elliotmartin92/kia-socket/testing/brass_part_photo.jpeg

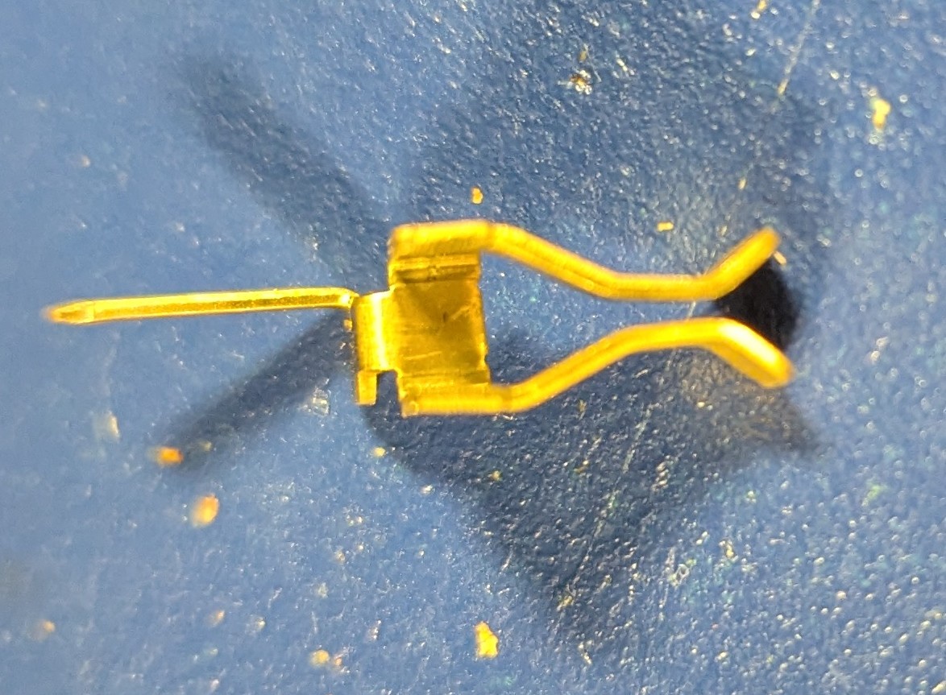
testing/brass_part_photo.jpeg
