elliotmartin92/kia-socket/testing/cropped_bracket_photo.jpg

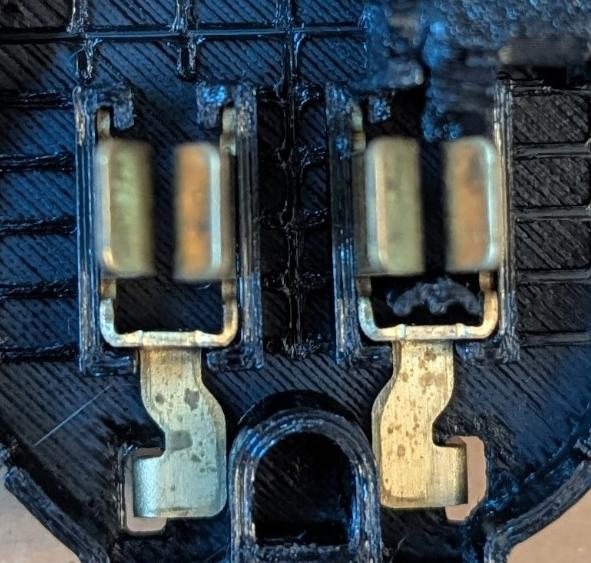
testing/cropped_bracket_photo.jpg
