elliotmartin92/kia-socket/testing/brass_insert_kinematic_simulation.png

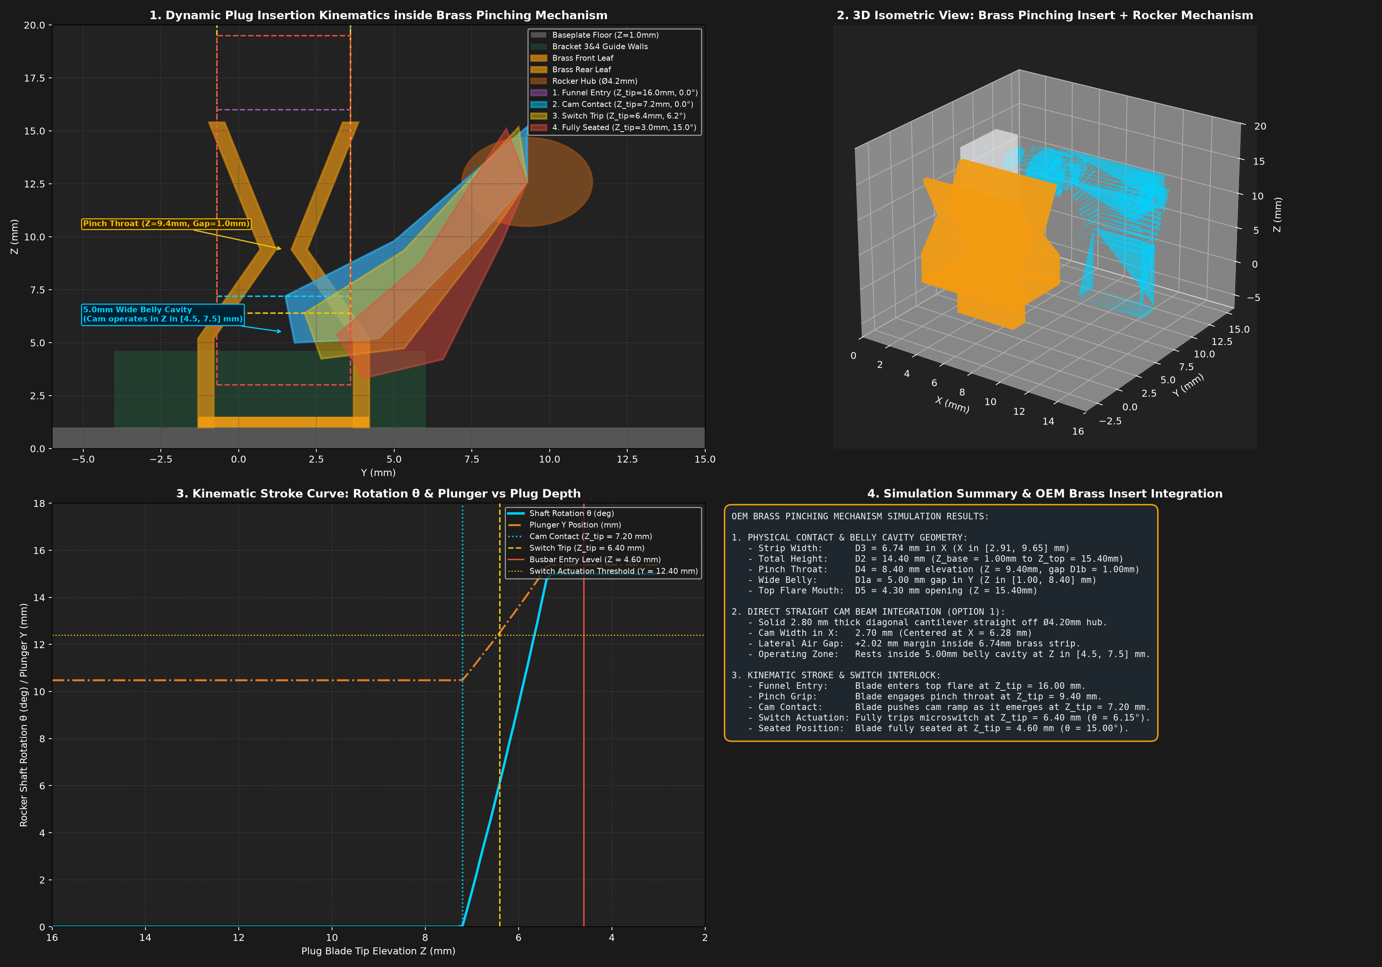
testing/brass_insert_kinematic_simulation.png
