elliotmartin92/kia-socket/testing/clip_support_design_comparison.png

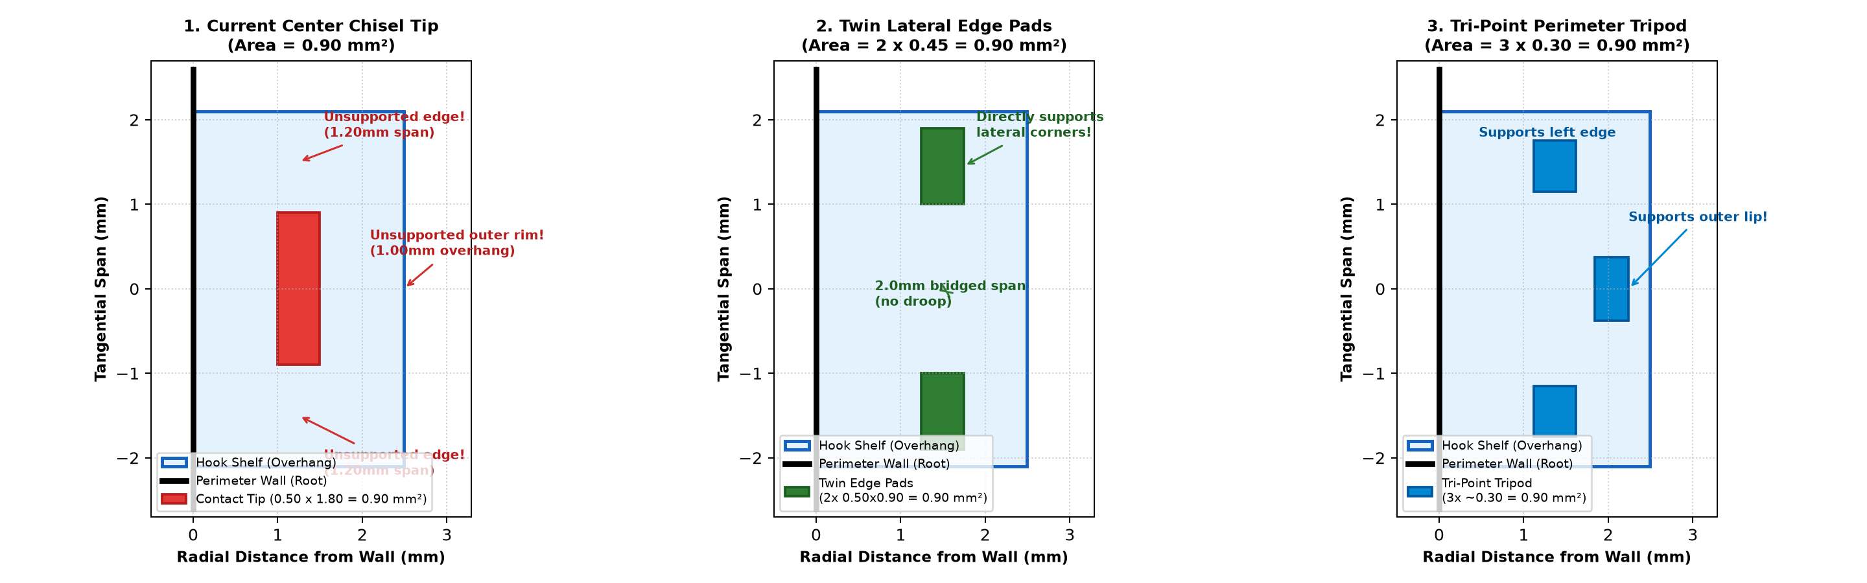
testing/clip_support_design_comparison.png
