elliotmartin92/kia-socket/testing/corrected_brass_kinematic_simulation.png

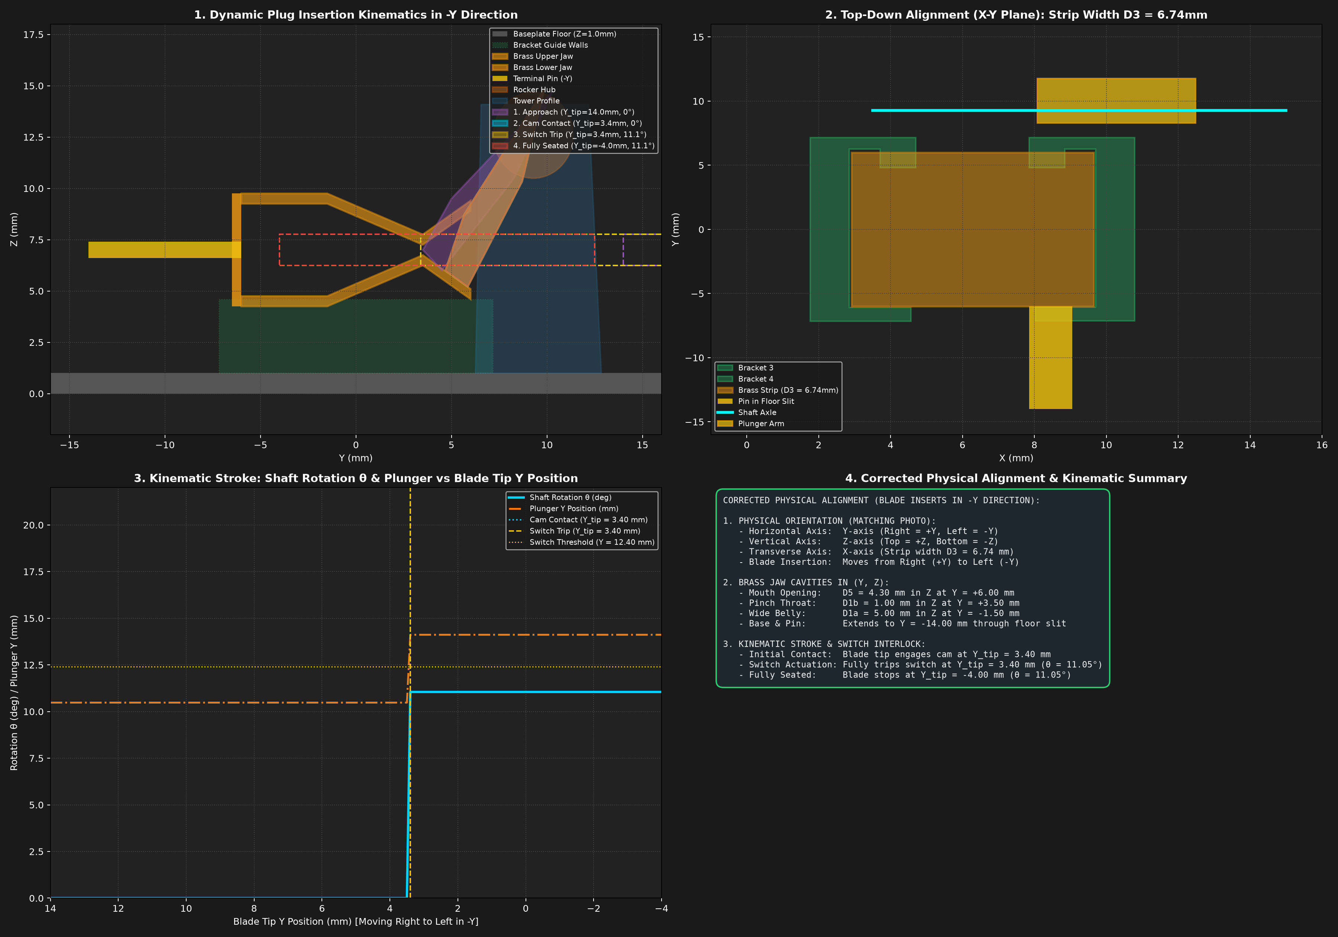
testing/corrected_brass_kinematic_simulation.png
