elliotmartin92/kia-socket/testing/arched_cam_step_by_step_study.png

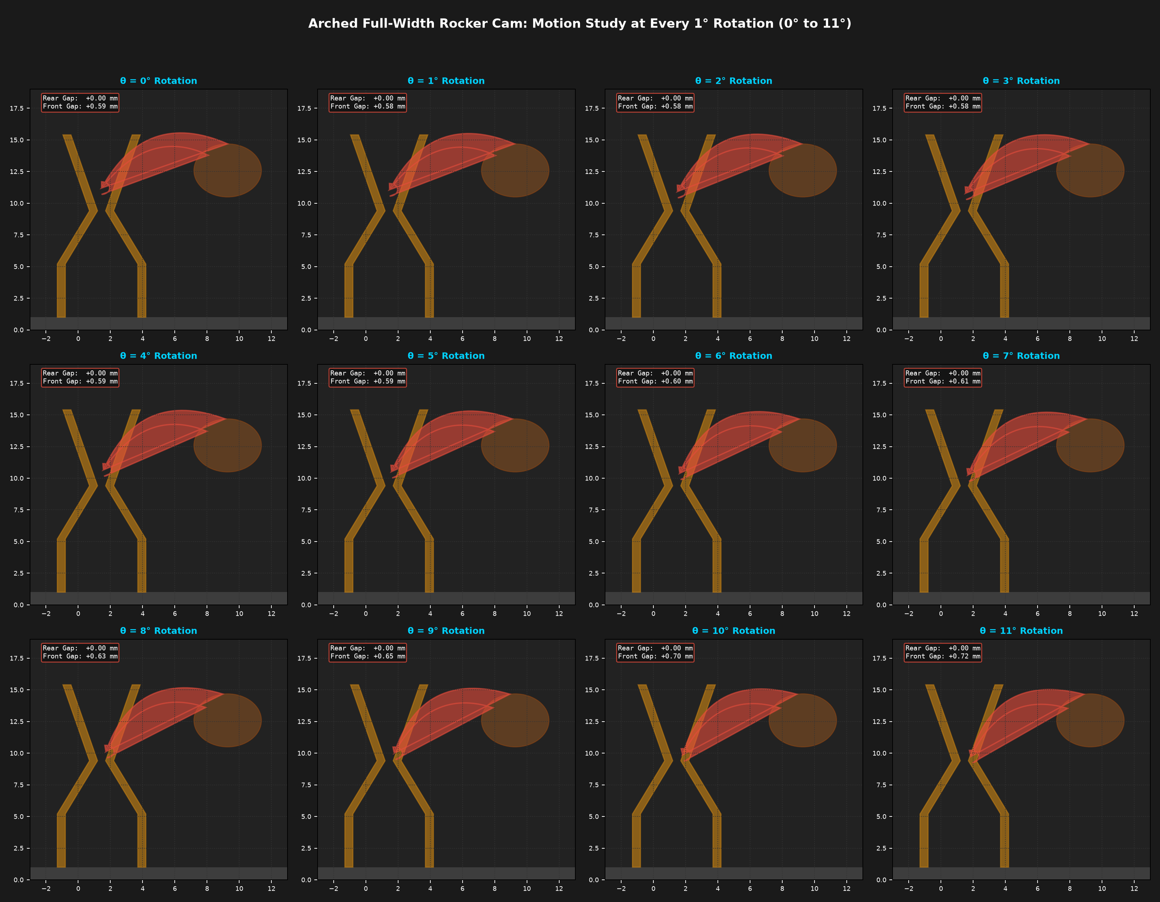
testing/arched_cam_step_by_step_study.png
