elliotmartin92/kia-socket/testing/exact_assembly_alignment.png

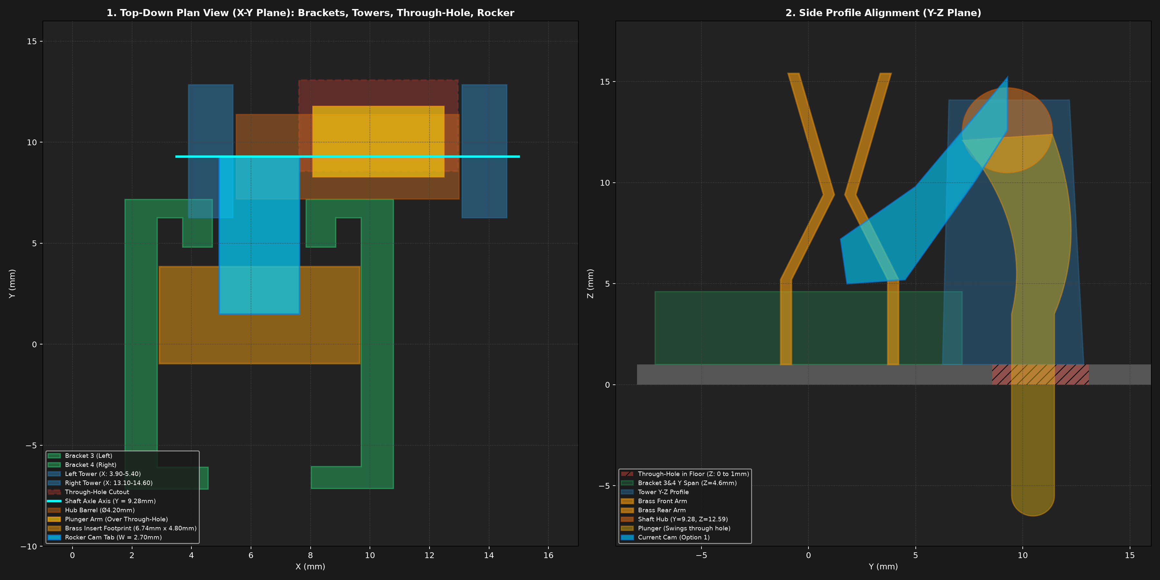
testing/exact_assembly_alignment.png
