elliotmartin92/kia-socket/testing/installed_brass_part_photo.jpg

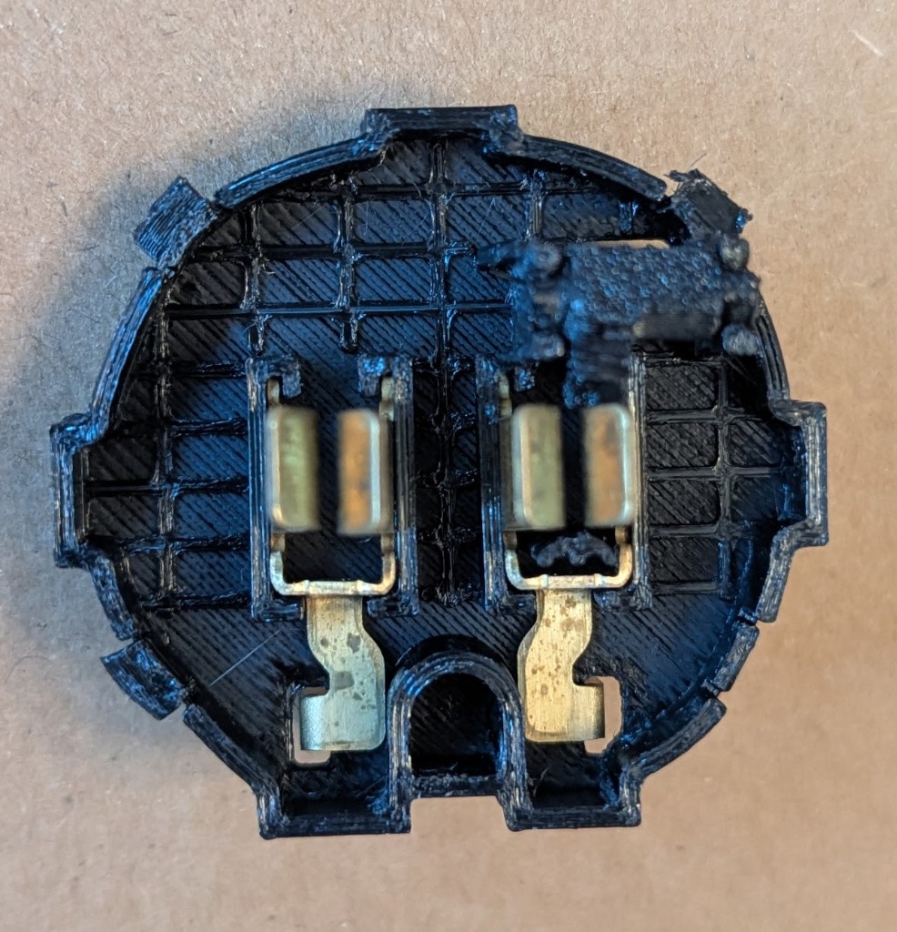
testing/installed_brass_part_photo.jpg
