elliotmartin92/kia-socket/testing/measurement_guide_diagram.png

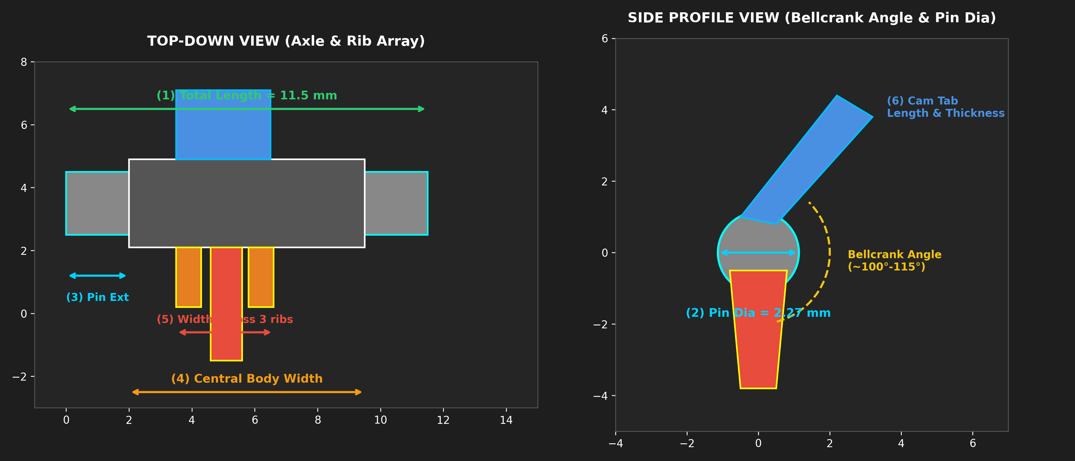
testing/measurement_guide_diagram.png
