elliotmartin92/kia-socket/testing/shaft_print_orientations_visualized.png

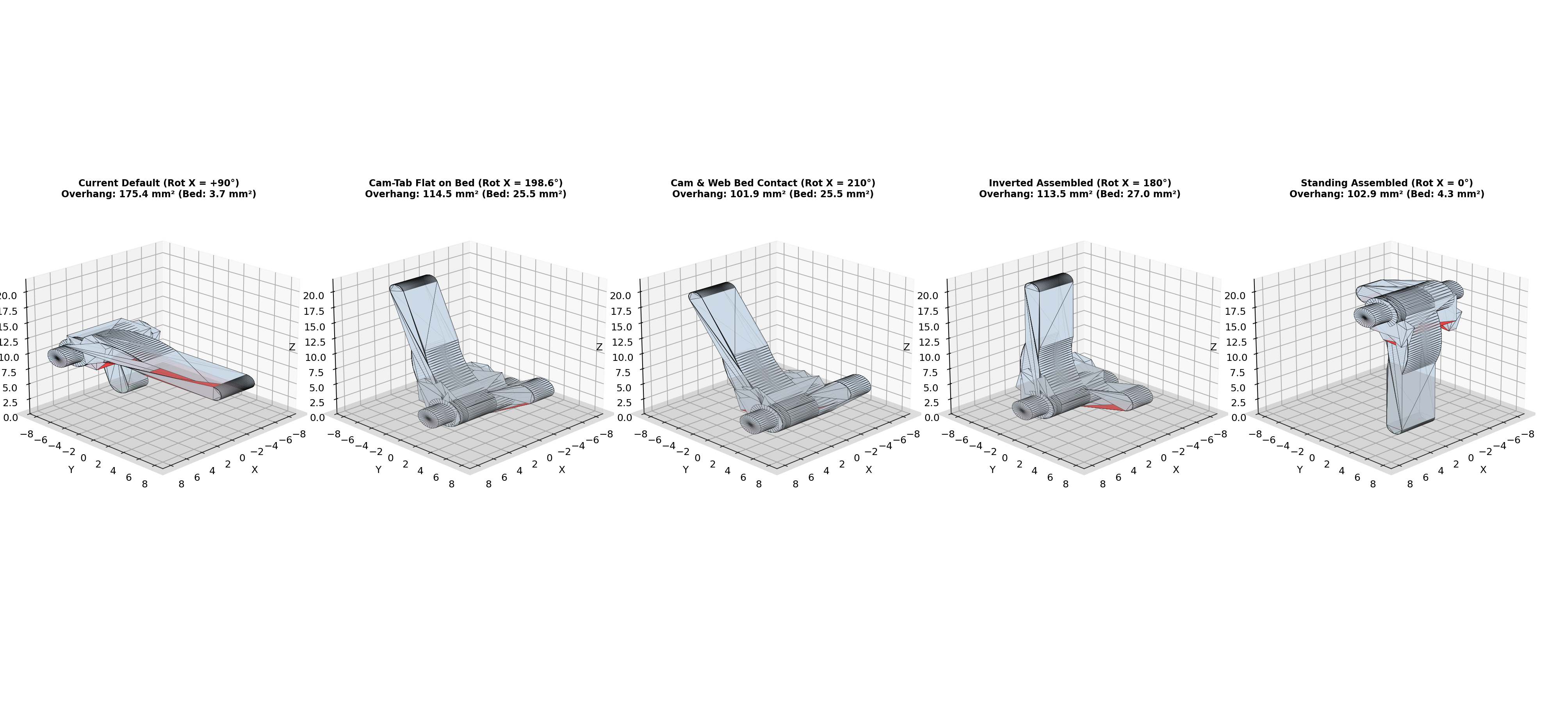
testing/shaft_print_orientations_visualized.png
