elliotmartin92/kia-socket/testing/tower_clamp_assembly_preview.png

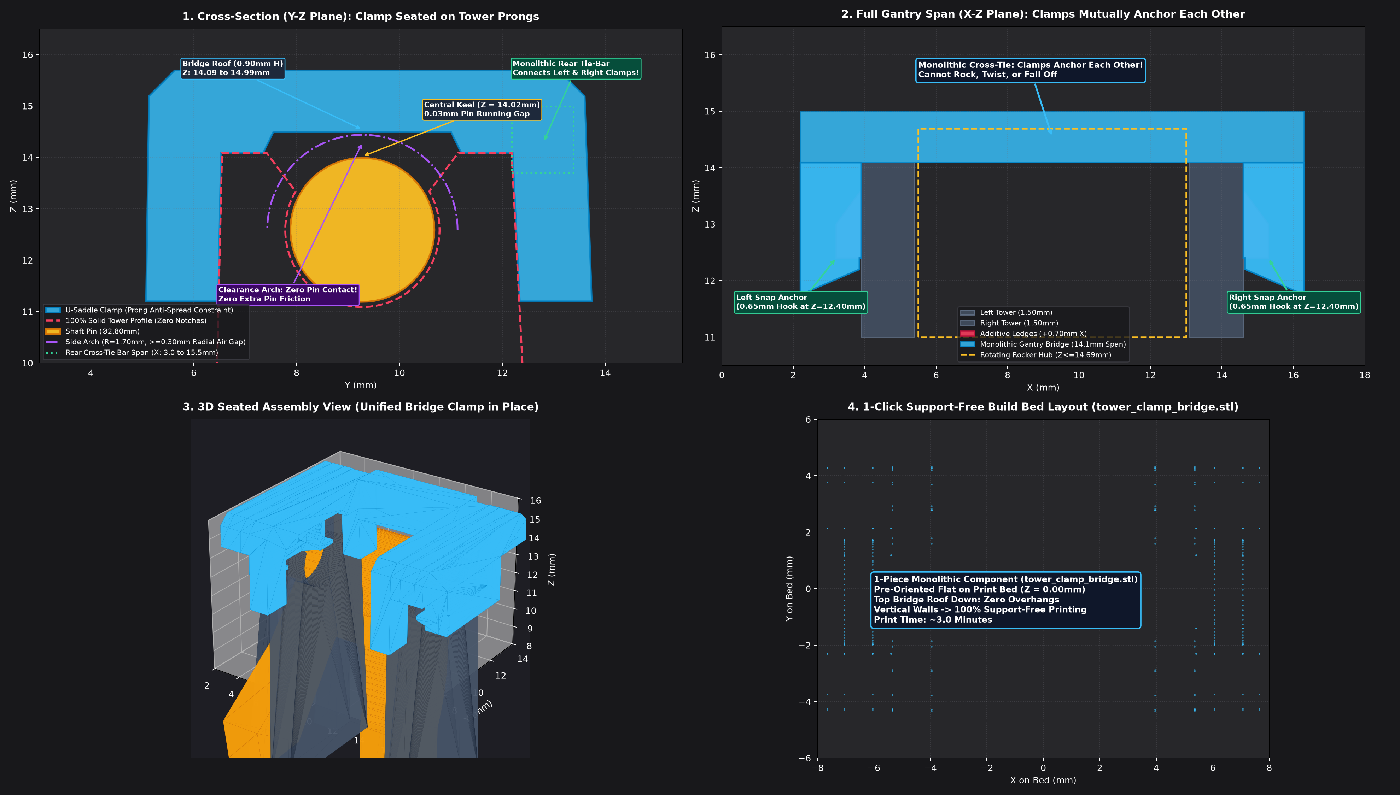
testing/tower_clamp_assembly_preview.png
