elliotmartin92/kia-socket/testing/tower_measurement_guide.png

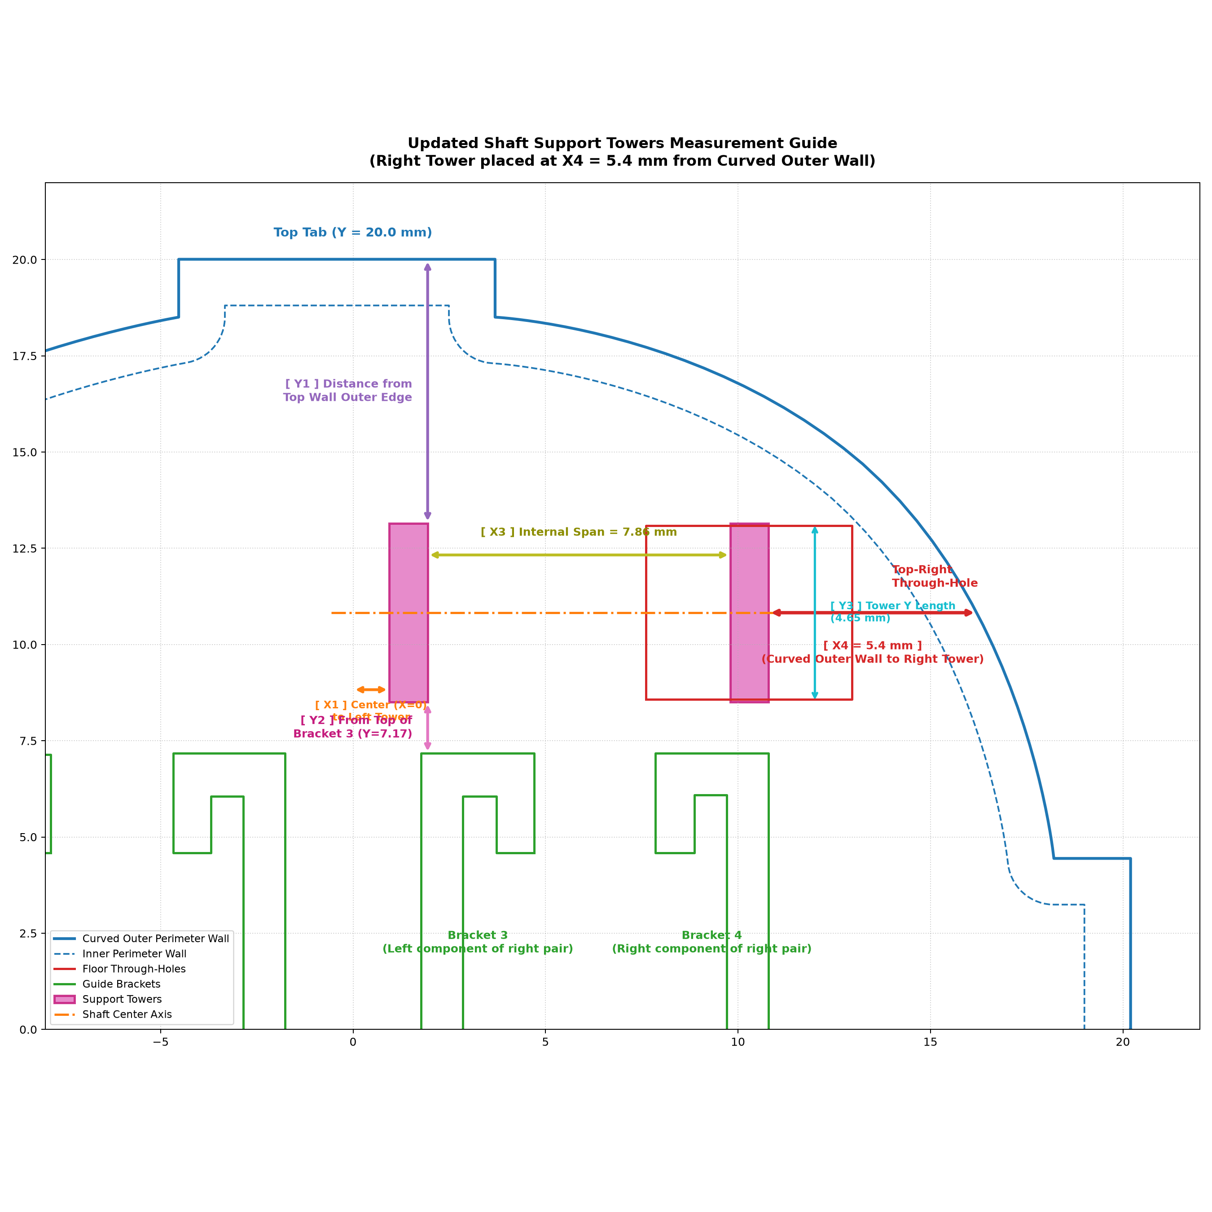
testing/tower_measurement_guide.png
