elliotmartin92/kia-socket/testing/3d_plug_insertion_view.png

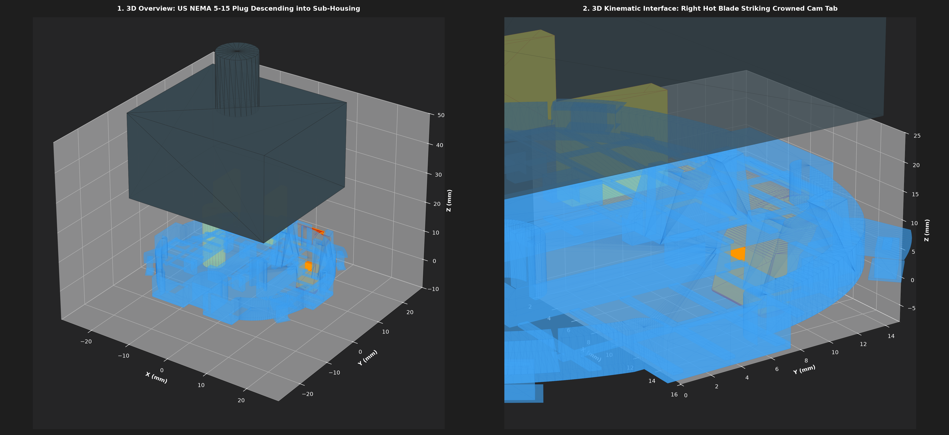
testing/3d_plug_insertion_view.png
