elliotmartin92/kia-socket/testing/aligned_bottom_arch_and_wall.png

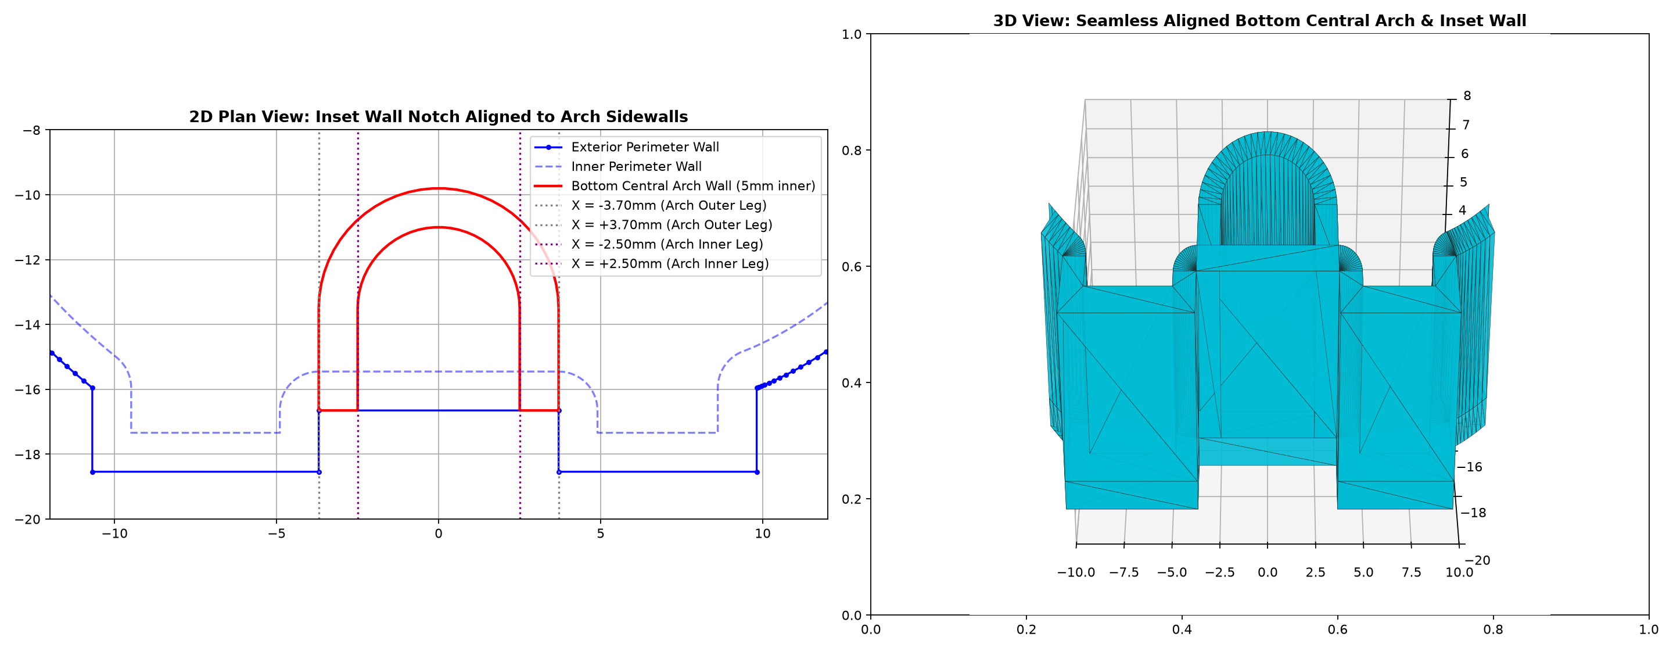
testing/aligned_bottom_arch_and_wall.png
