elliotmartin92/kia-socket/testing/aligned_bottom_notch_options.png

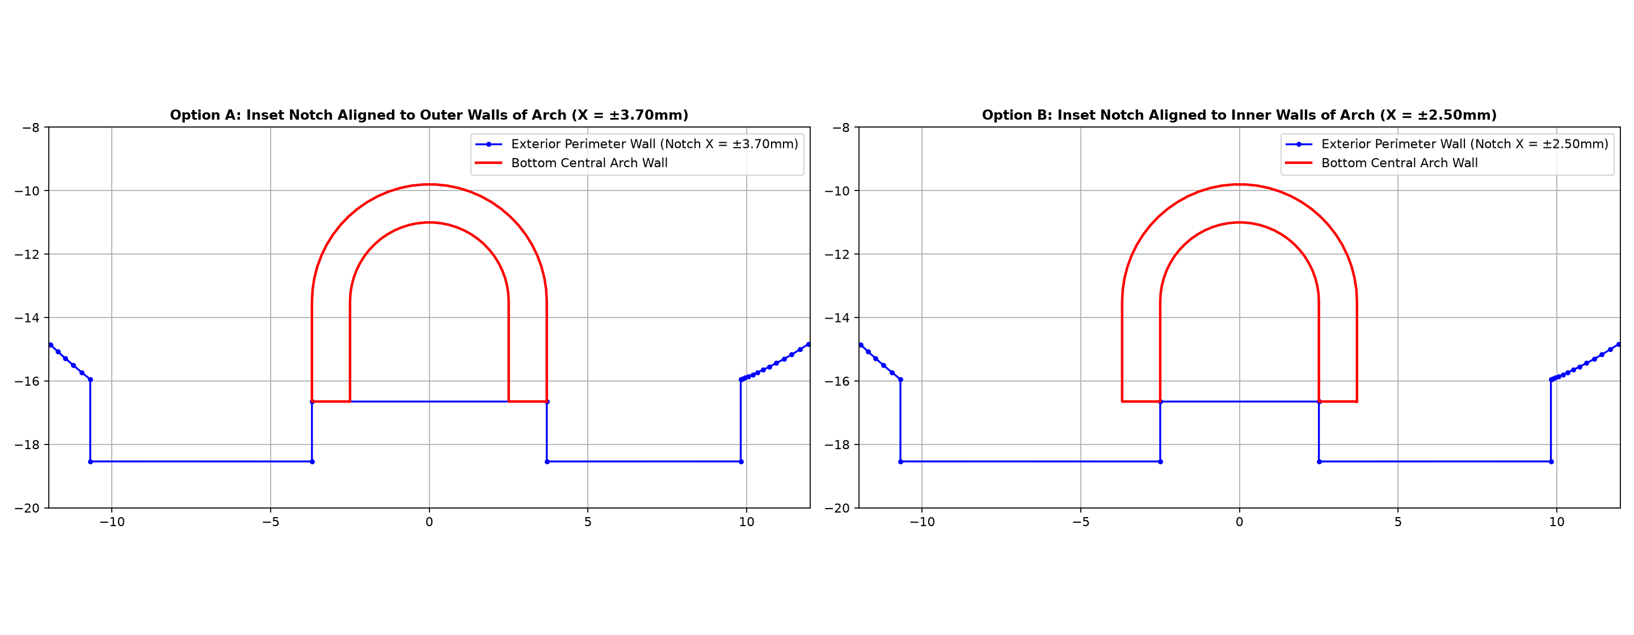
testing/aligned_bottom_notch_options.png
