elliotmartin92/kia-socket/testing/aligned_brass_insert_study.png

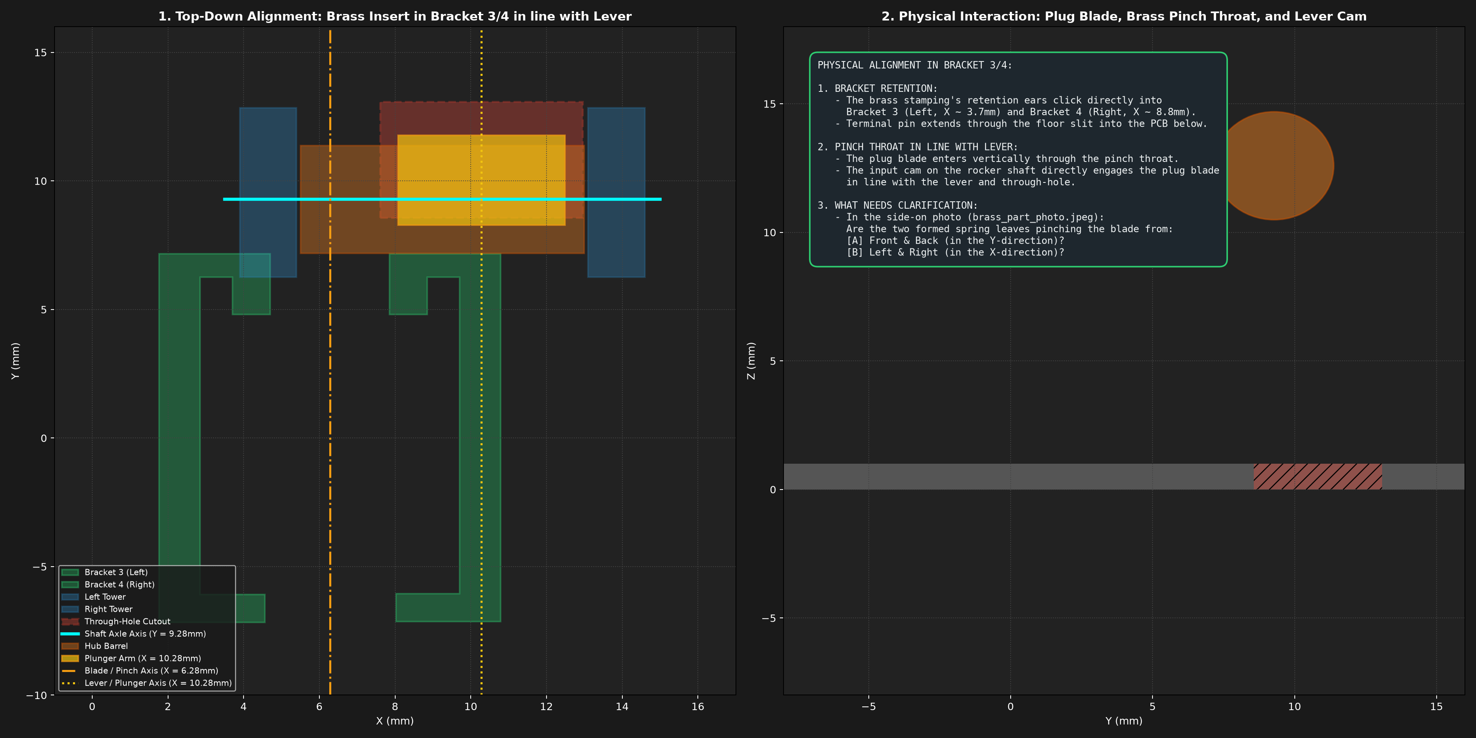
testing/aligned_brass_insert_study.png
