elliotmartin92/kia-socket/testing/aligned_towers_preview.png

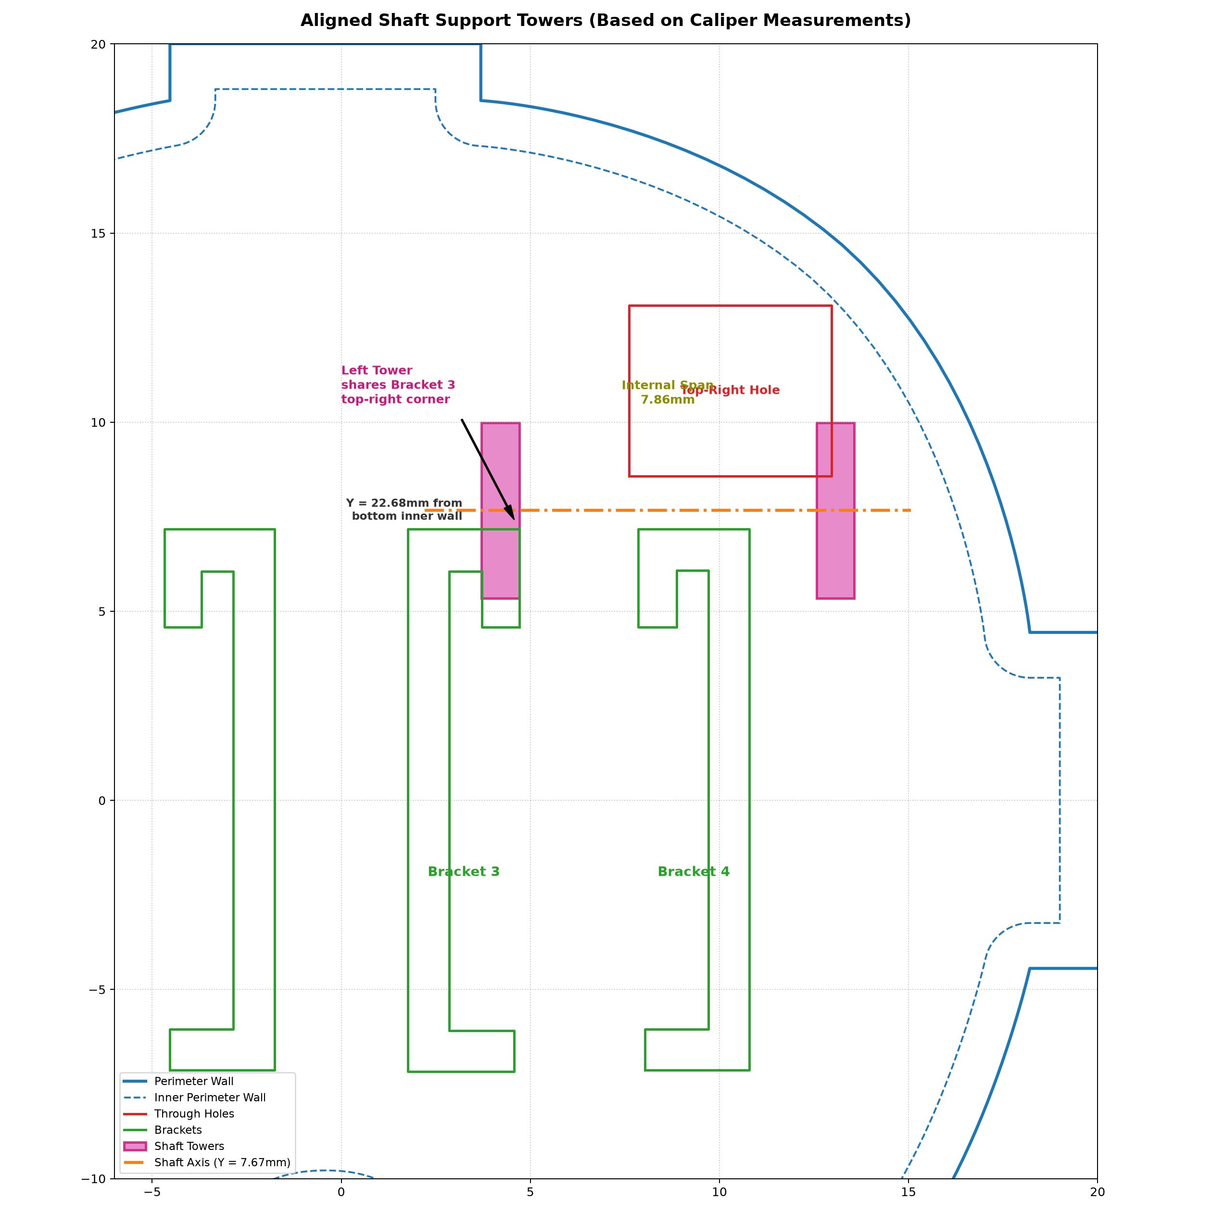
testing/aligned_towers_preview.png
