elliotmartin92/kia-socket/testing/approach_b_accurate_render.png

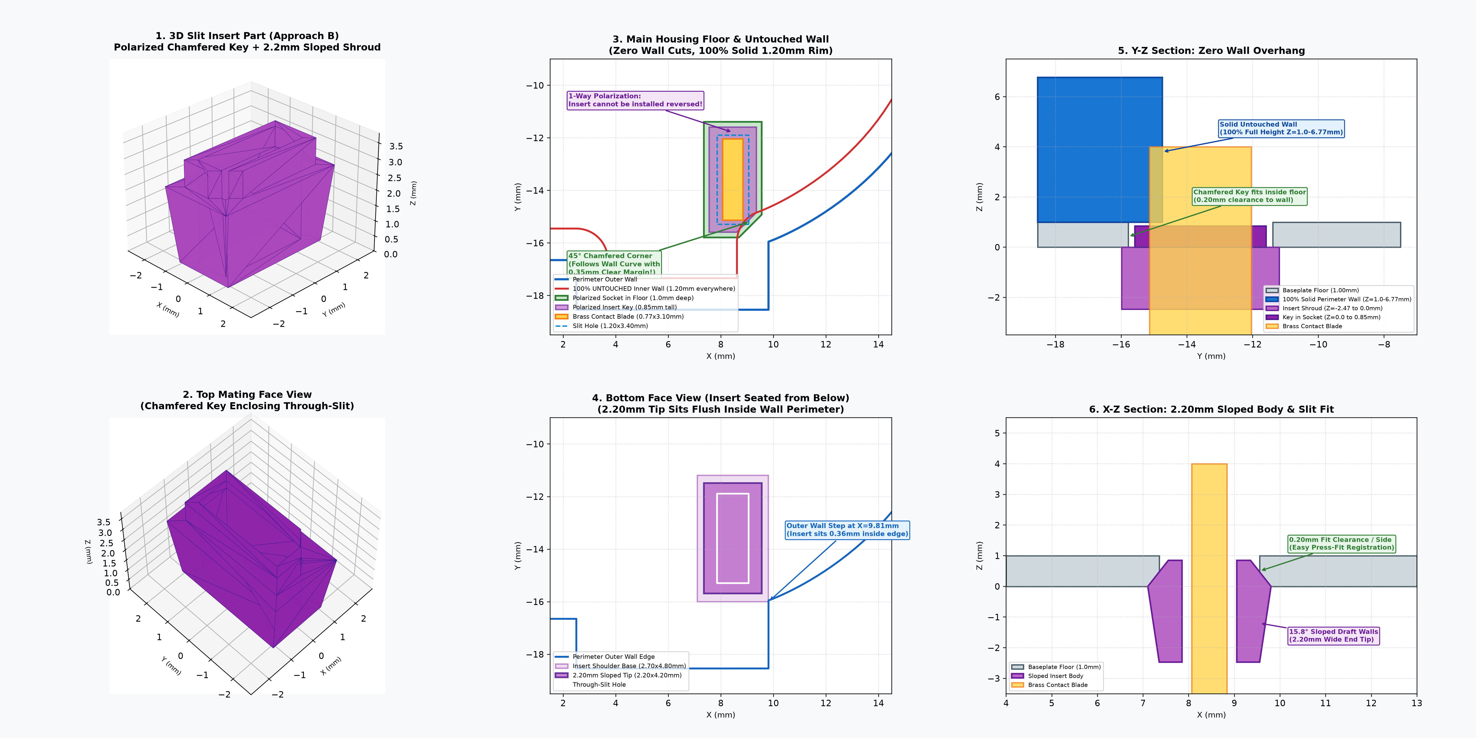
testing/approach_b_accurate_render.png
