elliotmartin92/kia-socket/testing/arch_5mm_test.png

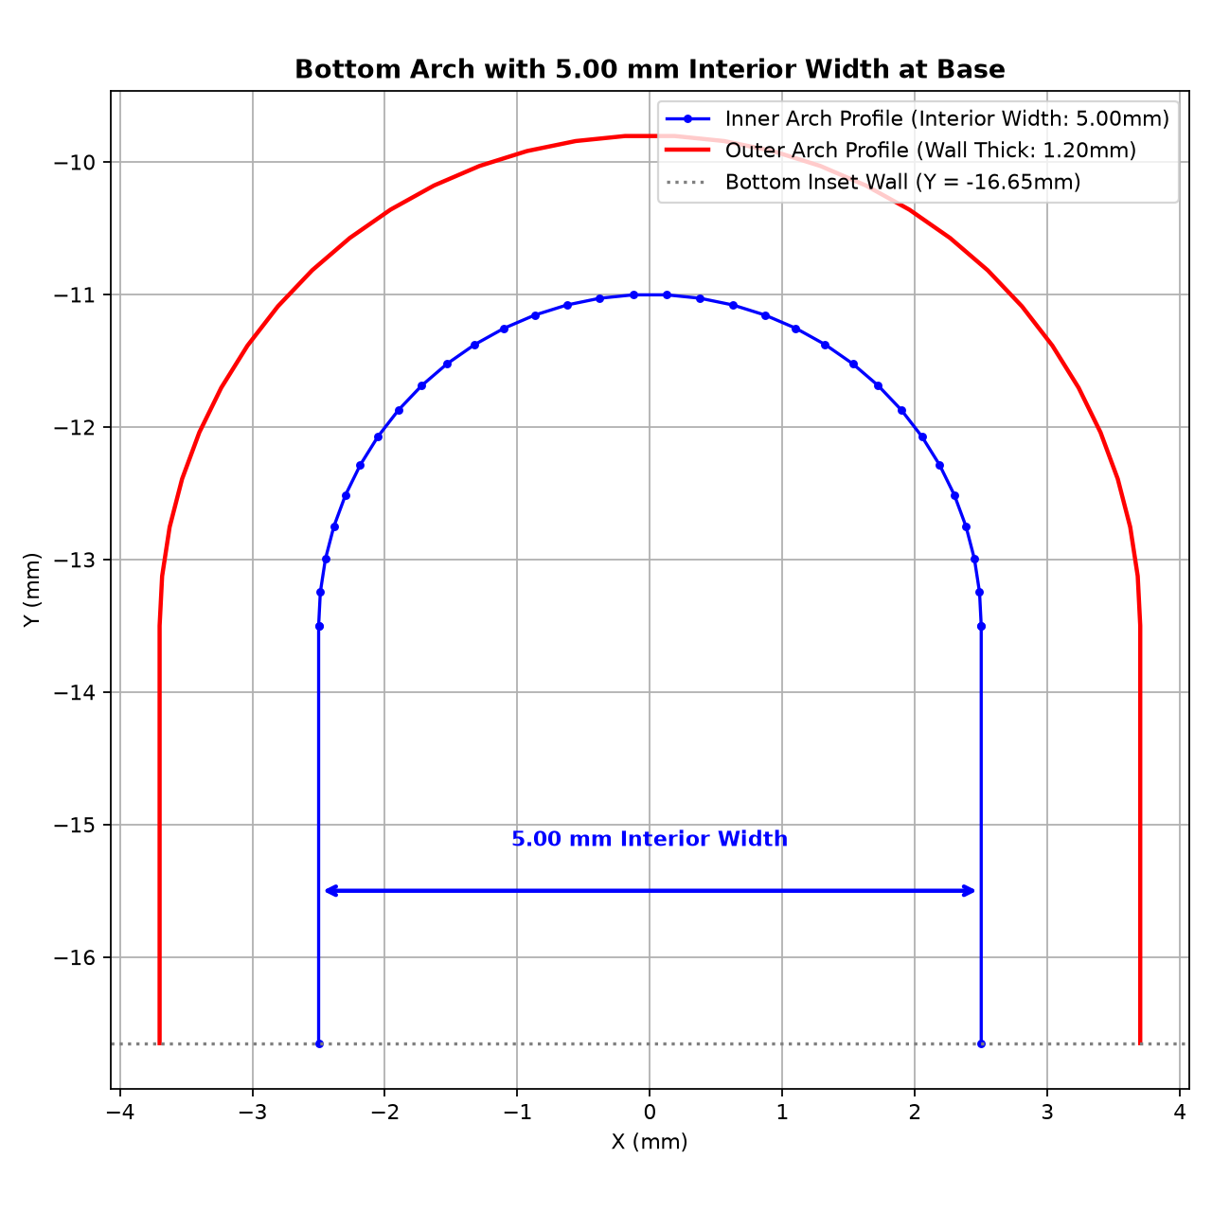
testing/arch_5mm_test.png
