elliotmartin92/kia-socket/testing/arch_795_preview.png

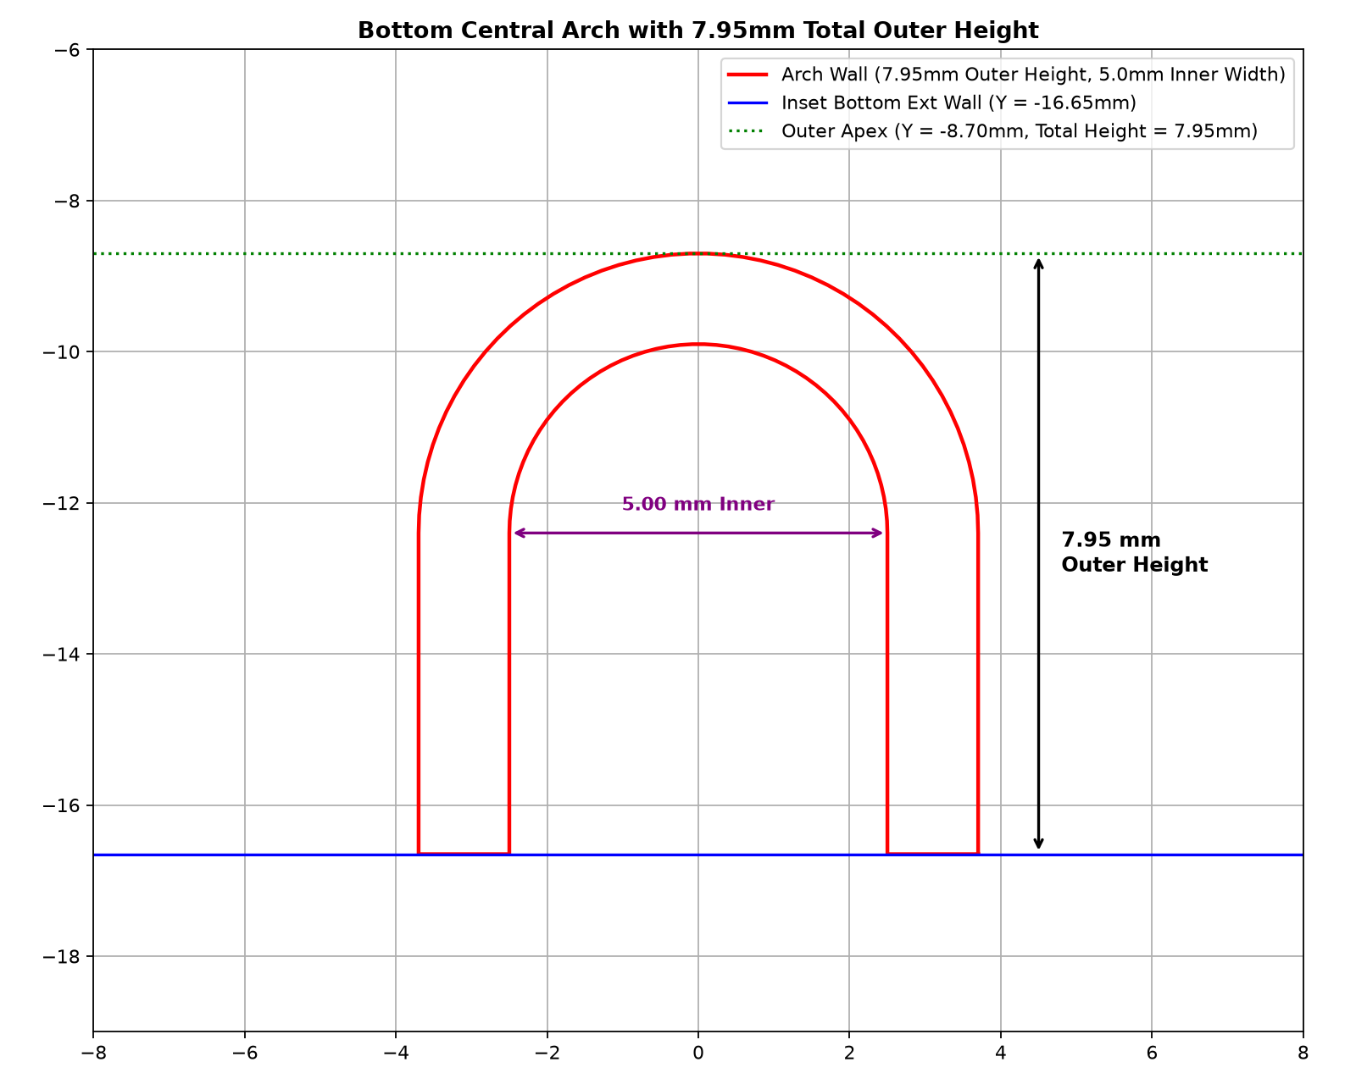
testing/arch_795_preview.png
