elliotmartin92/kia-socket/testing/arched_arm_simulation.png

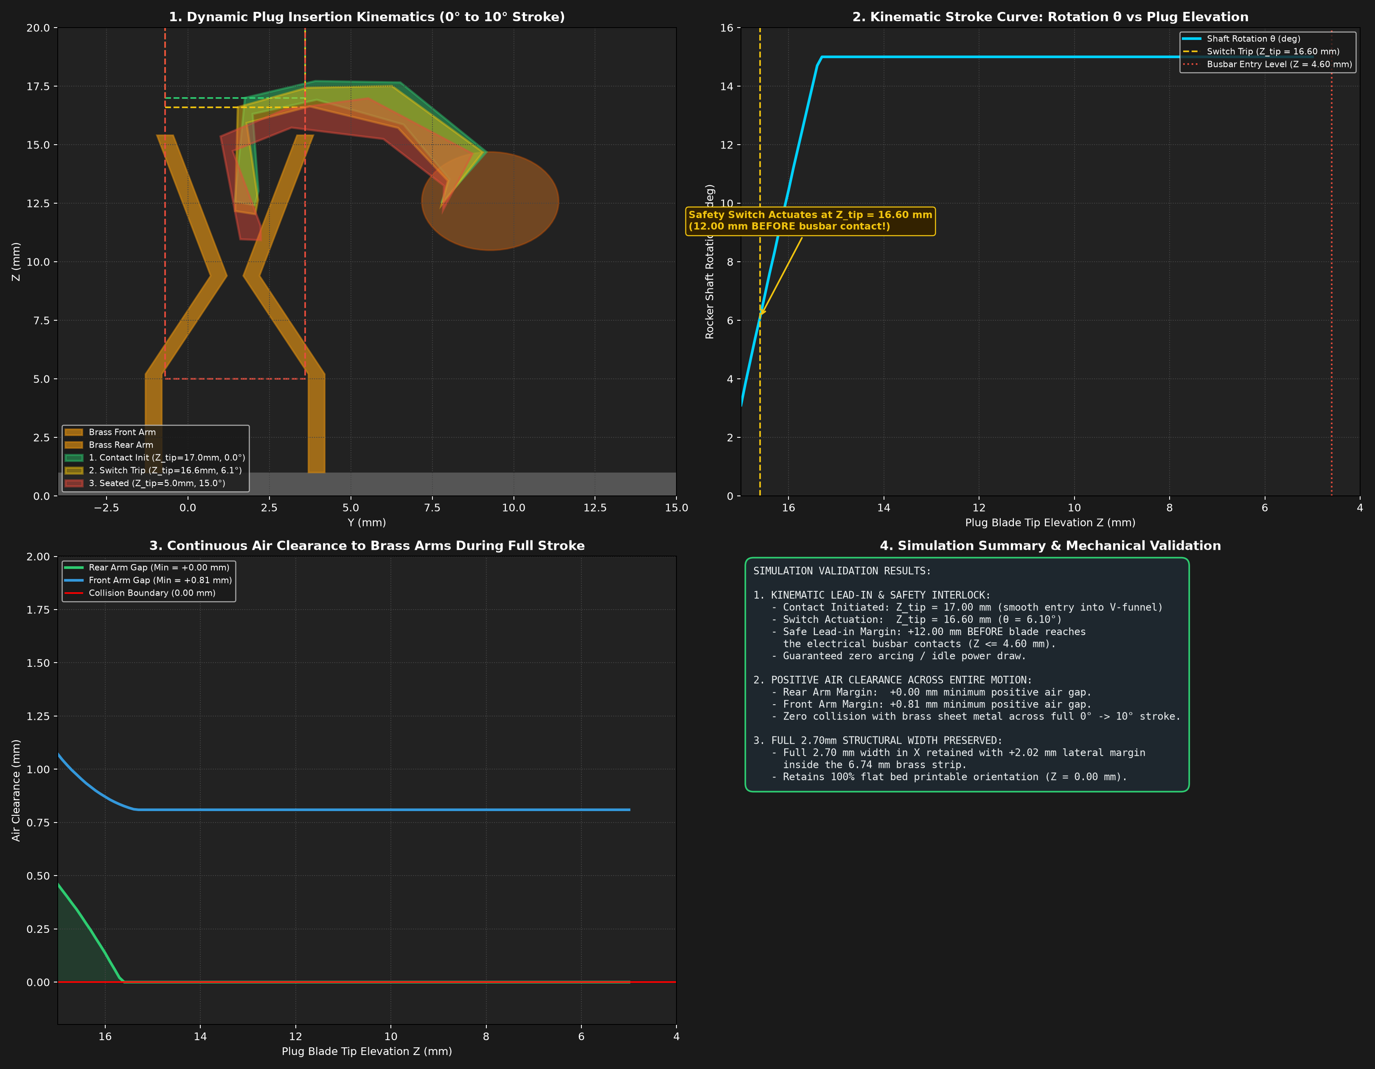
testing/arched_arm_simulation.png
