elliotmartin92/kia-socket/testing/bellcrank_angle_comparison.png

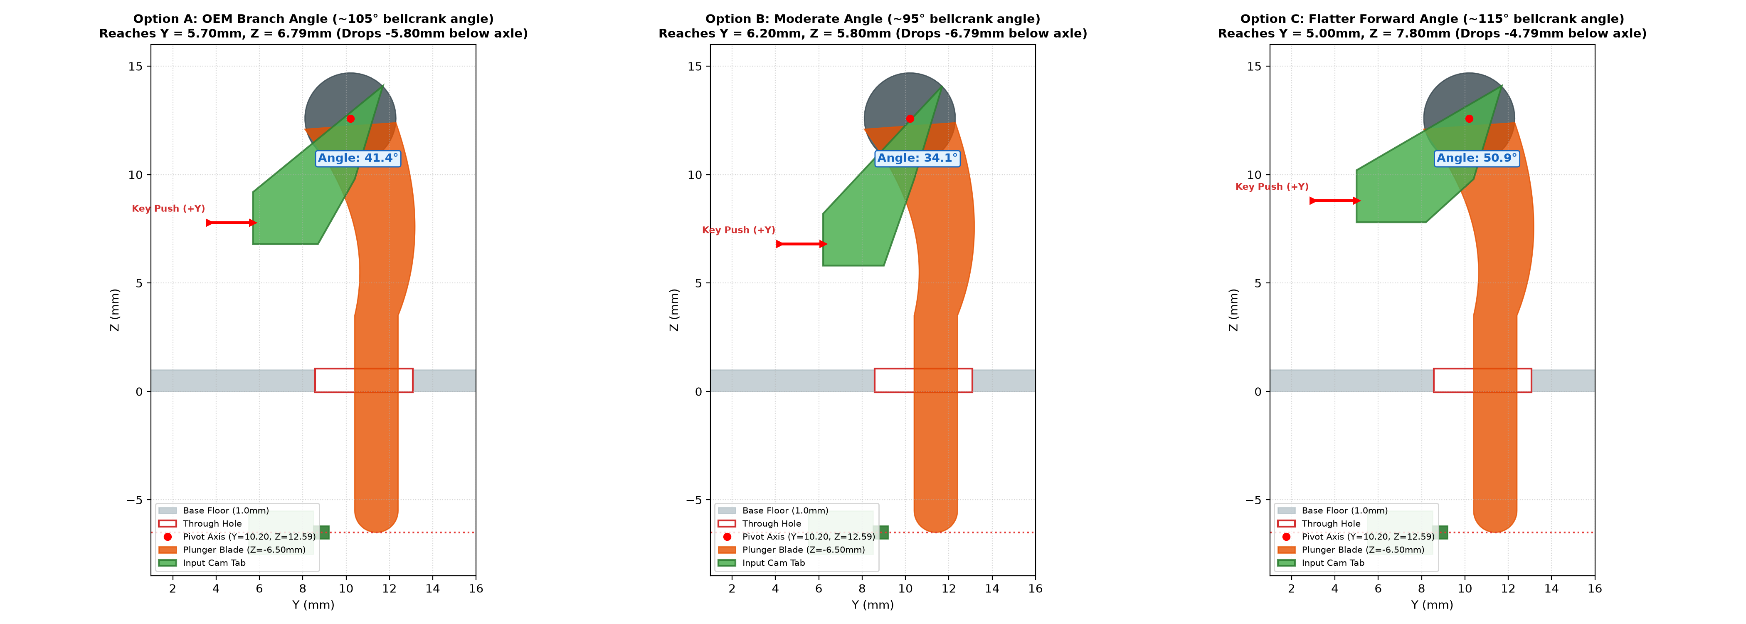
testing/bellcrank_angle_comparison.png
