elliotmartin92/kia-socket/testing/blade_cam_contact_analysis.png

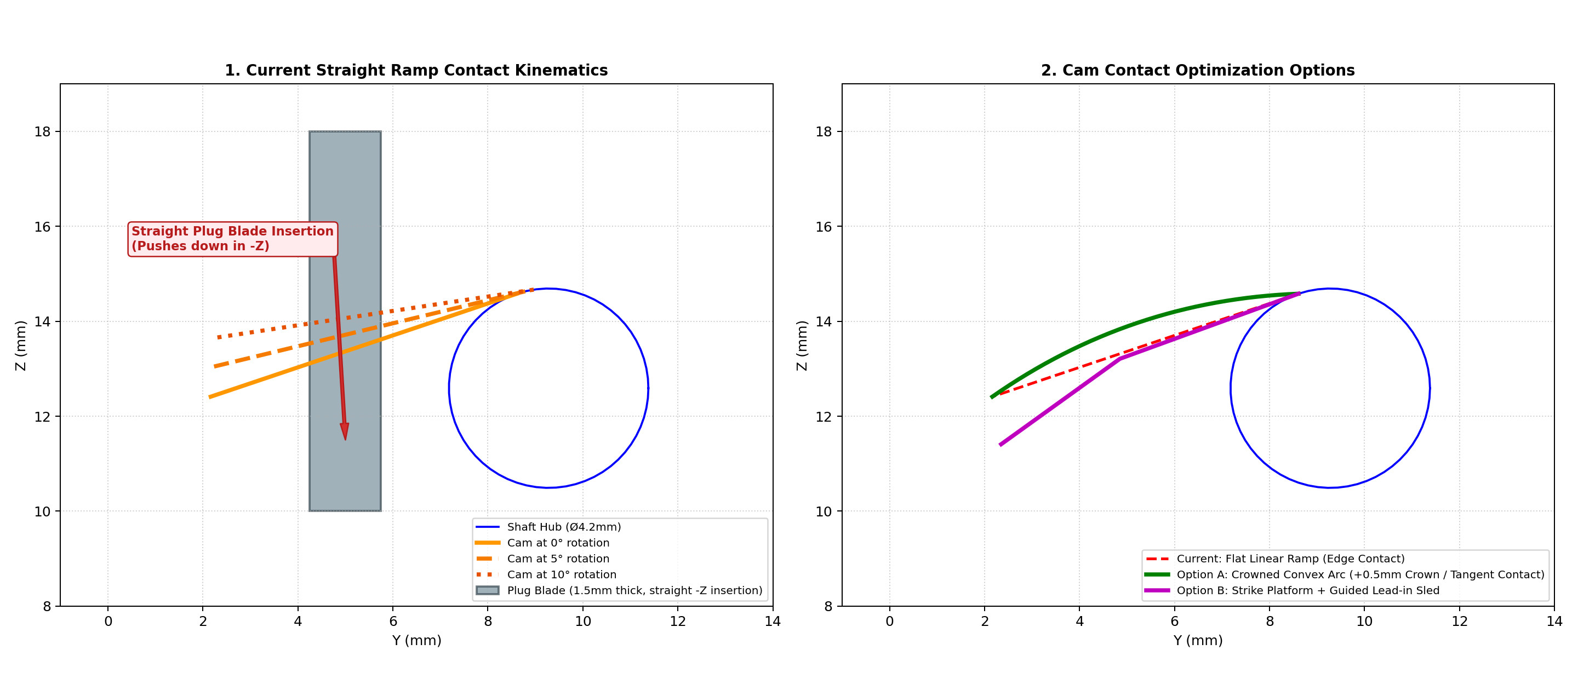
testing/blade_cam_contact_analysis.png
