elliotmartin92/kia-socket/testing/blade_contact_options_comparison.png

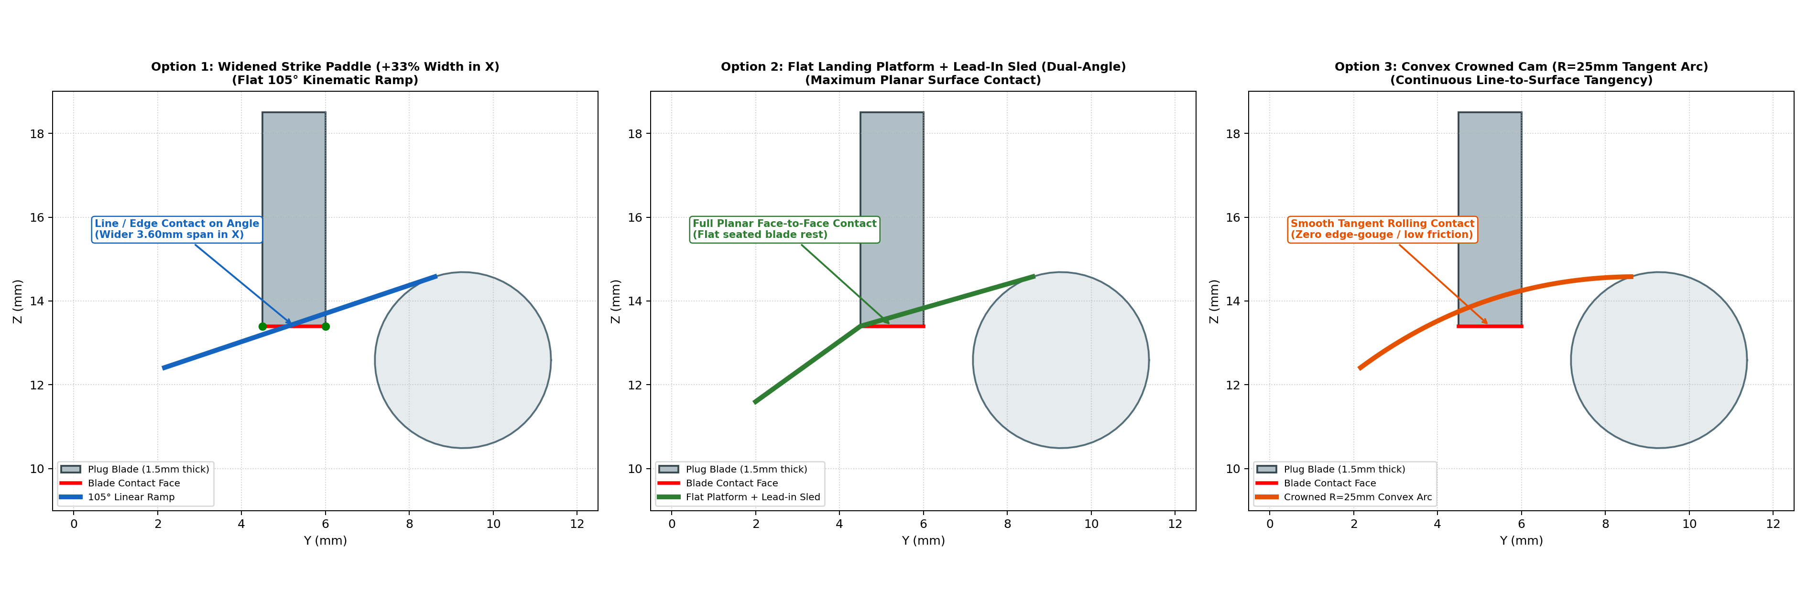
testing/blade_contact_options_comparison.png
