elliotmartin92/kia-socket/testing/blade_seating_measurements_diagram.png

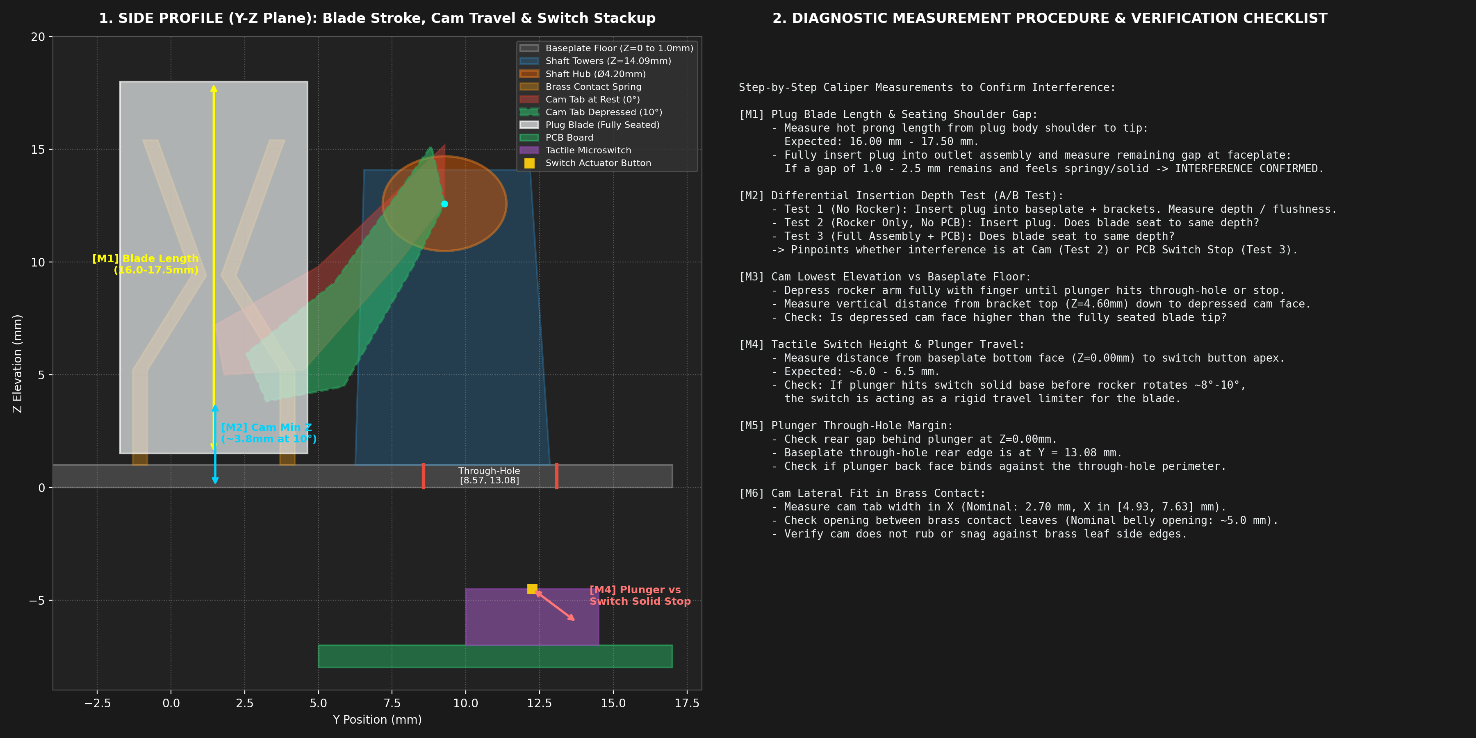
testing/blade_seating_measurements_diagram.png
