elliotmartin92/kia-socket/testing/bottom_arch_options.png

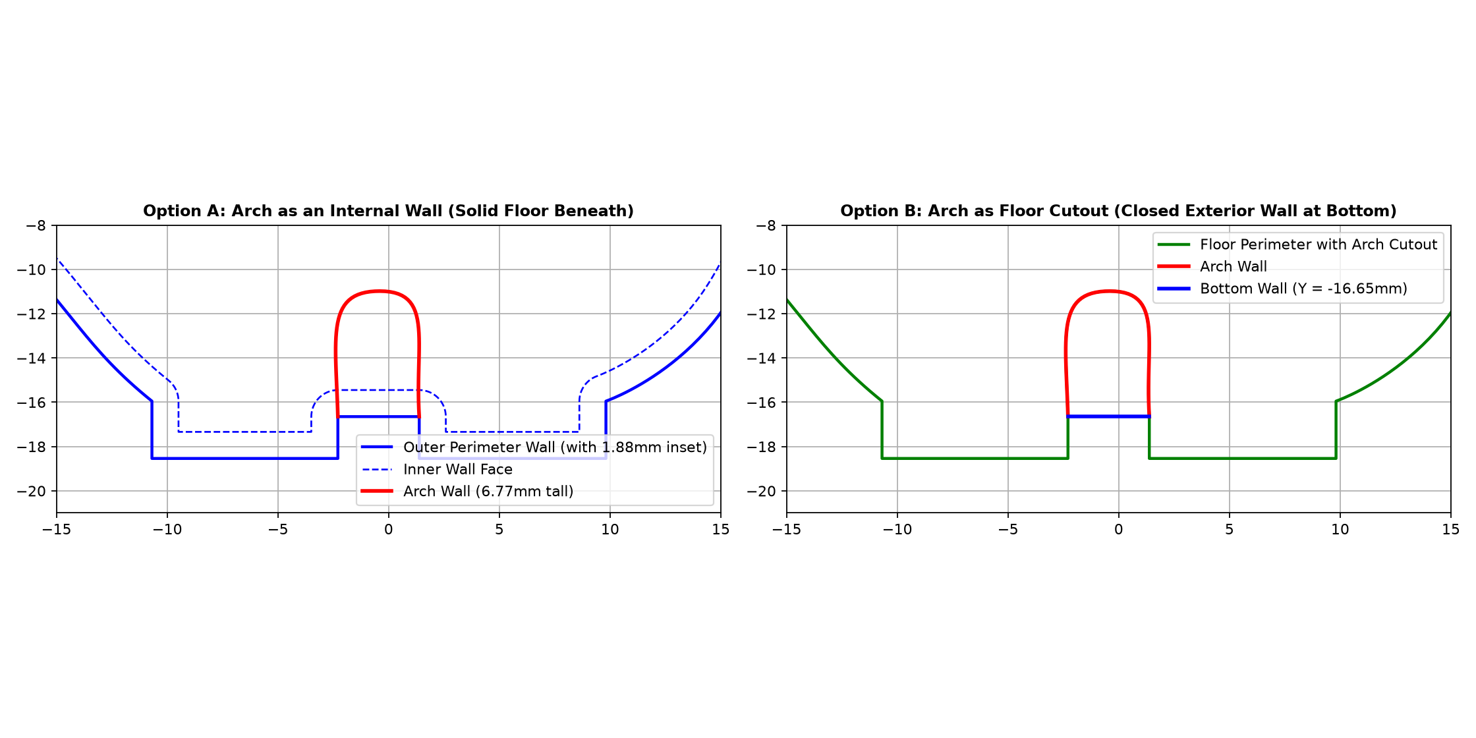
testing/bottom_arch_options.png
