elliotmartin92/kia-socket/testing/bottom_clip_options_plot.png

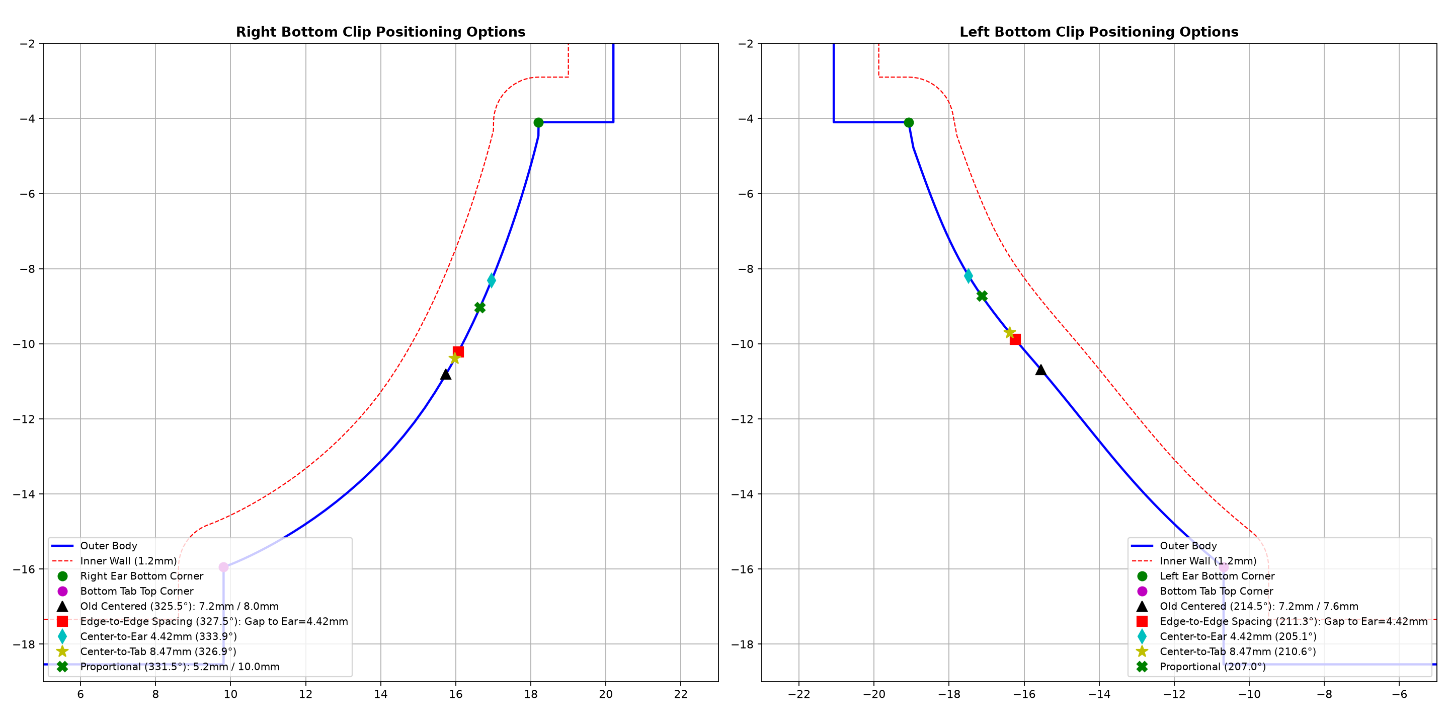
testing/bottom_clip_options_plot.png
