elliotmartin92/kia-socket/testing/bottom_feature_3d_test.png

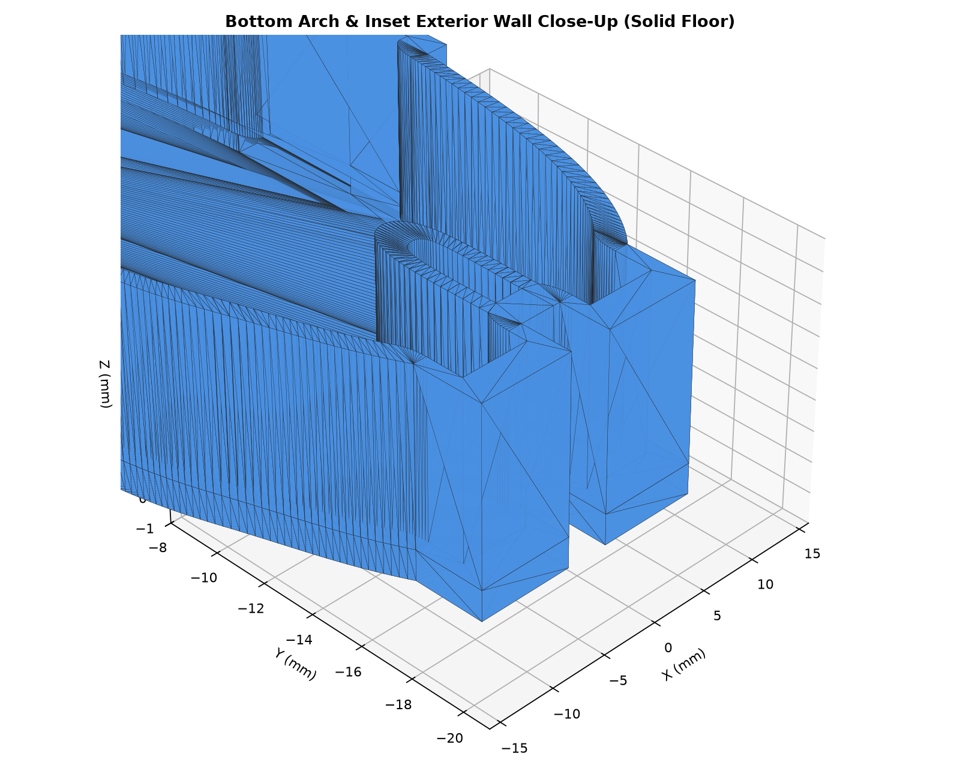
testing/bottom_feature_3d_test.png
