elliotmartin92/kia-socket/testing/bottom_notch_and_arch_configs.png

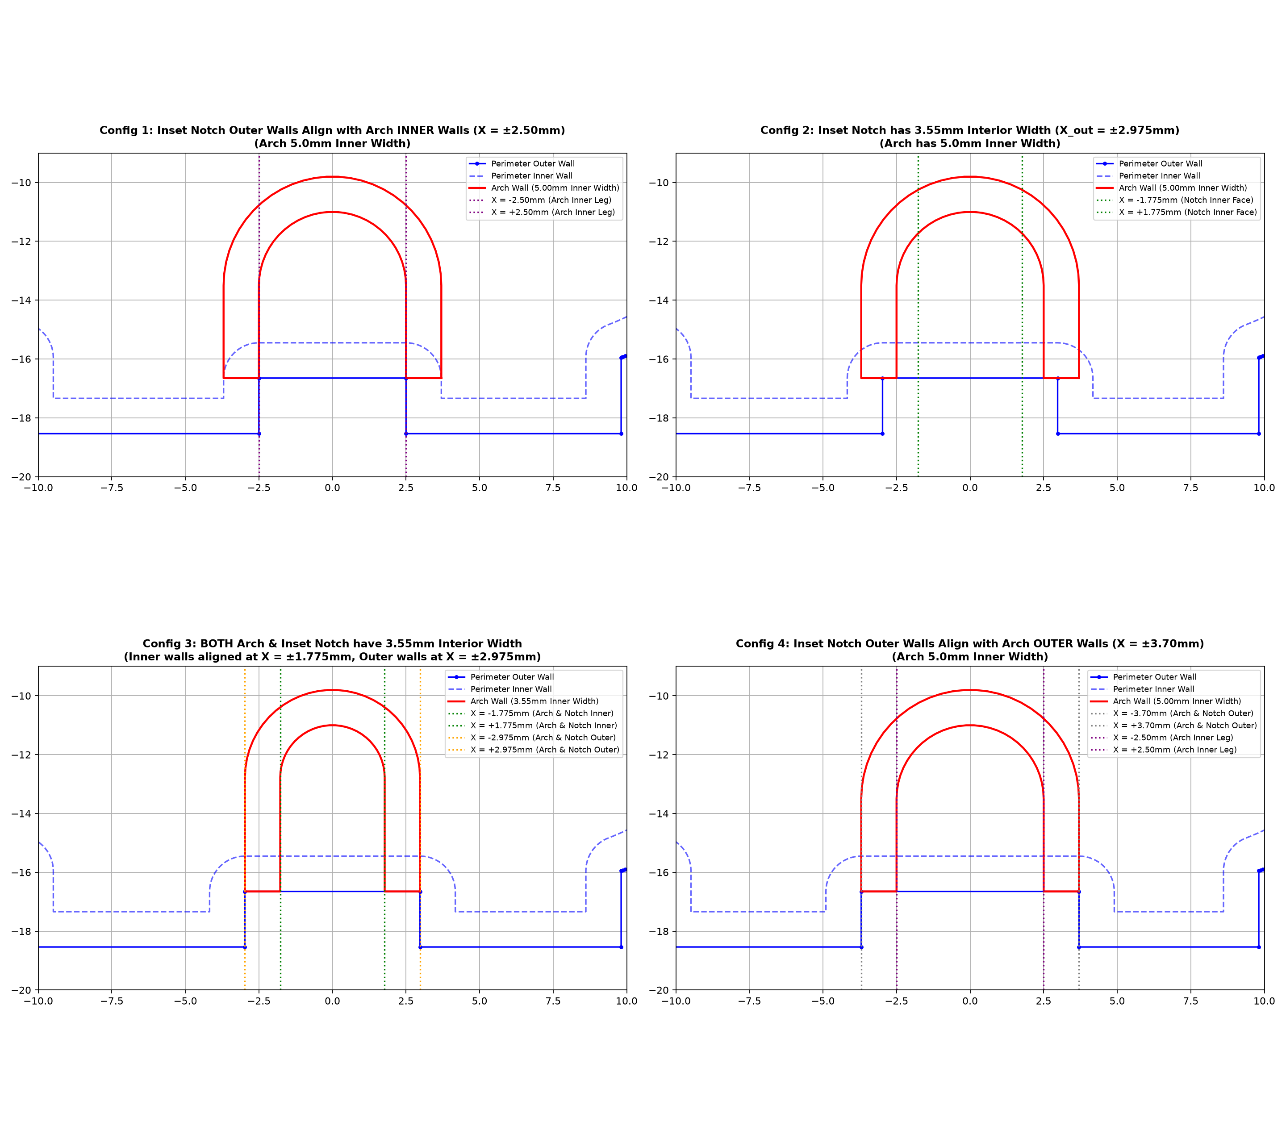
testing/bottom_notch_and_arch_configs.png
