elliotmartin92/kia-socket/testing/bottom_wall_alignment_inspect.png

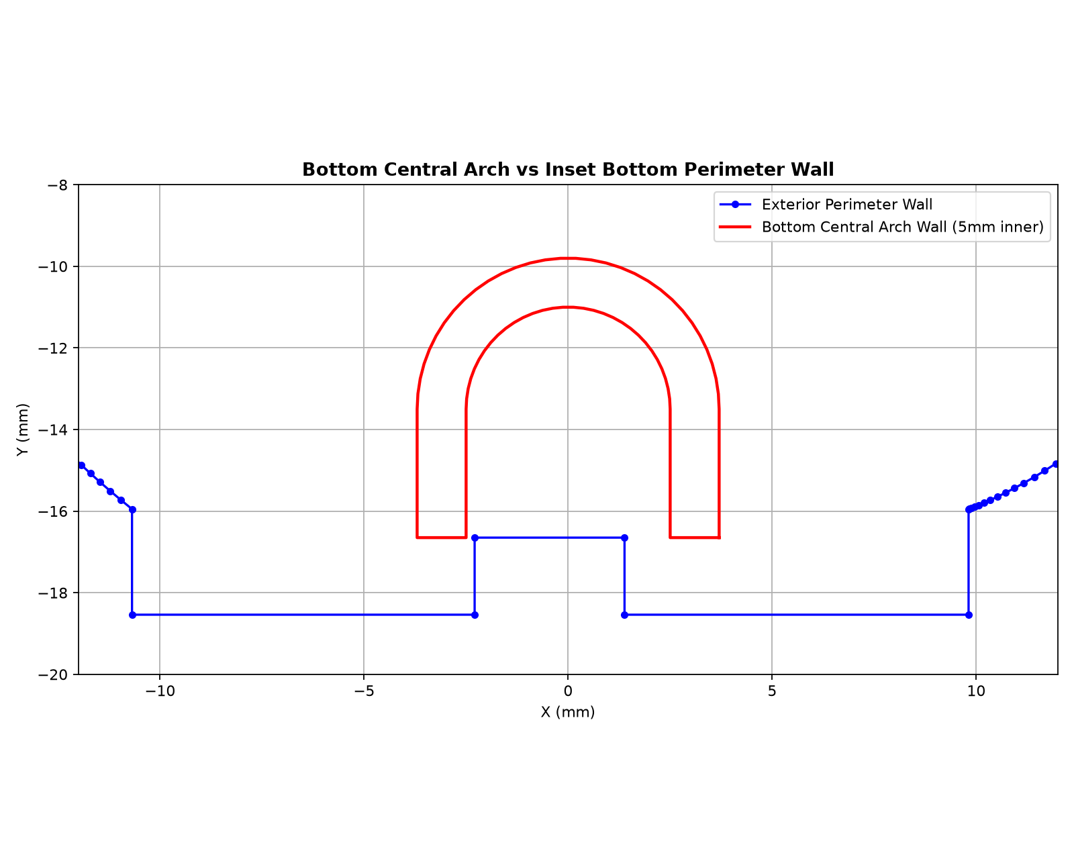
testing/bottom_wall_alignment_inspect.png
