elliotmartin92/kia-socket/testing/bracket3_clearance_verified.png

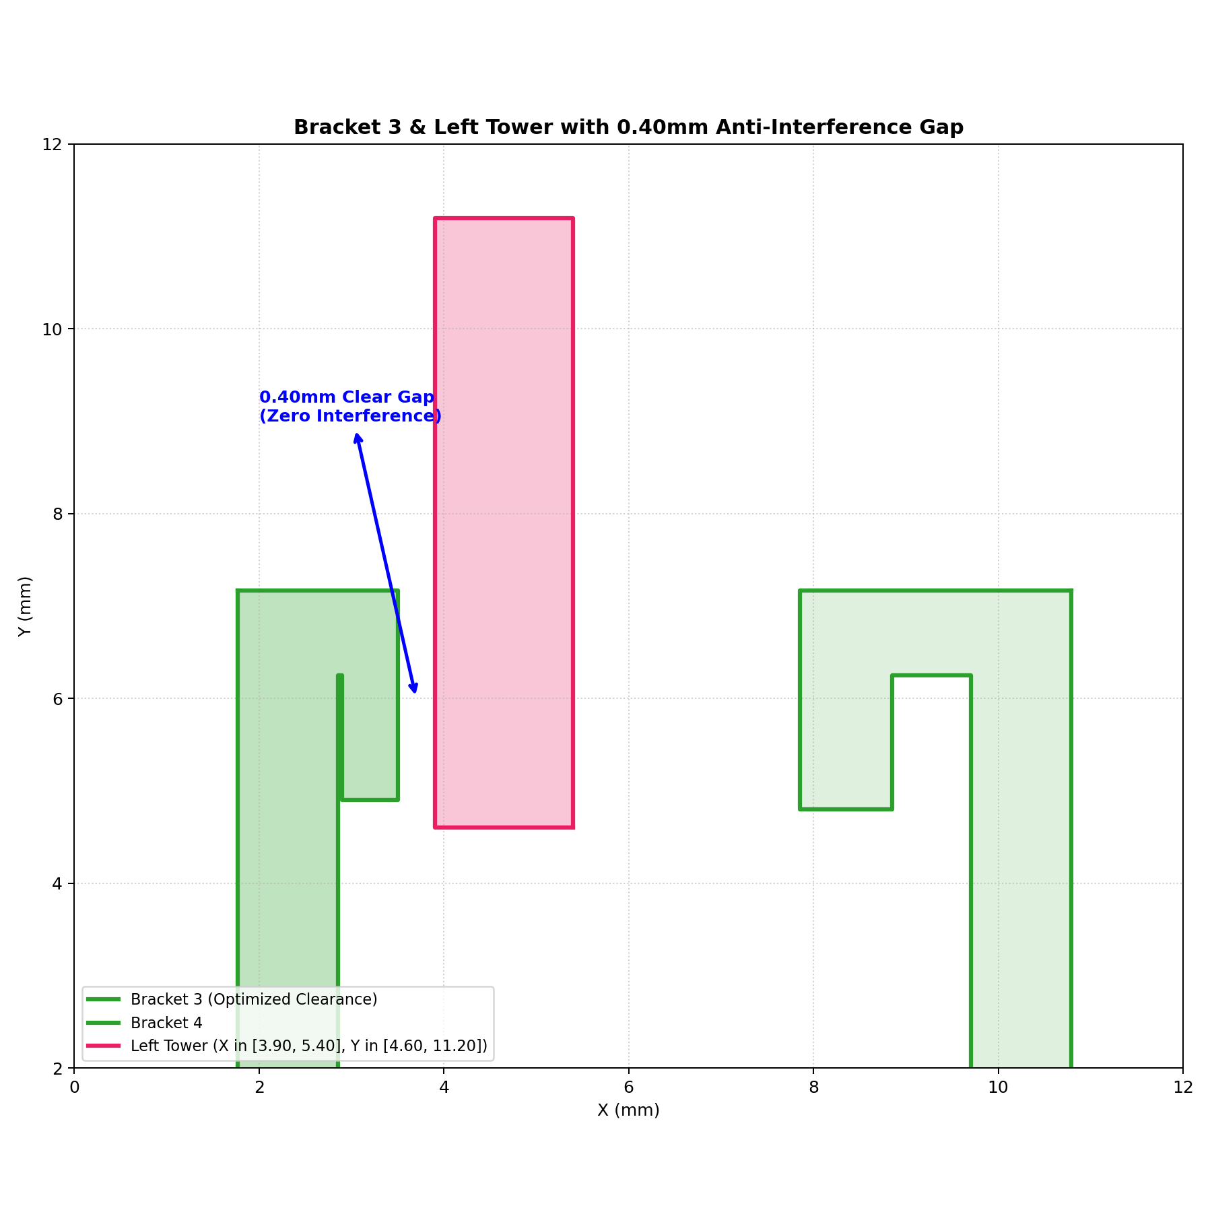
testing/bracket3_clearance_verified.png
