elliotmartin92/kia-socket/testing/bracket3_full_slot_trimmed_strut.png

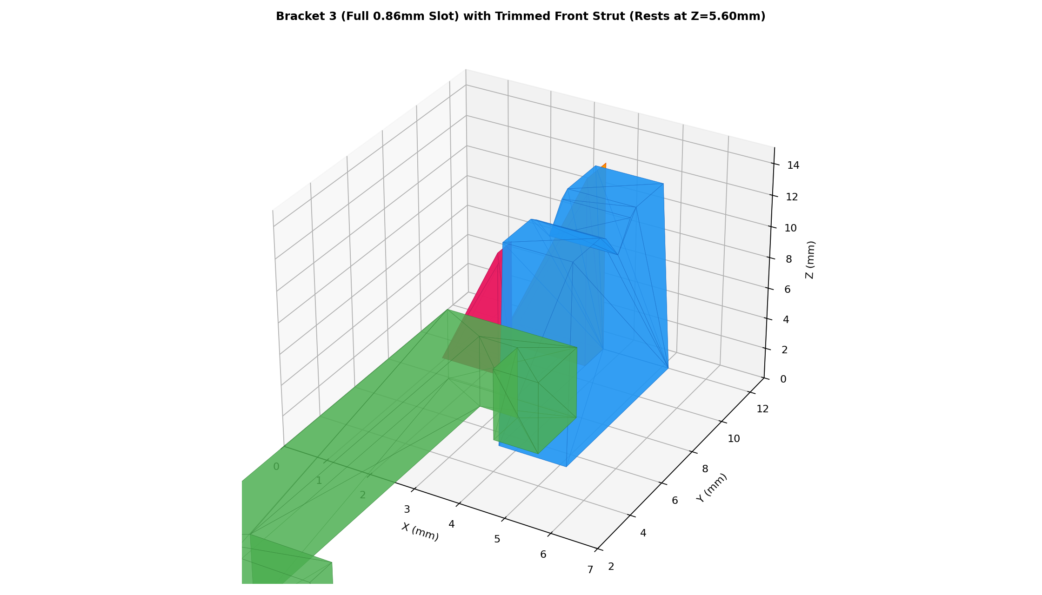
testing/bracket3_full_slot_trimmed_strut.png
