elliotmartin92/kia-socket/testing/bracket3_tower_interference.png

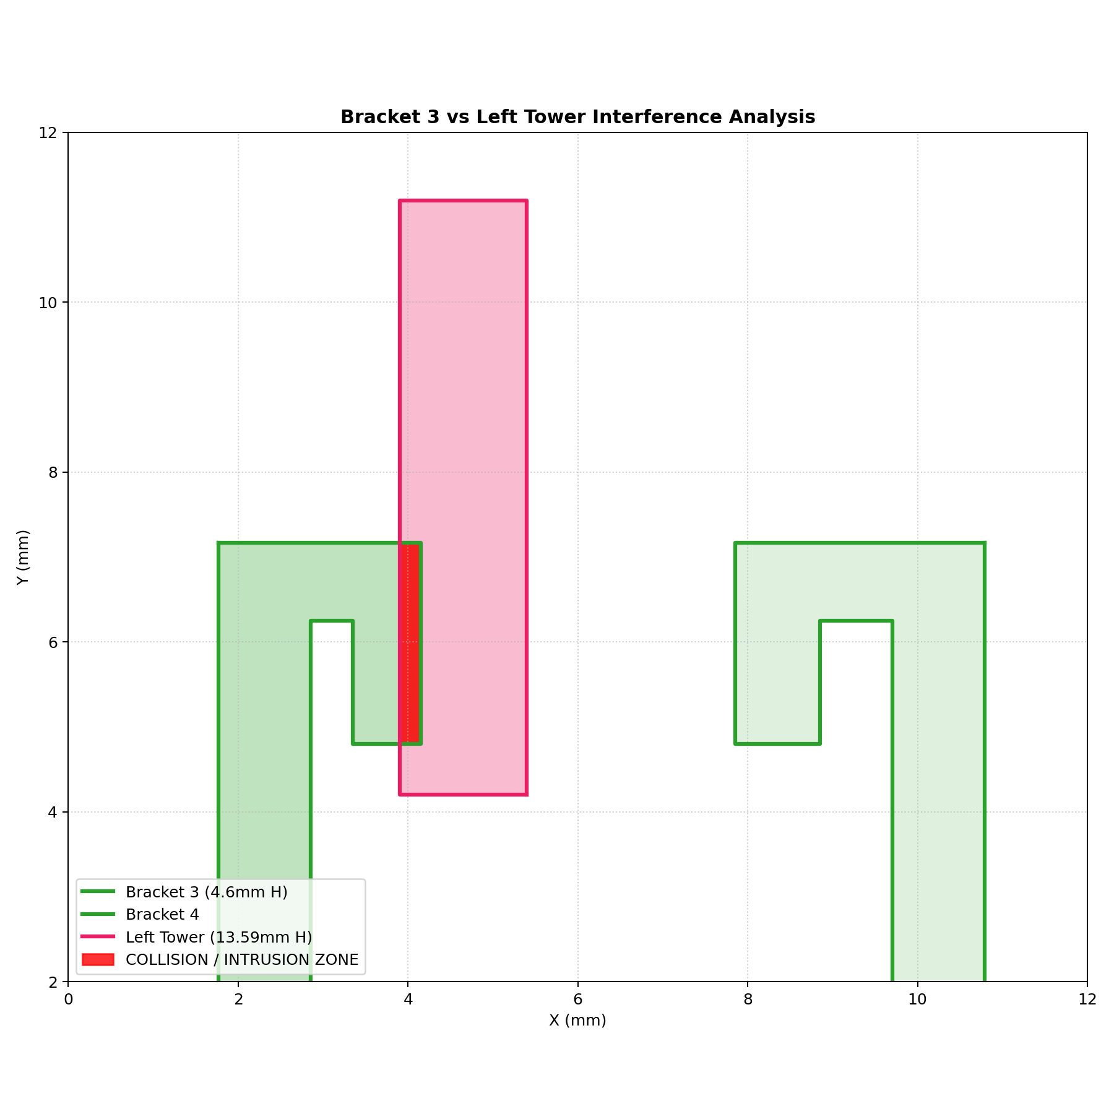
testing/bracket3_tower_interference.png
