elliotmartin92/kia-socket/testing/bracket_change_diagram.png

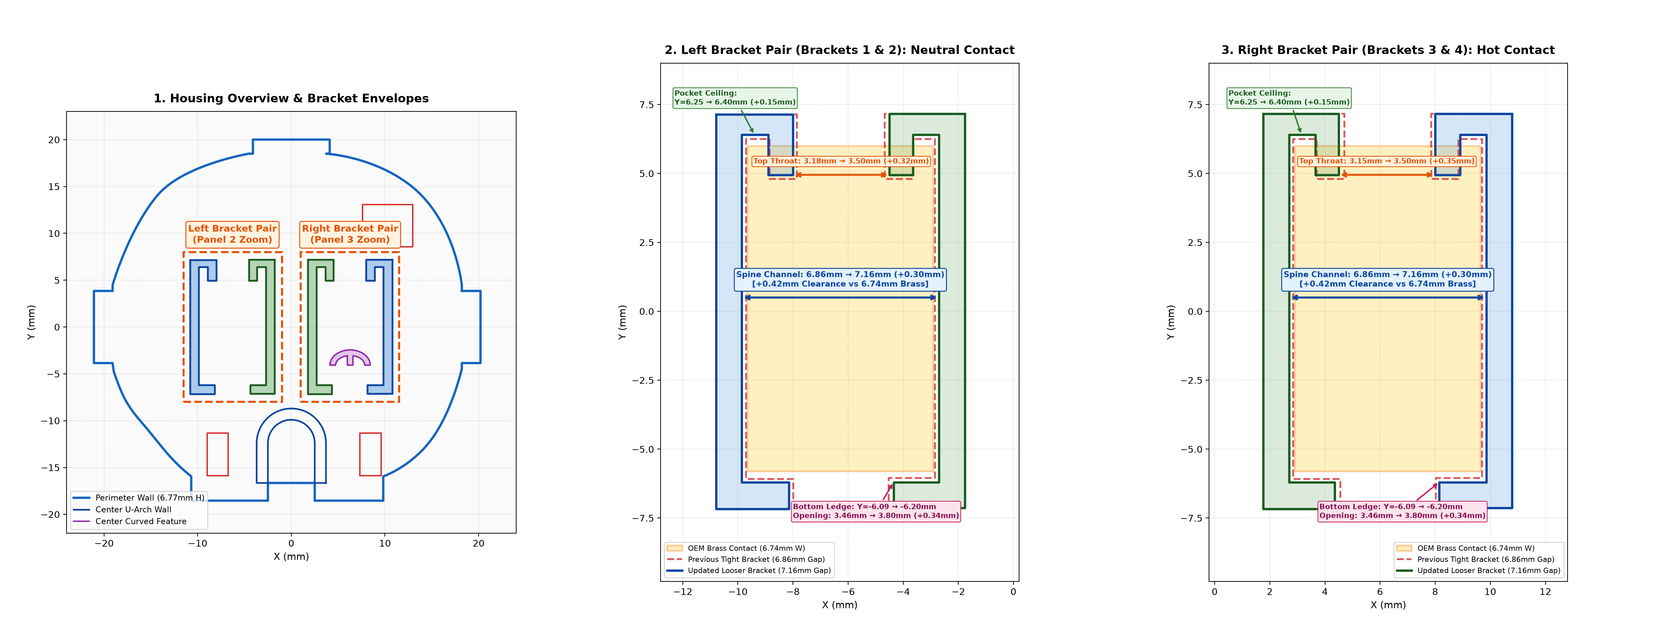
testing/bracket_change_diagram.png
