elliotmartin92/kia-socket/testing/bracket_channels_gap_preview.png

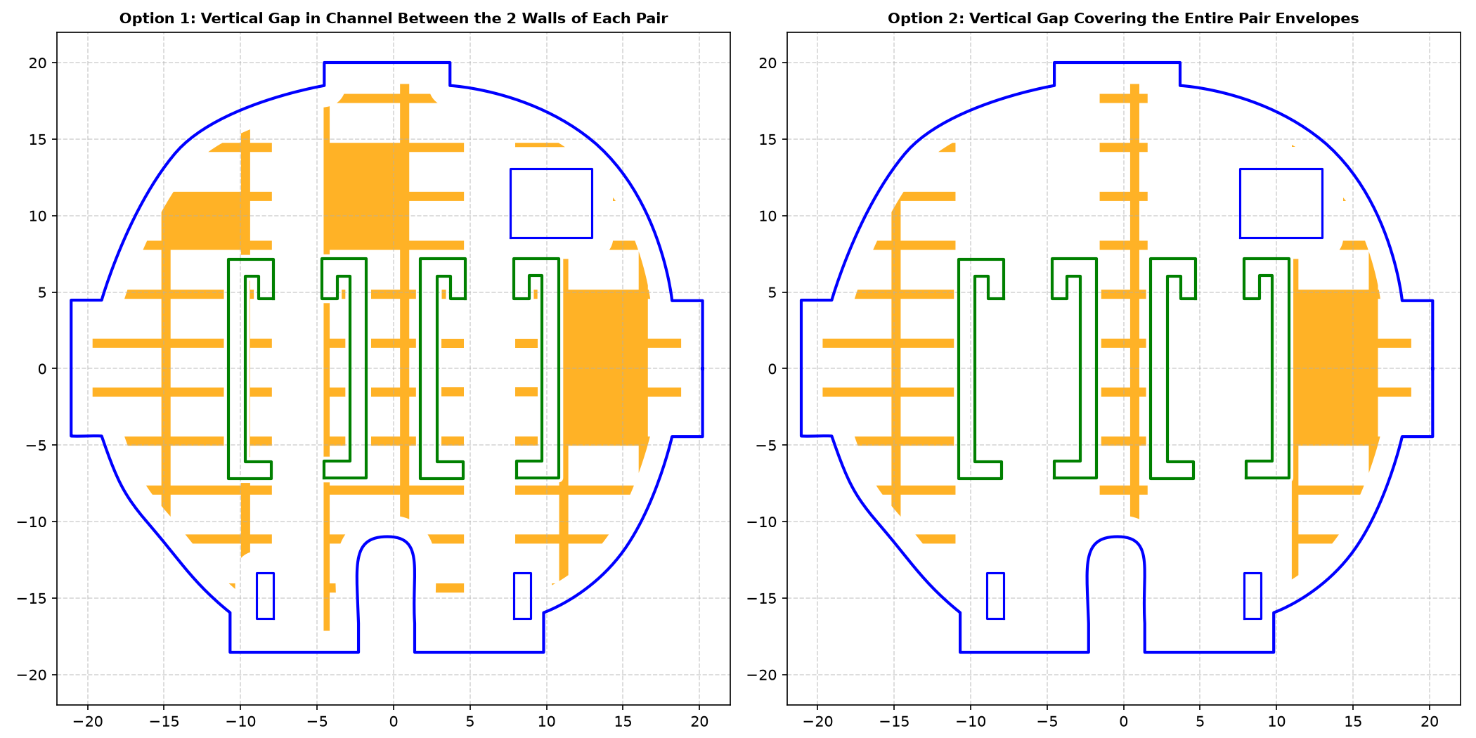
testing/bracket_channels_gap_preview.png
