elliotmartin92/kia-socket/testing/bracket_current_dimensions.png

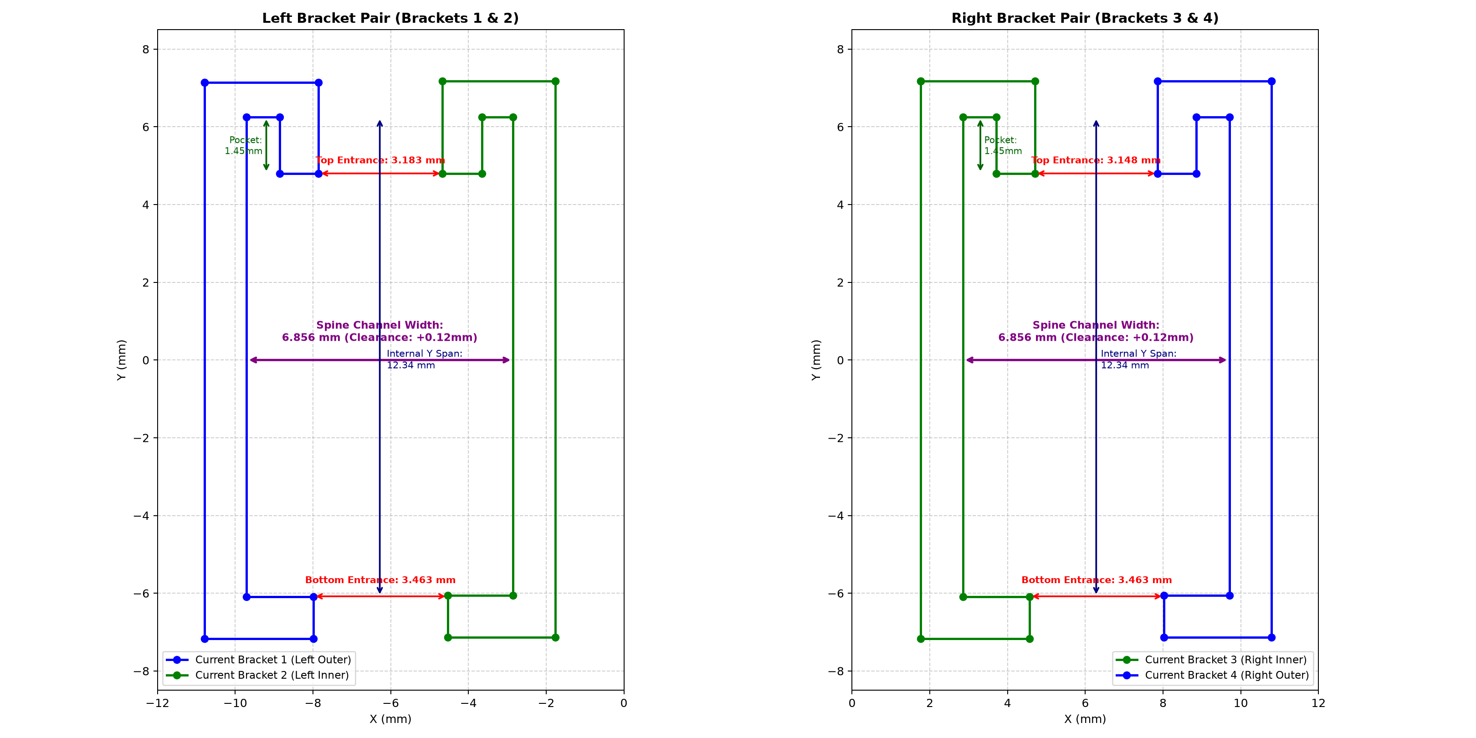
testing/bracket_current_dimensions.png
