elliotmartin92/kia-socket/testing/bracket_gap_adjusted_comparison.png

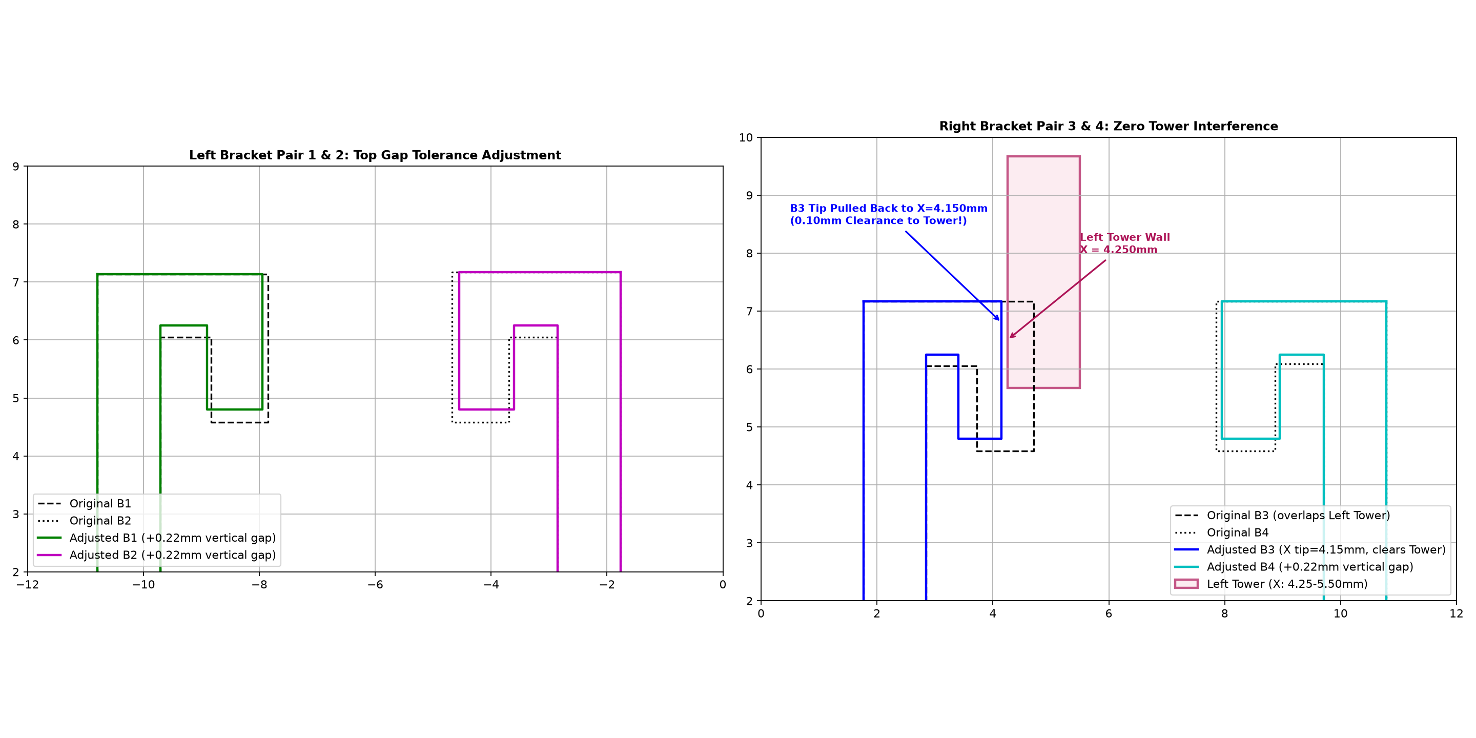
testing/bracket_gap_adjusted_comparison.png
