elliotmartin92/kia-socket/testing/bracket_landmarks.png

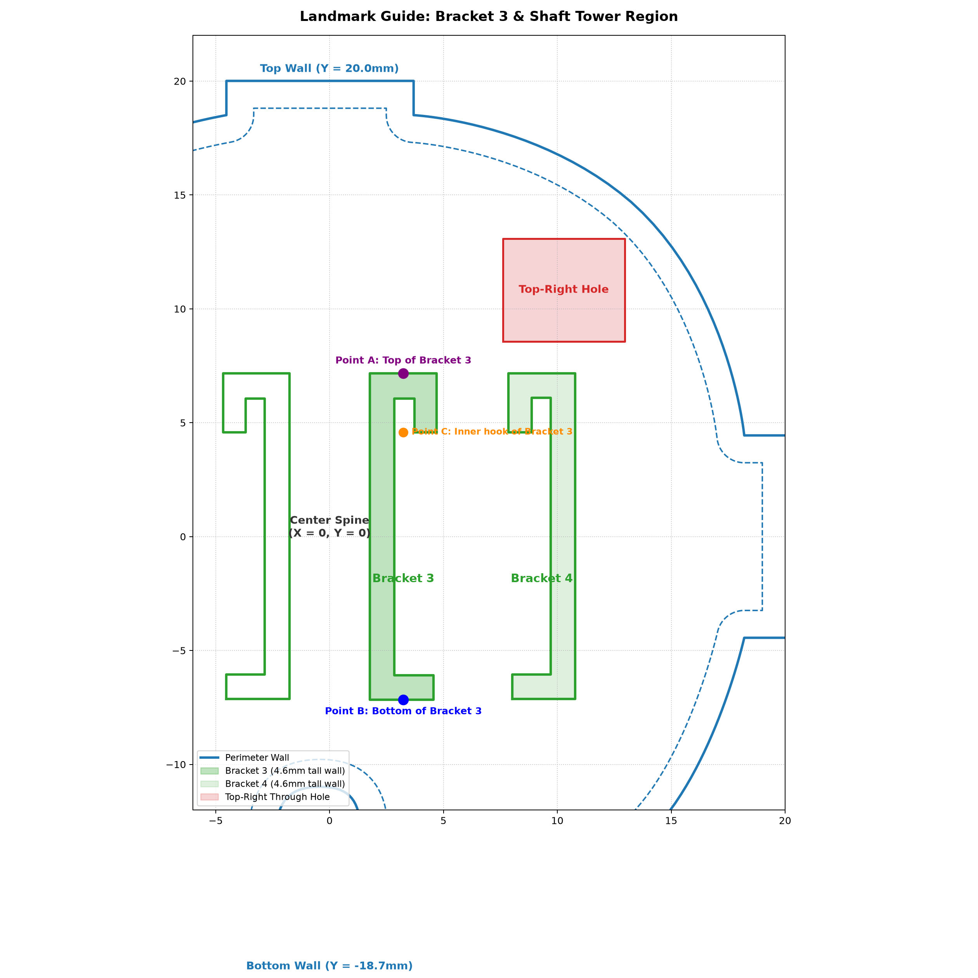
testing/bracket_landmarks.png
