elliotmartin92/kia-socket/testing/bracket_looser_tolerance_comparison.png

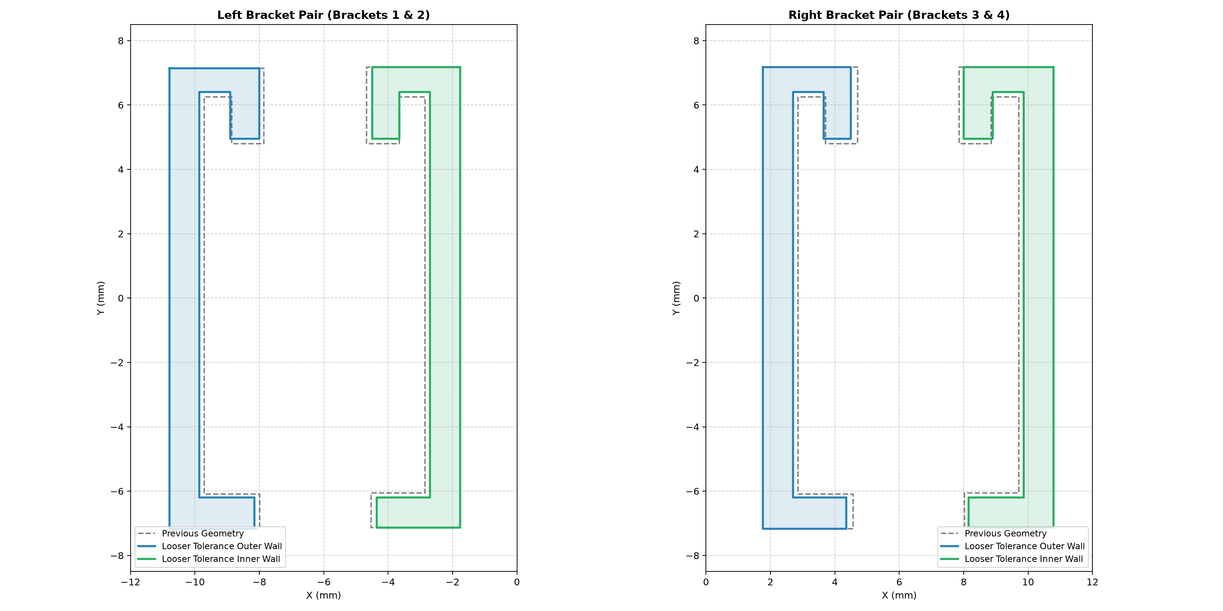
testing/bracket_looser_tolerance_comparison.png
