elliotmartin92/kia-socket/testing/bracket_seating_ribs_preview.png

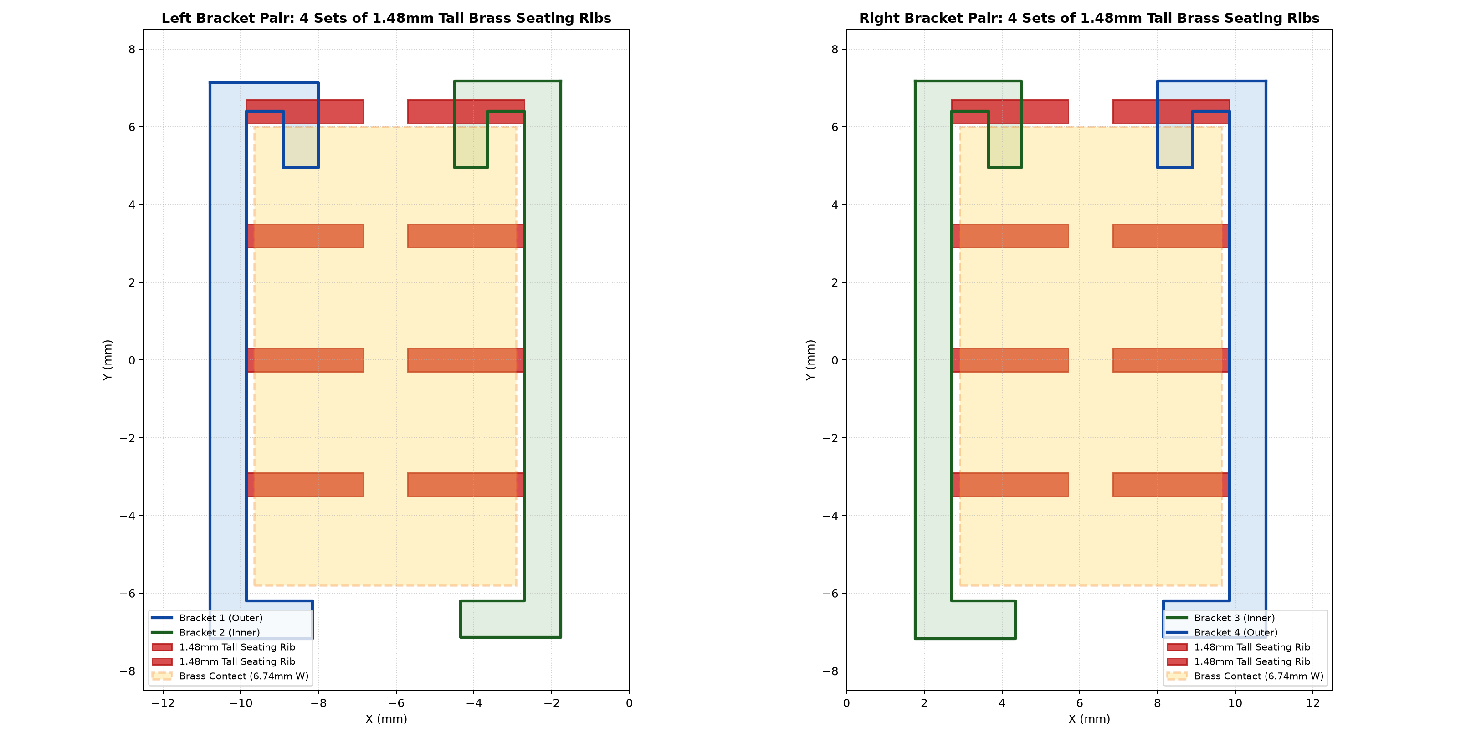
testing/bracket_seating_ribs_preview.png
