elliotmartin92/kia-socket/testing/bracket_top_gap_inspection.png

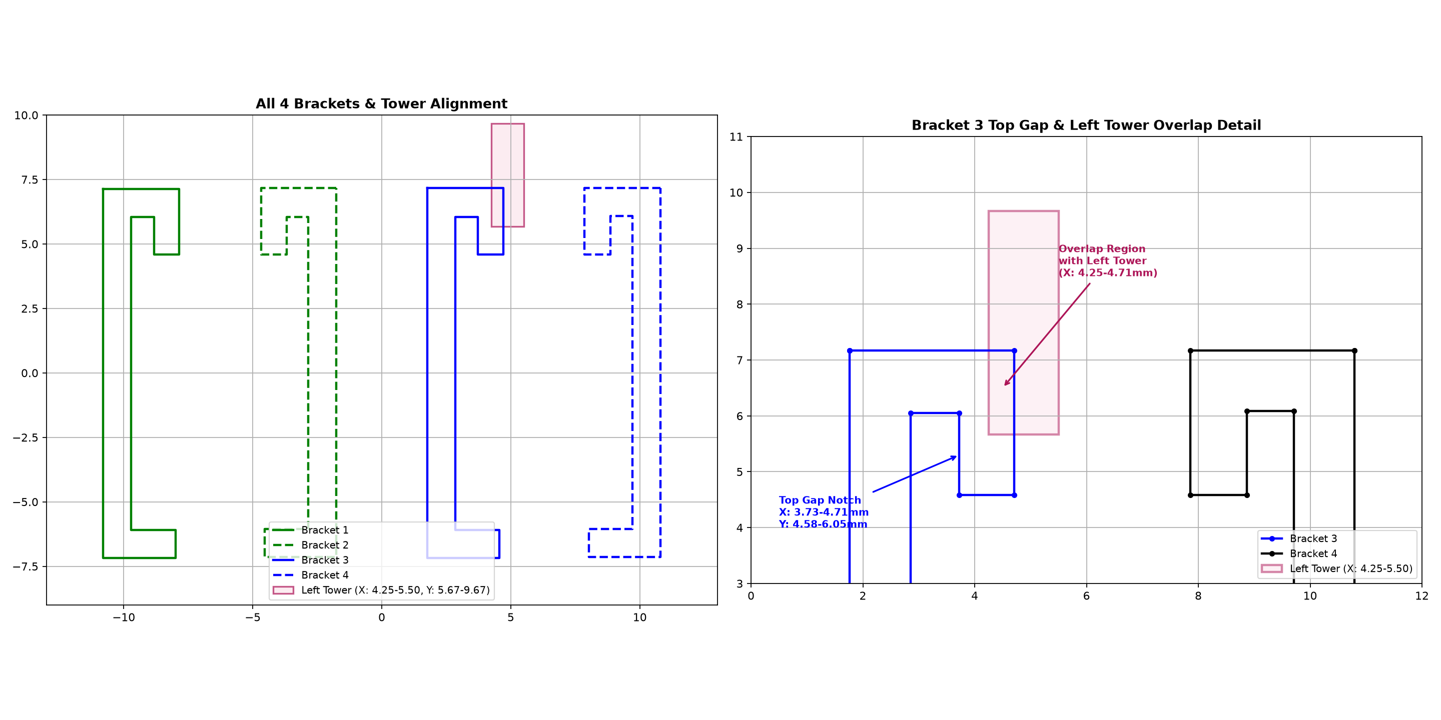
testing/bracket_top_gap_inspection.png
