elliotmartin92/kia-socket/testing/brackets_vs_slits_comparison.png

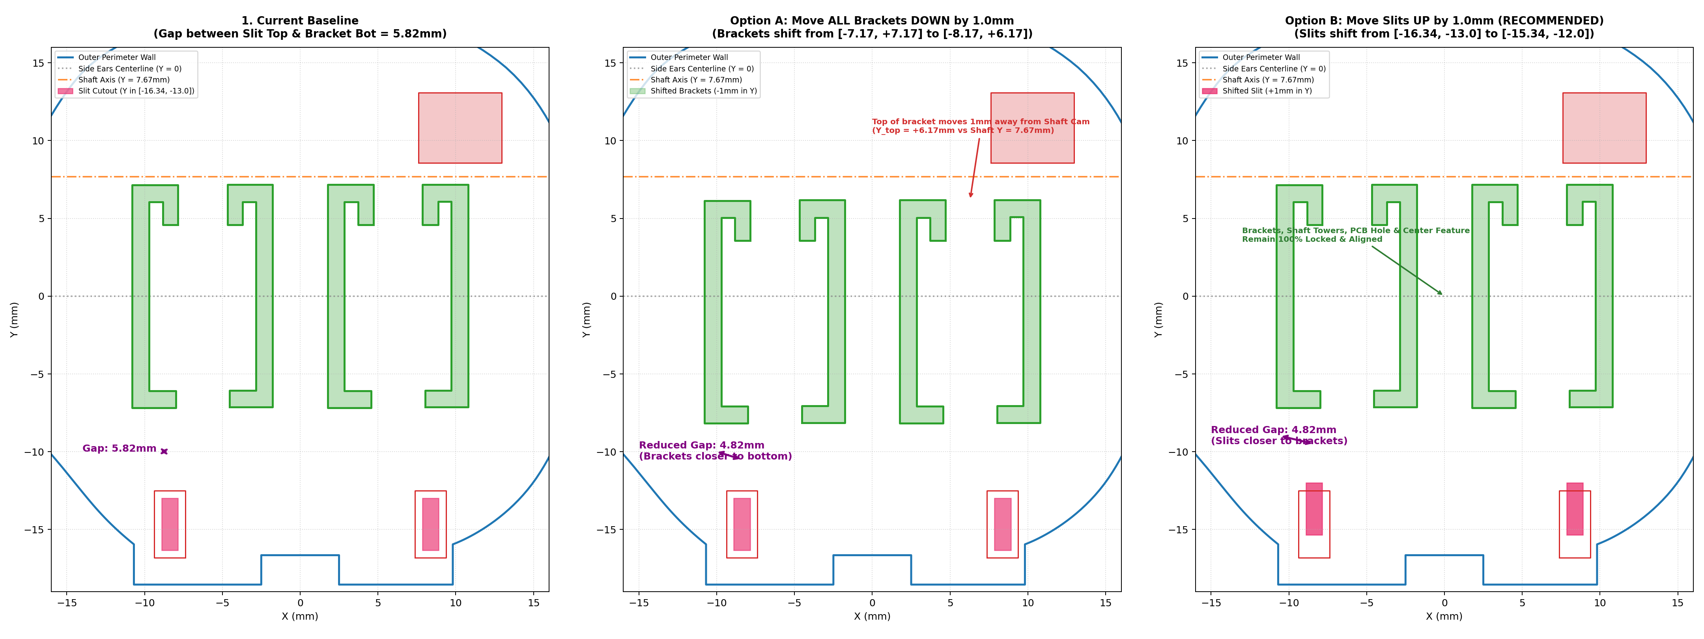
testing/brackets_vs_slits_comparison.png
