elliotmartin92/kia-socket/testing/brass_and_lever_clearance_analysis.png

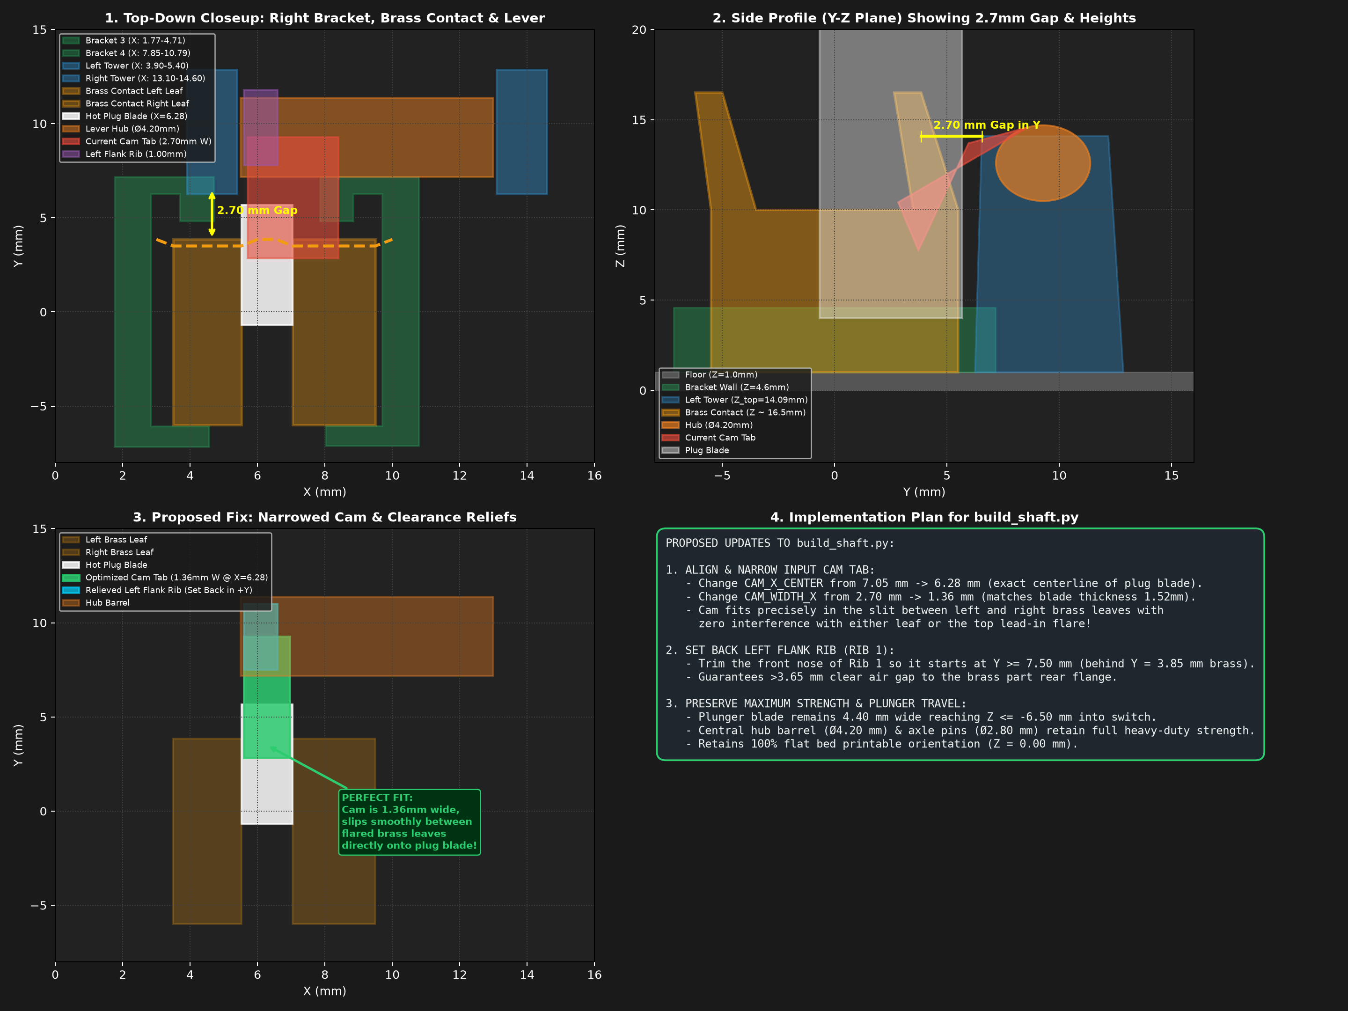
testing/brass_and_lever_clearance_analysis.png
