elliotmartin92/kia-socket/testing/brass_mechanism_interference_analysis.png

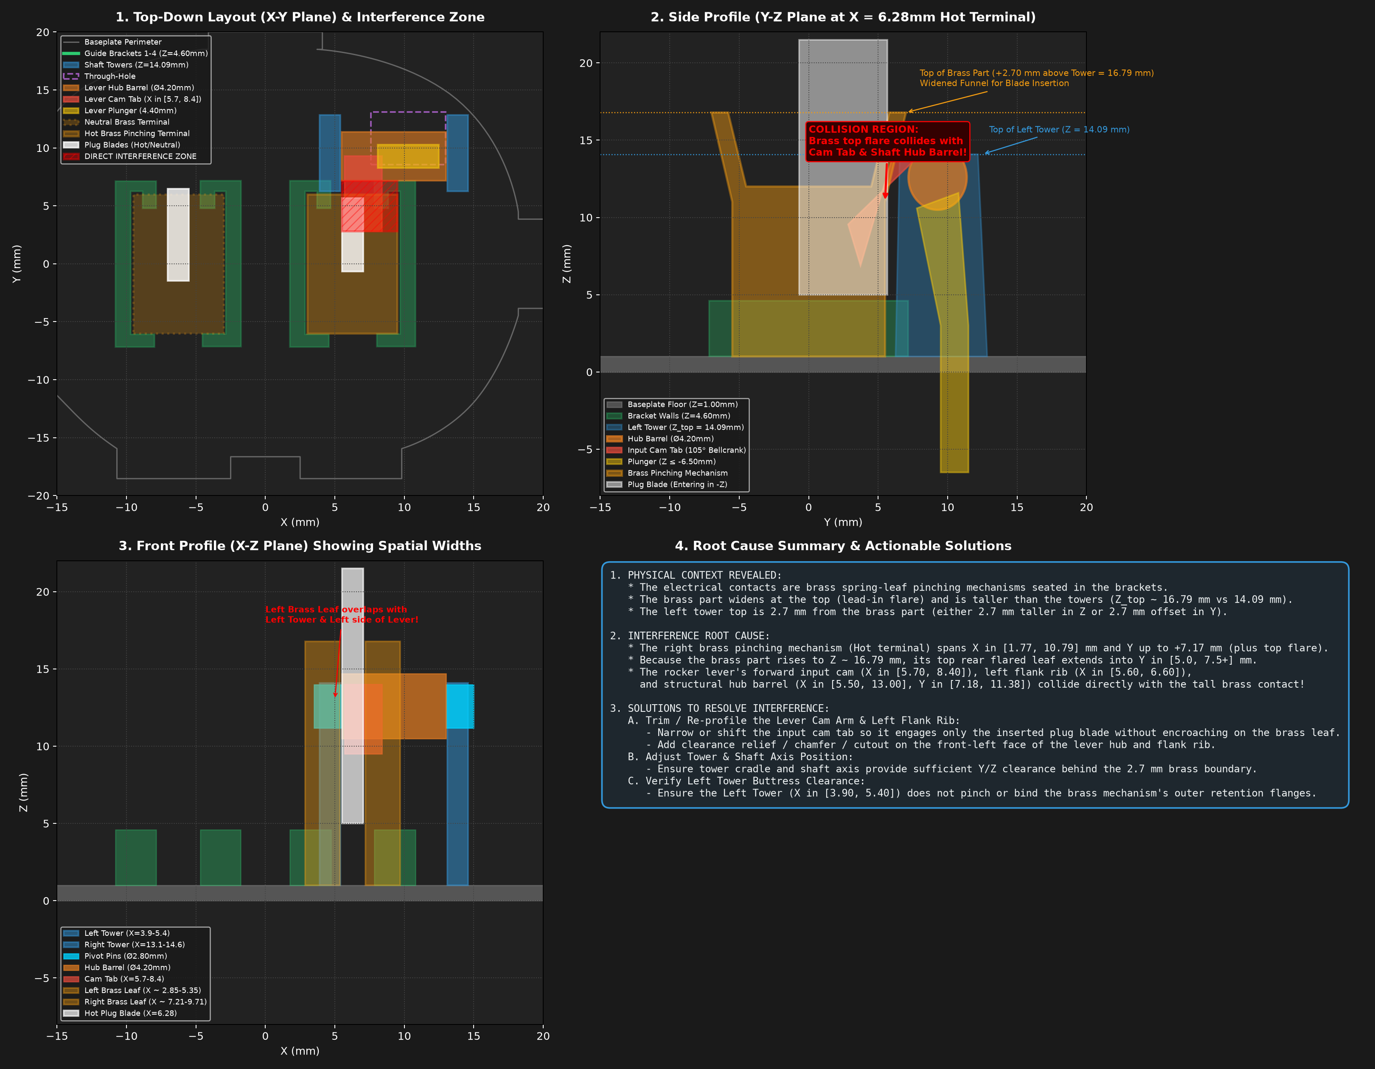
testing/brass_mechanism_interference_analysis.png
