elliotmartin92/kia-socket/testing/bridge_rib_detail.png

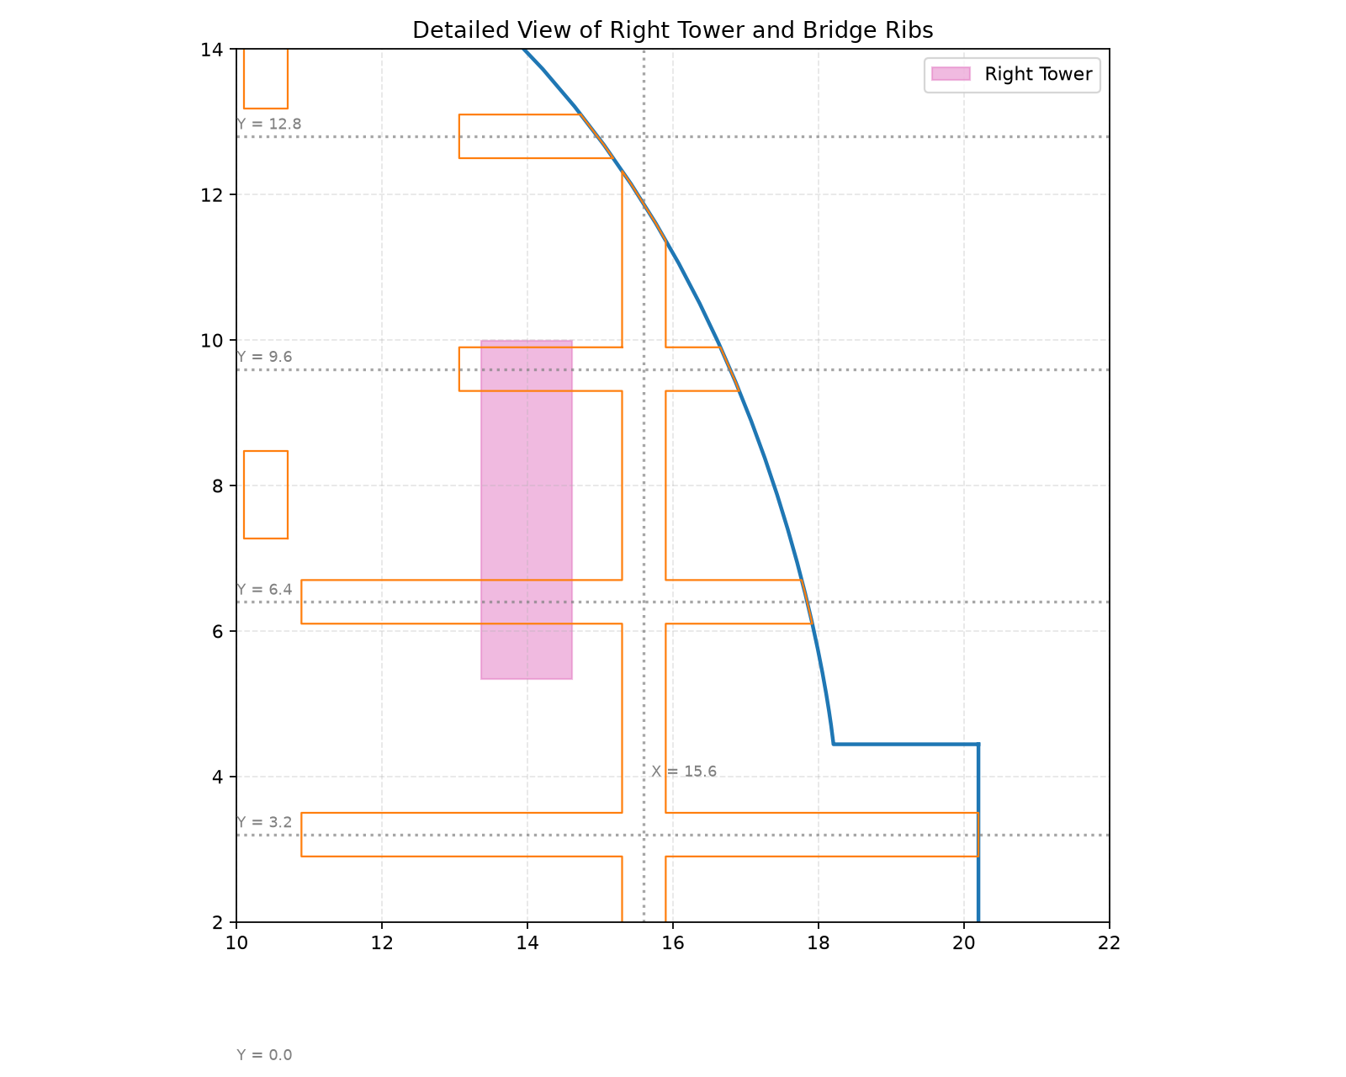
testing/bridge_rib_detail.png
