elliotmartin92/kia-socket/testing/bridge_rib_inspect.png

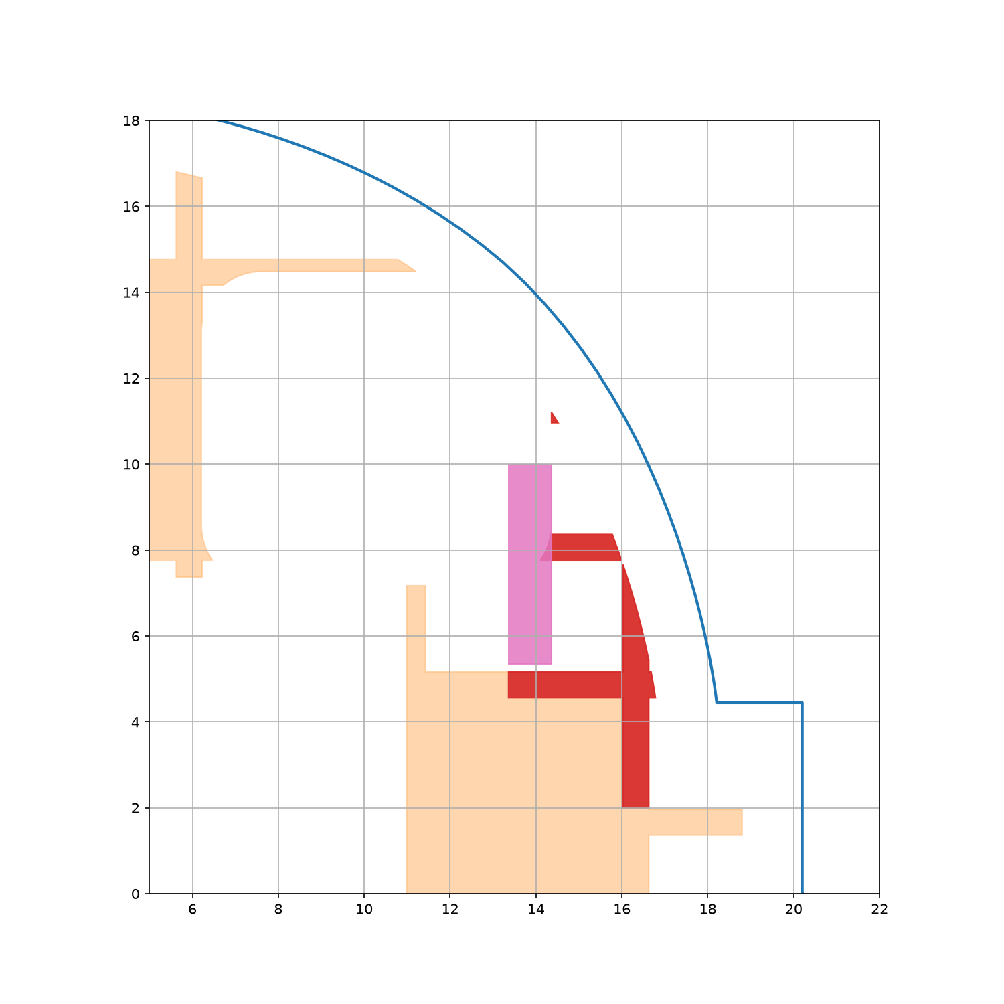
testing/bridge_rib_inspect.png
