elliotmartin92/kia-socket/testing/buttress_exact_alignment_preview.png

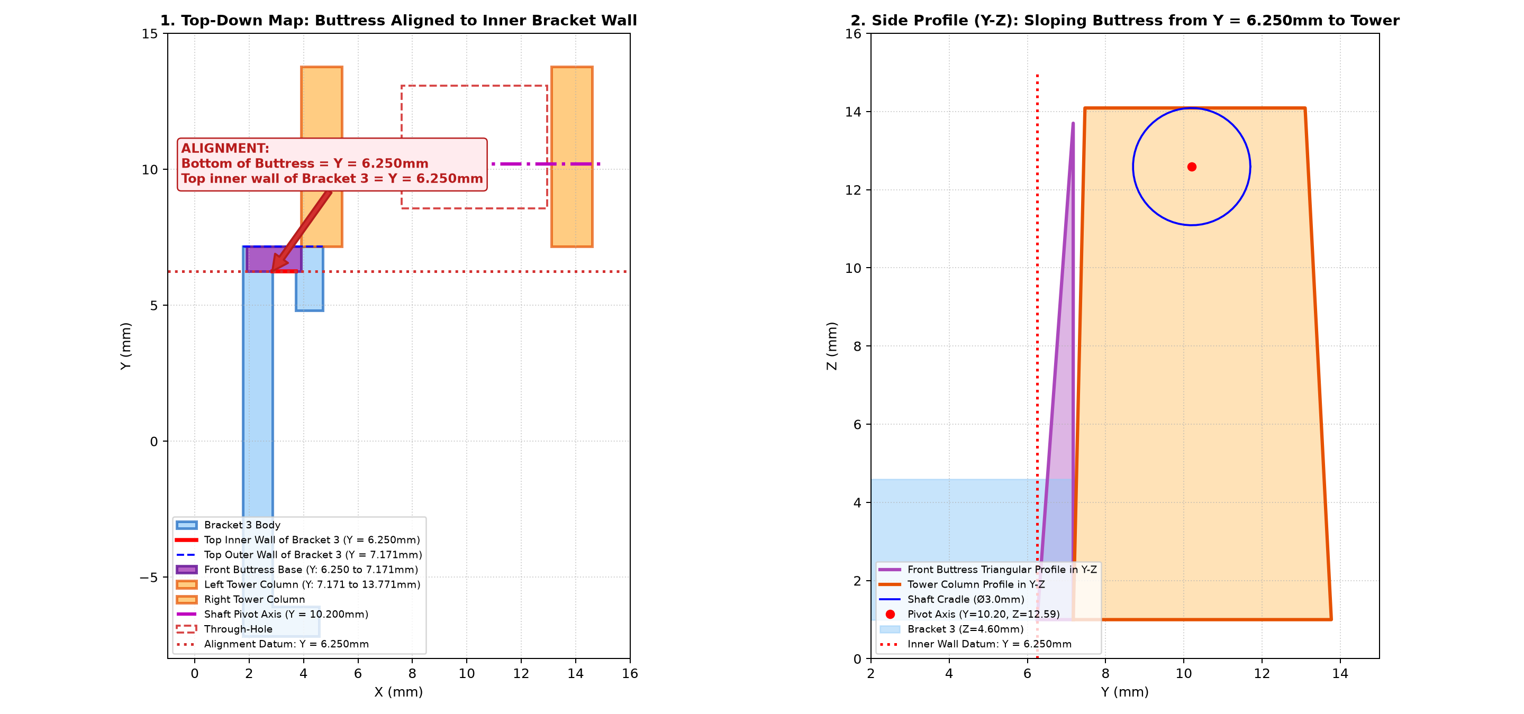
testing/buttress_exact_alignment_preview.png
