elliotmartin92/kia-socket/testing/cam_junction_inspect.png

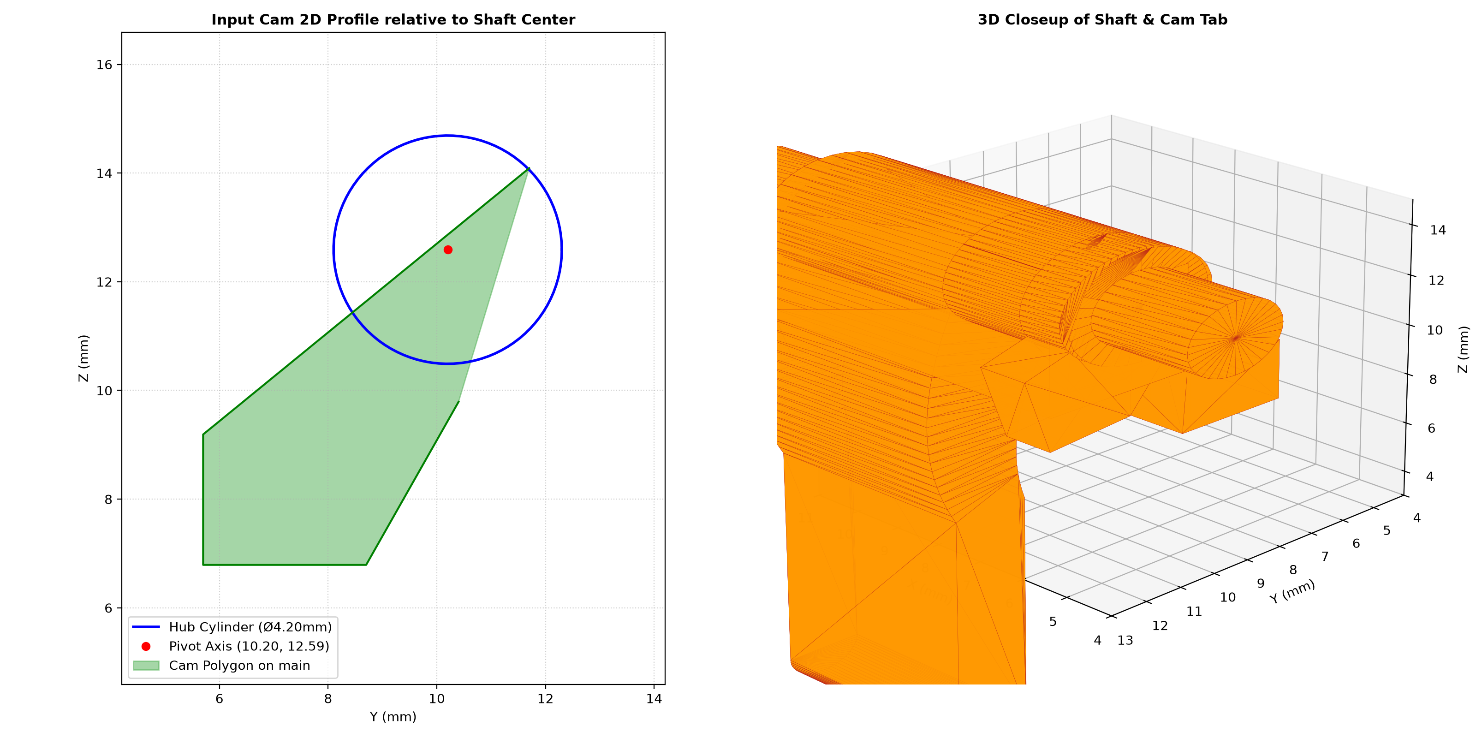
testing/cam_junction_inspect.png
