elliotmartin92/kia-socket/testing/central_gap_preview.png

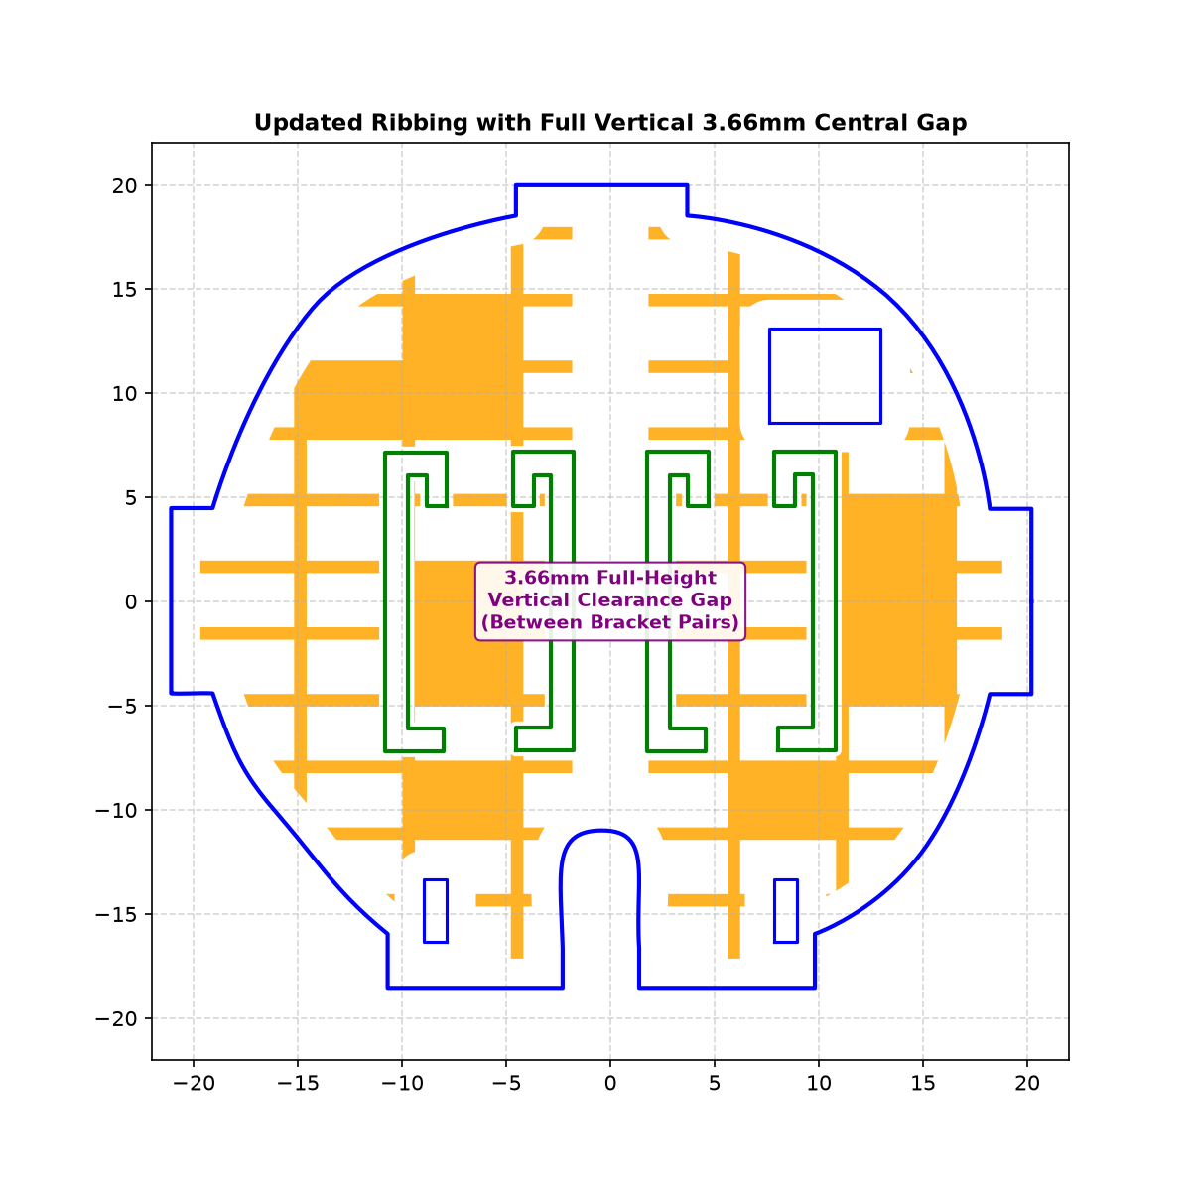
testing/central_gap_preview.png
