elliotmartin92/kia-socket/testing/clean_arch_test.png

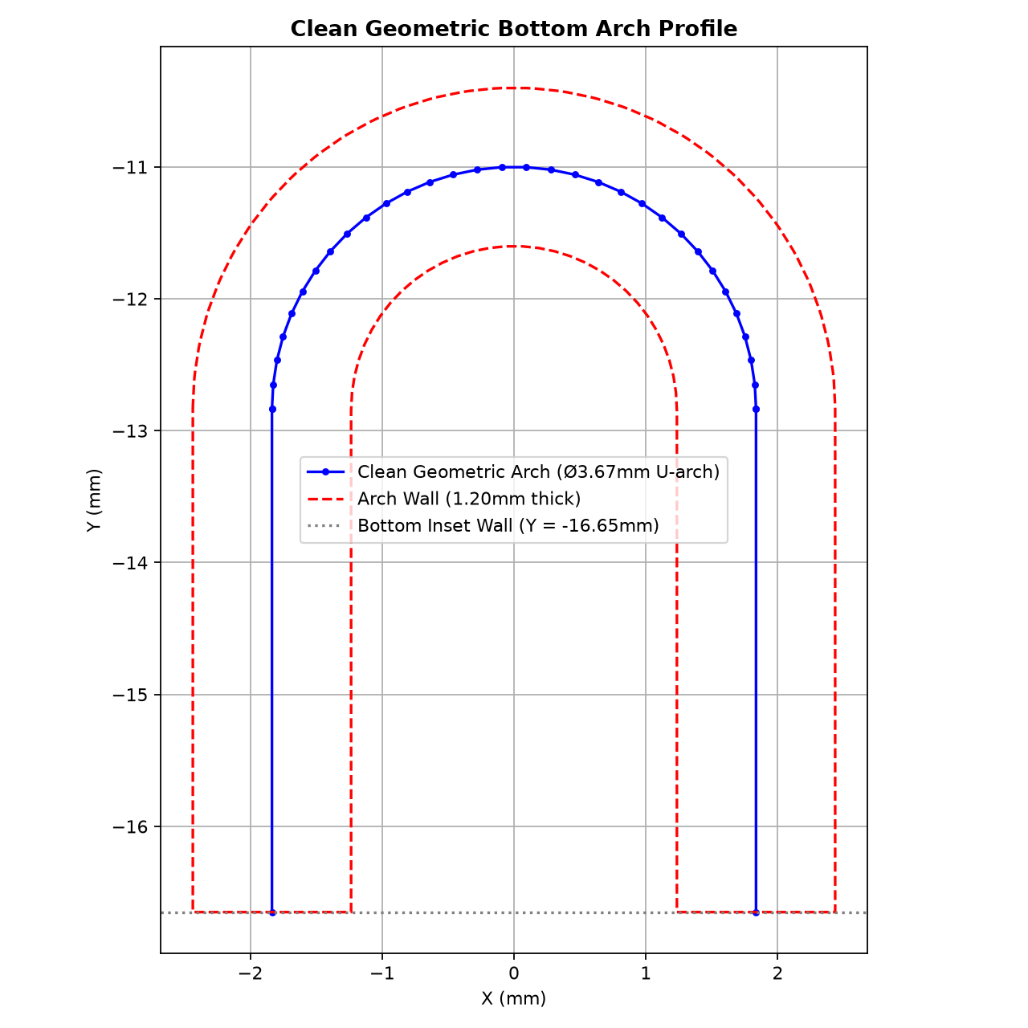
testing/clean_arch_test.png
