elliotmartin92/kia-socket/testing/clean_clip_test.png

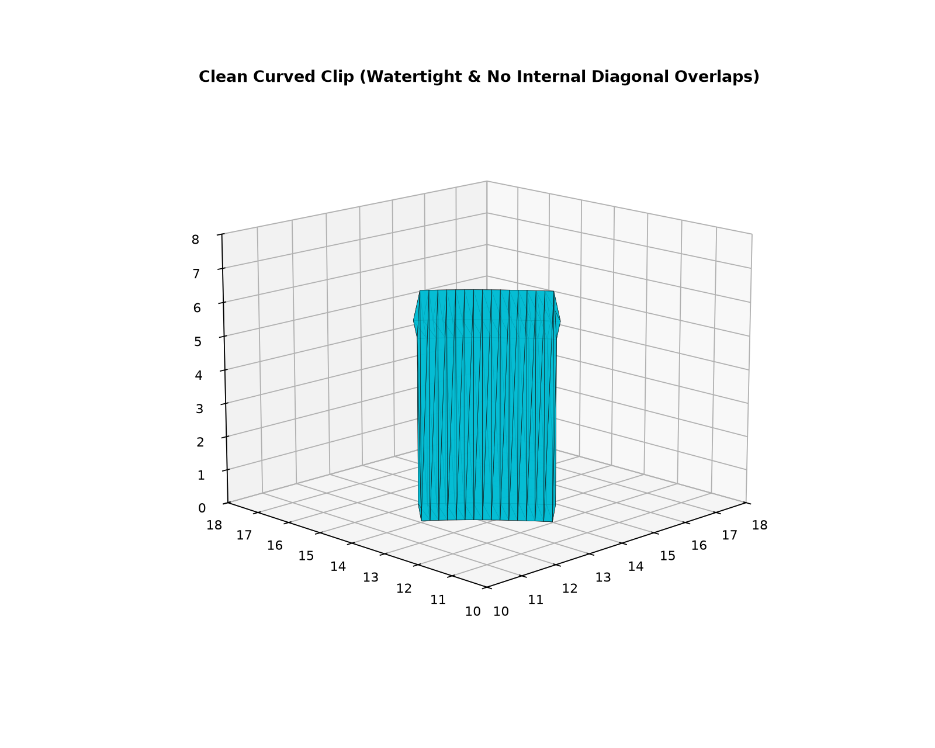
testing/clean_clip_test.png
