elliotmartin92/kia-socket/testing/clean_u_cradle.png

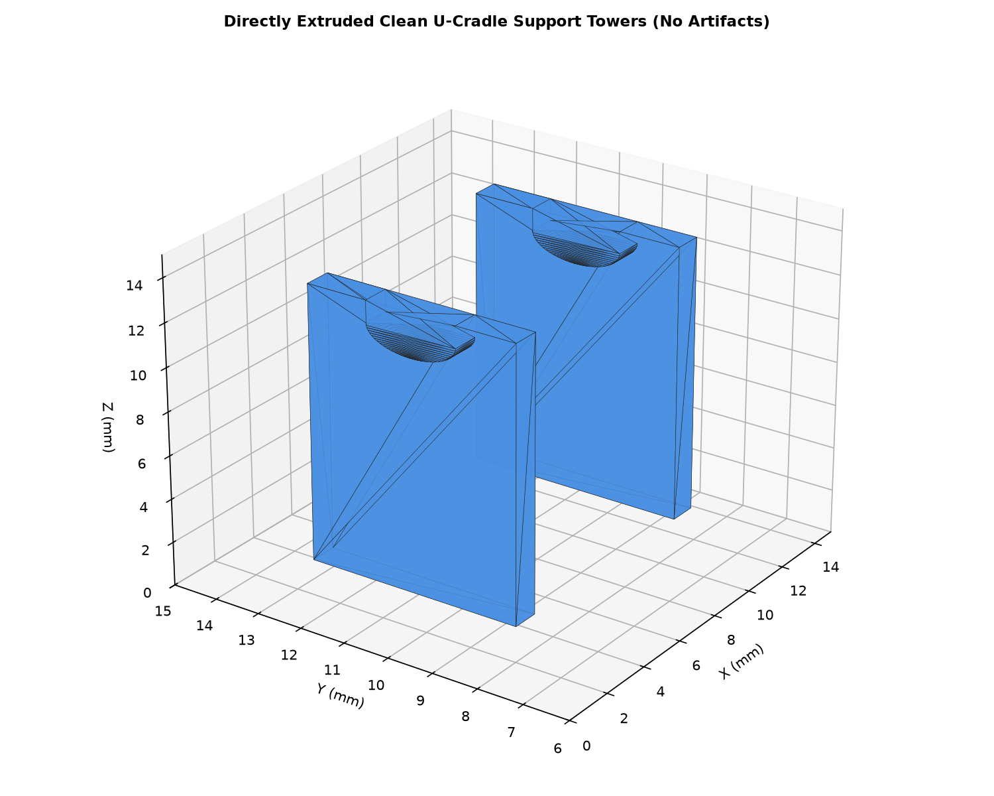
testing/clean_u_cradle.png
