elliotmartin92/kia-socket/testing/clip_45.0_detailed_stl.png

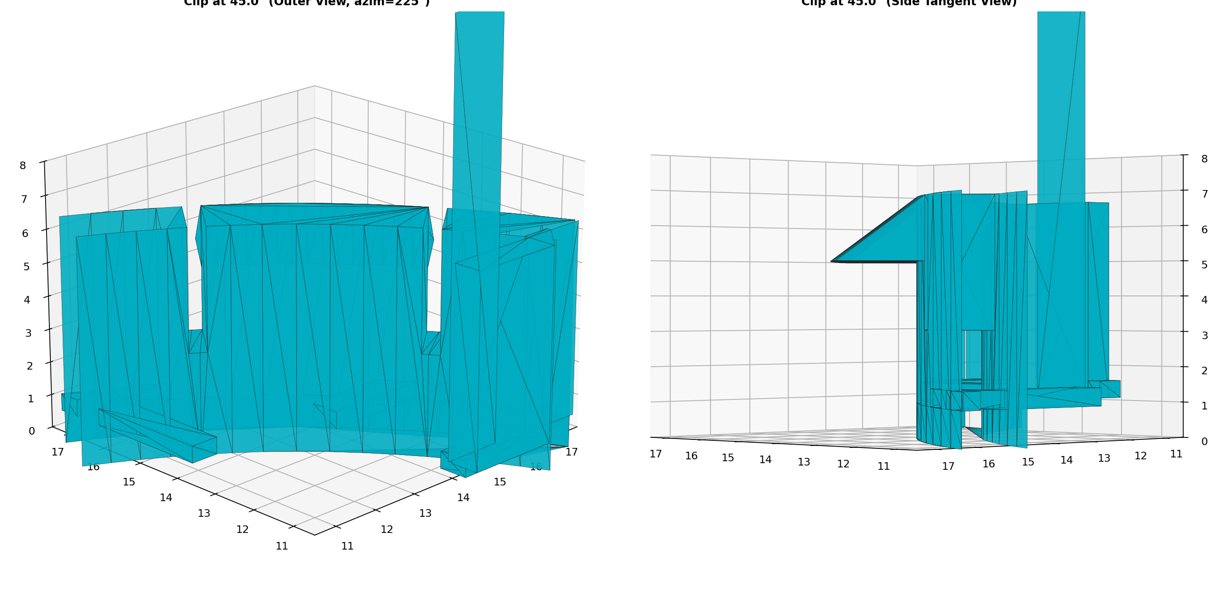
testing/clip_45.0_detailed_stl.png
