elliotmartin92/kia-socket/testing/clip_45_current_support.png

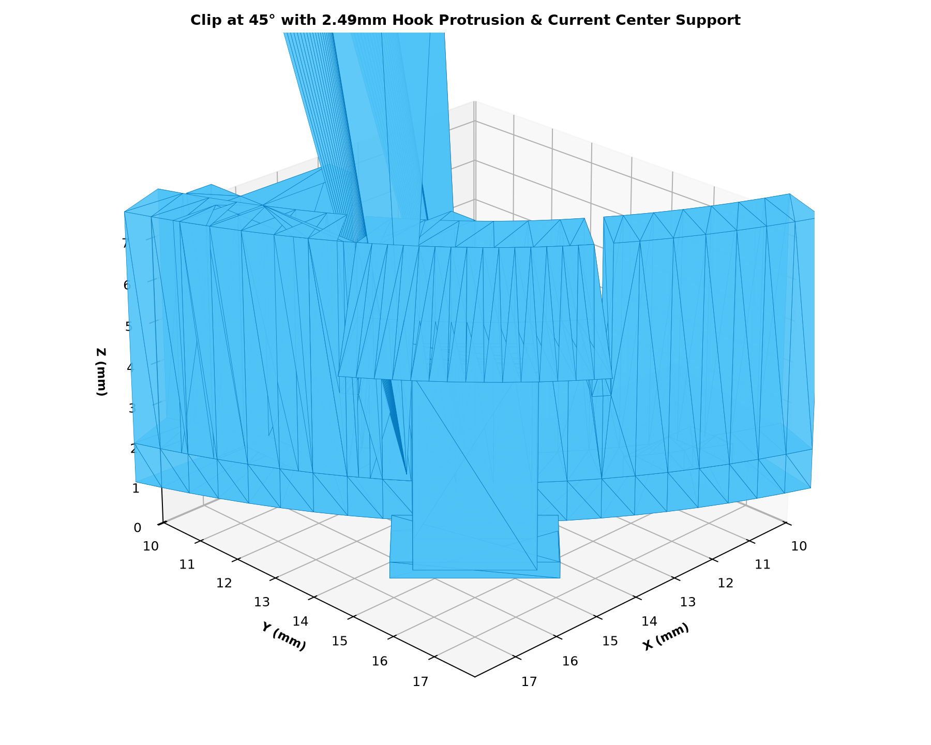
testing/clip_45_current_support.png
