elliotmartin92/kia-socket/testing/clip_135.0_detailed_stl.png

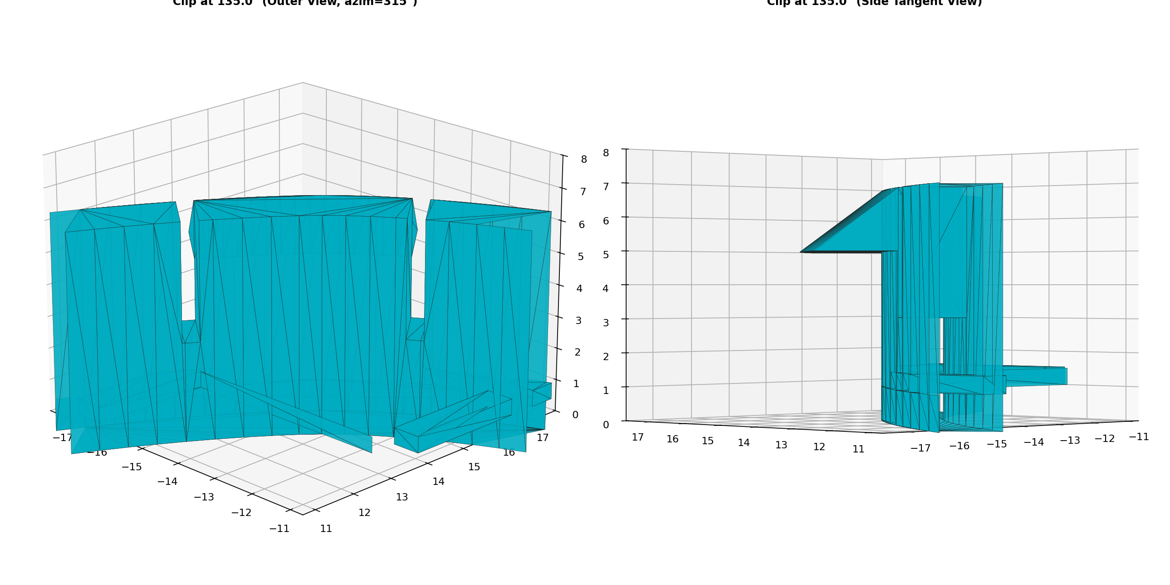
testing/clip_135.0_detailed_stl.png
