elliotmartin92/kia-socket/testing/clip_214.5_detailed_stl.png

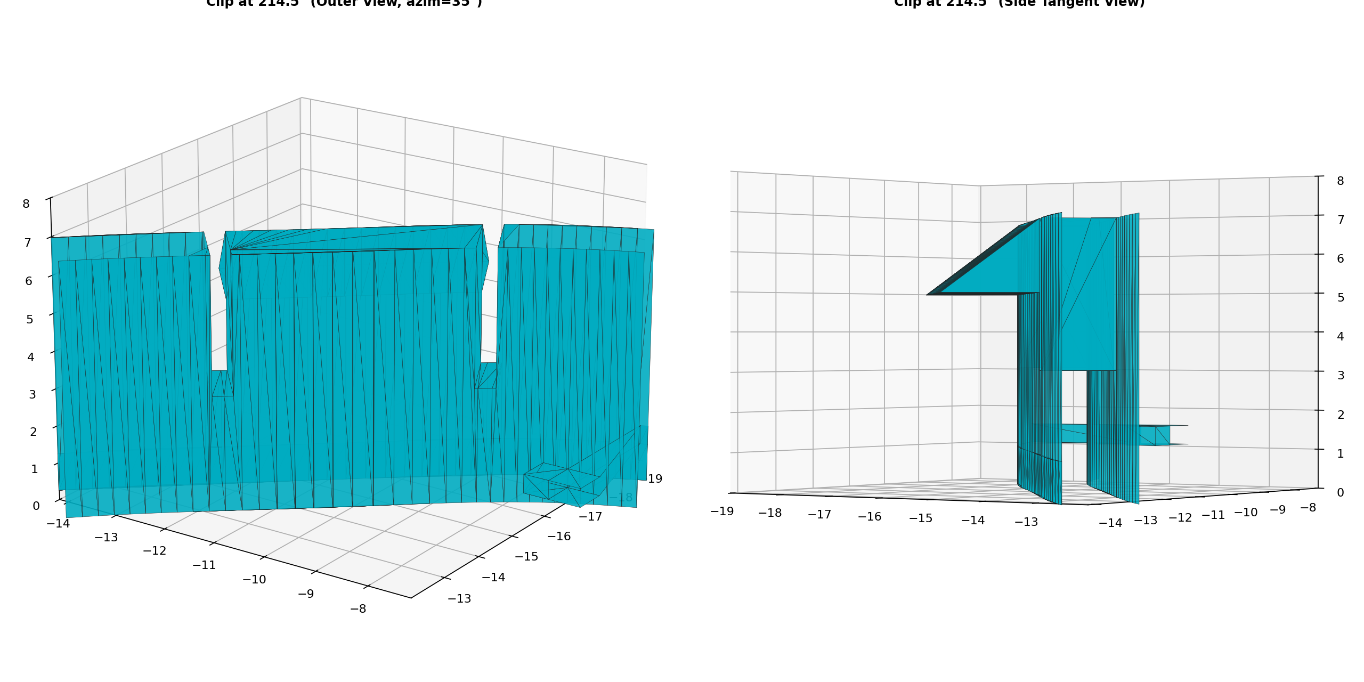
testing/clip_214.5_detailed_stl.png
