elliotmartin92/kia-socket/testing/clip_225_detailed_stl.png

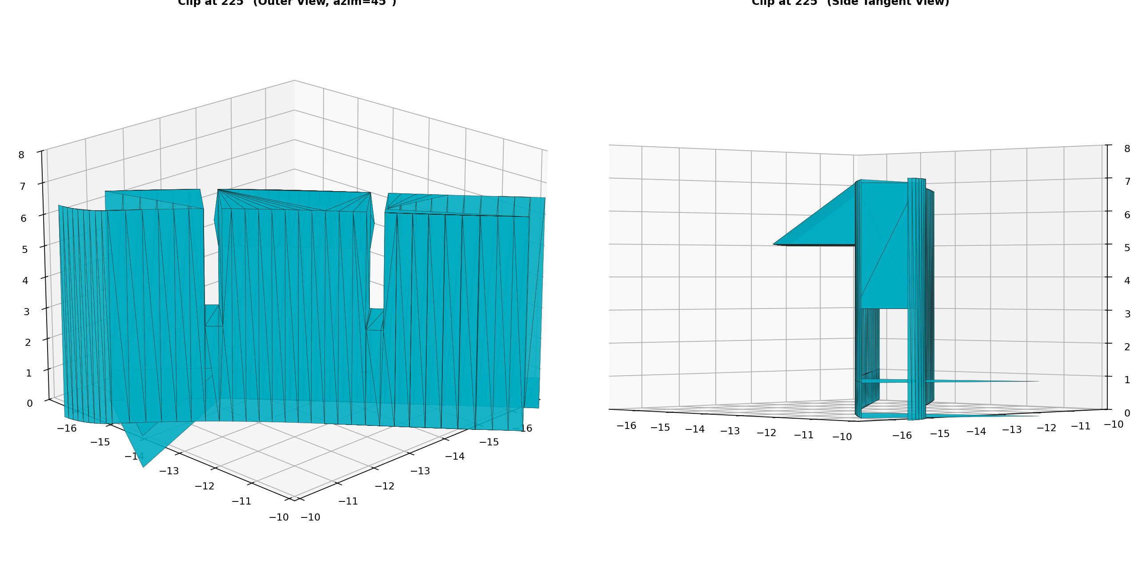
testing/clip_225_detailed_stl.png
