elliotmartin92/kia-socket/testing/clip_315_detailed_stl.png

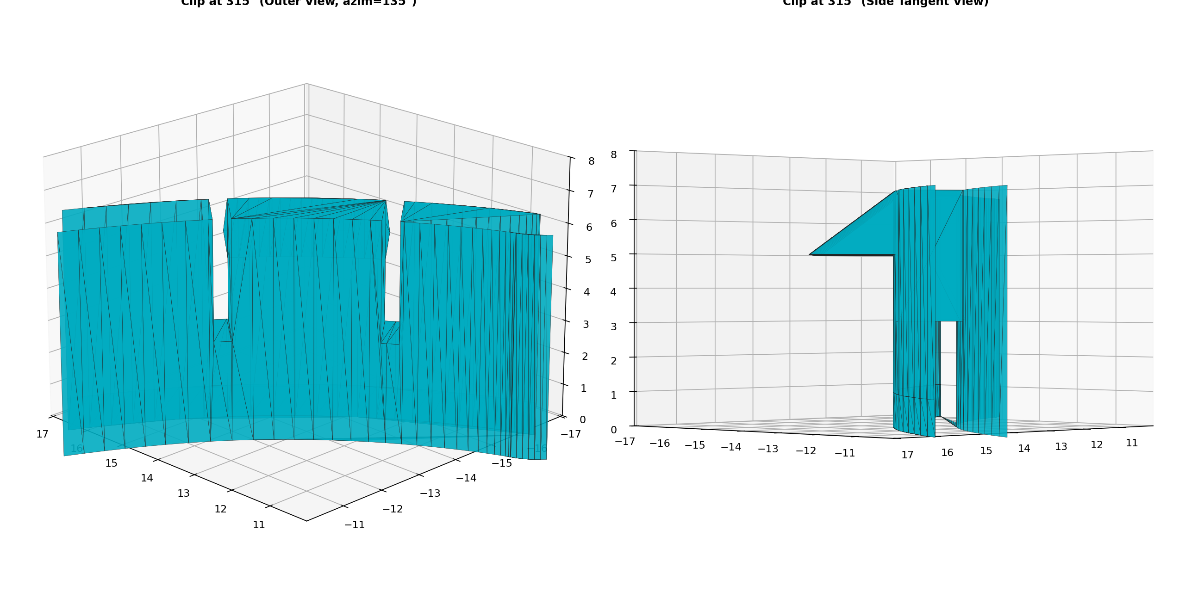
testing/clip_315_detailed_stl.png
