elliotmartin92/kia-socket/testing/clip_and_rib_details.png

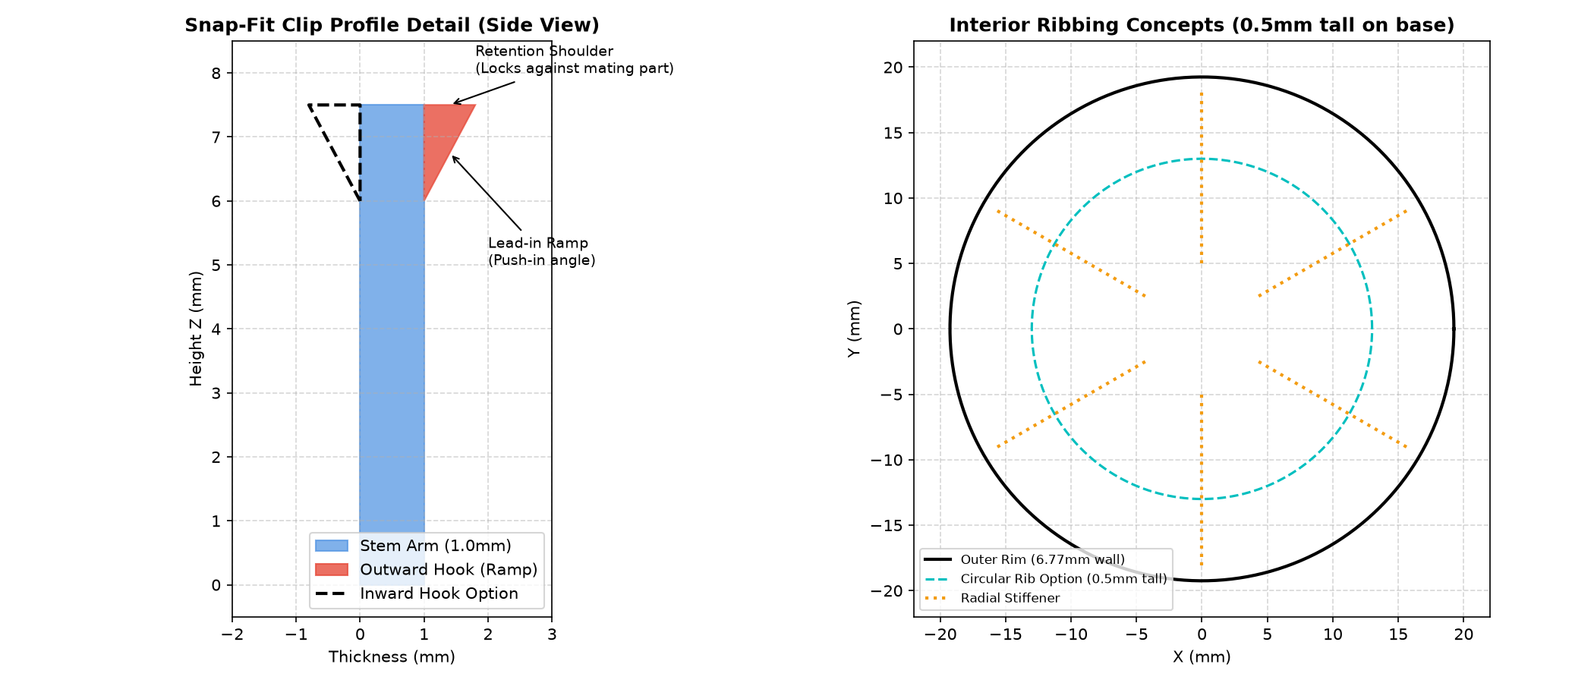
testing/clip_and_rib_details.png
