elliotmartin92/kia-socket/testing/clip_closeup_views.png

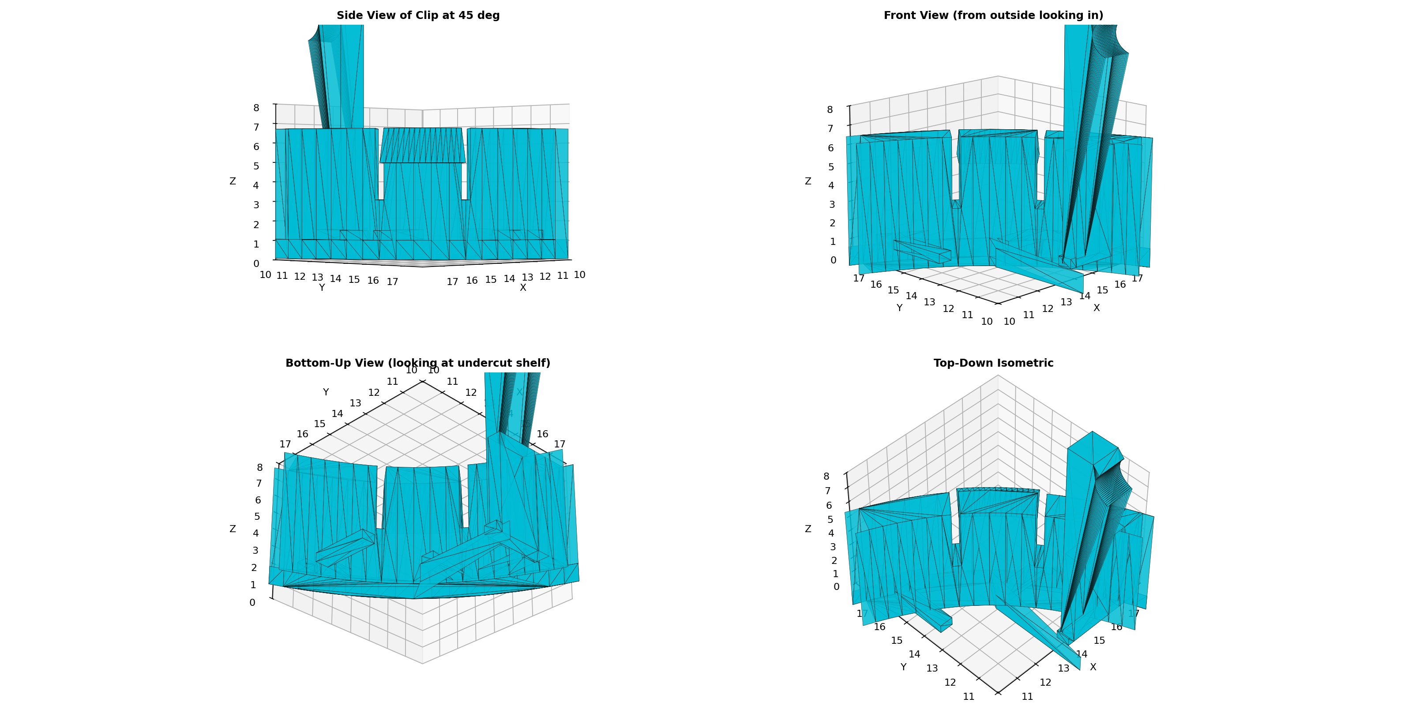
testing/clip_closeup_views.png
