elliotmartin92/kia-socket/testing/clip_extension_preview.png

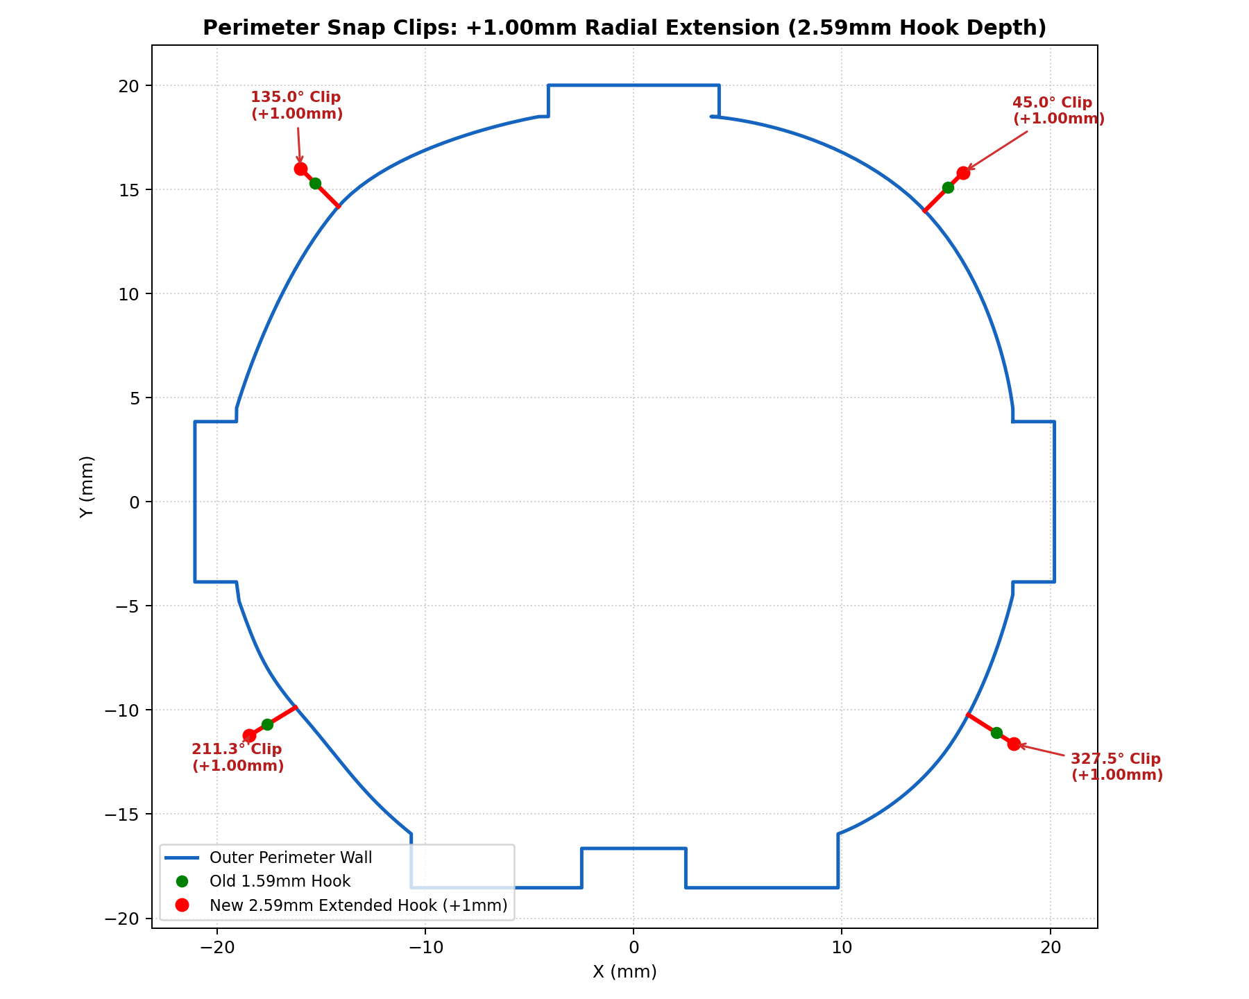
testing/clip_extension_preview.png
