elliotmartin92/kia-socket/testing/clip_halfway_verification.png

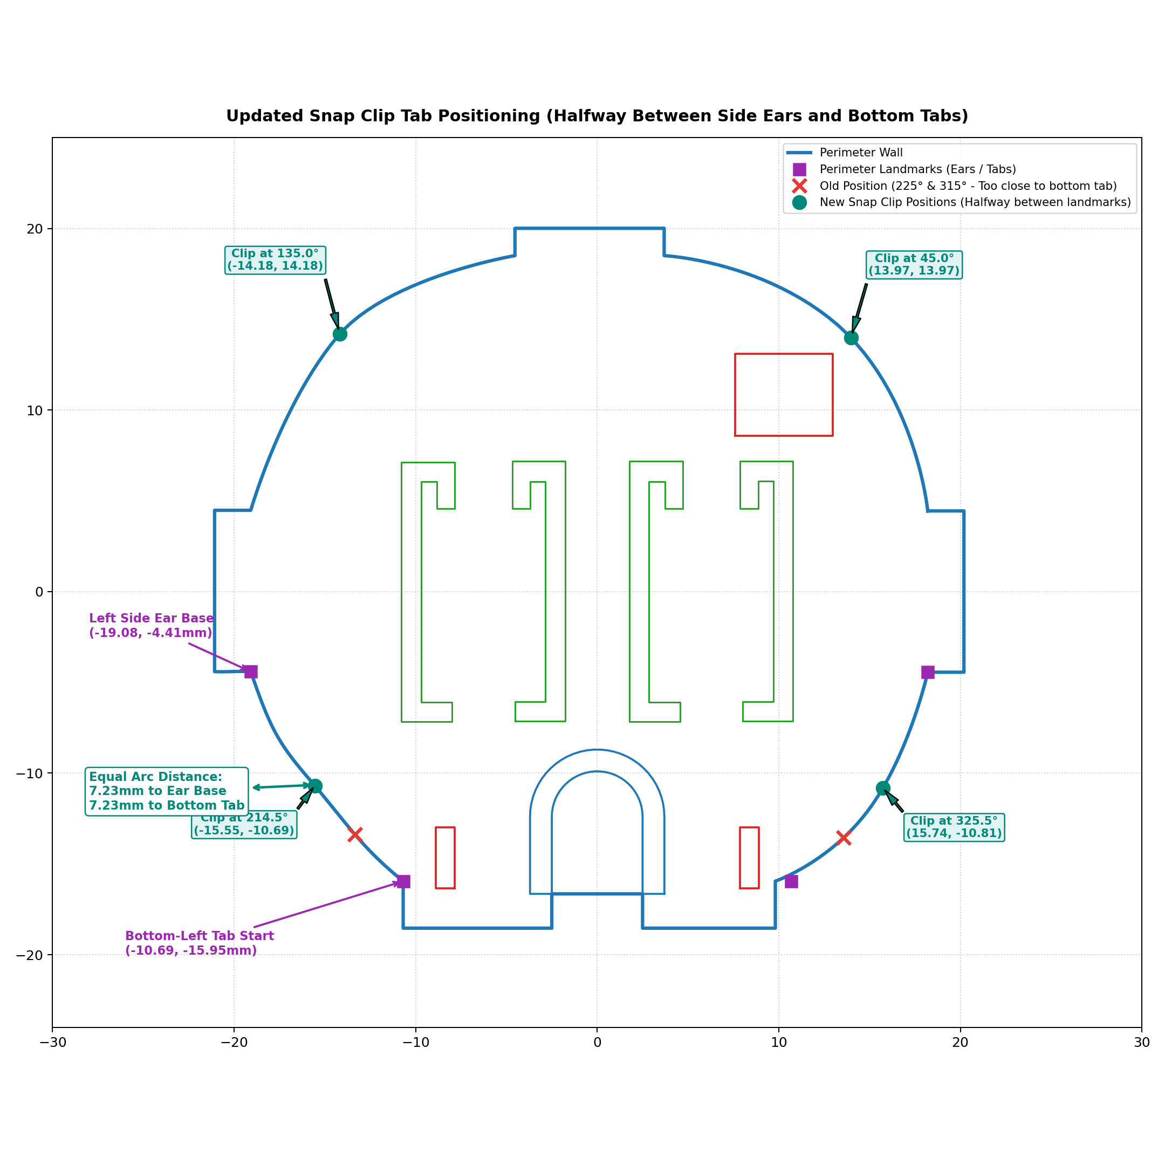
testing/clip_halfway_verification.png
