elliotmartin92/kia-socket/testing/clip_profile_rz.png

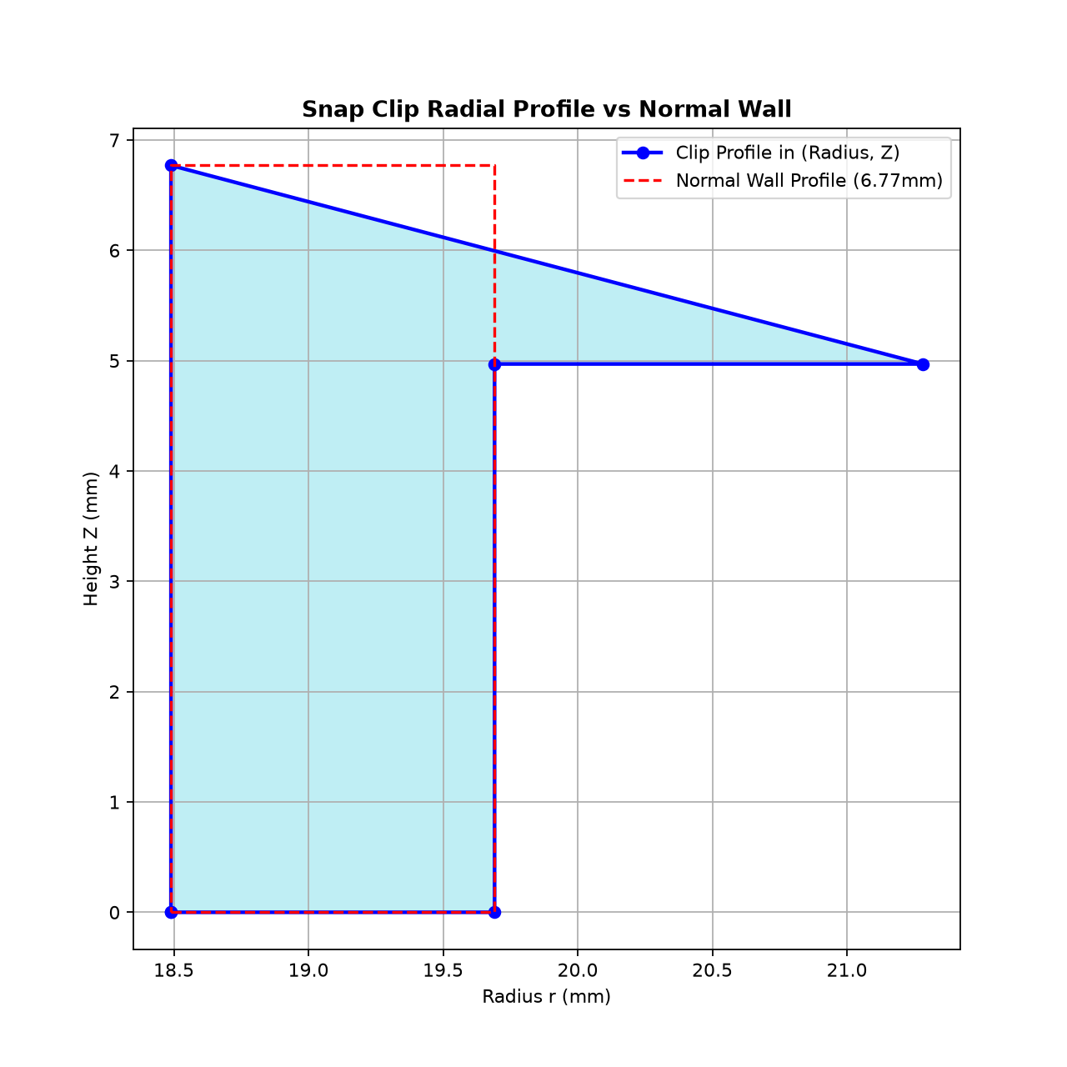
testing/clip_profile_rz.png
