elliotmartin92/kia-socket/testing/clip_reposition_test.png

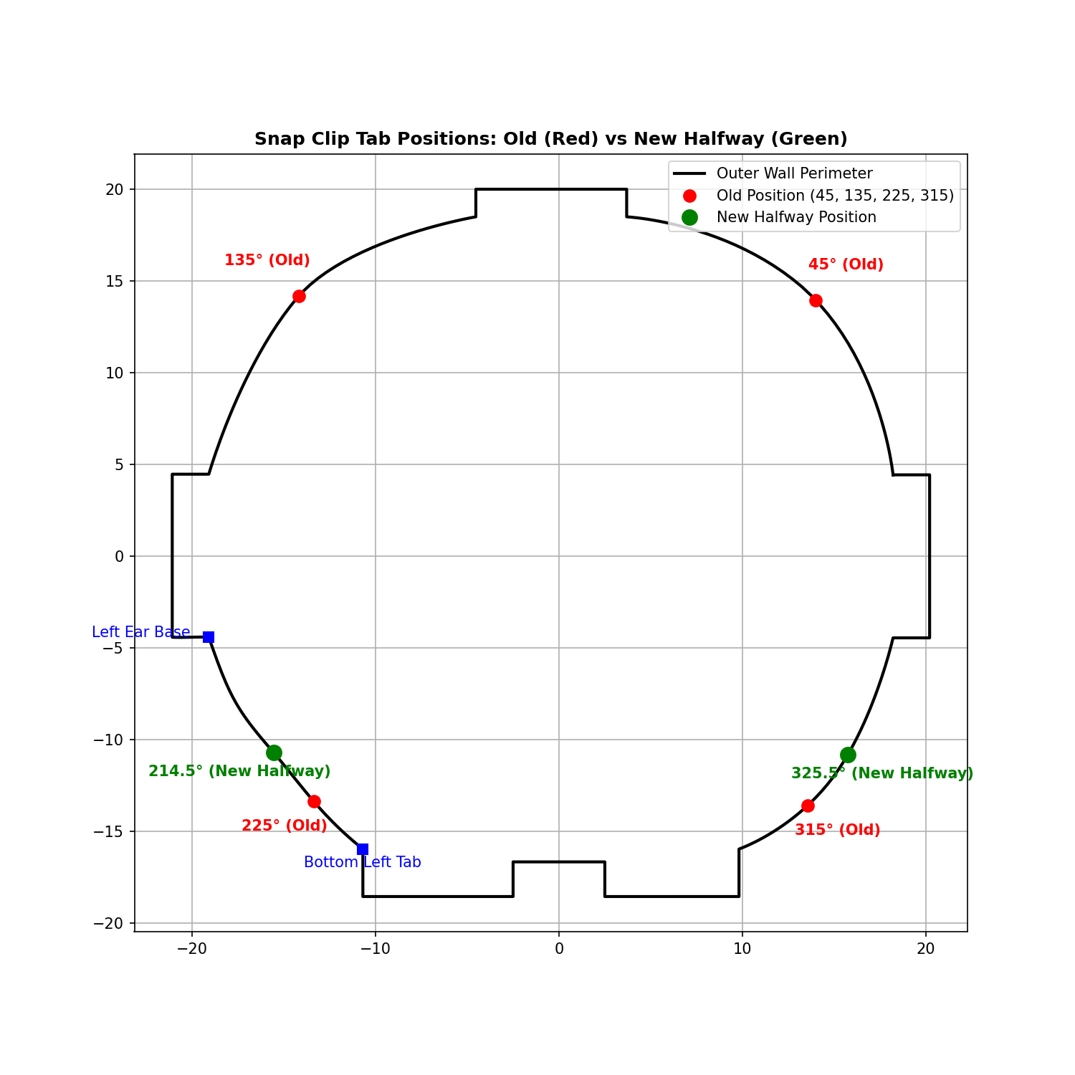
testing/clip_reposition_test.png
