elliotmartin92/kia-socket/testing/clip_support_before_after_3d.png

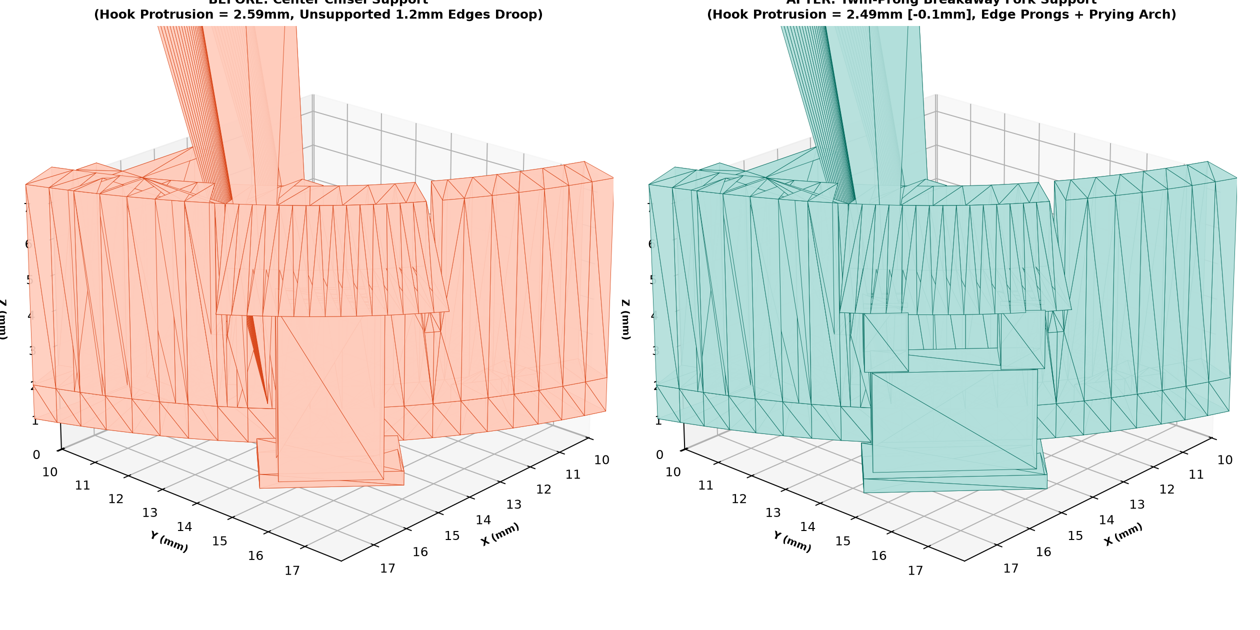
testing/clip_support_before_after_3d.png
