elliotmartin92/kia-socket/testing/clip_support_tower_preview.png

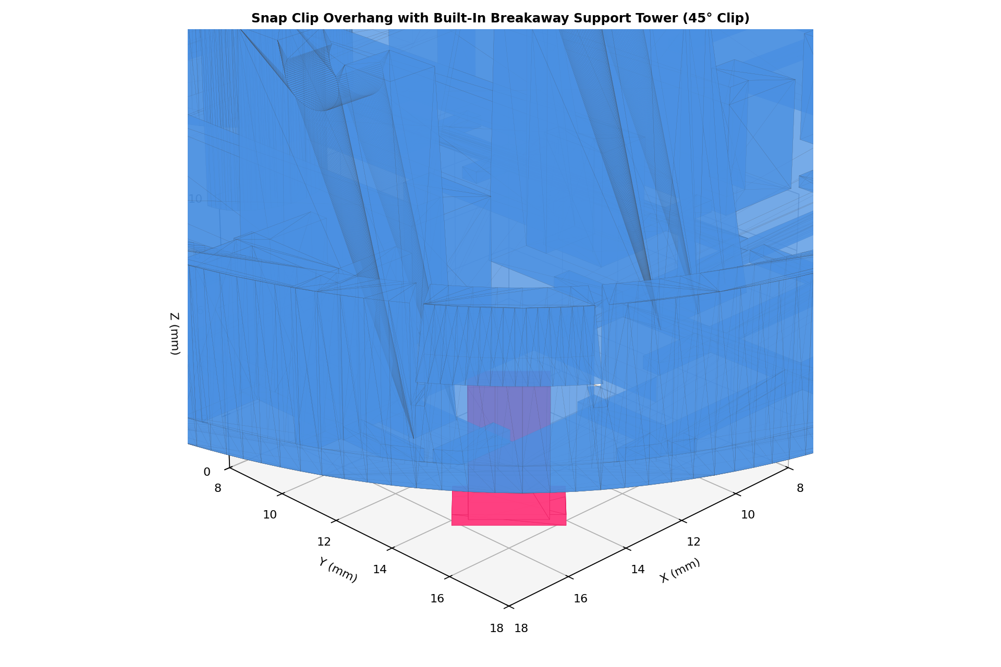
testing/clip_support_tower_preview.png
