elliotmartin92/kia-socket/testing/compare_seating_rib_positions.png

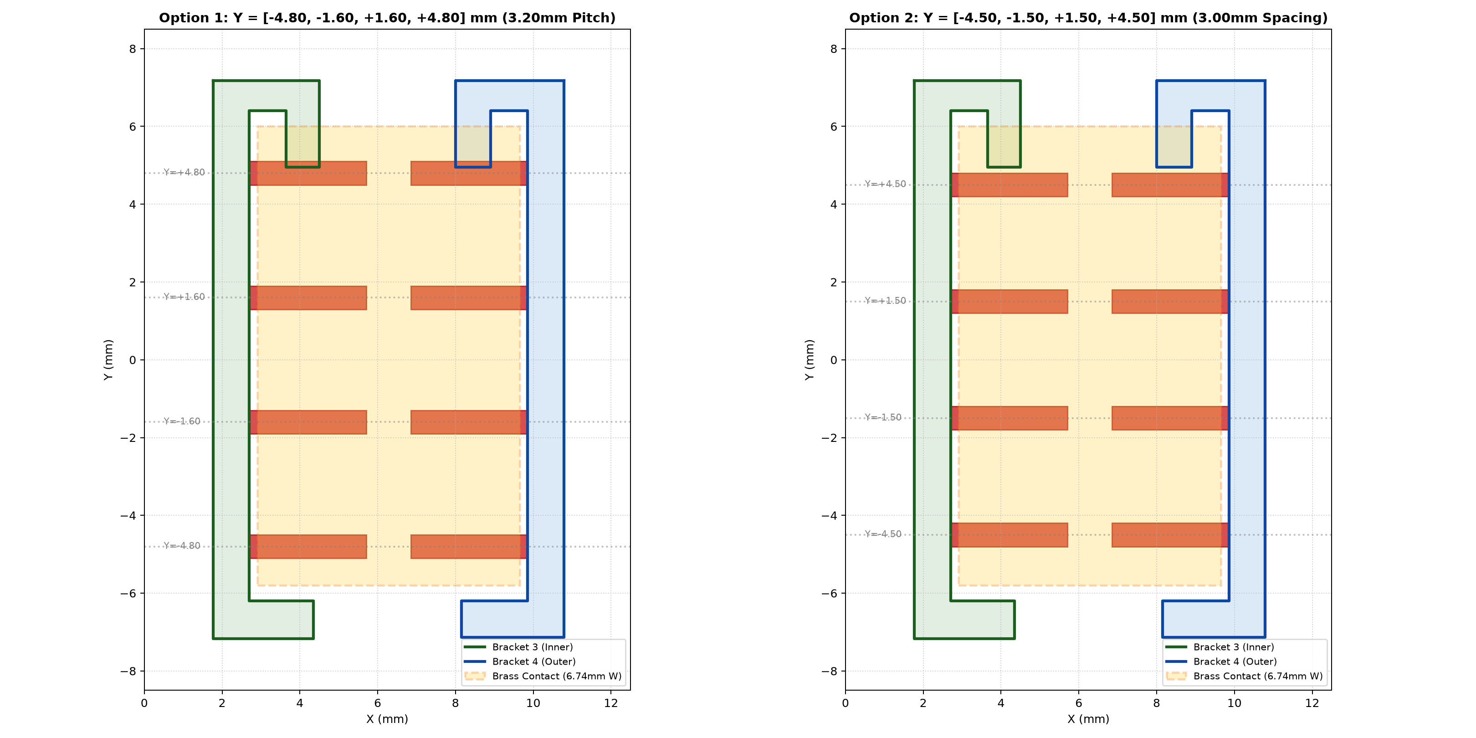
testing/compare_seating_rib_positions.png
