elliotmartin92/kia-socket/testing/complete_bracket_update_diagram.png

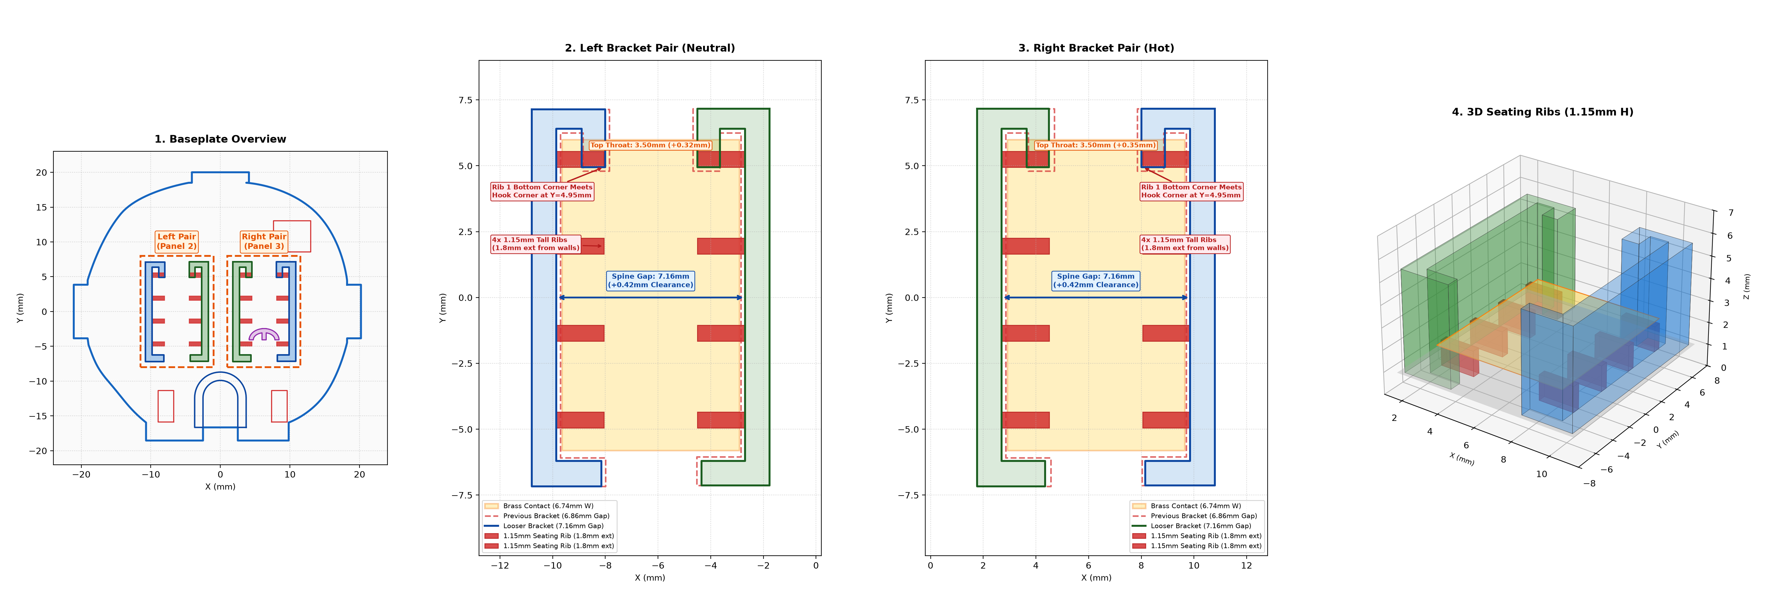
testing/complete_bracket_update_diagram.png
