elliotmartin92/kia-socket/testing/connected_ribs_clean.png

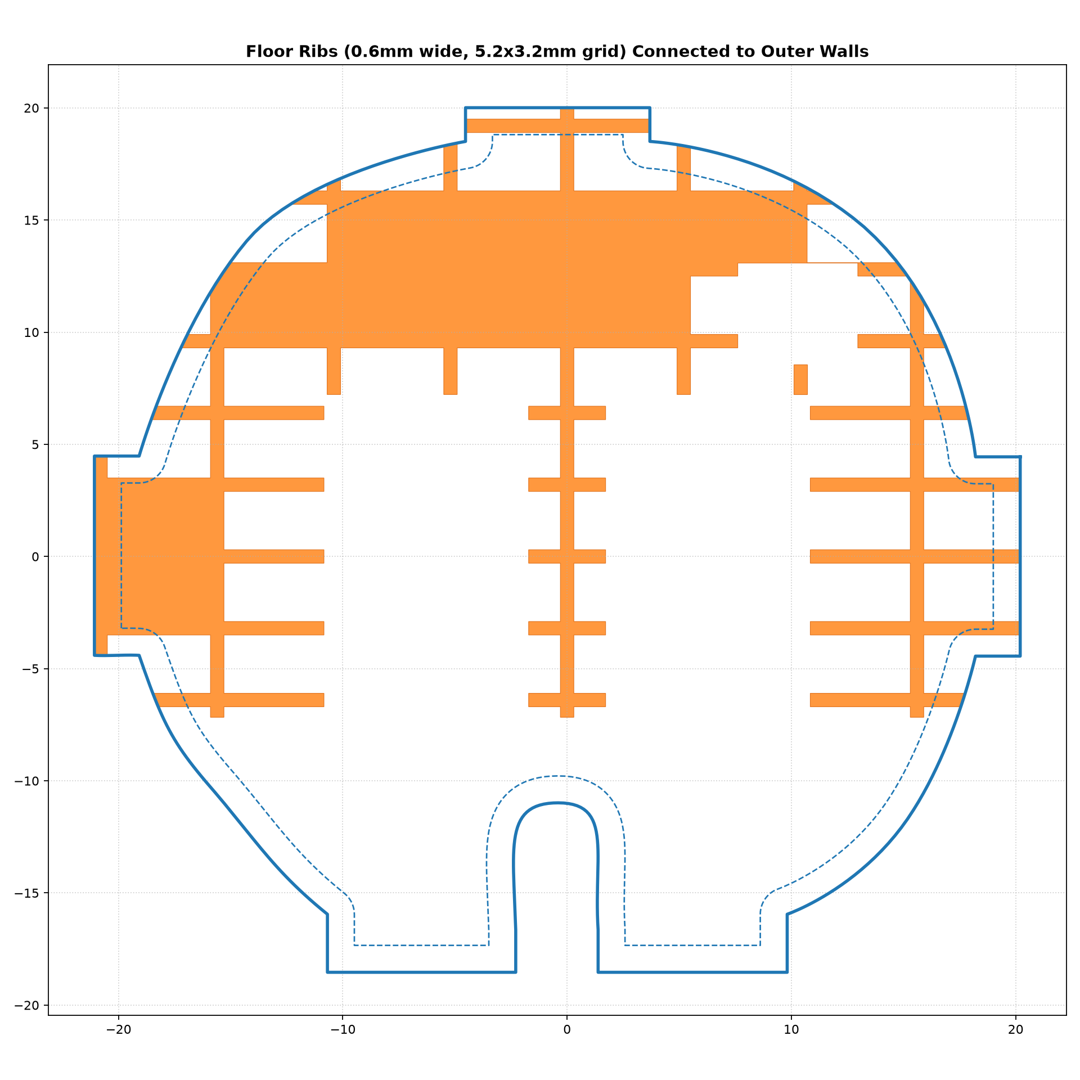
testing/connected_ribs_clean.png
