elliotmartin92/kia-socket/testing/connected_ribs_preview.png

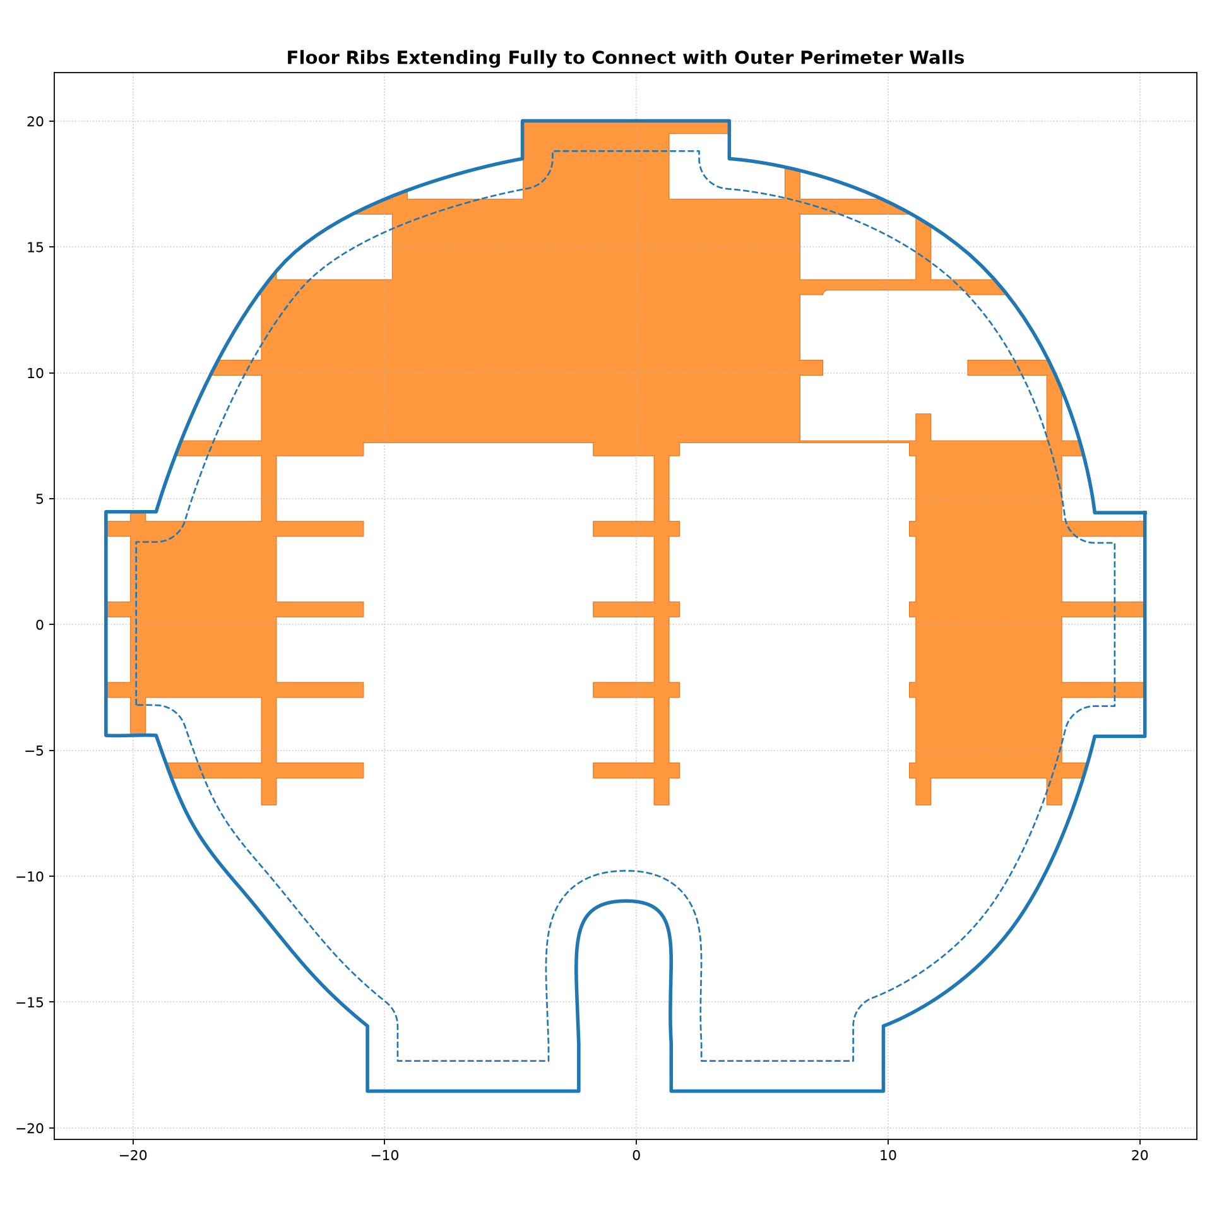
testing/connected_ribs_preview.png
