elliotmartin92/kia-socket/testing/cradle_retention_comparison.png

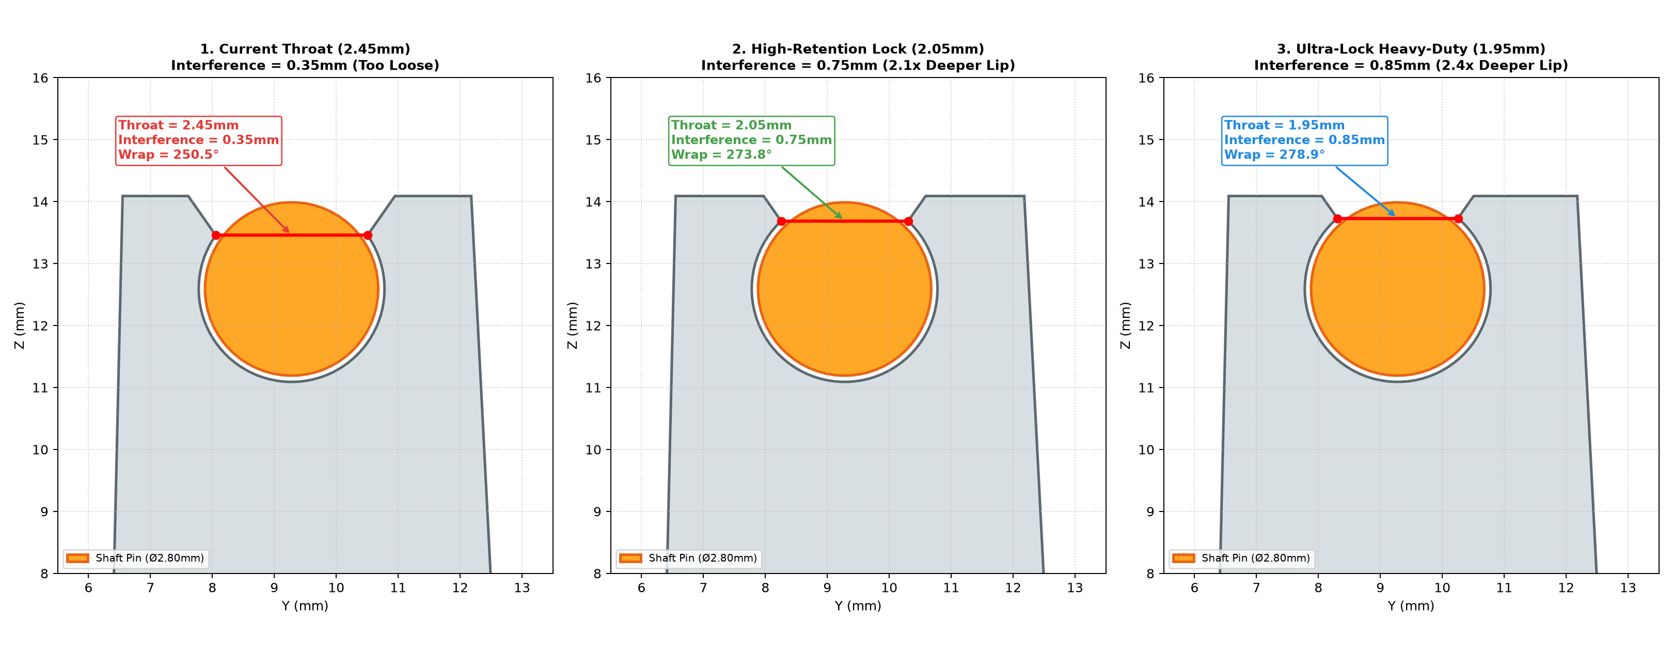
testing/cradle_retention_comparison.png
