elliotmartin92/kia-socket/testing/crowned_cam_dynamic_verification.png

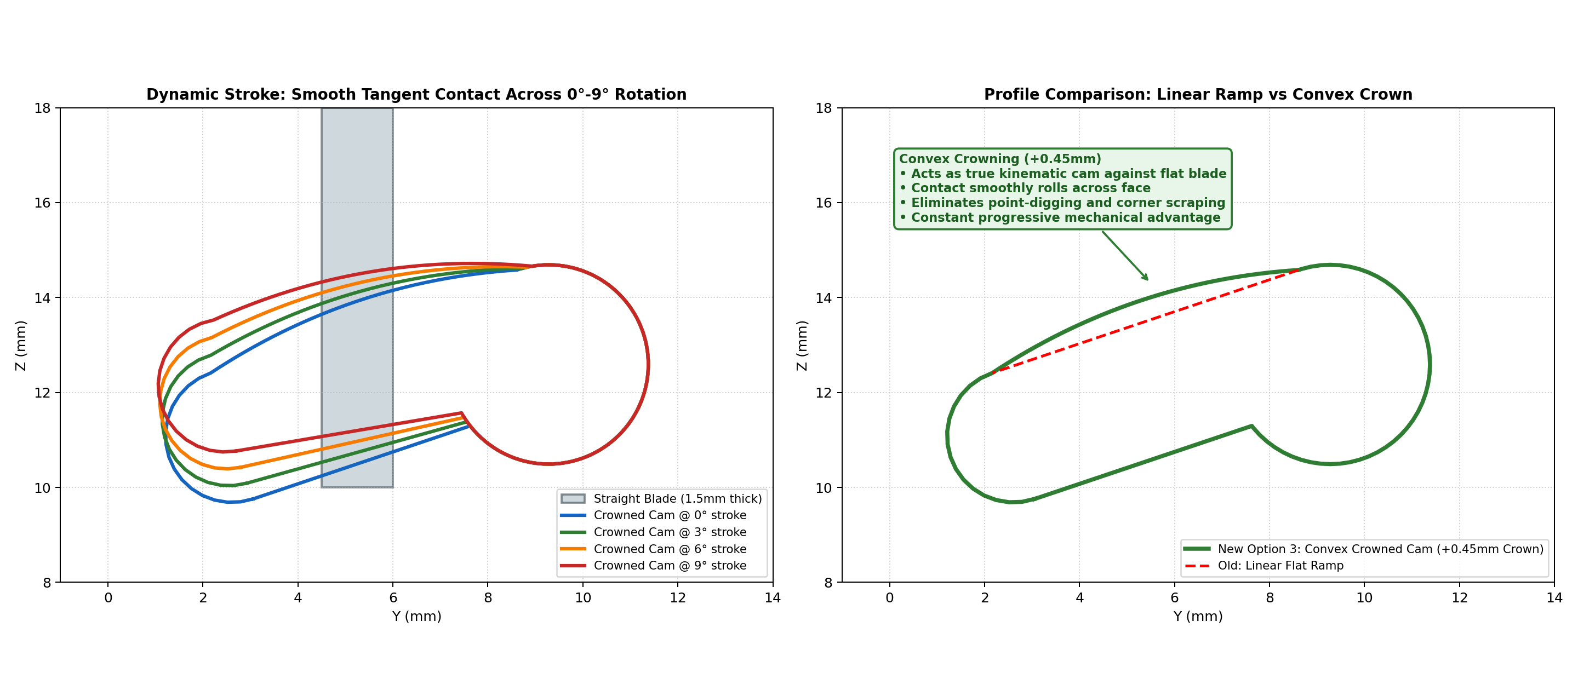
testing/crowned_cam_dynamic_verification.png
