elliotmartin92/kia-socket/testing/curved_clip_test.png

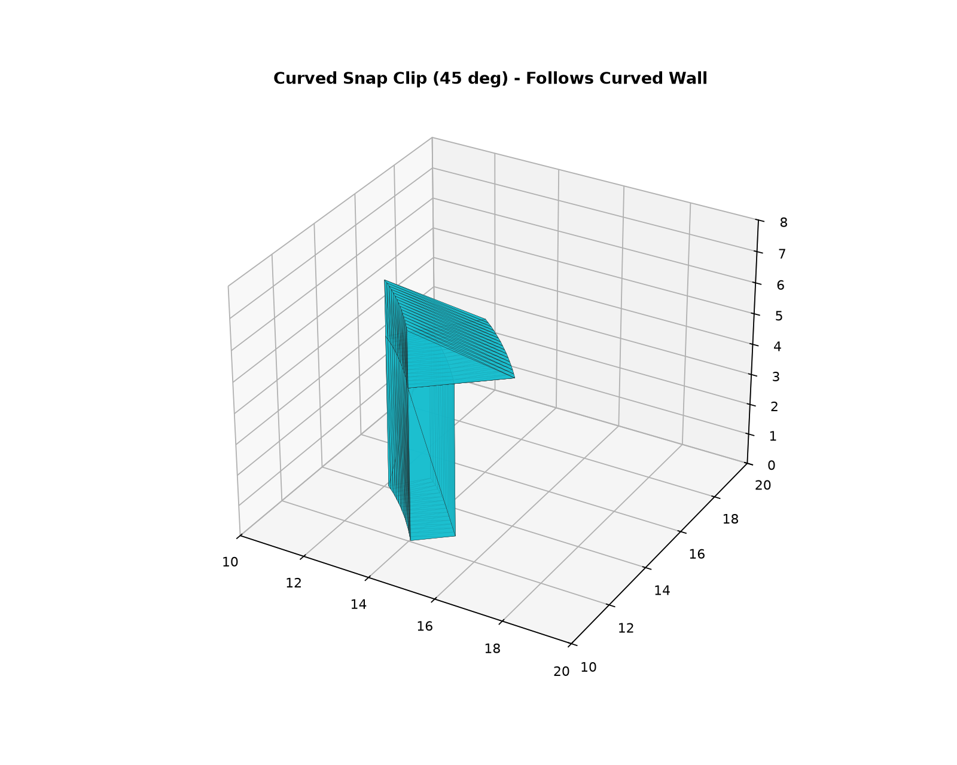
testing/curved_clip_test.png
