elliotmartin92/kia-socket/testing/curved_feature_2mm_offset.png

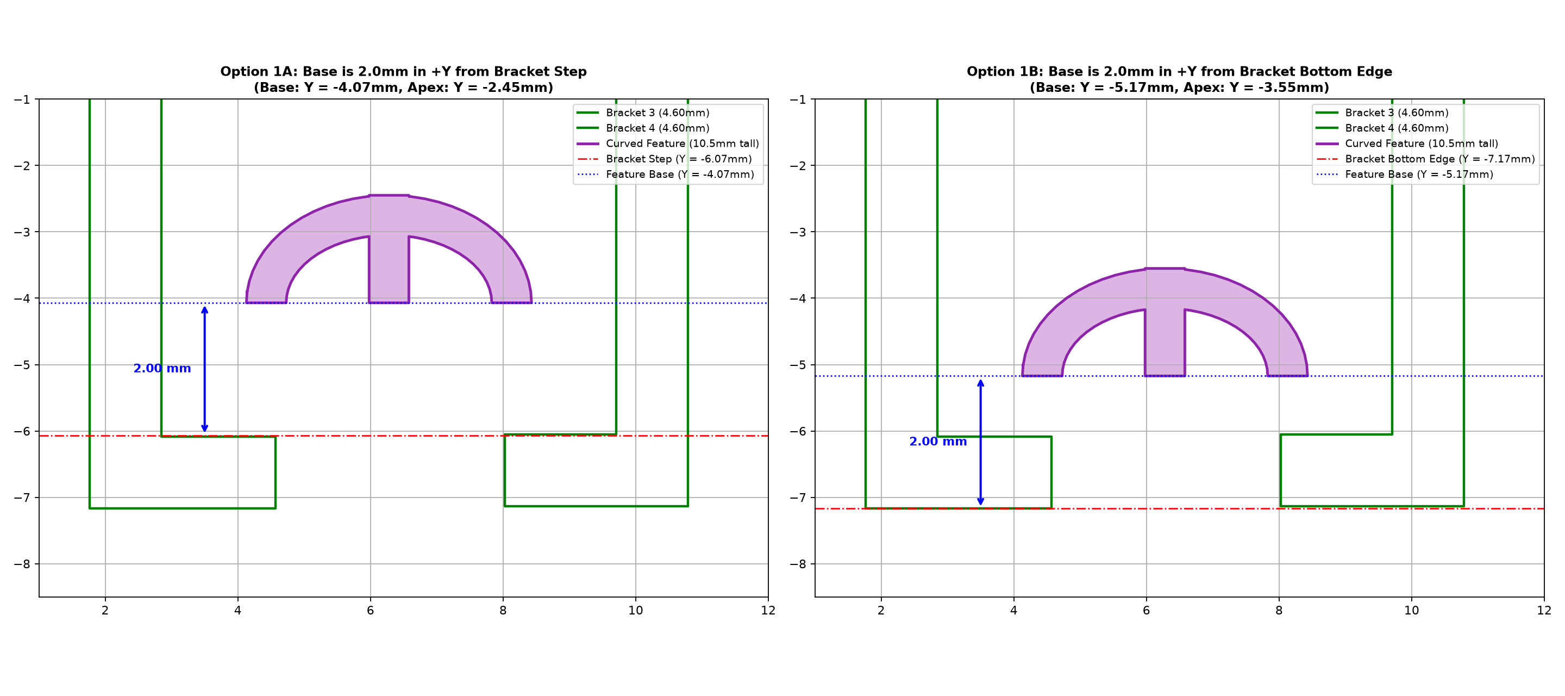
testing/curved_feature_2mm_offset.png
