elliotmartin92/kia-socket/testing/curved_feature_blade_clearance.png

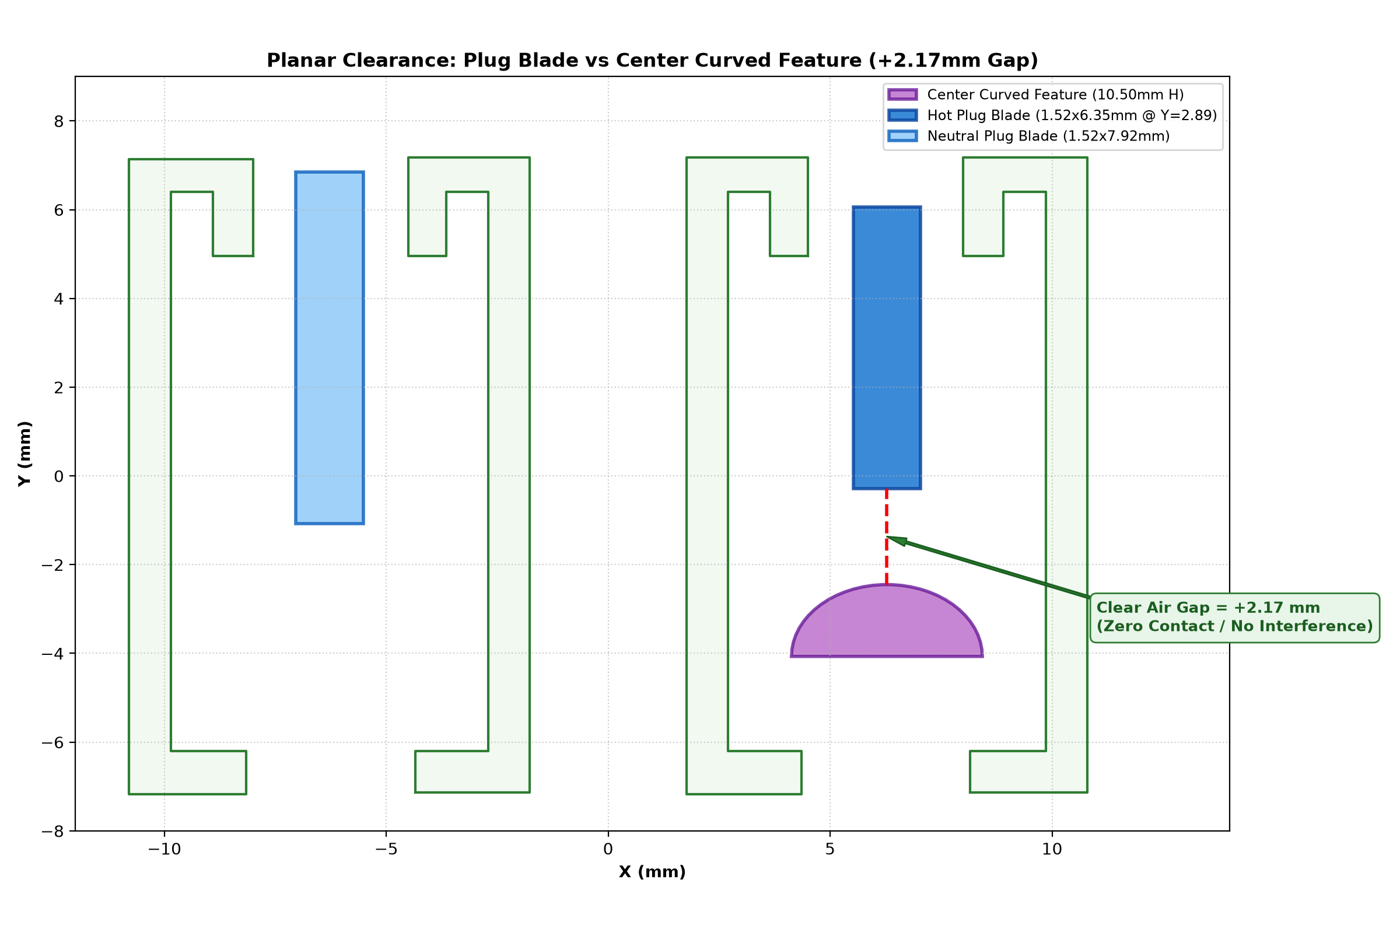
testing/curved_feature_blade_clearance.png
