elliotmartin92/kia-socket/testing/curved_feature_candidates.png

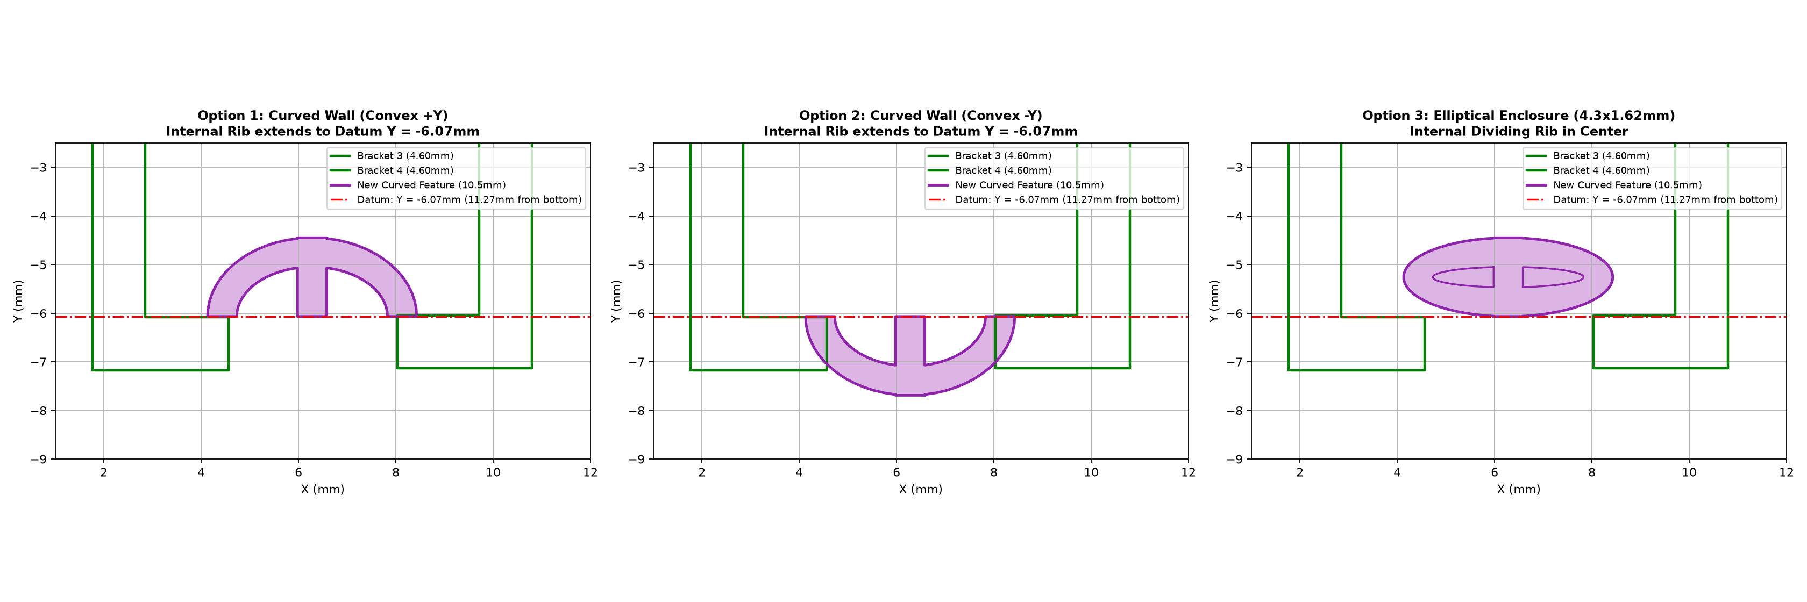
testing/curved_feature_candidates.png
