elliotmartin92/kia-socket/testing/curved_feature_reinforcement_options.png

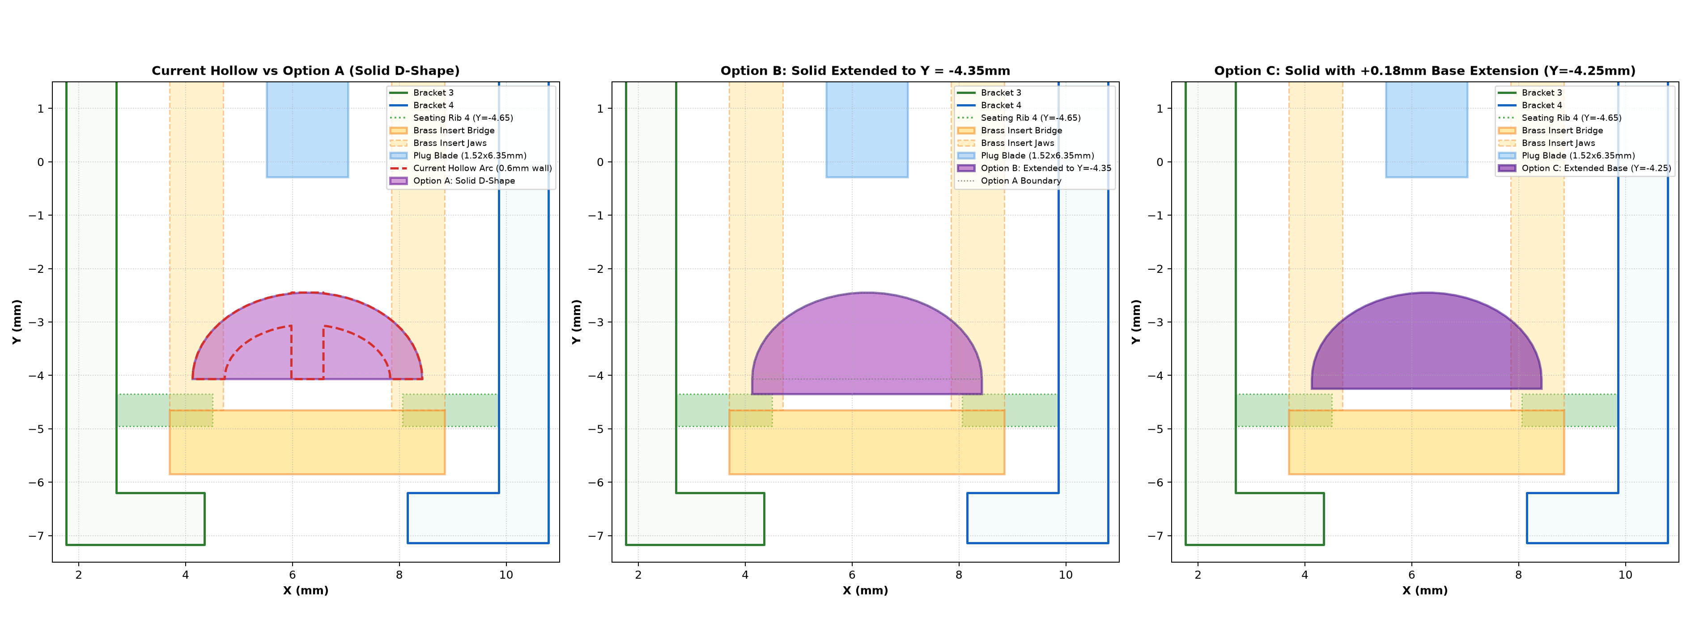
testing/curved_feature_reinforcement_options.png
