elliotmartin92/kia-socket/testing/deep_inspect_right_slit.png

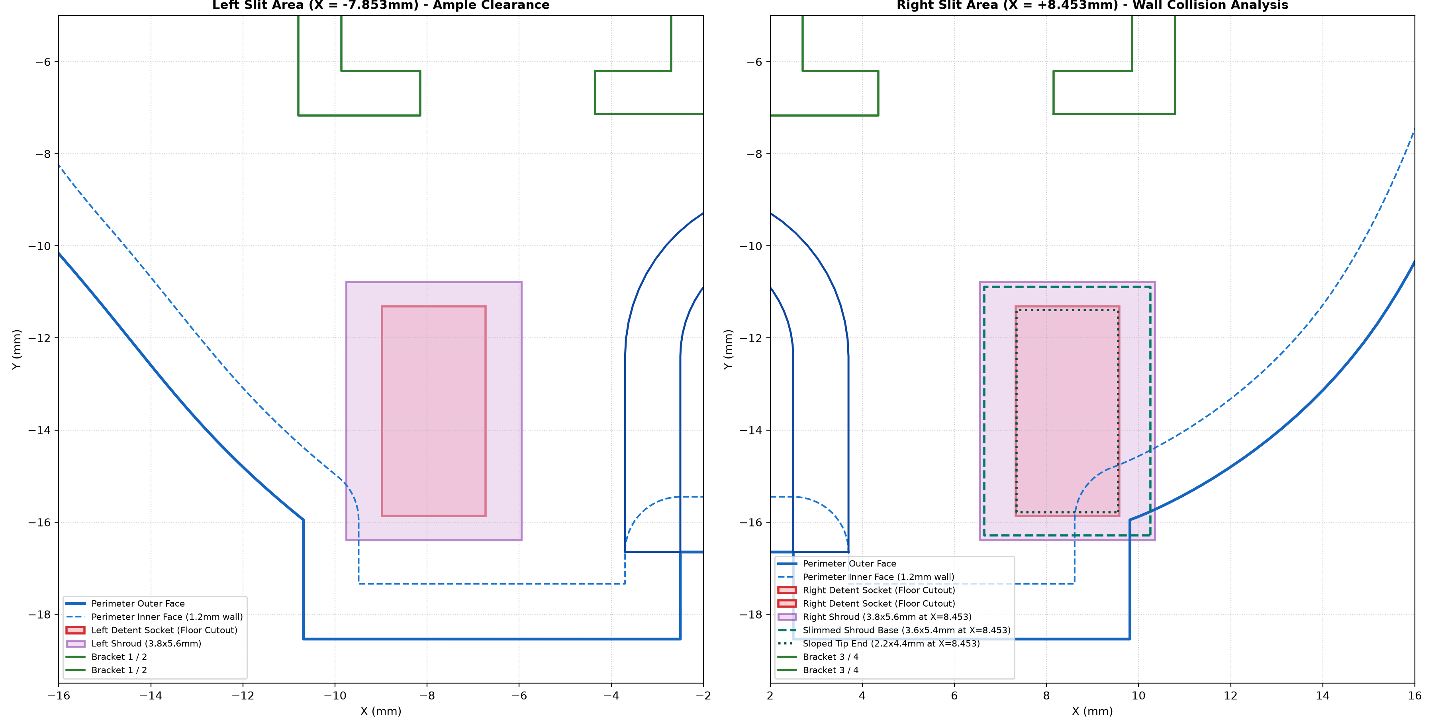
testing/deep_inspect_right_slit.png
