elliotmartin92/kia-socket/testing/detent_socket_fit_verified.png

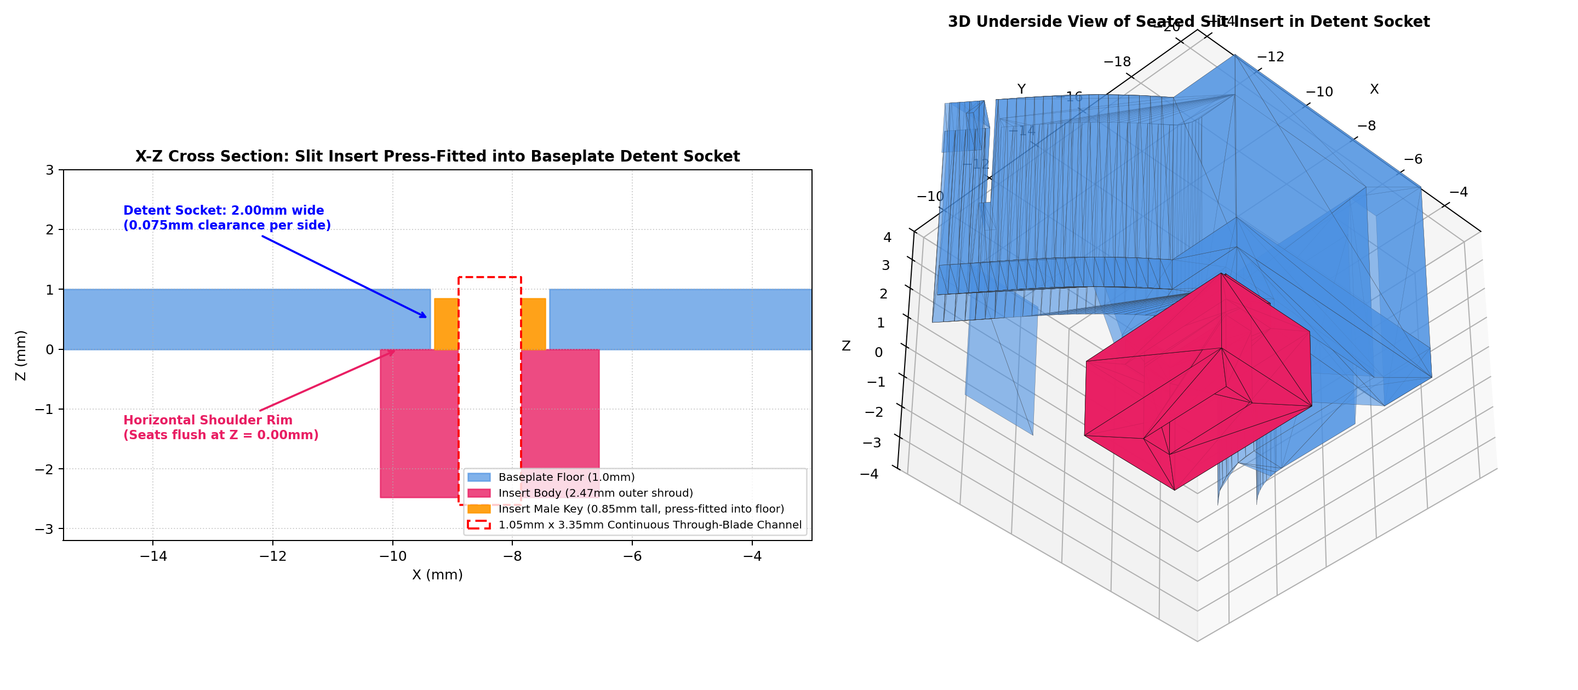
testing/detent_socket_fit_verified.png
