elliotmartin92/kia-socket/testing/direct_105_cam_mesh_inspect.png

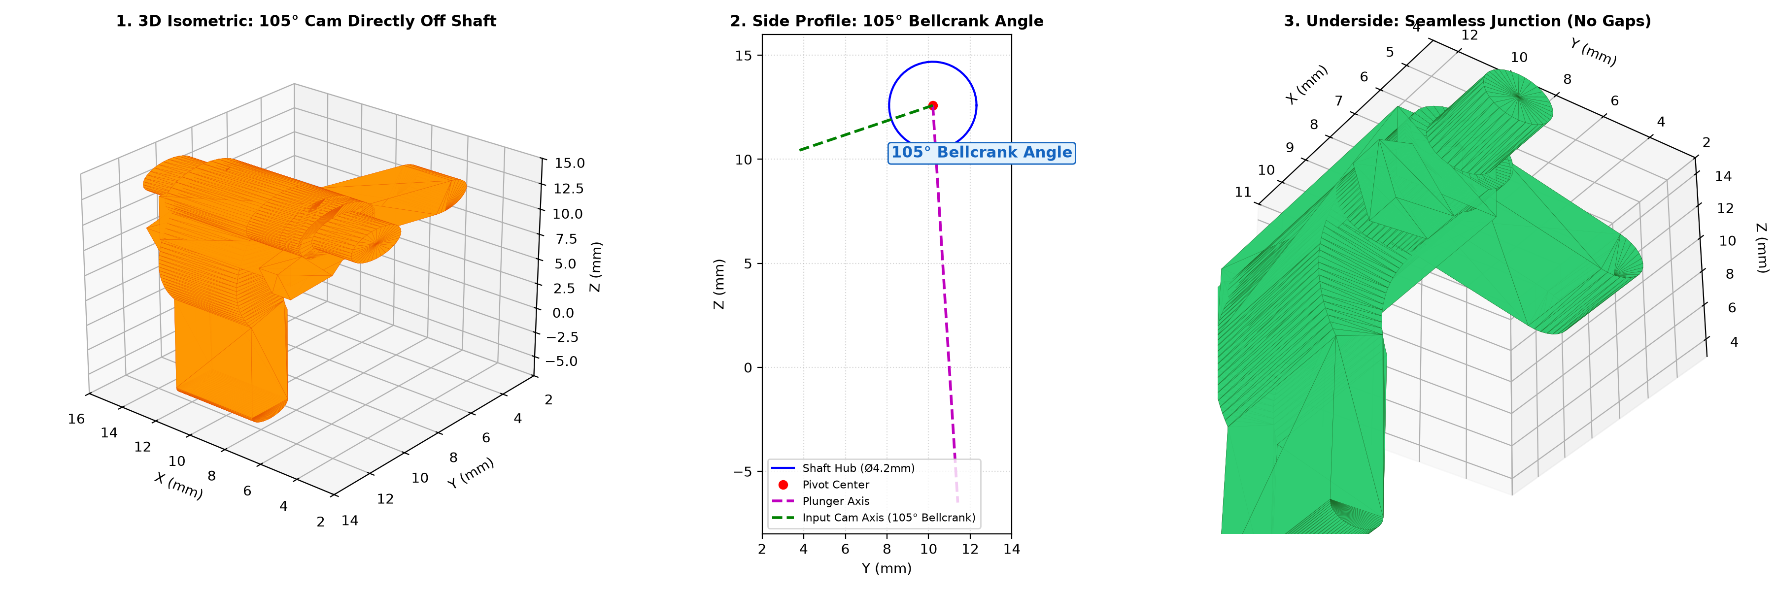
testing/direct_105_cam_mesh_inspect.png
