elliotmartin92/kia-socket/testing/direct_105deg_cam_preview.png

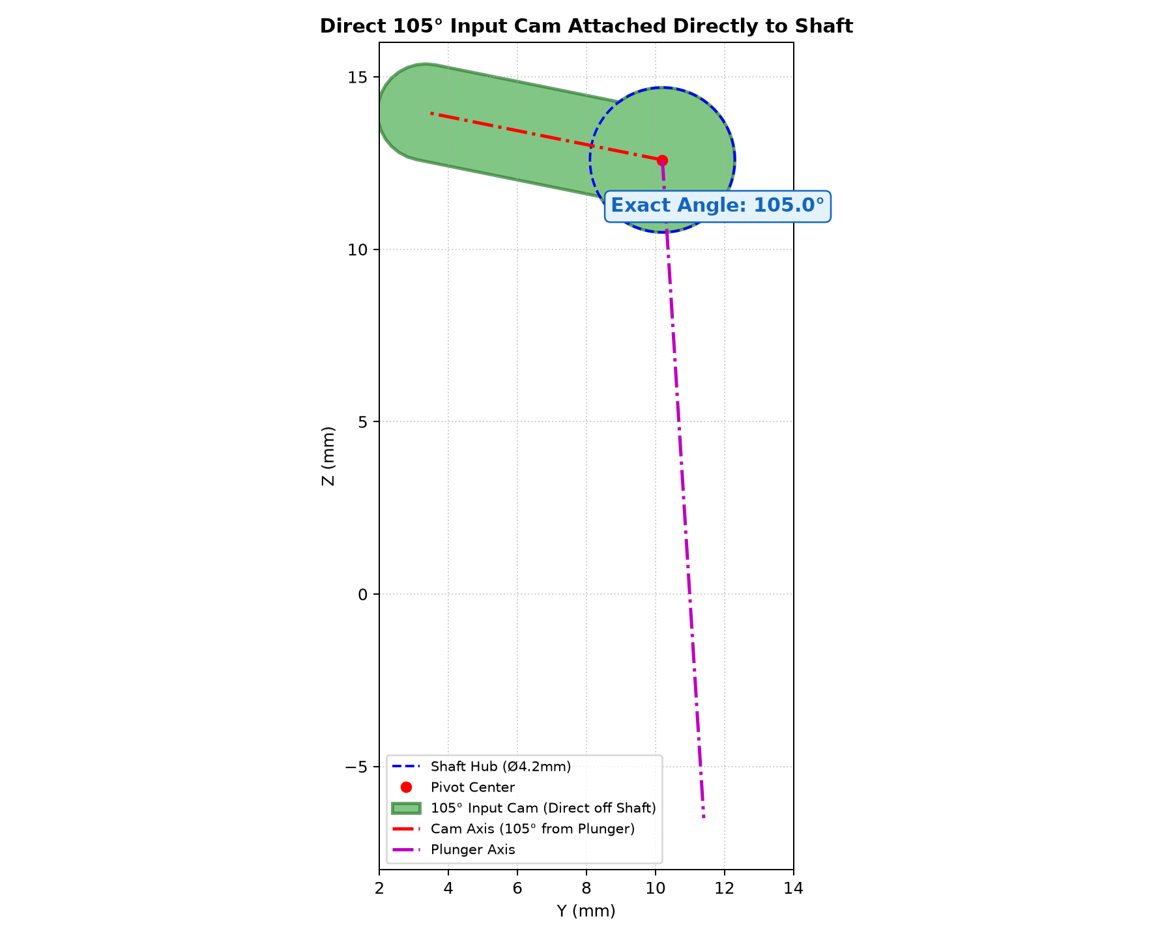
testing/direct_105deg_cam_preview.png
