elliotmartin92/kia-socket/testing/direct_straight_cam_comparison.png

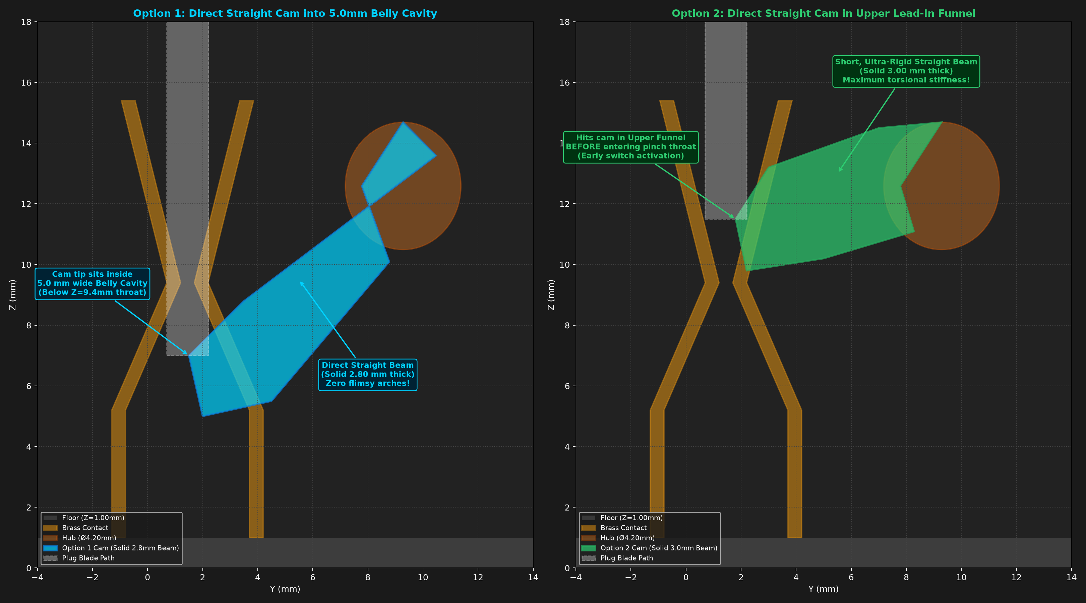
testing/direct_straight_cam_comparison.png
