elliotmartin92/kia-socket/testing/ear_comparison_830_vs_820.png

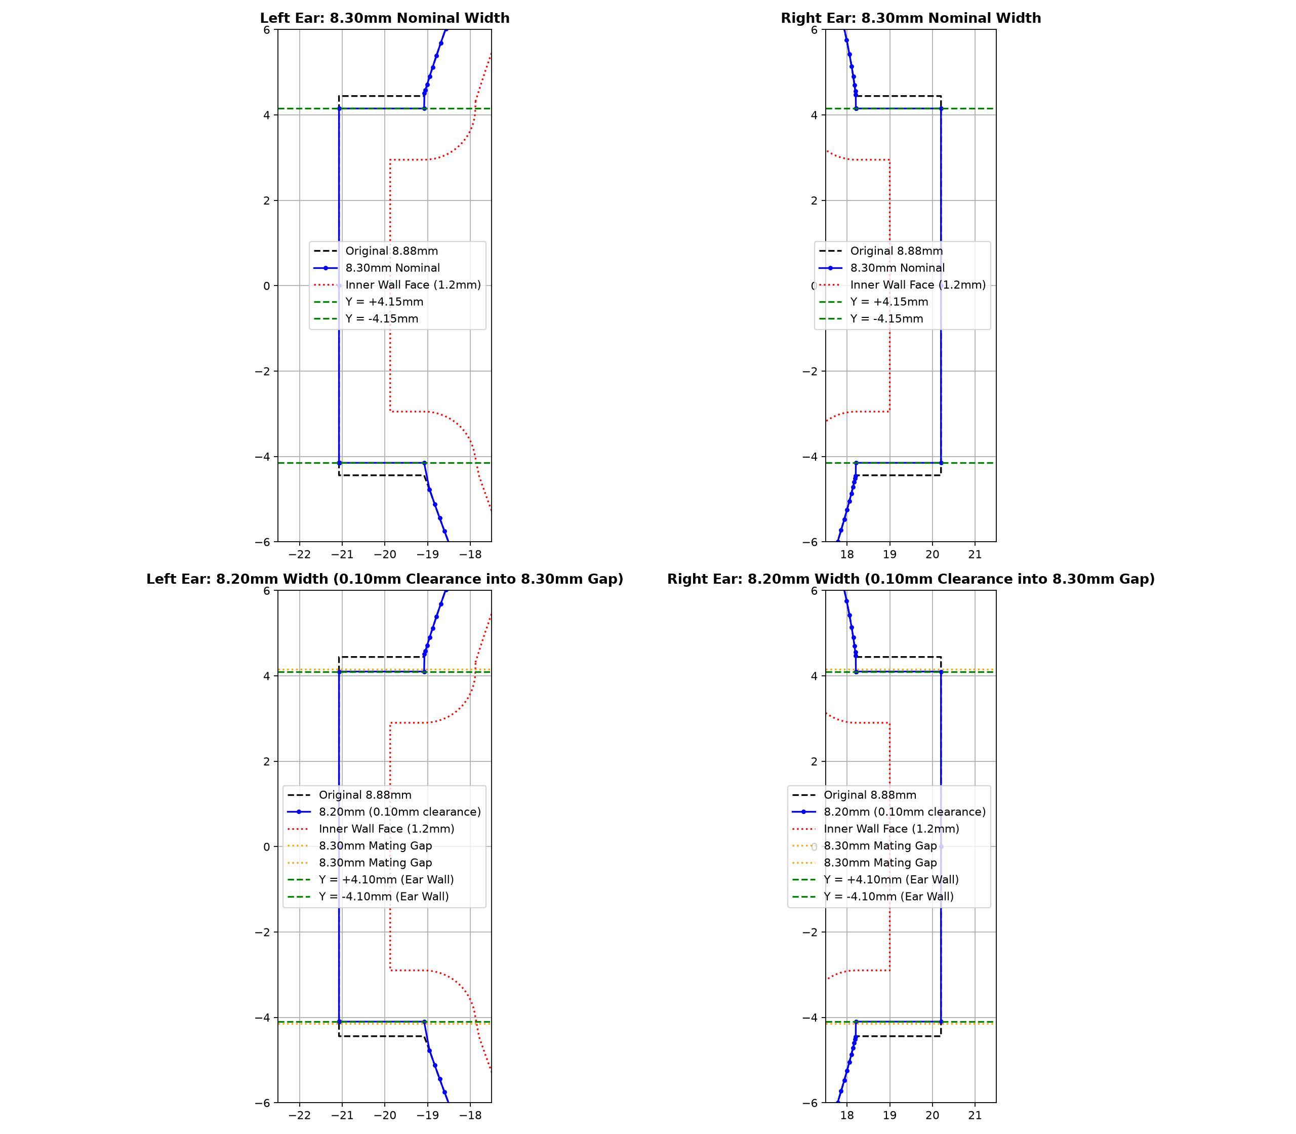
testing/ear_comparison_830_vs_820.png
