elliotmartin92/kia-socket/testing/ear_regions_inspection.png

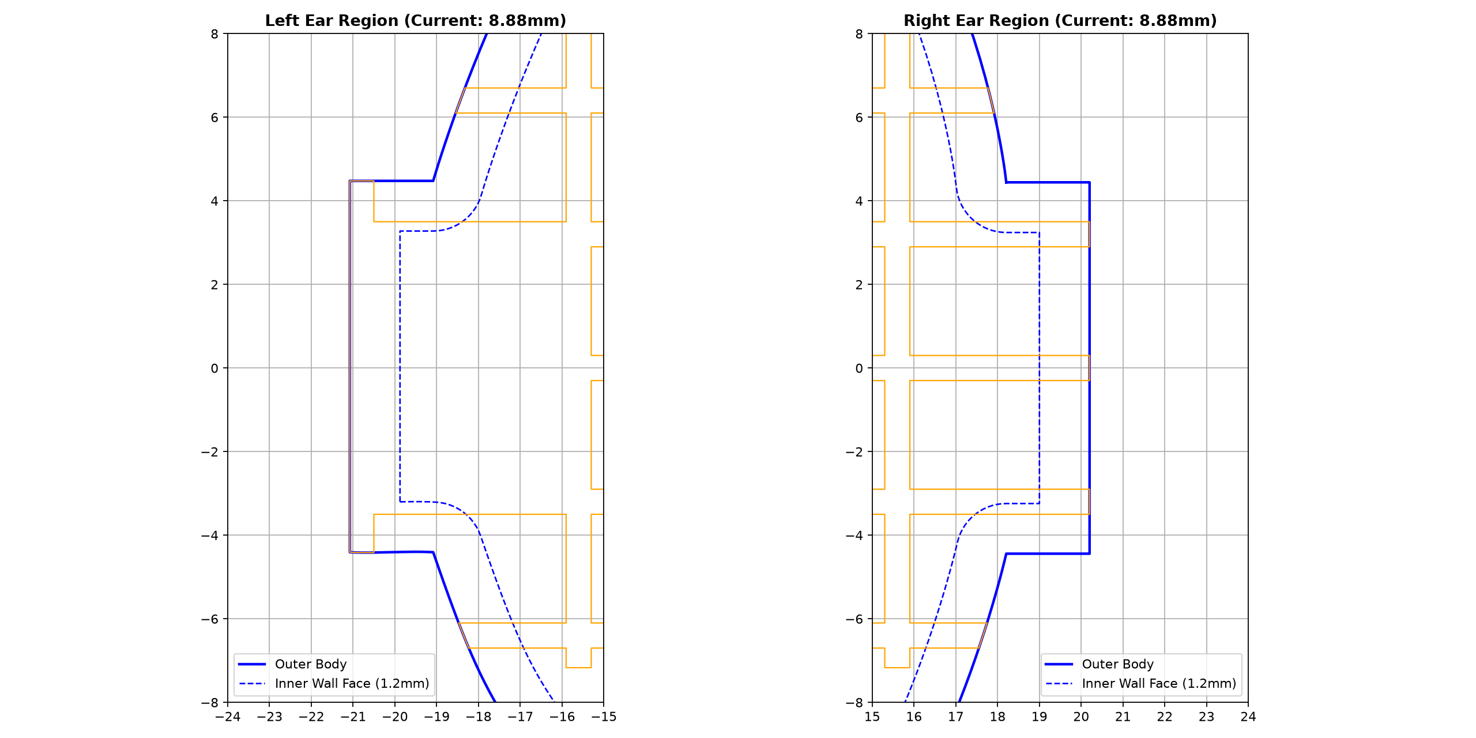
testing/ear_regions_inspection.png
