elliotmartin92/kia-socket/testing/enlarged_shaft_and_tower_inspection.png

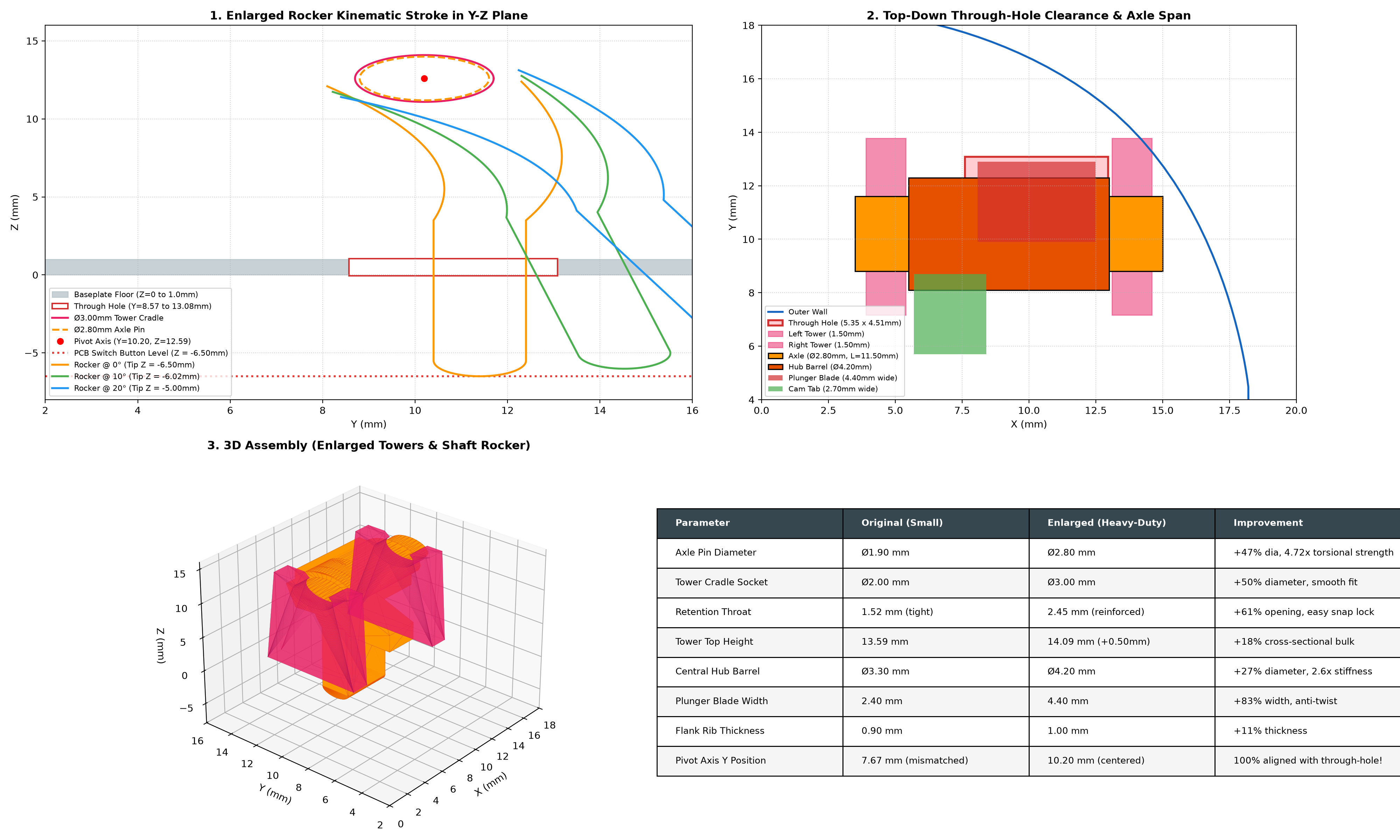
testing/enlarged_shaft_and_tower_inspection.png
