elliotmartin92/kia-socket/testing/enlarged_slit_fit_verified.png

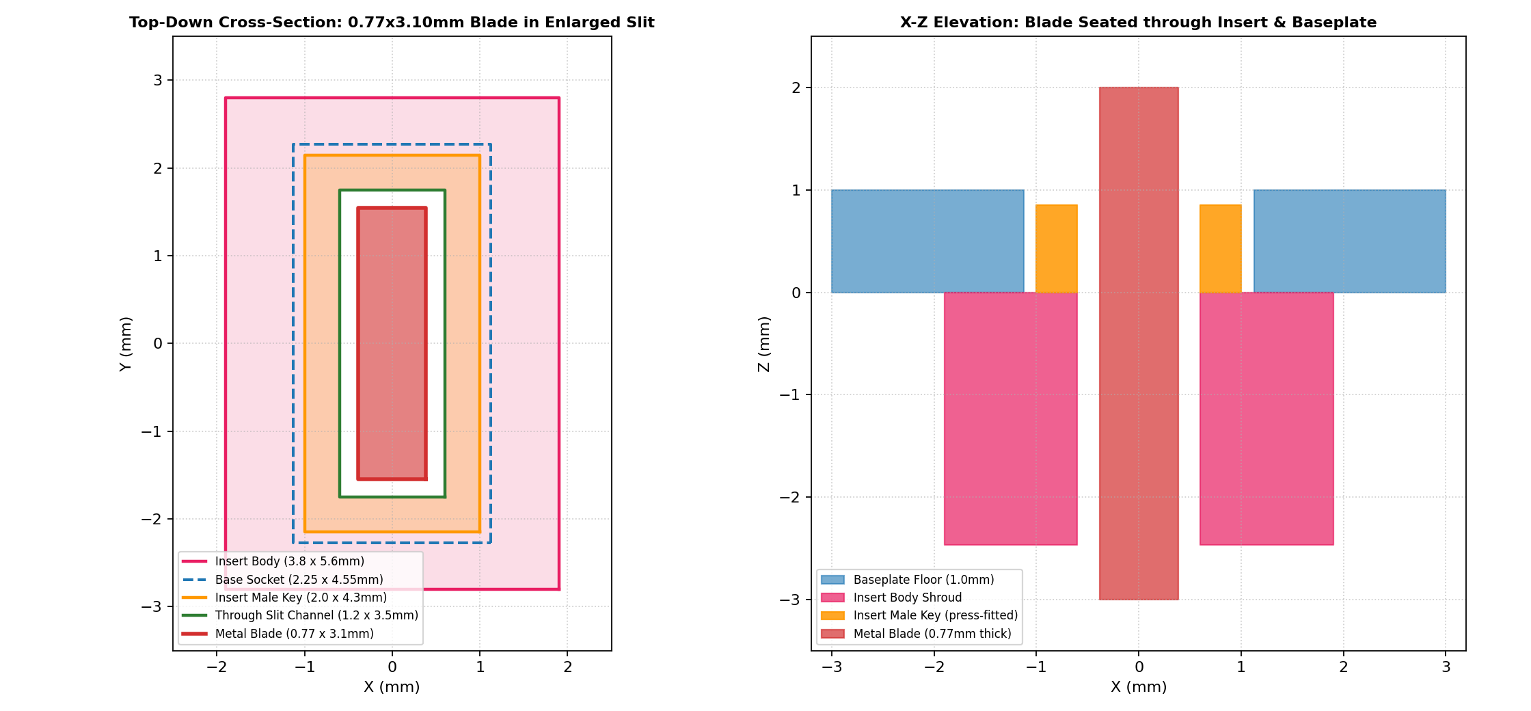
testing/enlarged_slit_fit_verified.png
