elliotmartin92/kia-socket/testing/exact_brass_and_cam_profile.png

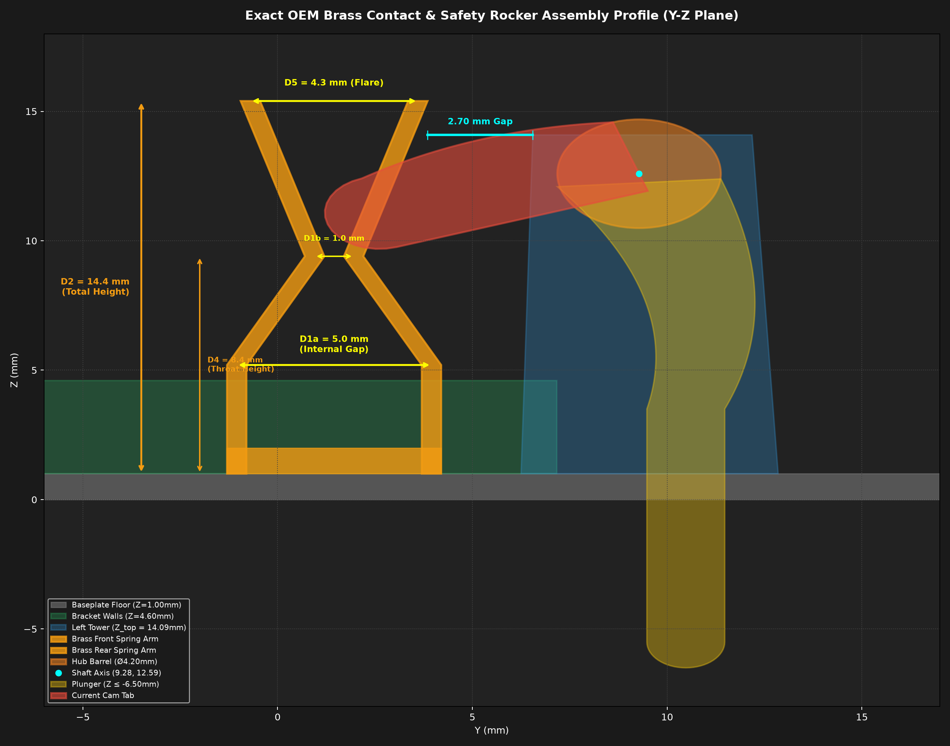
testing/exact_brass_and_cam_profile.png
