elliotmartin92/kia-socket/testing/exact_physical_simulation_review.png

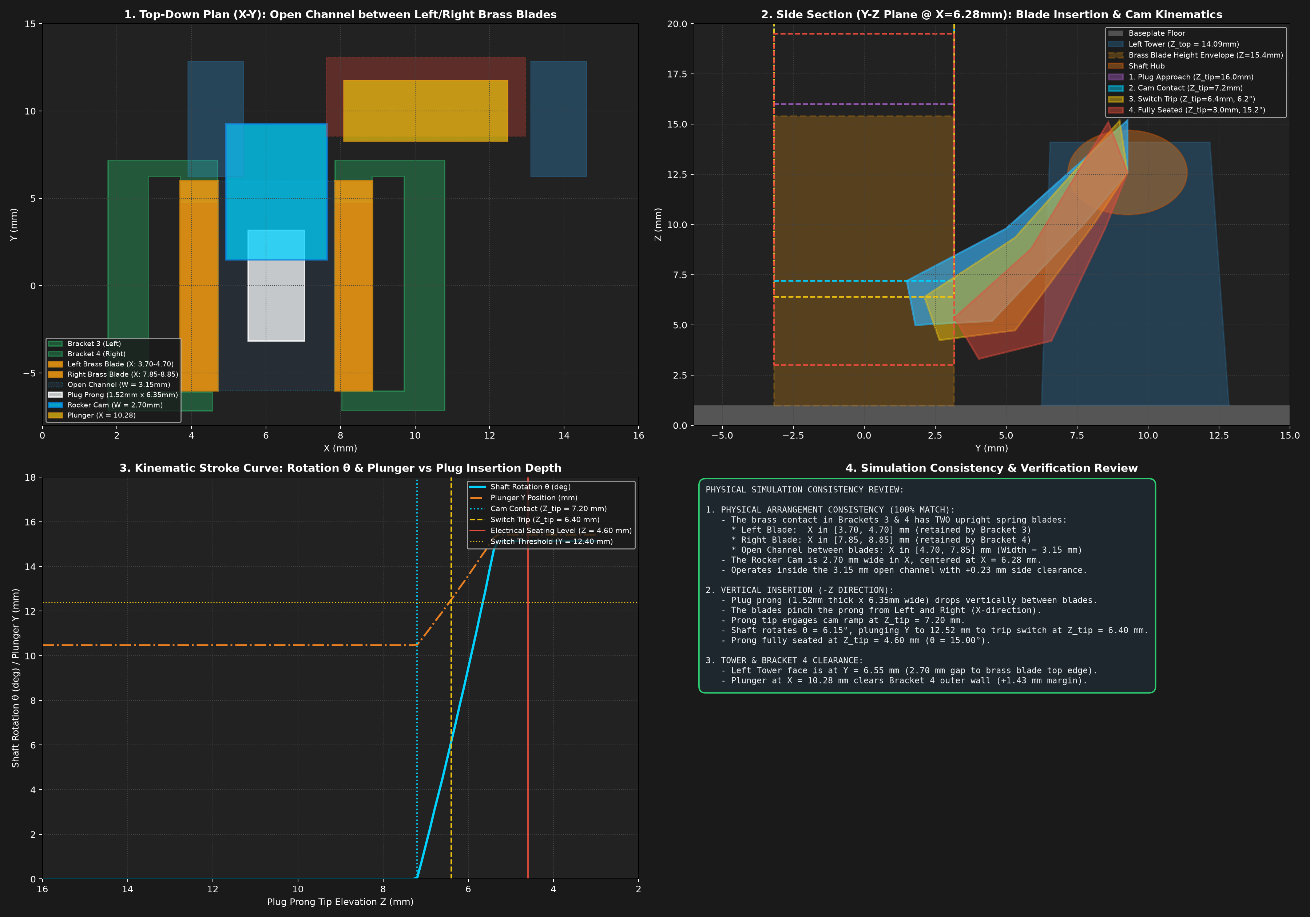
testing/exact_physical_simulation_review.png
