elliotmartin92/kia-socket/testing/fixed_original_position_slit.png

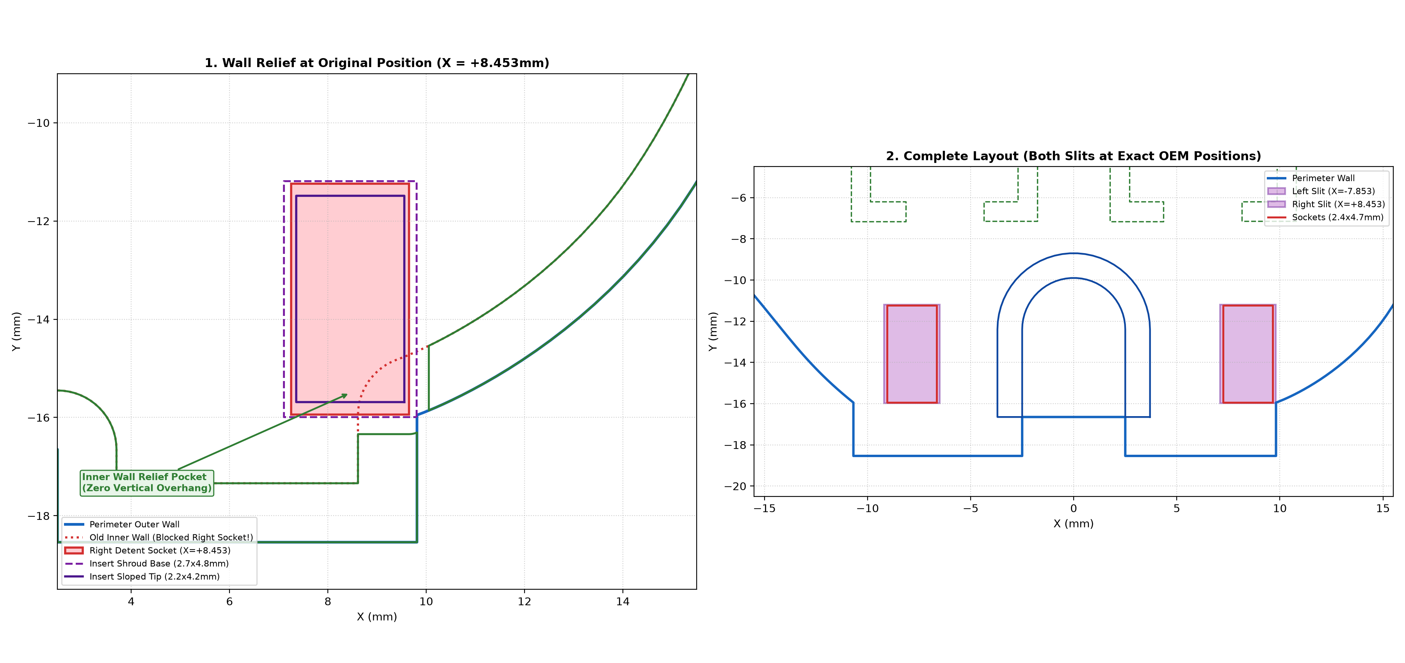
testing/fixed_original_position_slit.png
