elliotmartin92/kia-socket/testing/fixed_slit_insert_preview.png

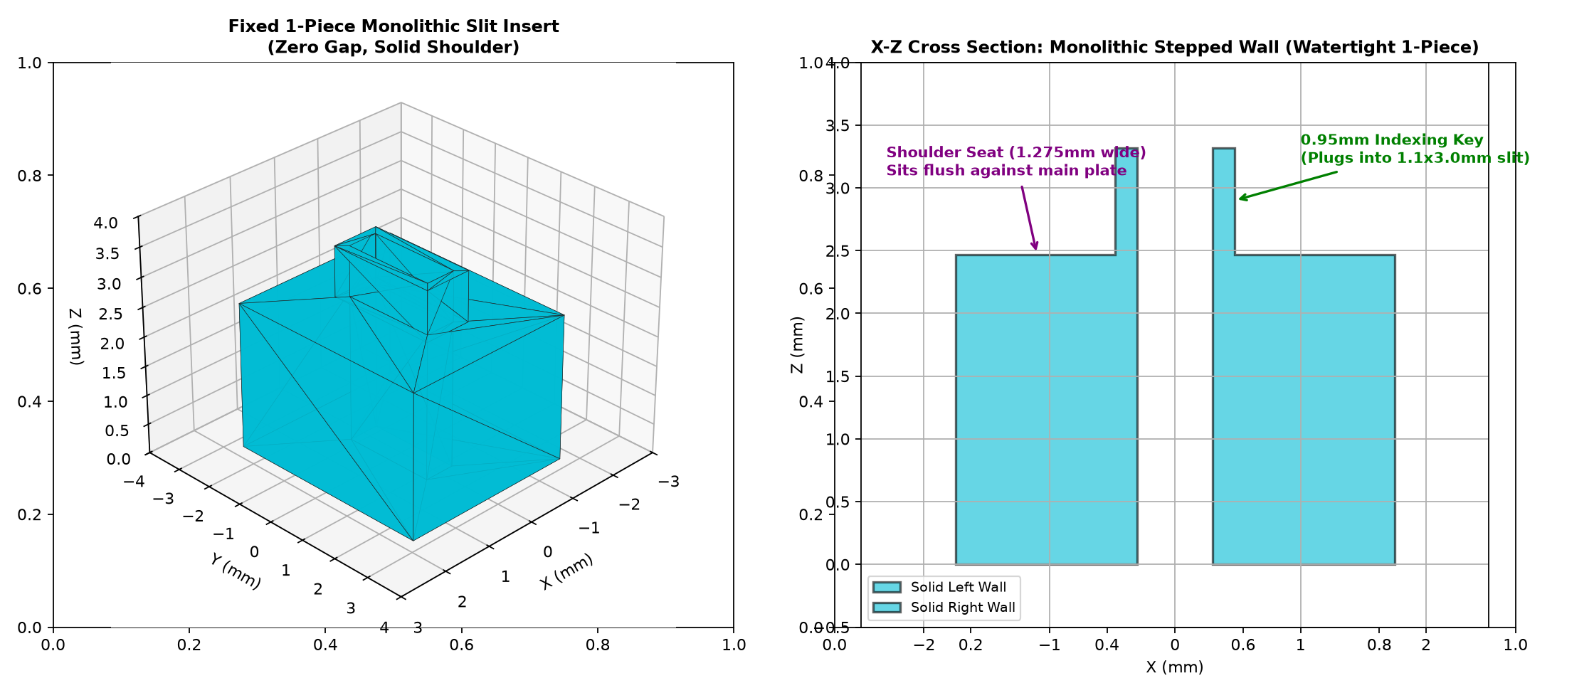
testing/fixed_slit_insert_preview.png
