elliotmartin92/kia-socket/testing/flush_cam_top_comparison.png

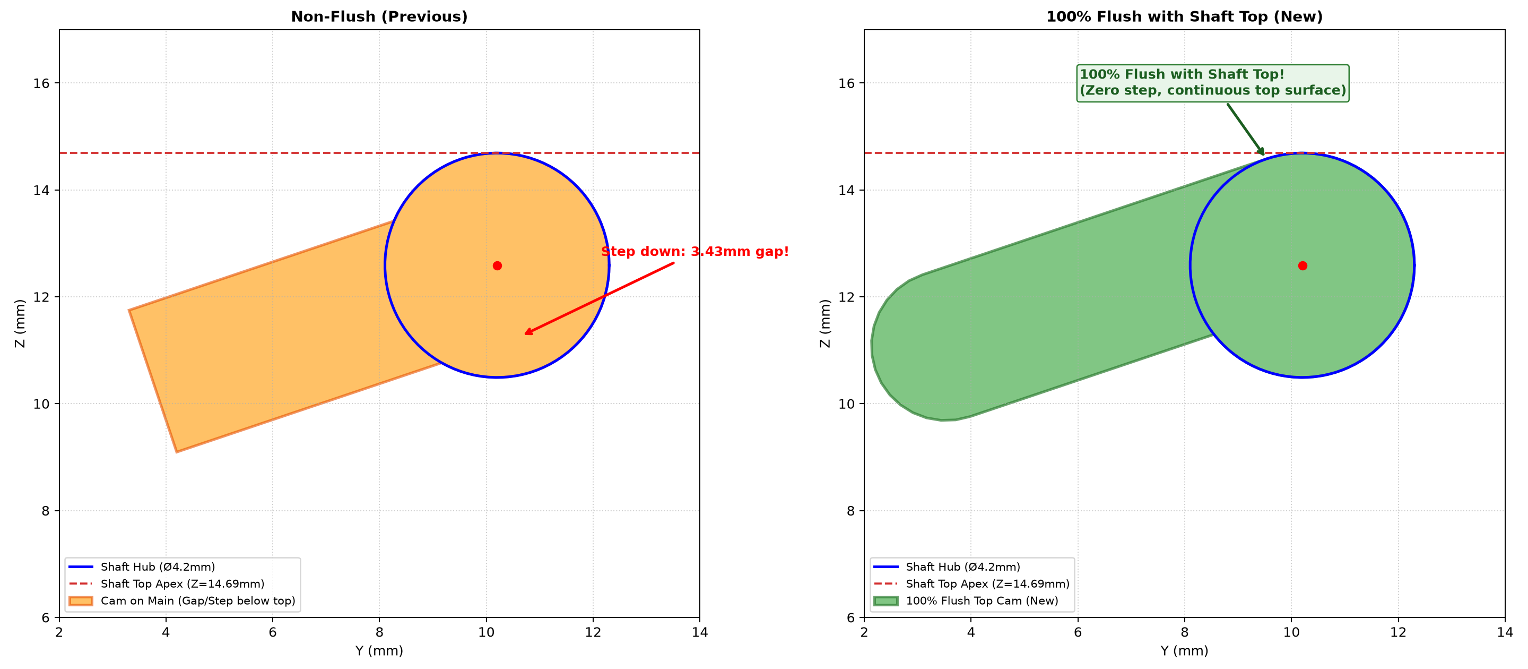
testing/flush_cam_top_comparison.png
