elliotmartin92/kia-socket/testing/flush_shaft_closeup.png

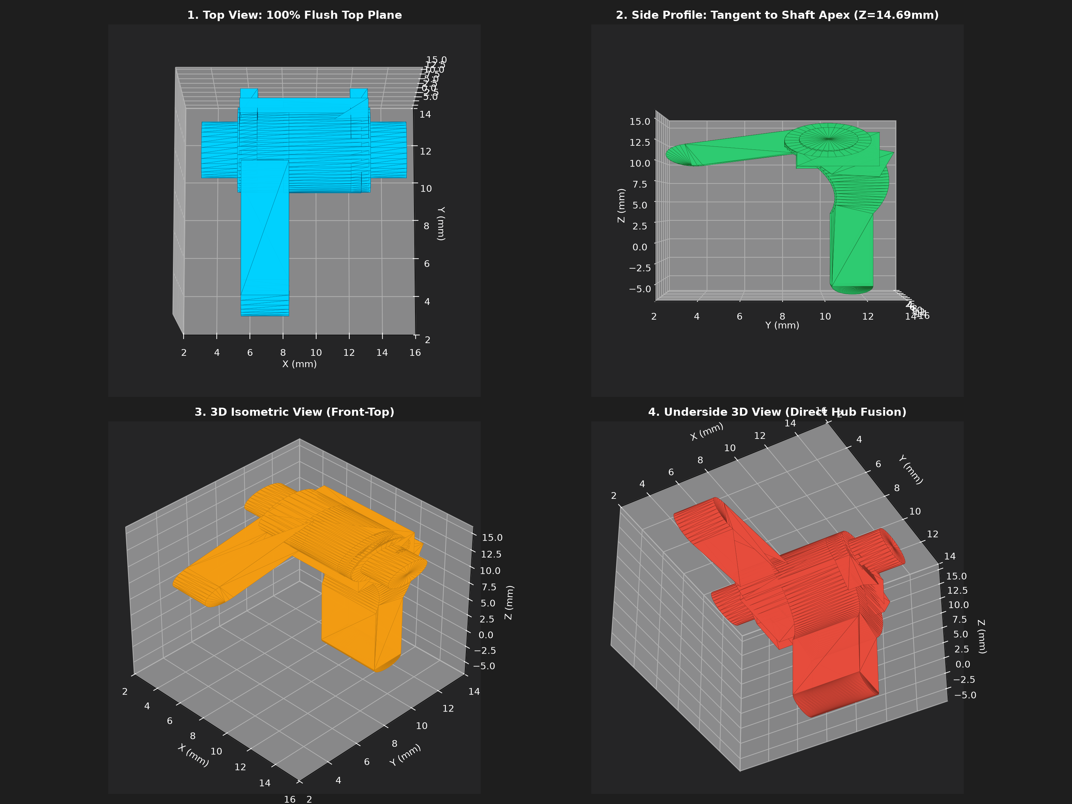
testing/flush_shaft_closeup.png
