elliotmartin92/kia-socket/testing/insert_gap_solutions_preview.png

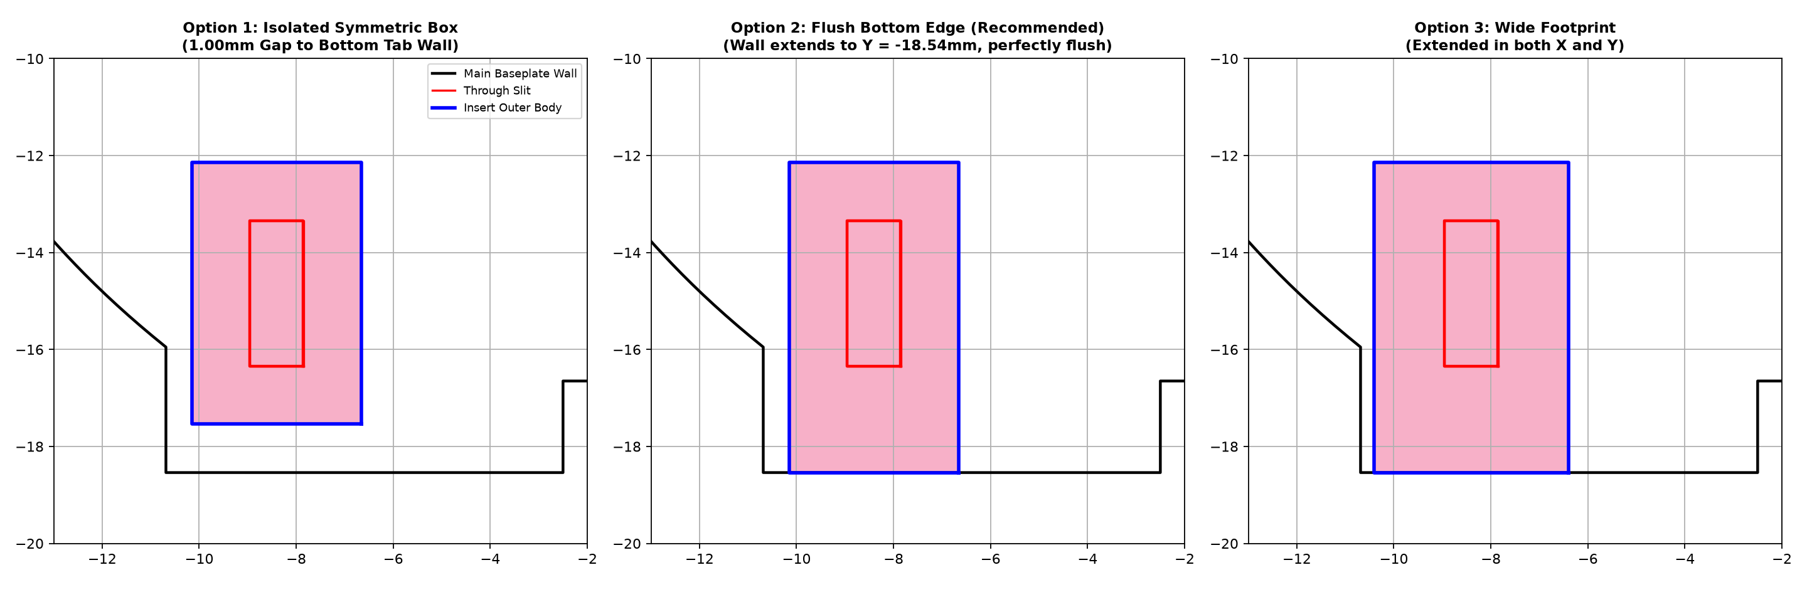
testing/insert_gap_solutions_preview.png
