elliotmartin92/kia-socket/testing/inserts_fit_analysis.png

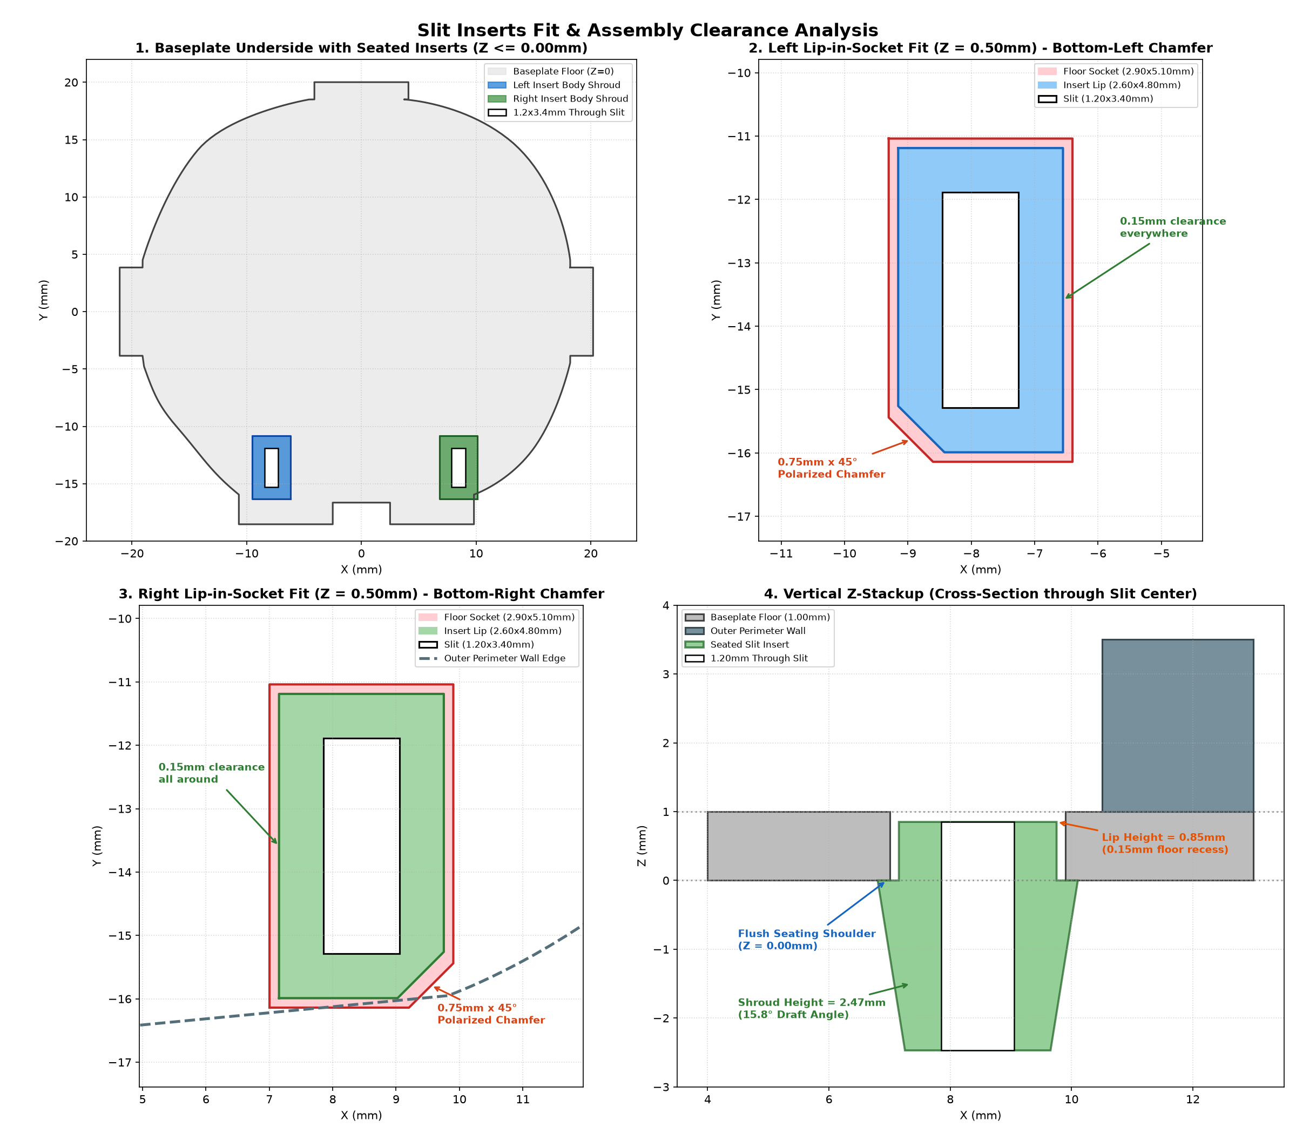
testing/inserts_fit_analysis.png
