elliotmartin92/kia-socket/testing/inspect_insert_gap.png

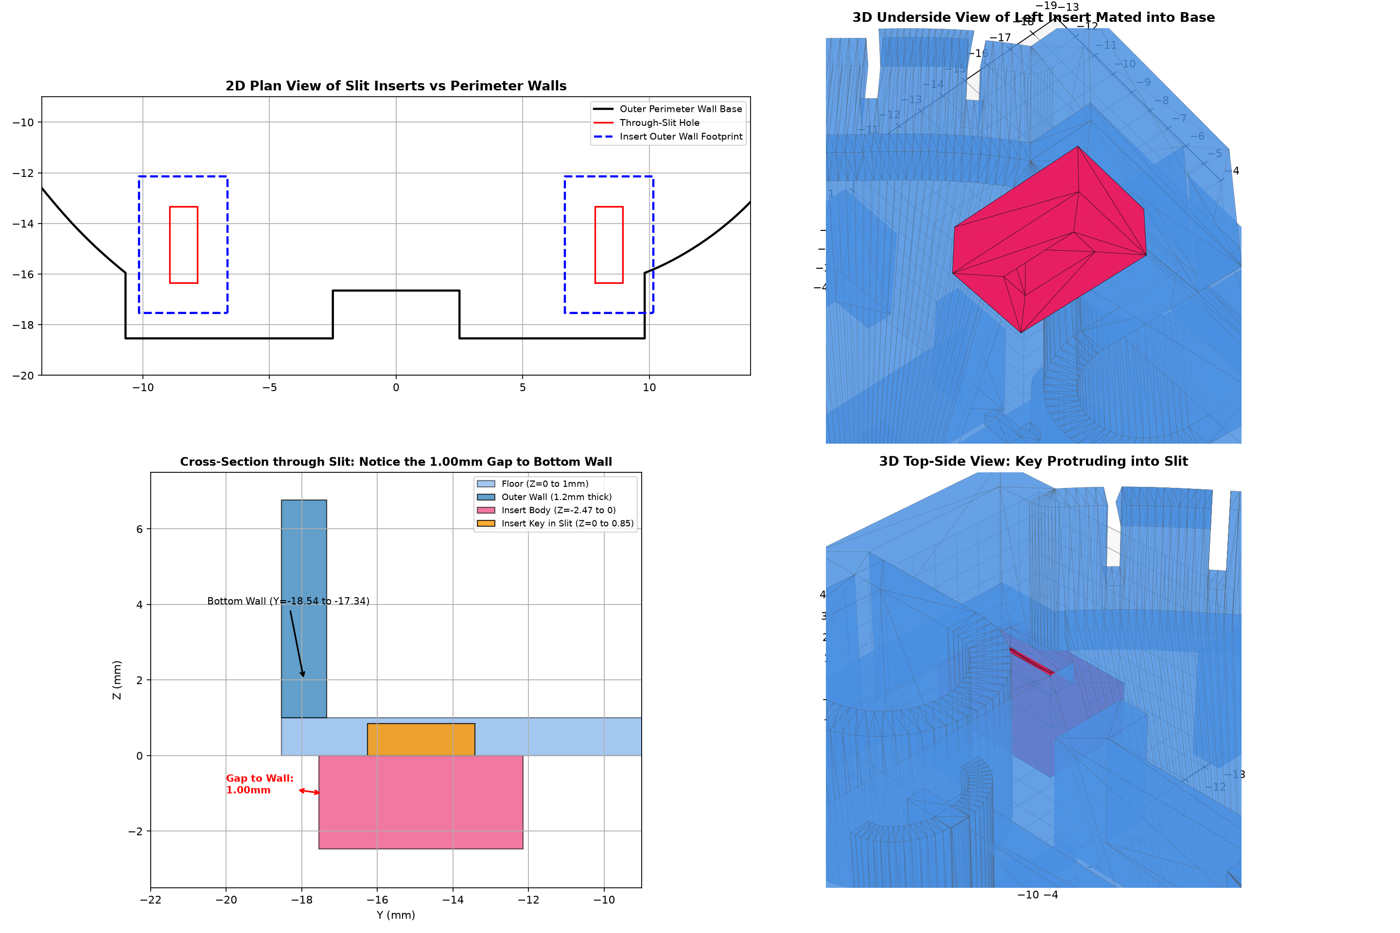
testing/inspect_insert_gap.png
