elliotmartin92/kia-socket/testing/inspect_key_modification.png

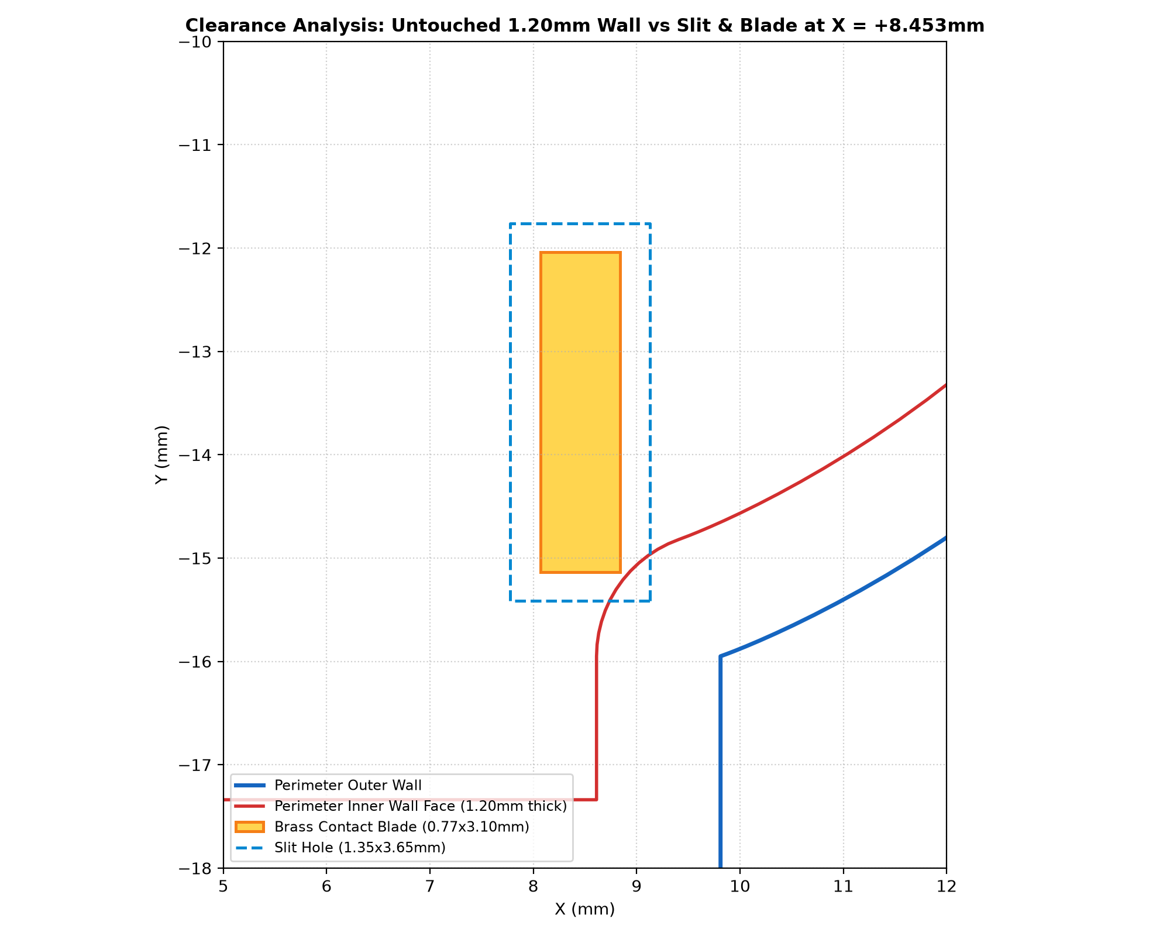
testing/inspect_key_modification.png
