elliotmartin92/kia-socket/testing/internal_features_exact.png

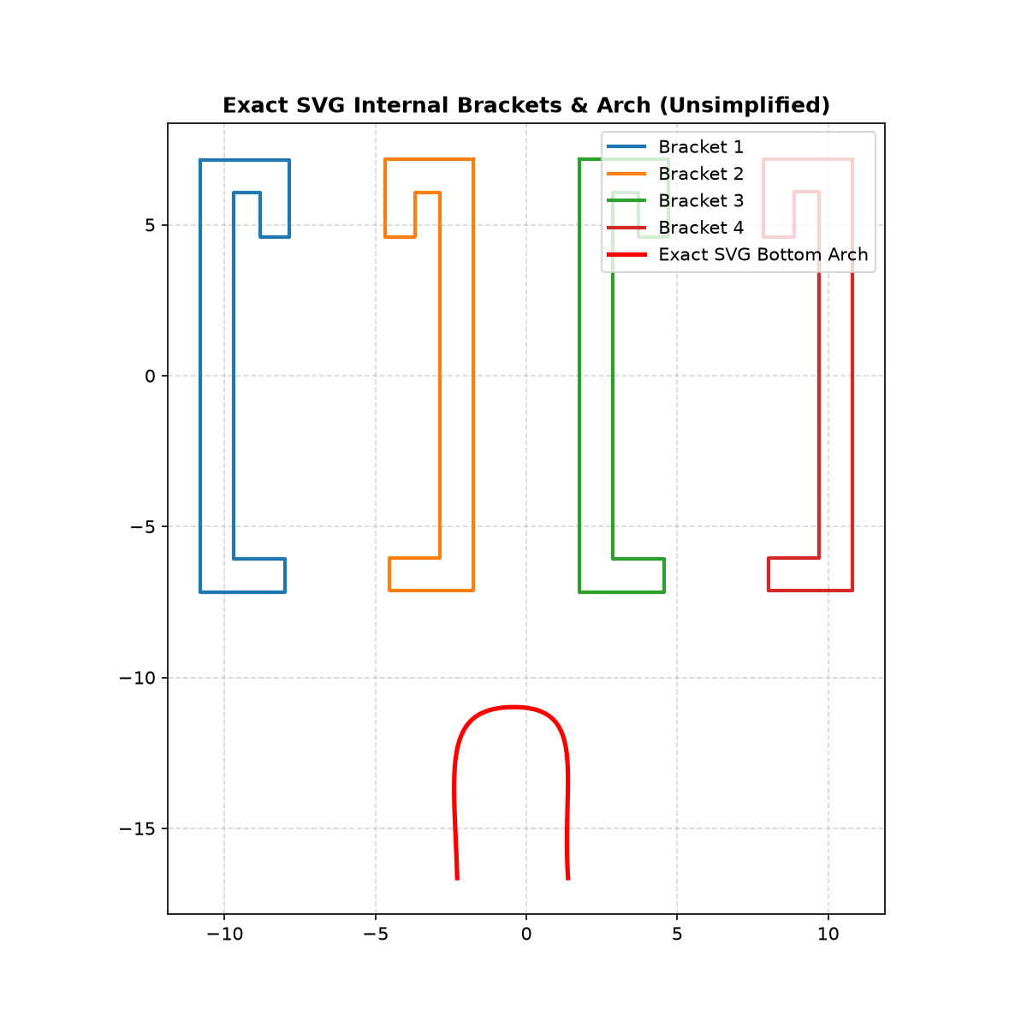
testing/internal_features_exact.png
