elliotmartin92/kia-socket/testing/key_modification_comparison.png

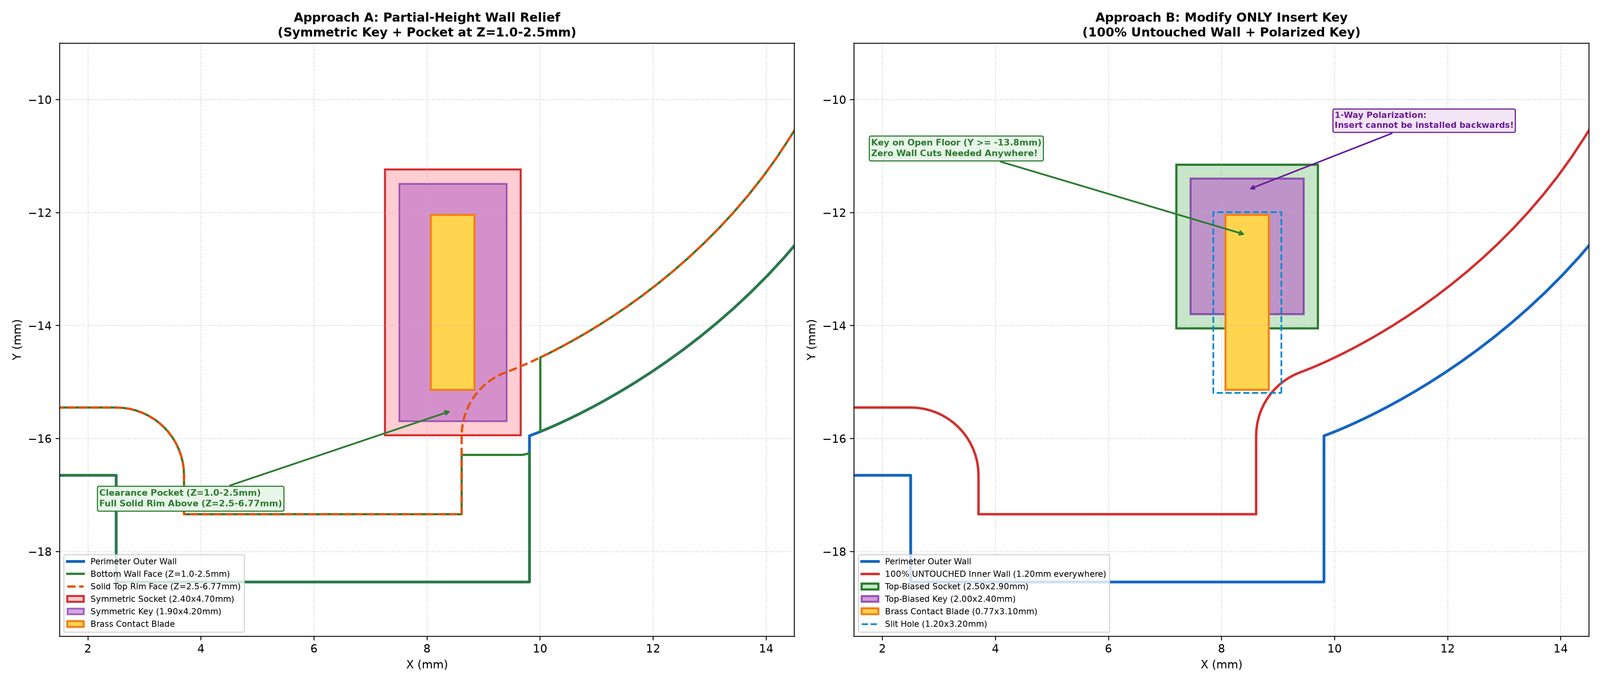
testing/key_modification_comparison.png
