elliotmartin92/kia-socket/testing/new_curved_feature_3d.png

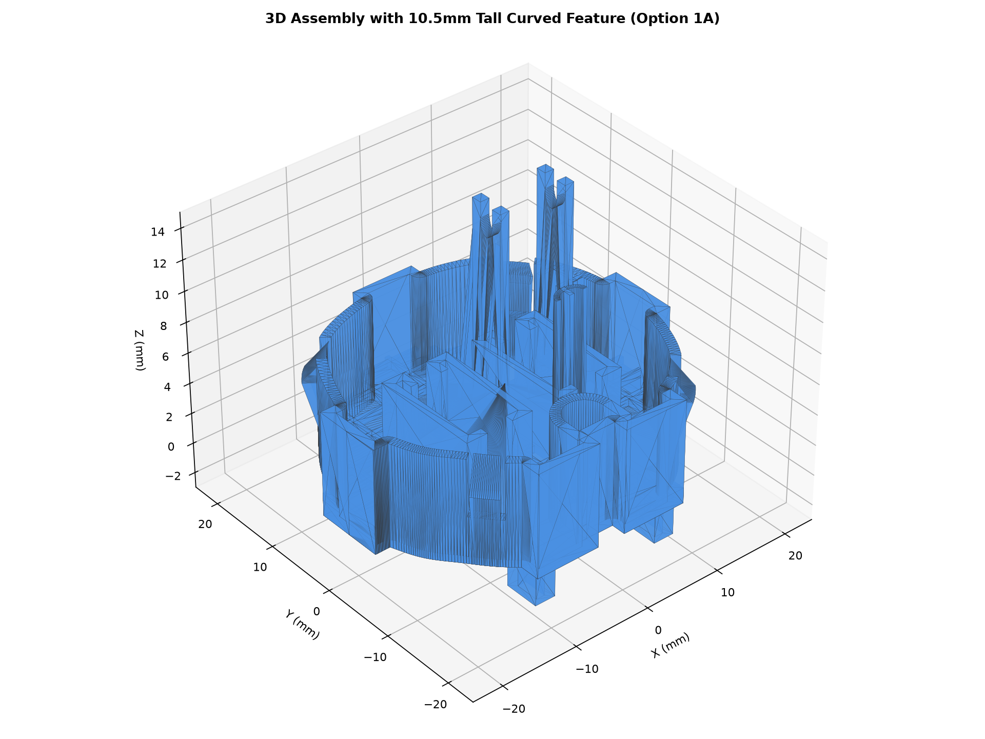
testing/new_curved_feature_3d.png
