elliotmartin92/kia-socket/testing/new_feature_candidates.png

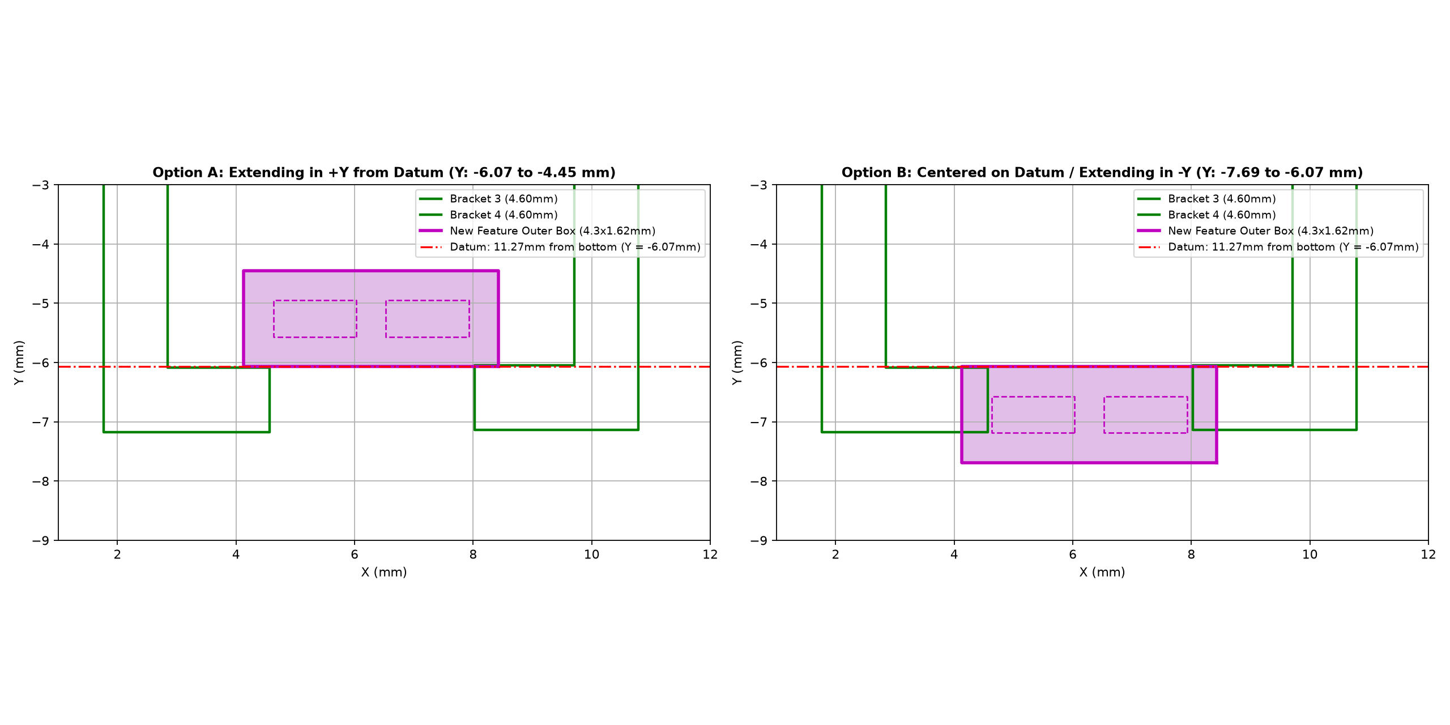
testing/new_feature_candidates.png
