elliotmartin92/kia-socket/testing/no_ribs_below_brackets.png

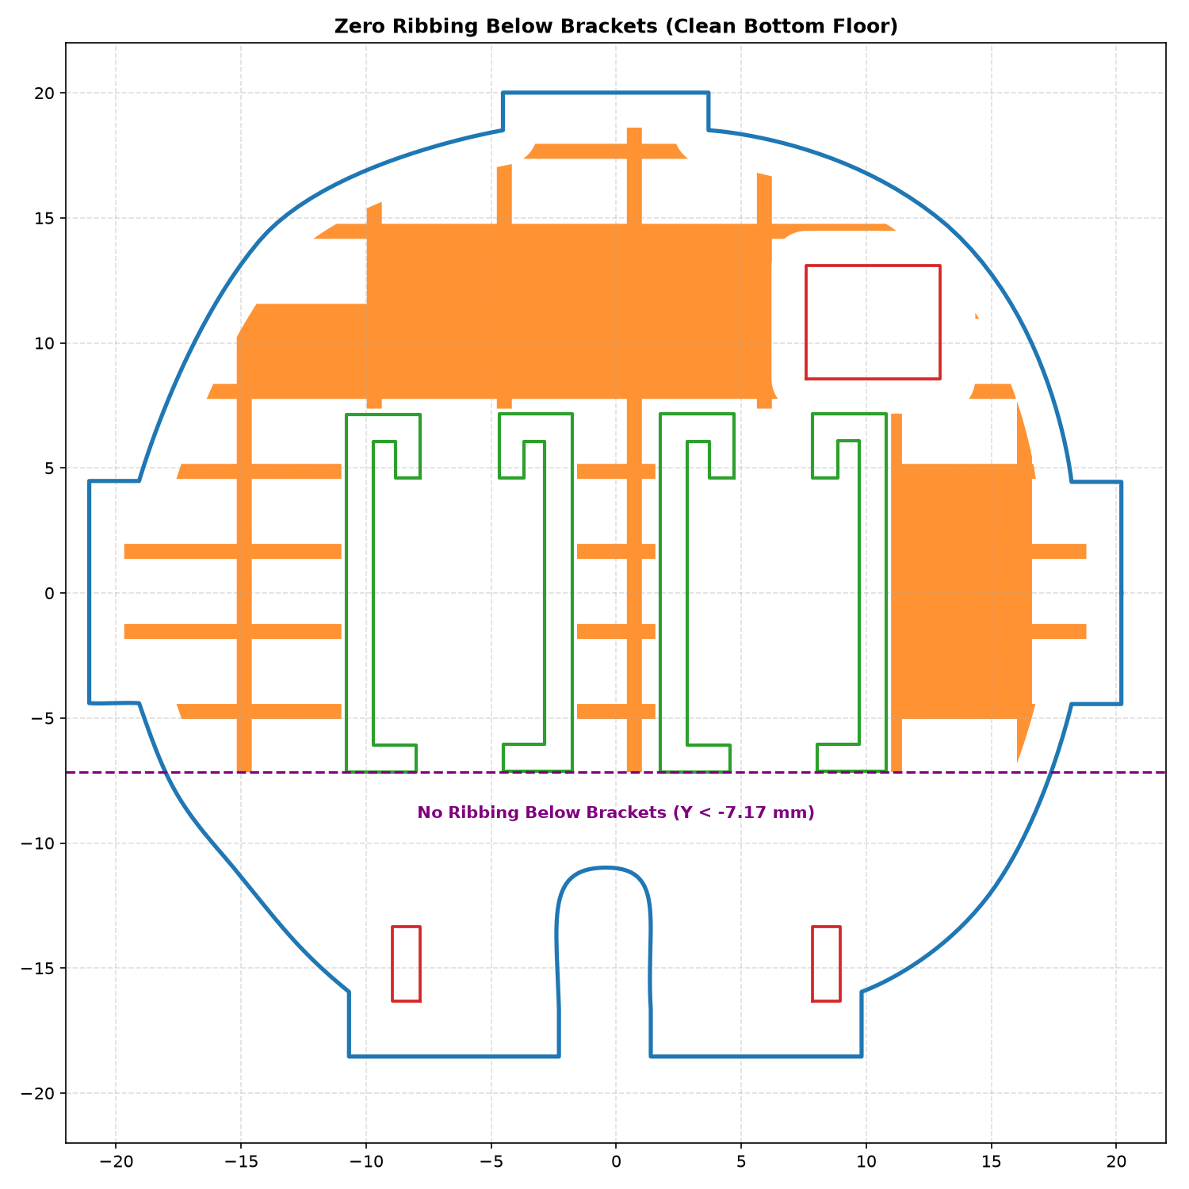
testing/no_ribs_below_brackets.png
