elliotmartin92/kia-socket/testing/no_ribs_under_brackets_options.png

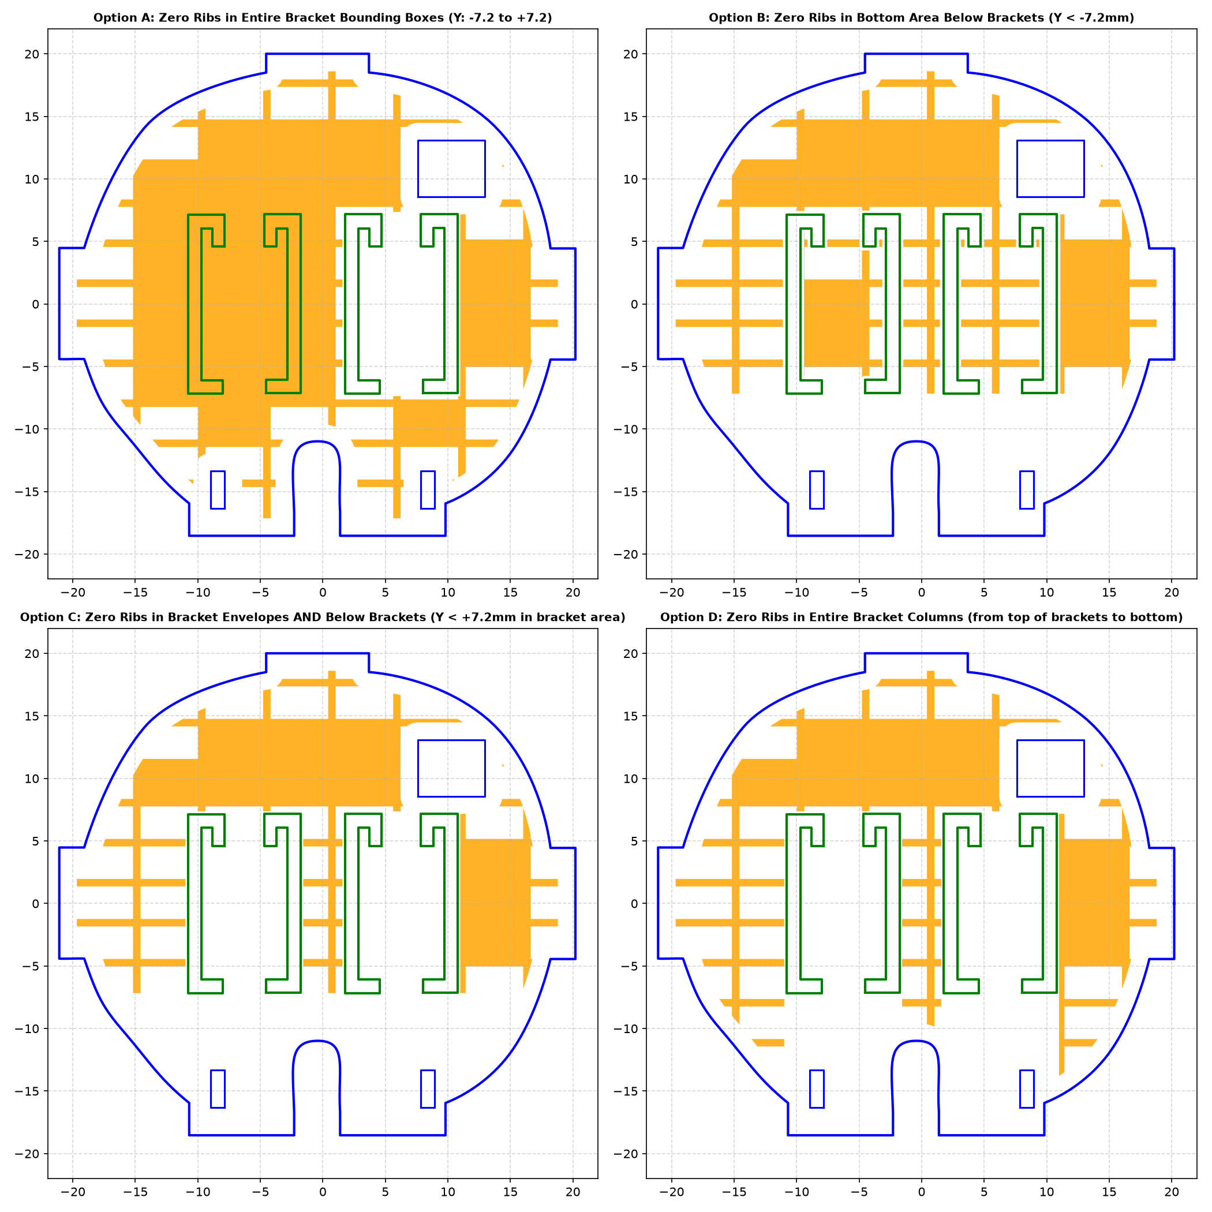
testing/no_ribs_under_brackets_options.png
