elliotmartin92/kia-socket/testing/oem_shaft_rocker_inspection.png

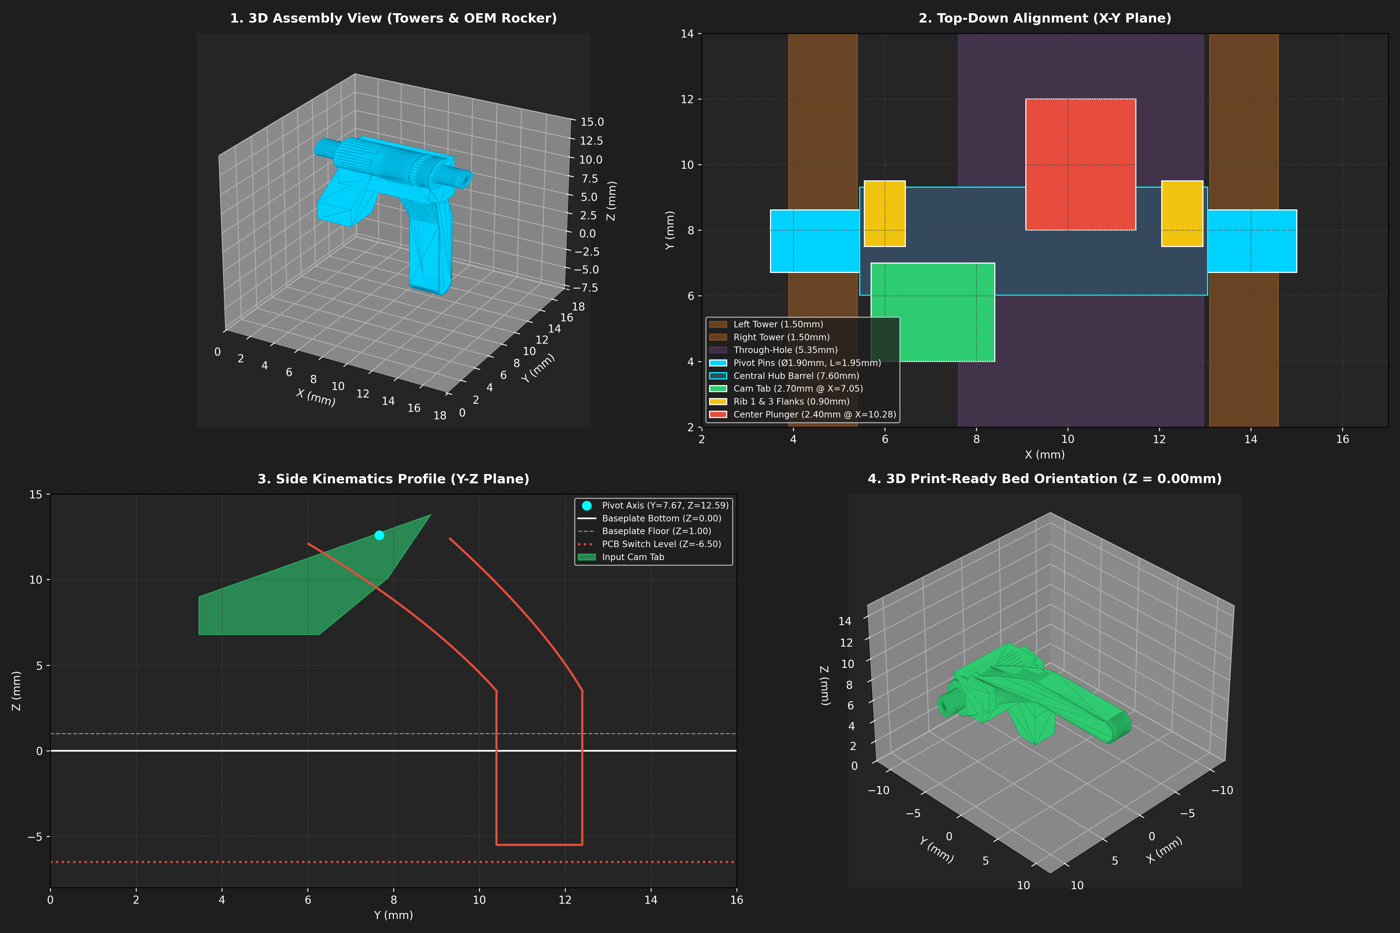
testing/oem_shaft_rocker_inspection.png
