elliotmartin92/kia-socket/testing/optimized_full_width_cam_fit.png

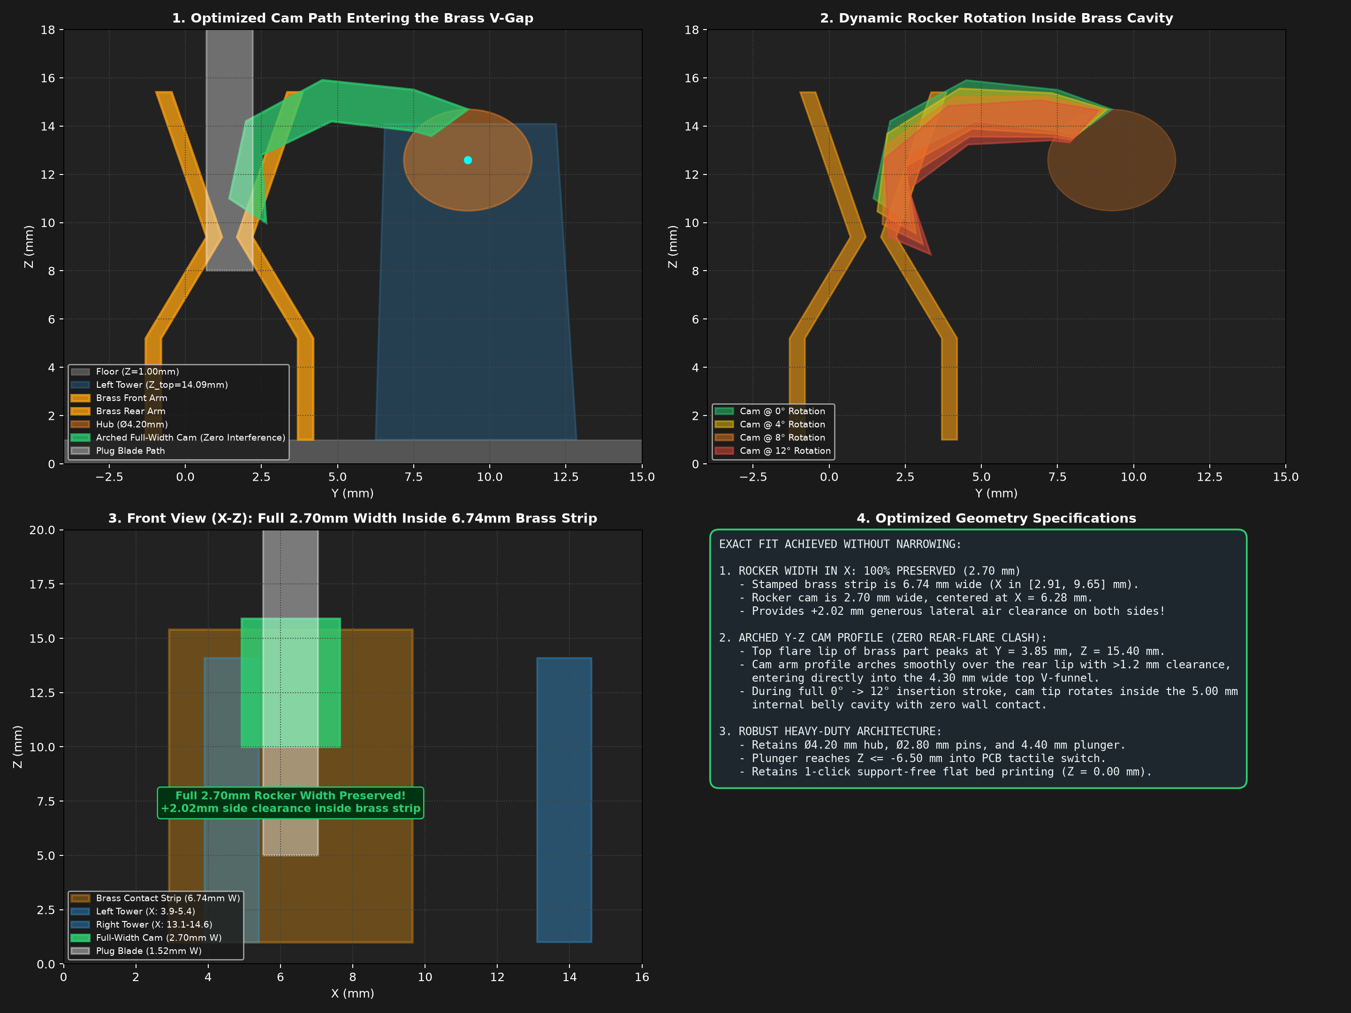
testing/optimized_full_width_cam_fit.png
