elliotmartin92/kia-socket/testing/option1_belly_cam_simulation.png

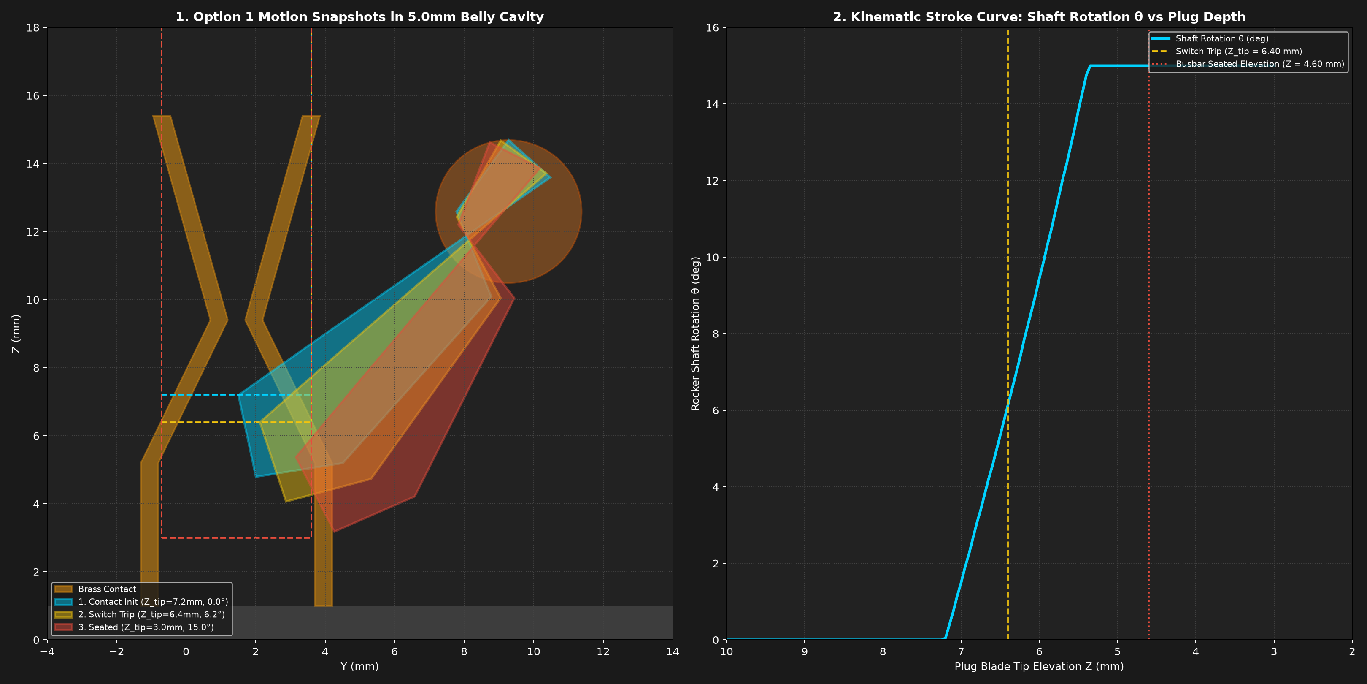
testing/option1_belly_cam_simulation.png
