elliotmartin92/kia-socket/testing/partial_height_wall_relief_preview.png

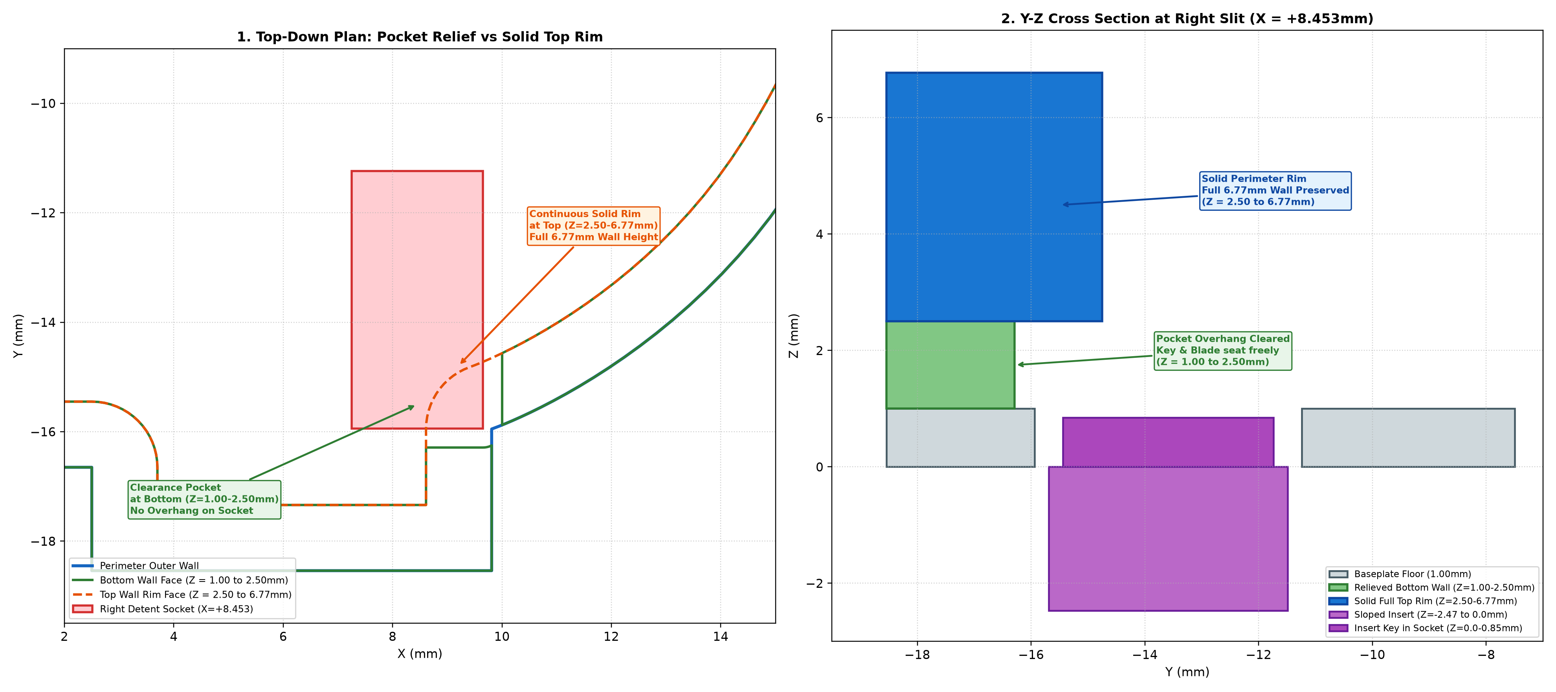
testing/partial_height_wall_relief_preview.png
