elliotmartin92/kia-socket/testing/path_comparison.png

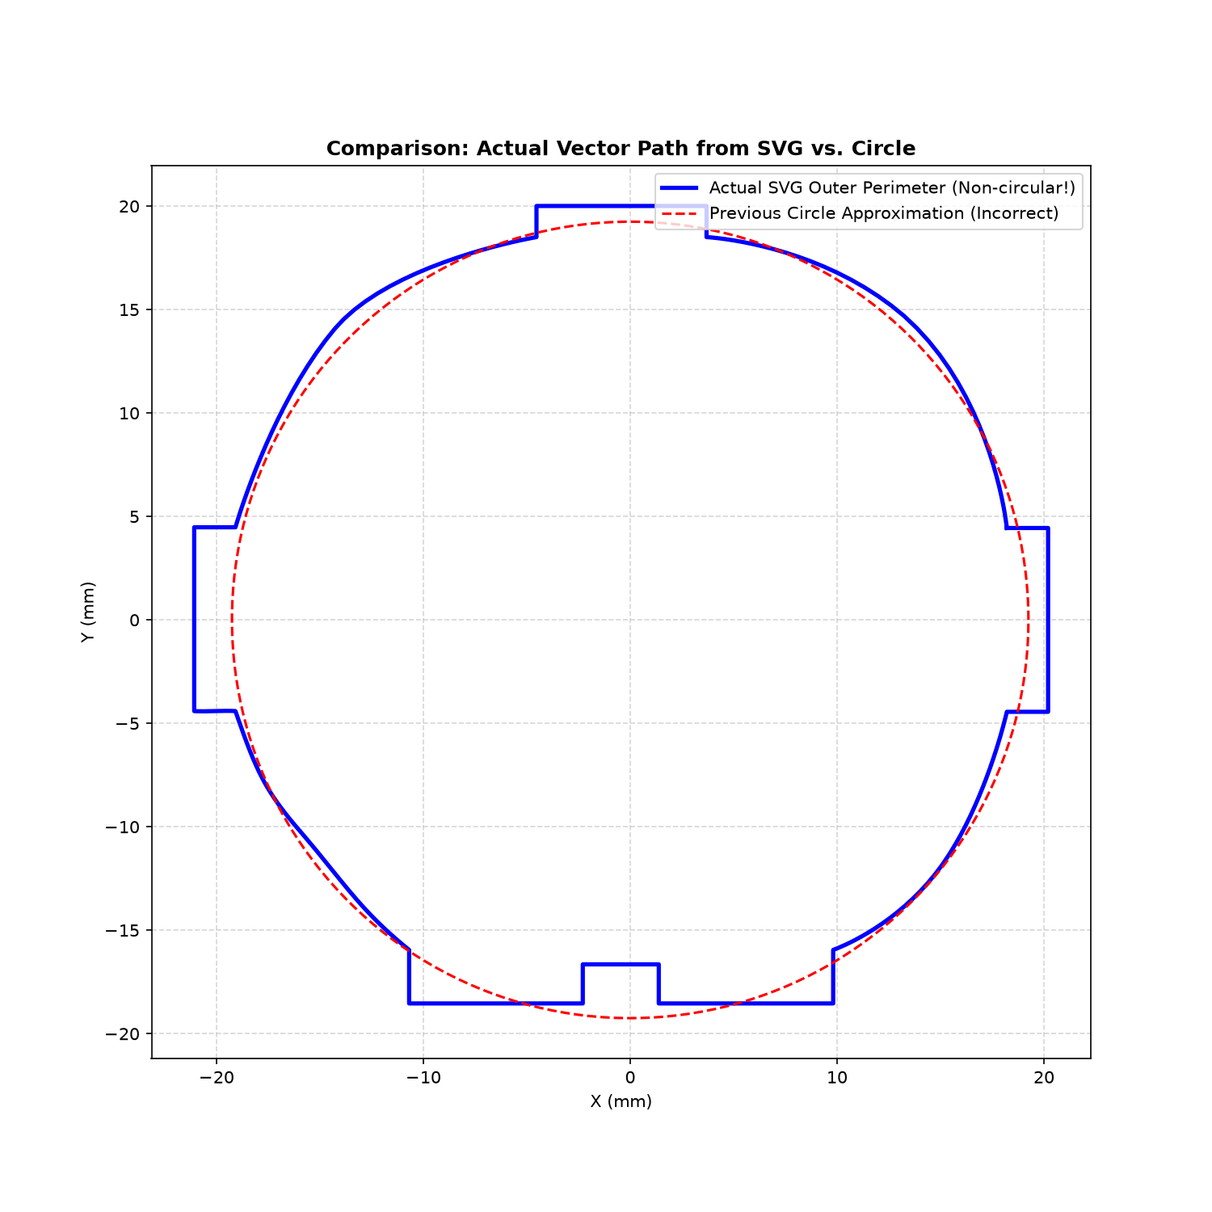
testing/path_comparison.png
