elliotmartin92/kia-socket/testing/perfect_key_preview.png

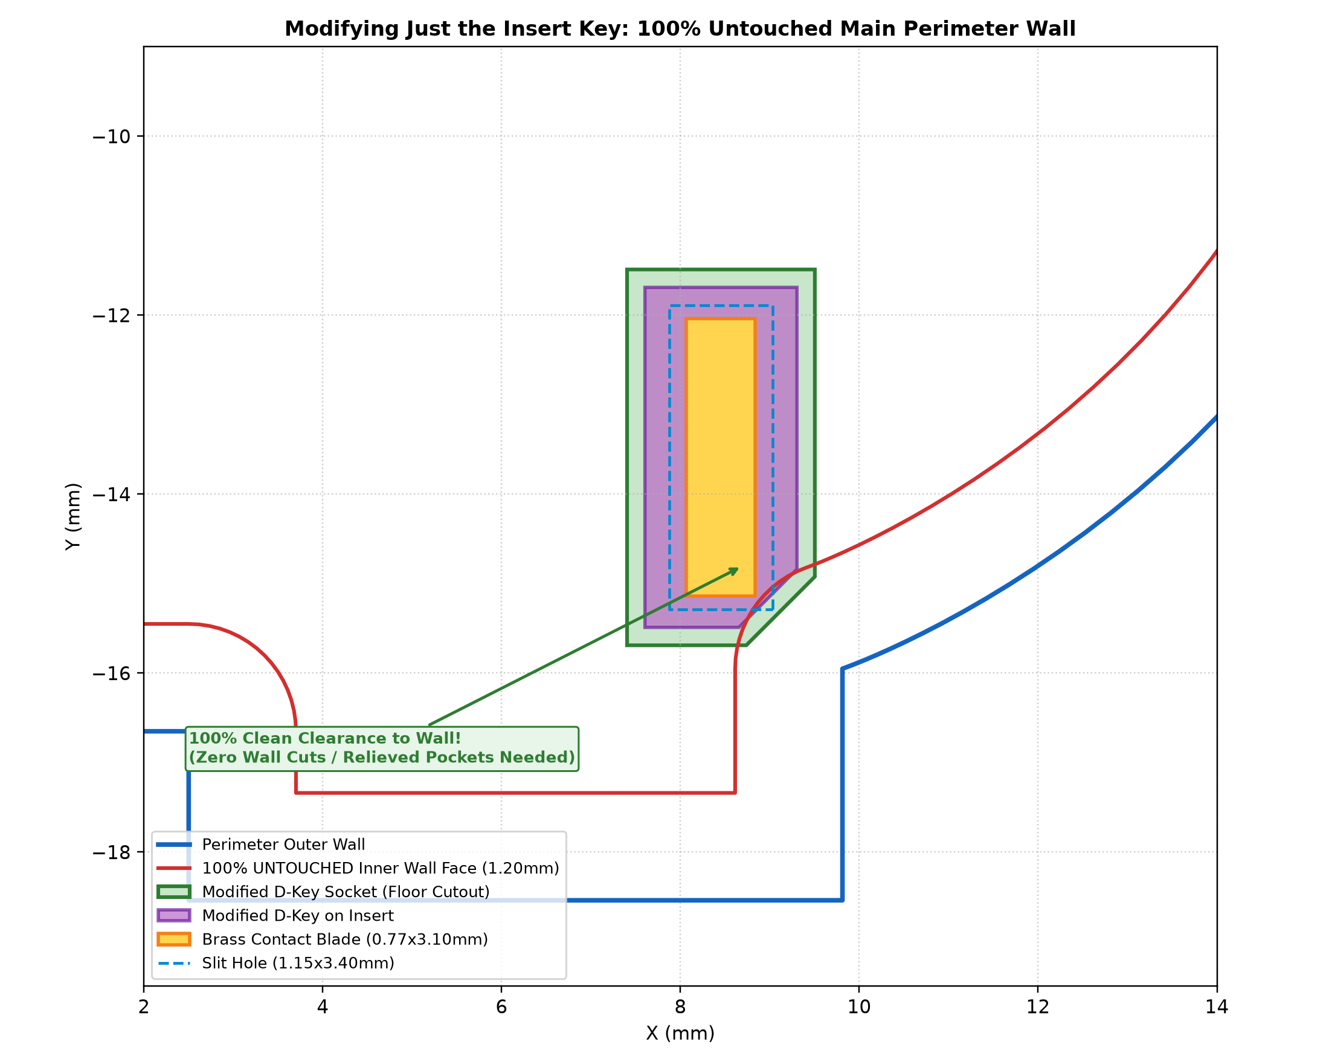
testing/perfect_key_preview.png
