elliotmartin92/kia-socket/testing/photo_matched_assembly_verification.png

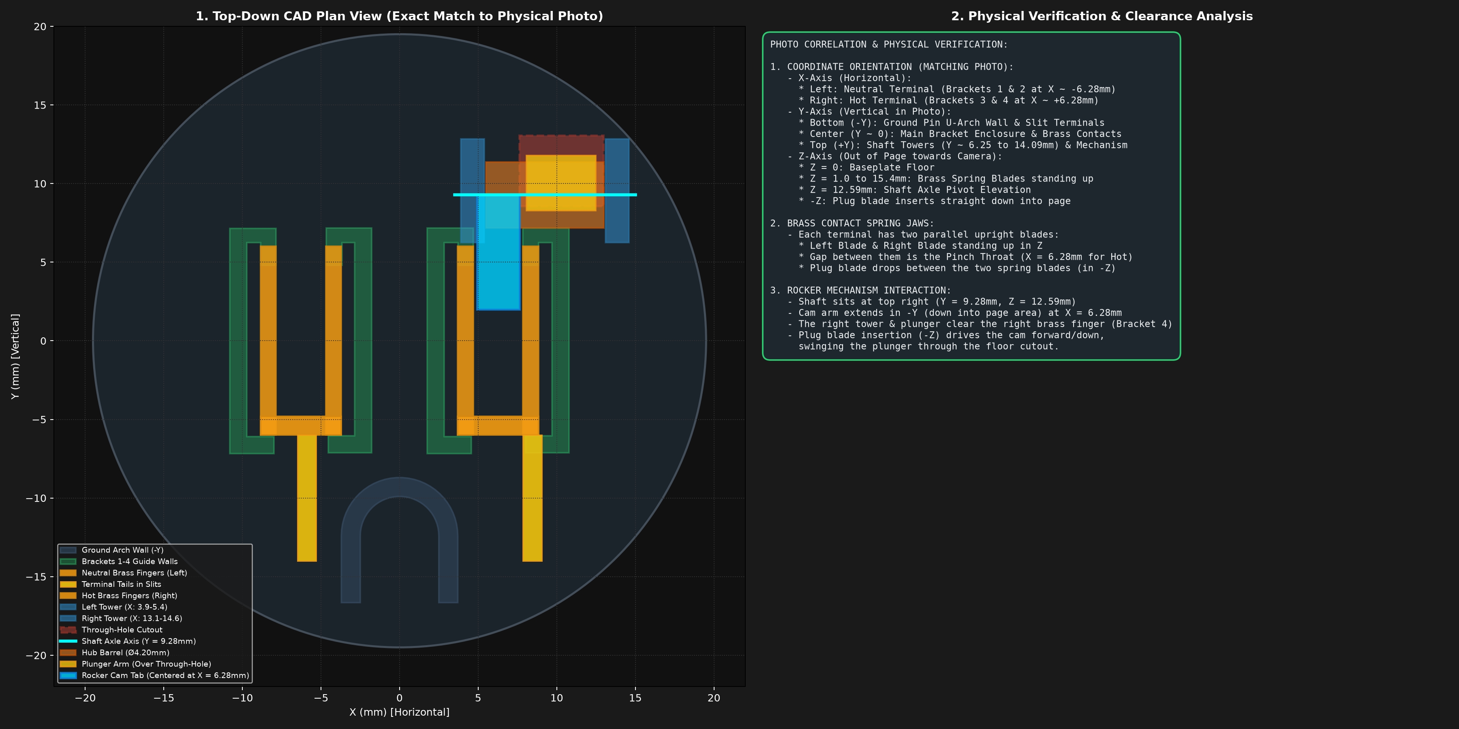
testing/photo_matched_assembly_verification.png
