elliotmartin92/kia-socket/testing/plug_gap_check2_diagram.png

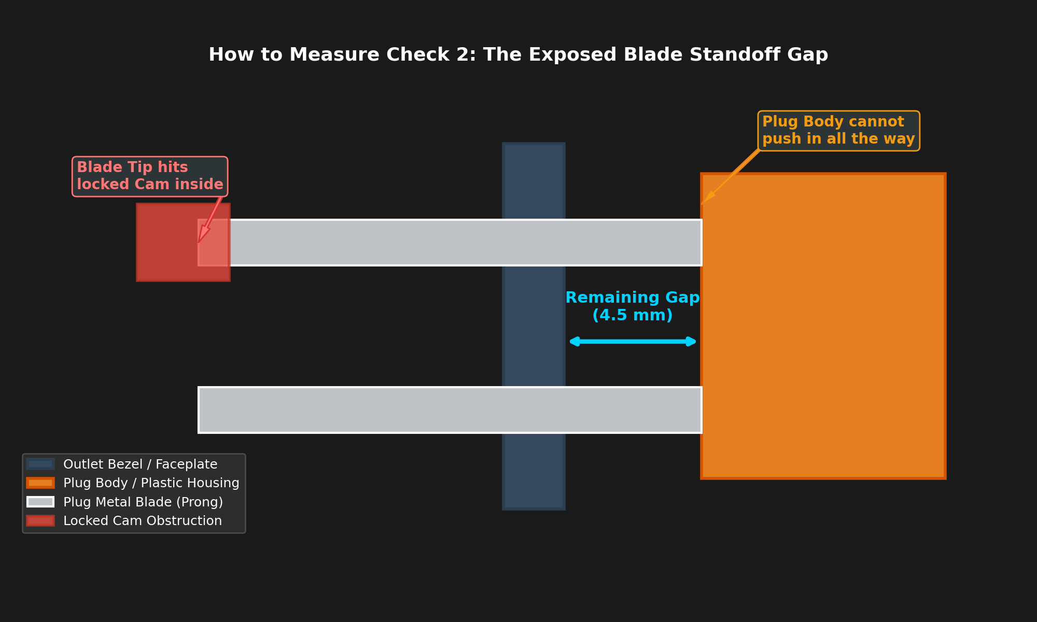
testing/plug_gap_check2_diagram.png
