elliotmartin92/kia-socket/testing/plug_insertion_simulation.png

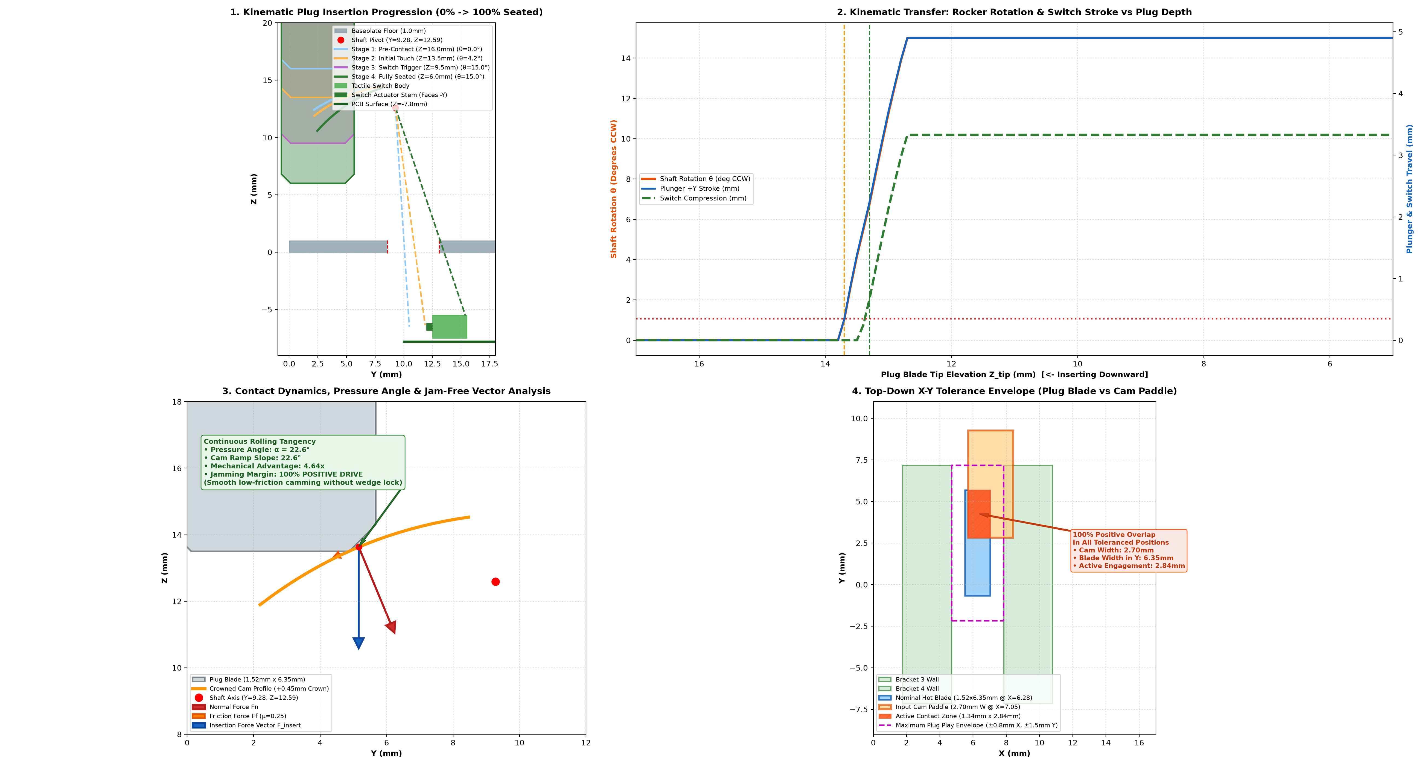
testing/plug_insertion_simulation.png
