elliotmartin92/kia-socket/testing/polarized_key_preview.png

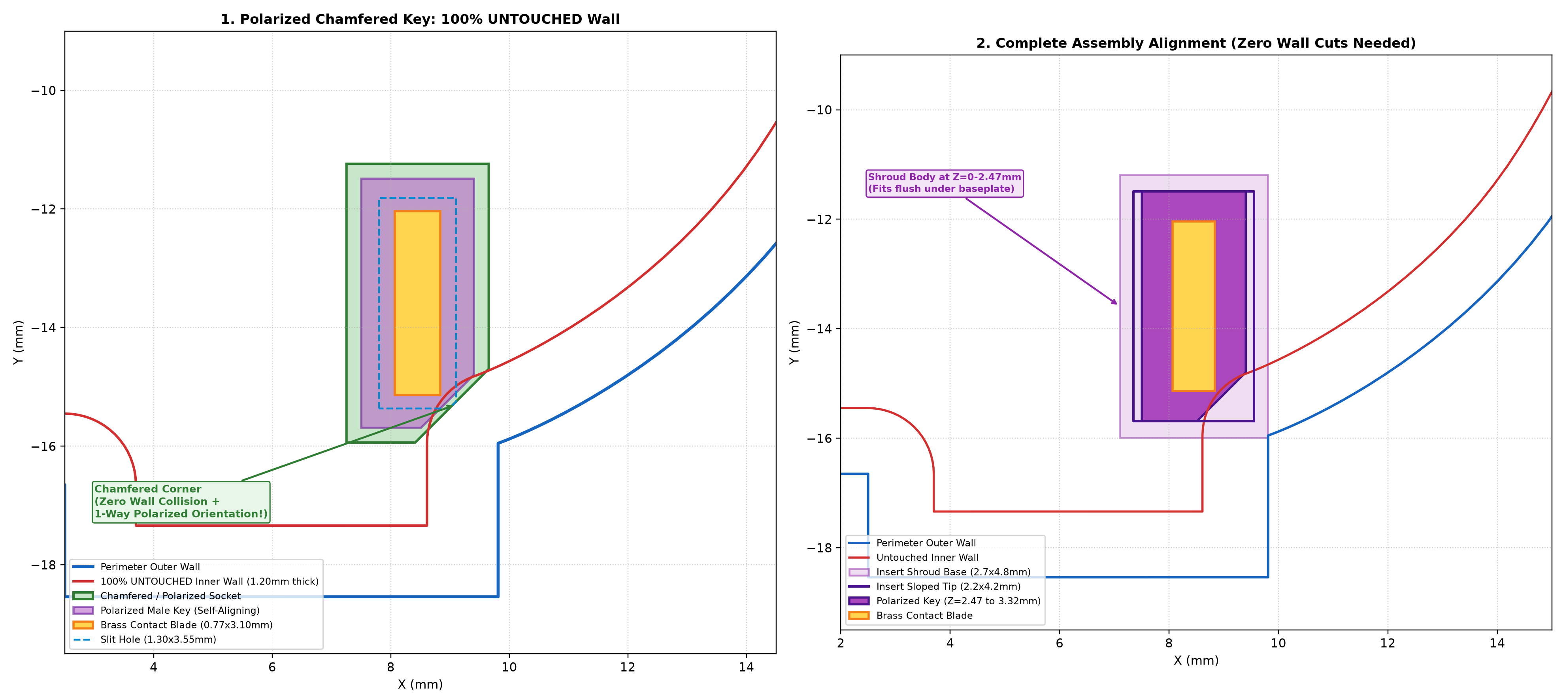
testing/polarized_key_preview.png
