elliotmartin92/kia-socket/testing/reinforcement_variations_comparison.png

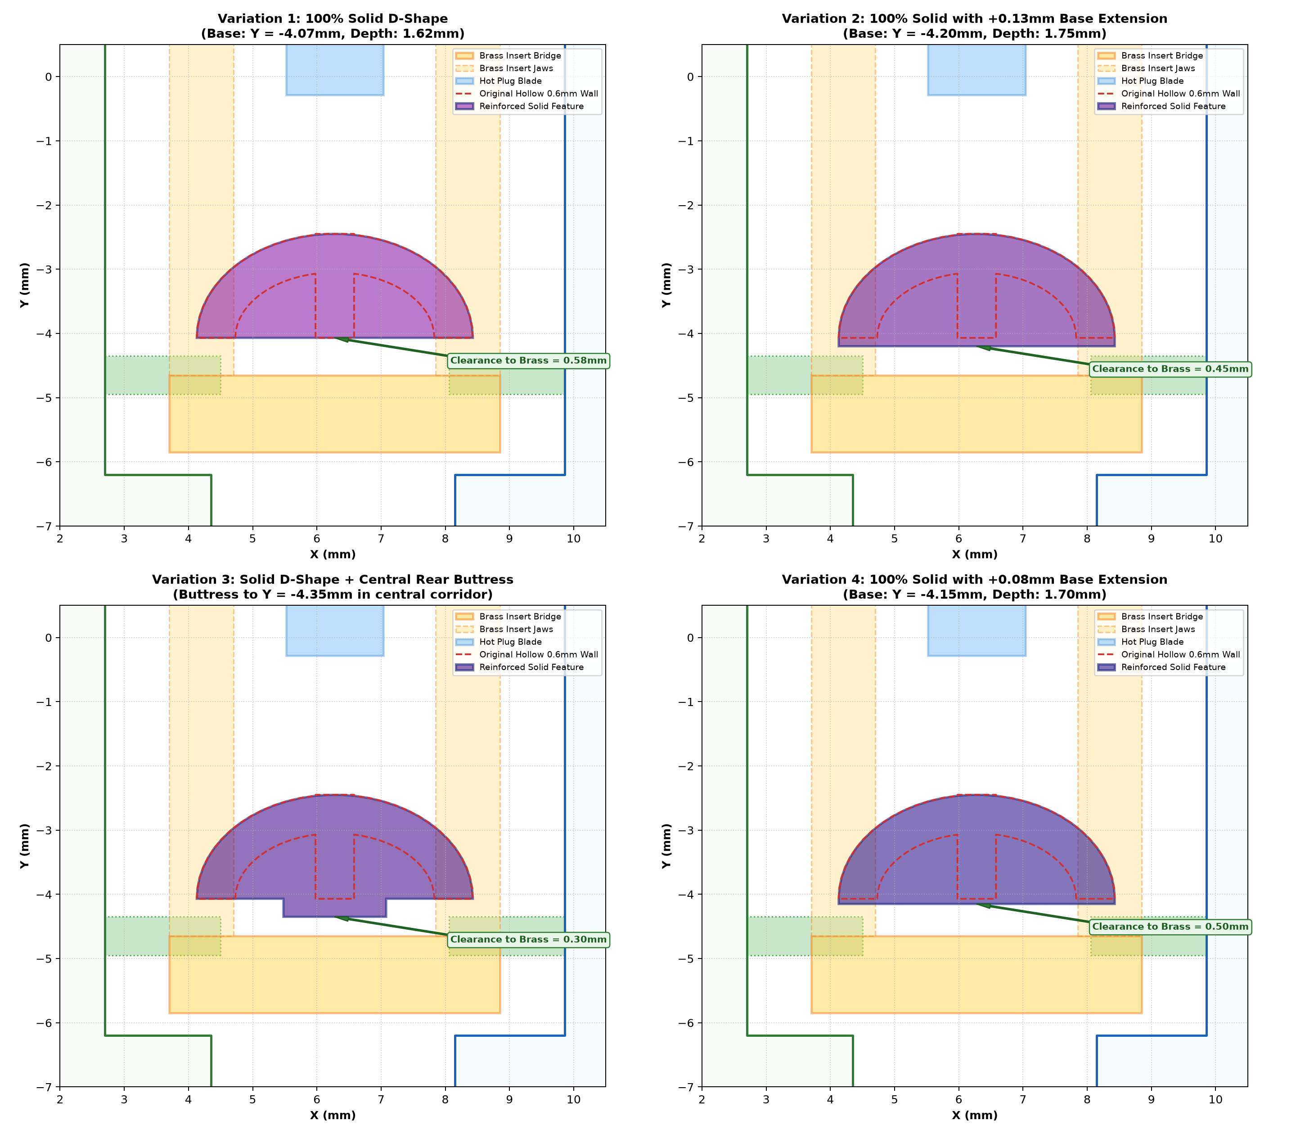
testing/reinforcement_variations_comparison.png
