elliotmartin92/kia-socket/testing/retention_cradle_preview.png

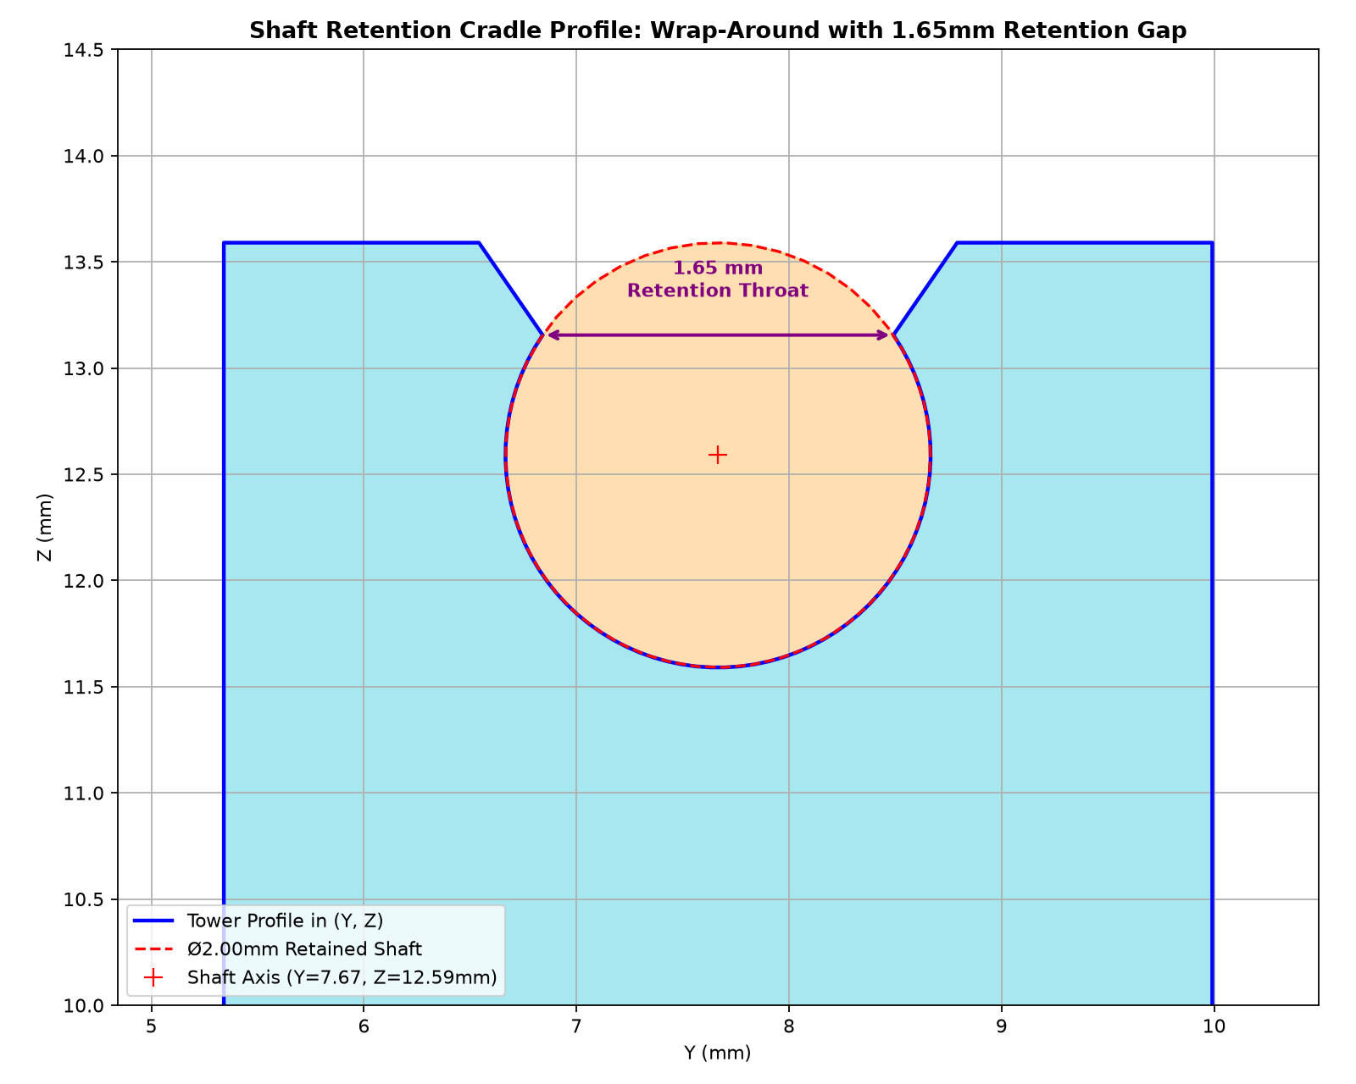
testing/retention_cradle_preview.png
