elliotmartin92/kia-socket/testing/rib_gap_options.png

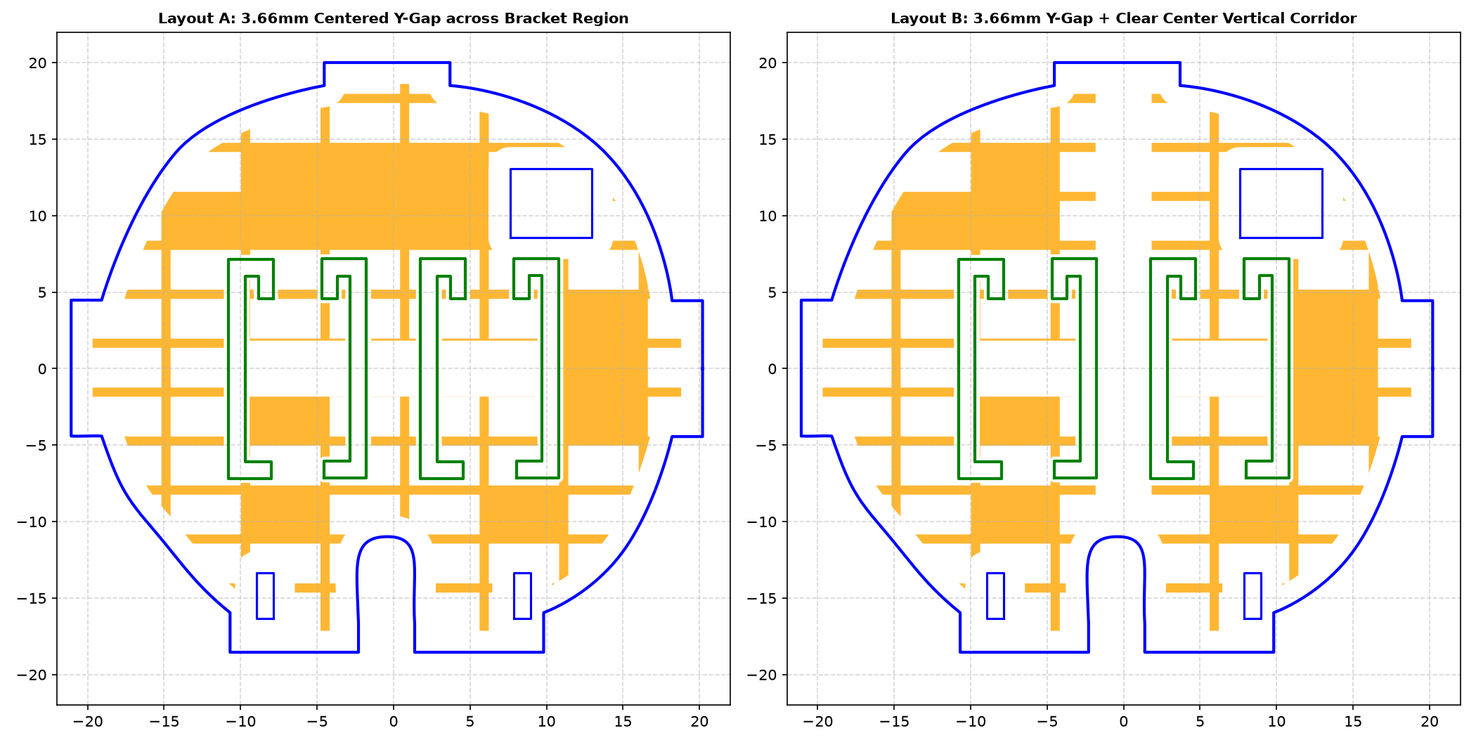
testing/rib_gap_options.png
