elliotmartin92/kia-socket/testing/rocker_caliper_measurement_diagram.png

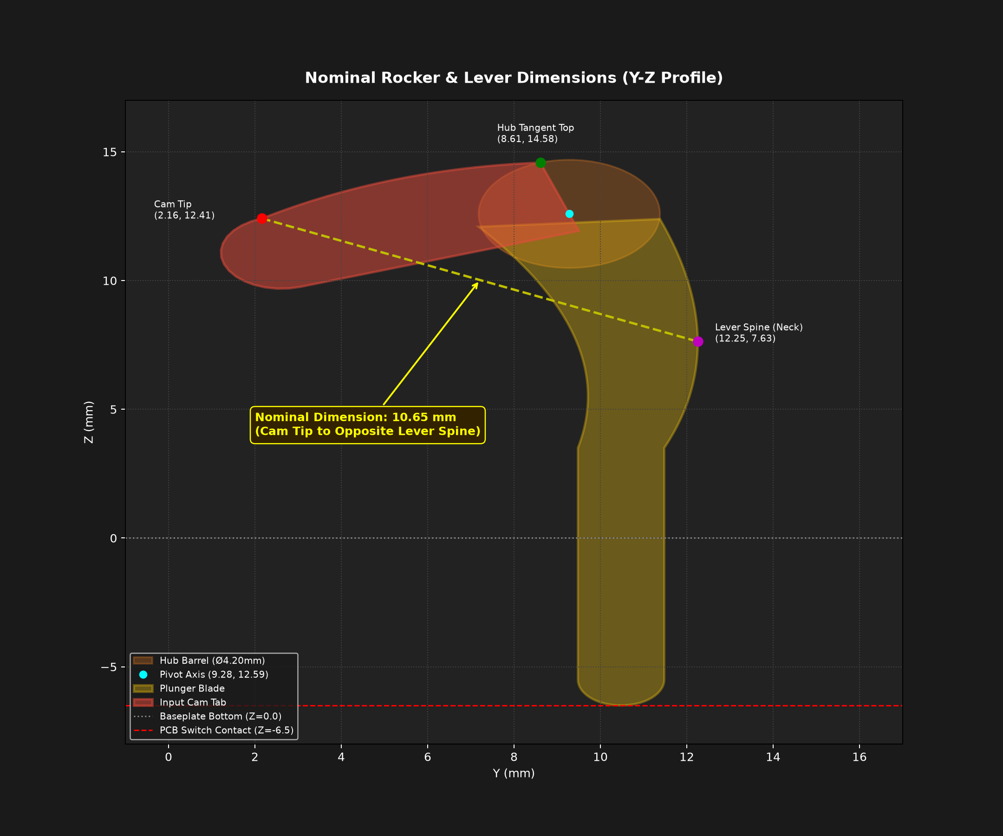
testing/rocker_caliper_measurement_diagram.png
