elliotmartin92/kia-socket/testing/rocker_stiffness_comparison.png

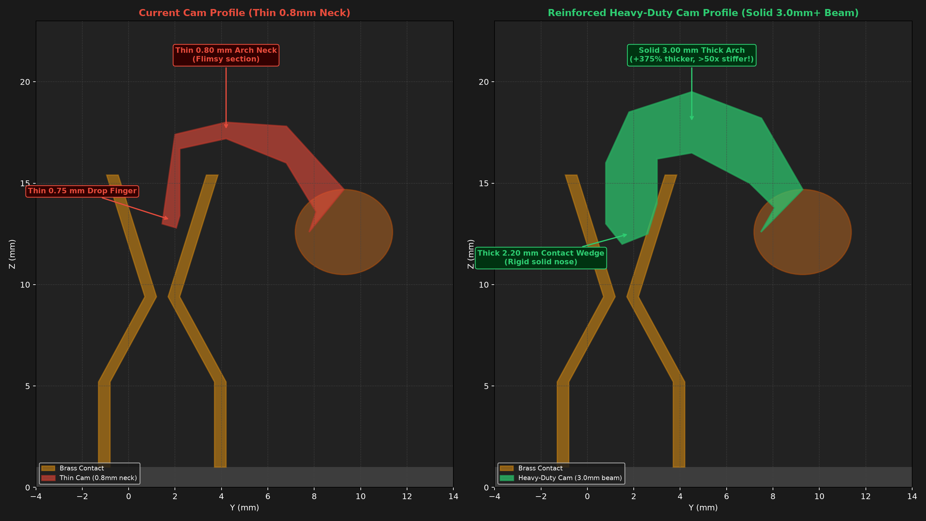
testing/rocker_stiffness_comparison.png
