elliotmartin92/kia-socket/testing/separate_slit_indexing_preview.png

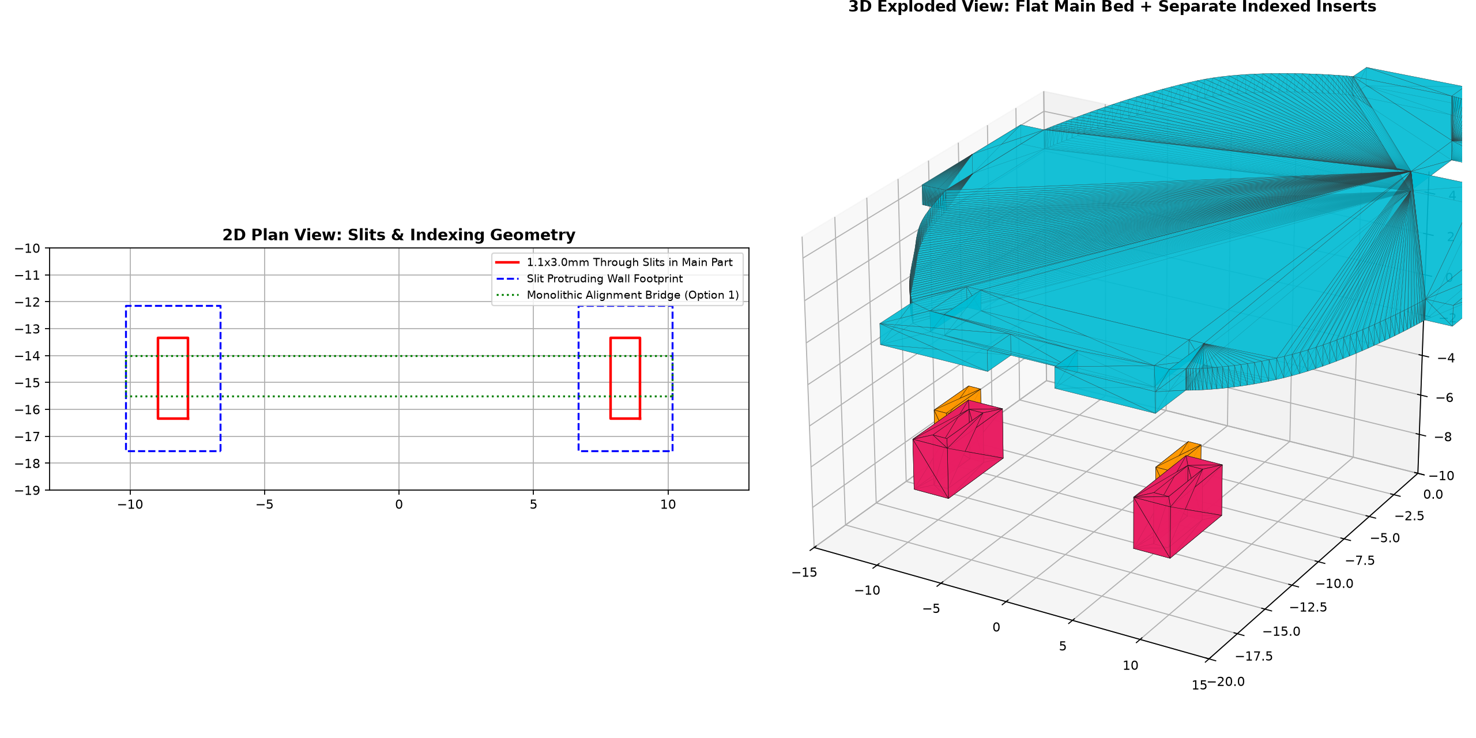
testing/separate_slit_indexing_preview.png
