elliotmartin92/kia-socket/testing/shaft_reinforcement_comparison.png

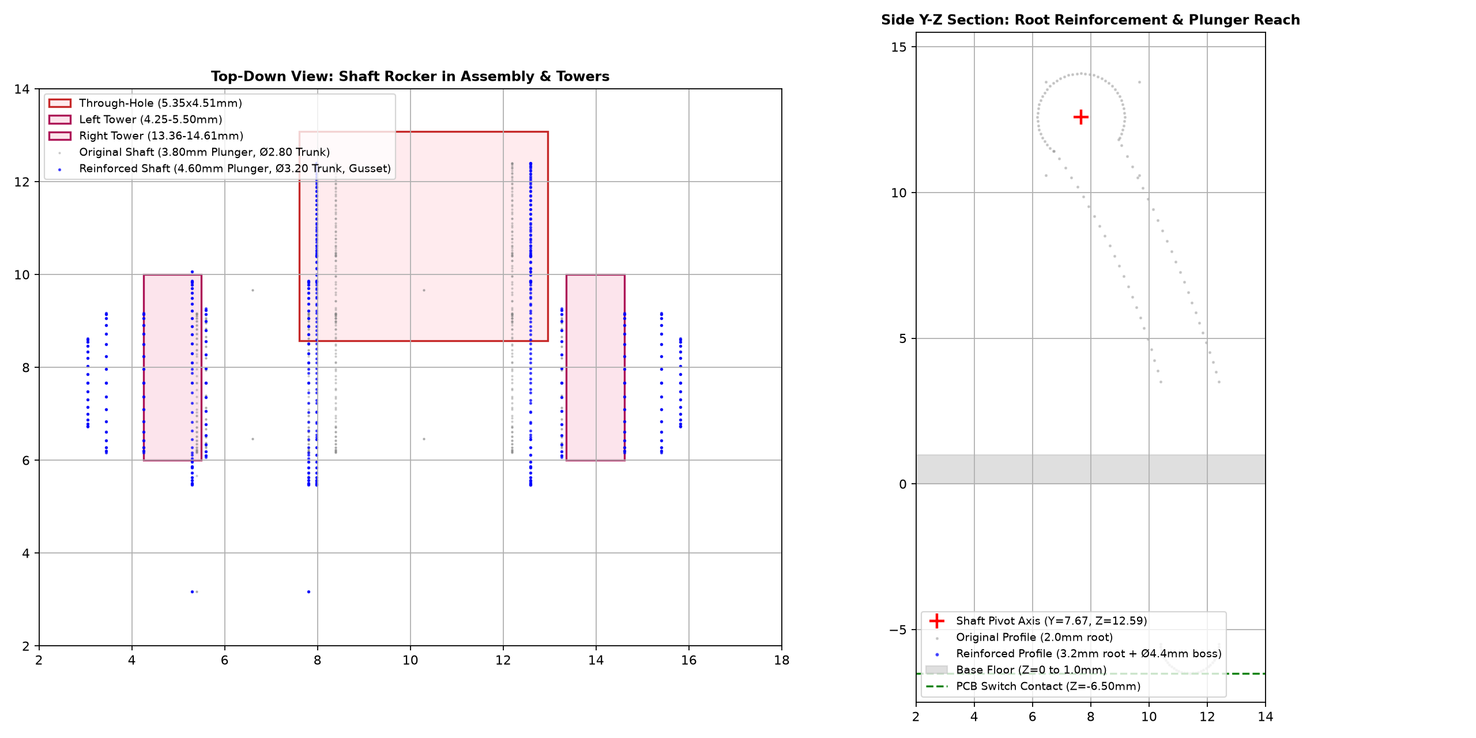
testing/shaft_reinforcement_comparison.png
