elliotmartin92/kia-socket/testing/shaft_supports_preview.png

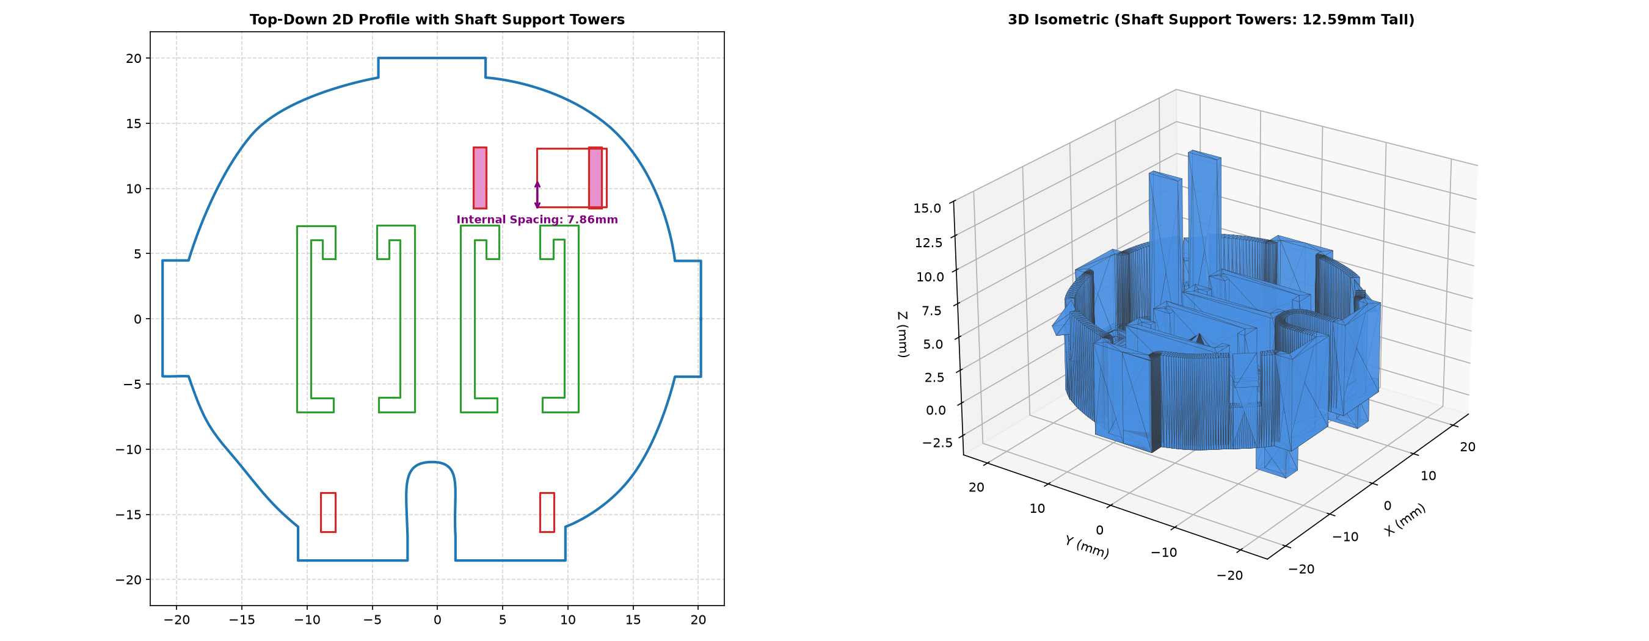
testing/shaft_supports_preview.png
