elliotmartin92/kia-socket/testing/side_ears_355_preview.png

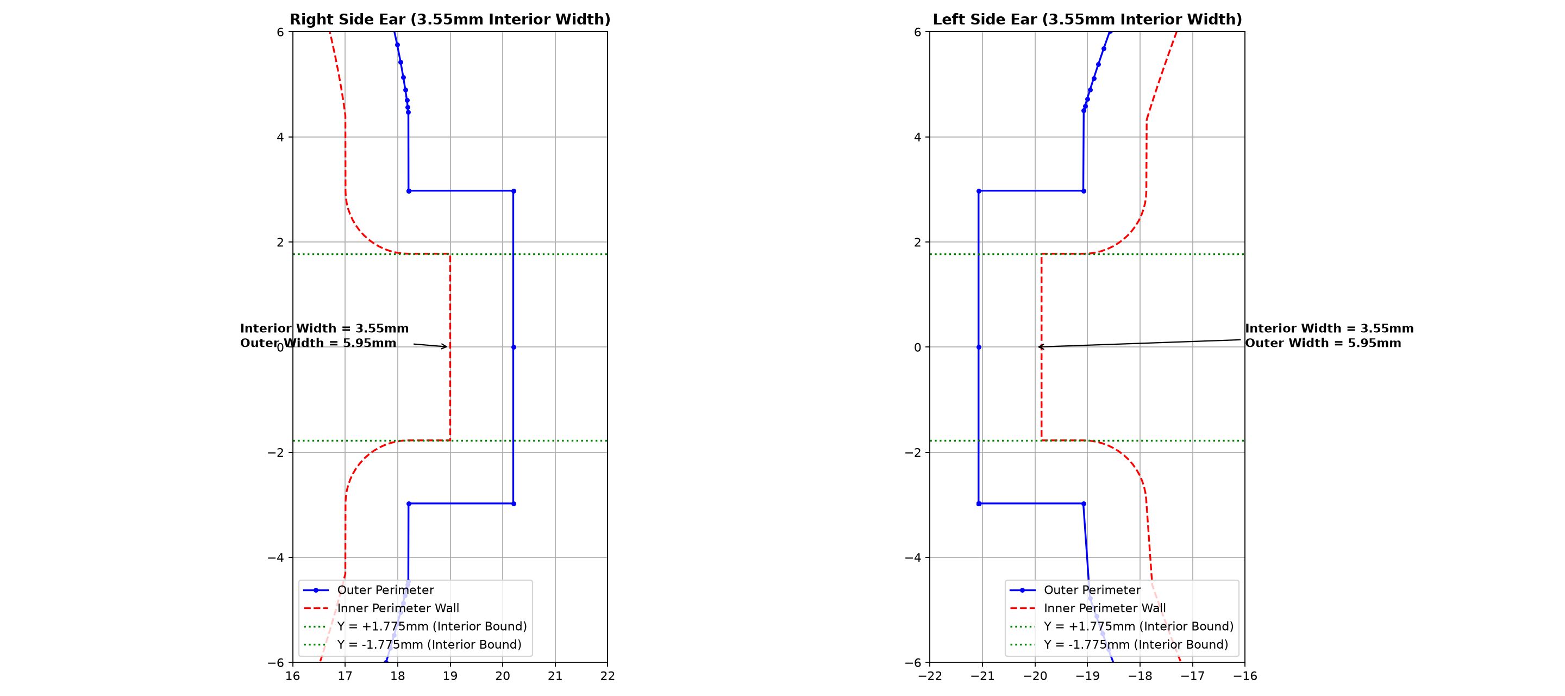
testing/side_ears_355_preview.png
