elliotmartin92/kia-socket/testing/slit_bottom_compare.png

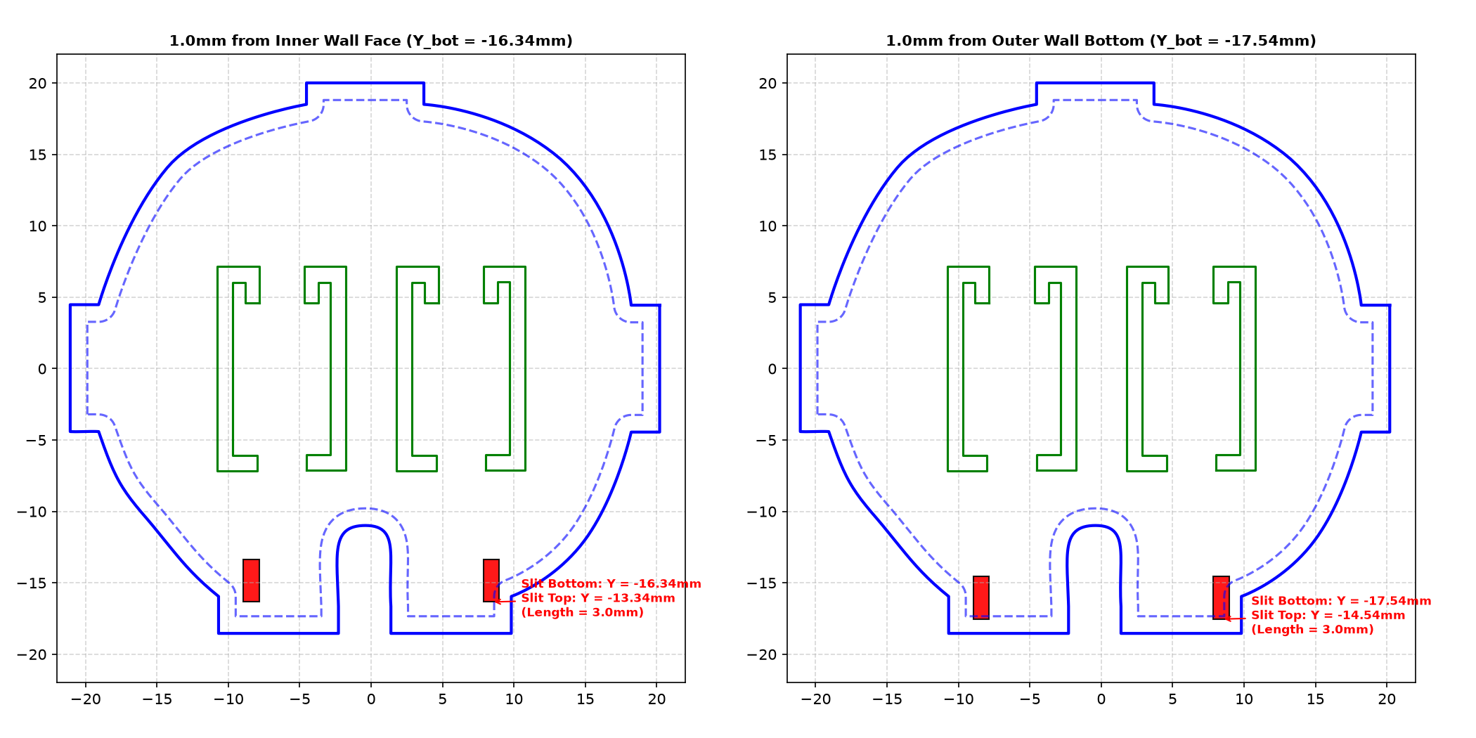
testing/slit_bottom_compare.png
