elliotmartin92/kia-socket/testing/slit_bracket_alignment_analysis.png

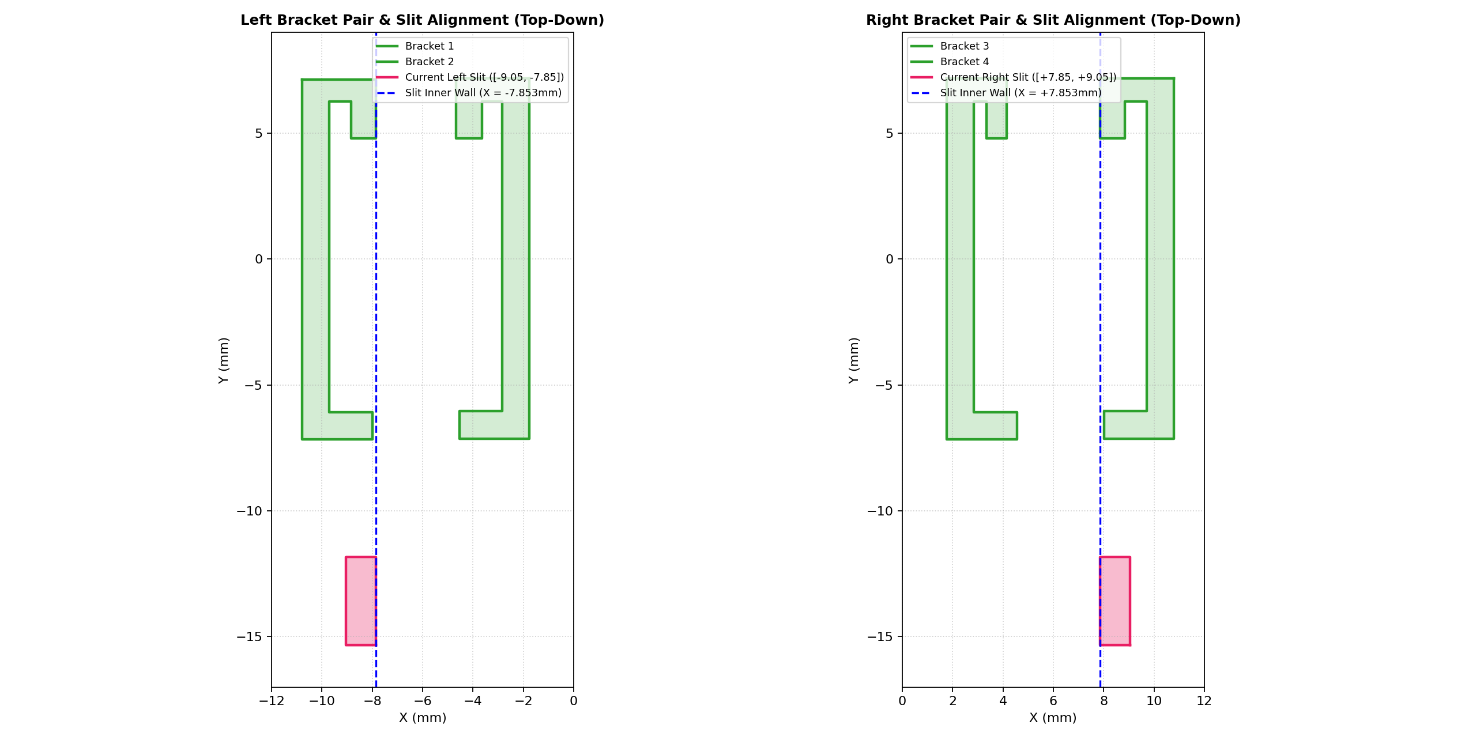
testing/slit_bracket_alignment_analysis.png
