elliotmartin92/kia-socket/testing/slit_centering_options.png

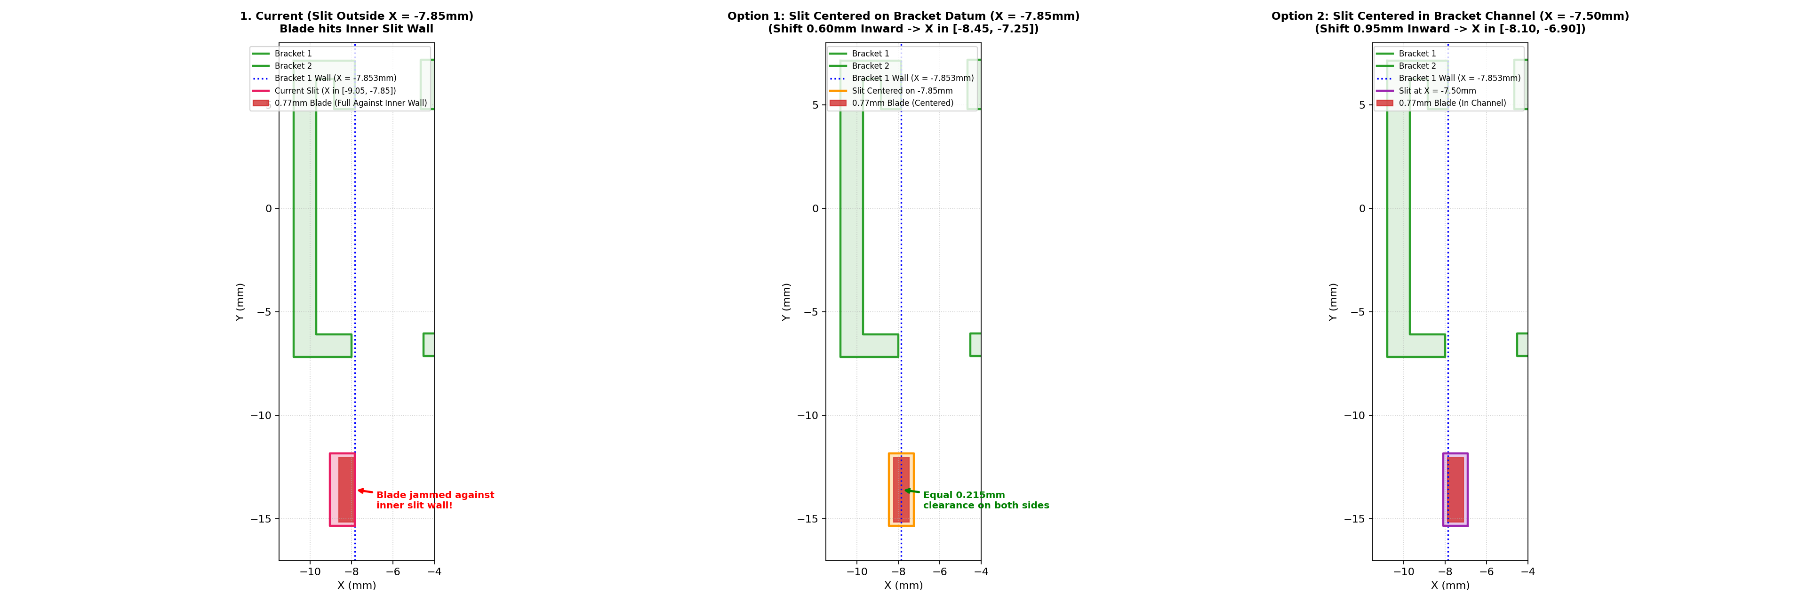
testing/slit_centering_options.png
