elliotmartin92/kia-socket/testing/slit_insert_interference_analysis.png

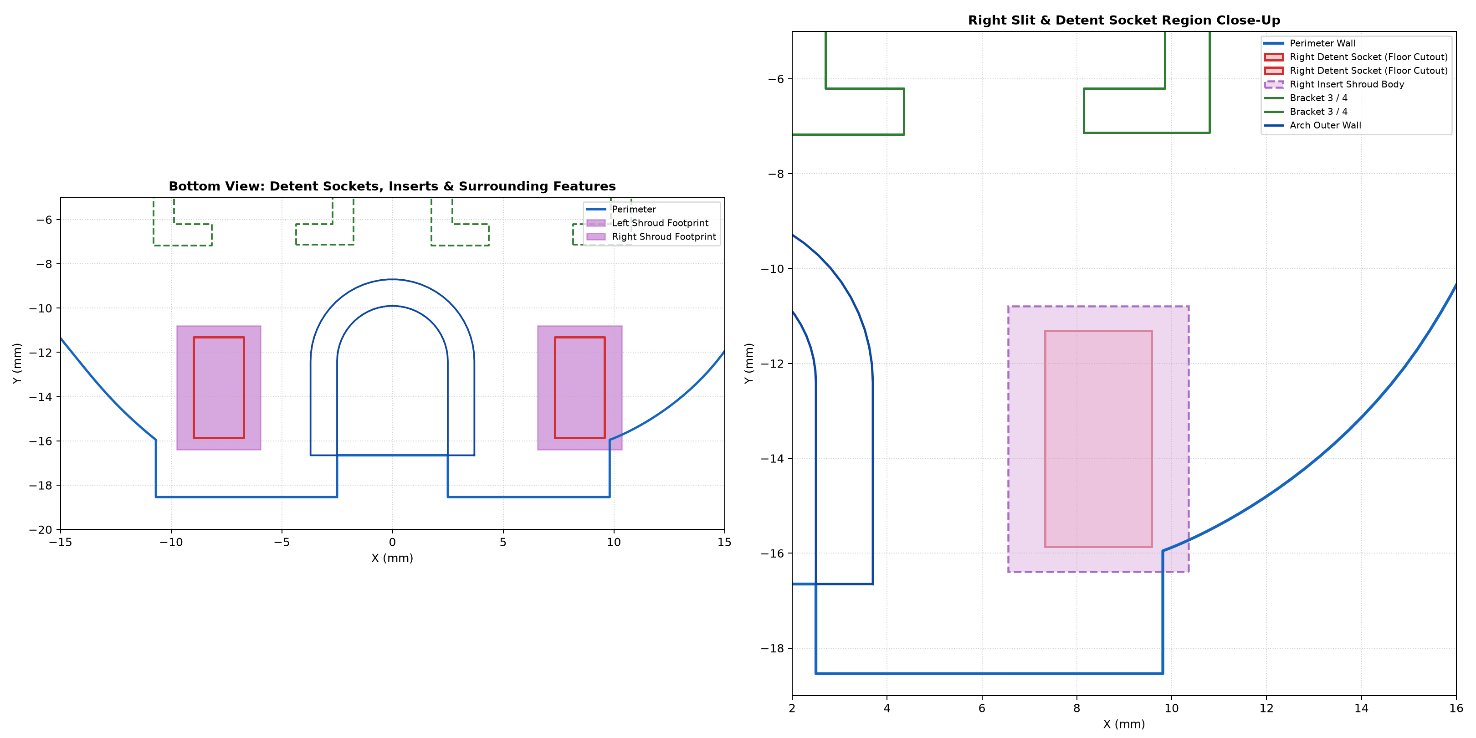
testing/slit_insert_interference_analysis.png
