elliotmartin92/kia-socket/testing/slit_insert_preview.png

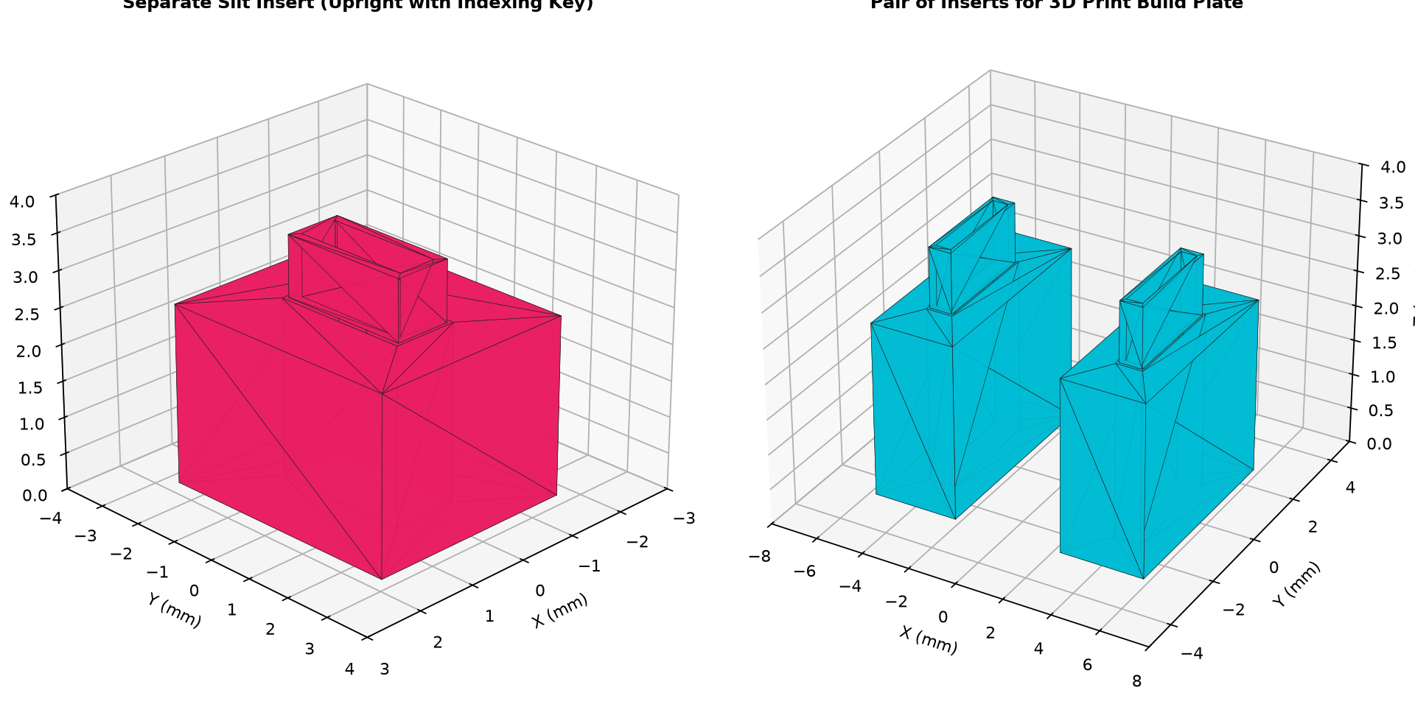
testing/slit_insert_preview.png
