elliotmartin92/kia-socket/testing/slits_preview.png

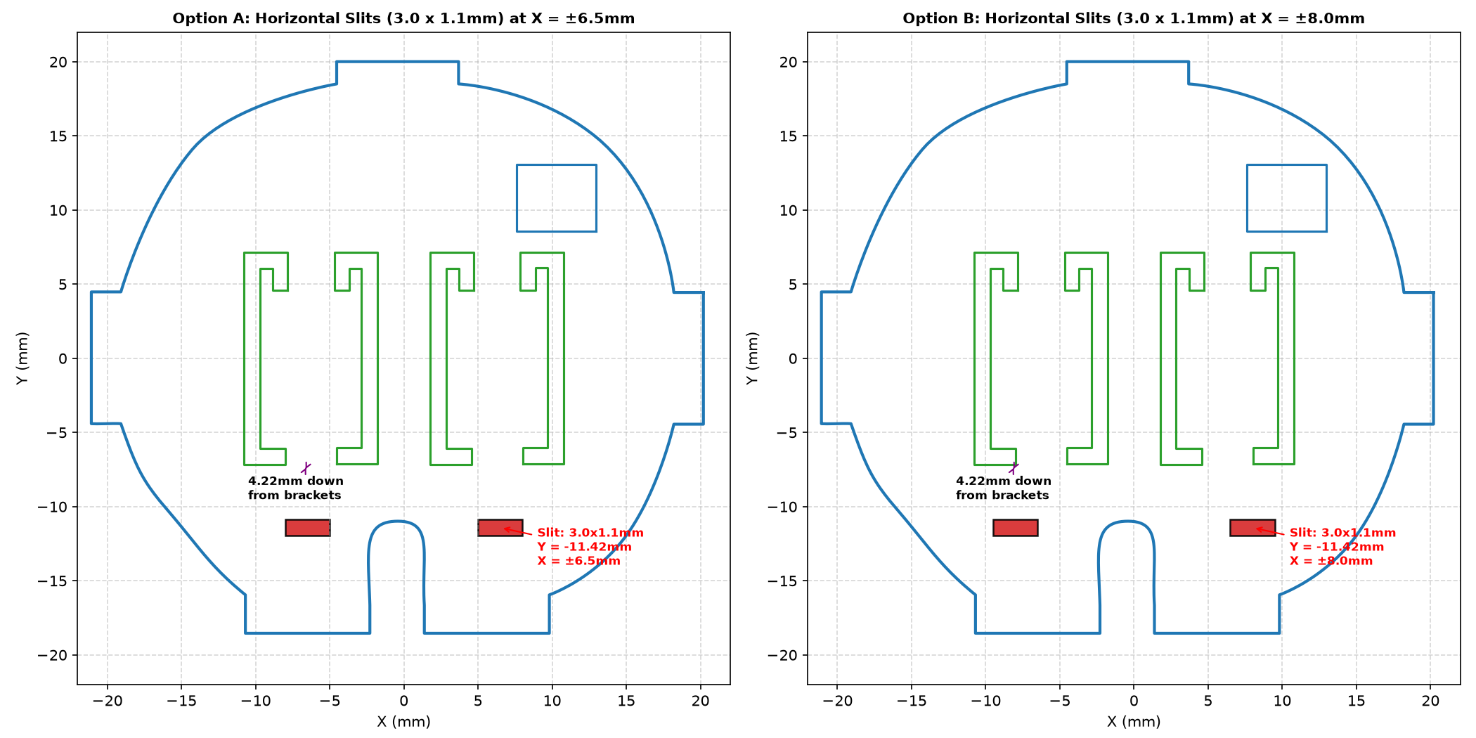
testing/slits_preview.png
