elliotmartin92/kia-socket/testing/sloped_slit_insert_preview.png

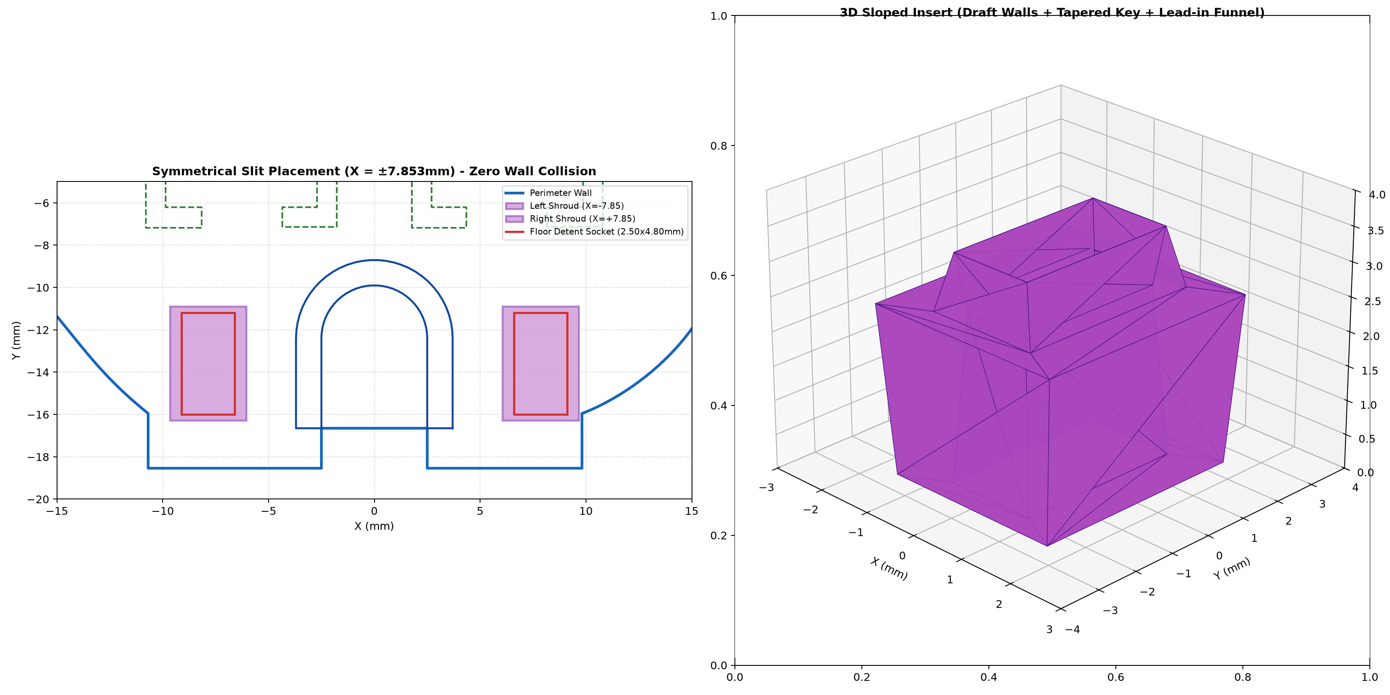
testing/sloped_slit_insert_preview.png
