elliotmartin92/kia-socket/testing/steep_struts_preview.png

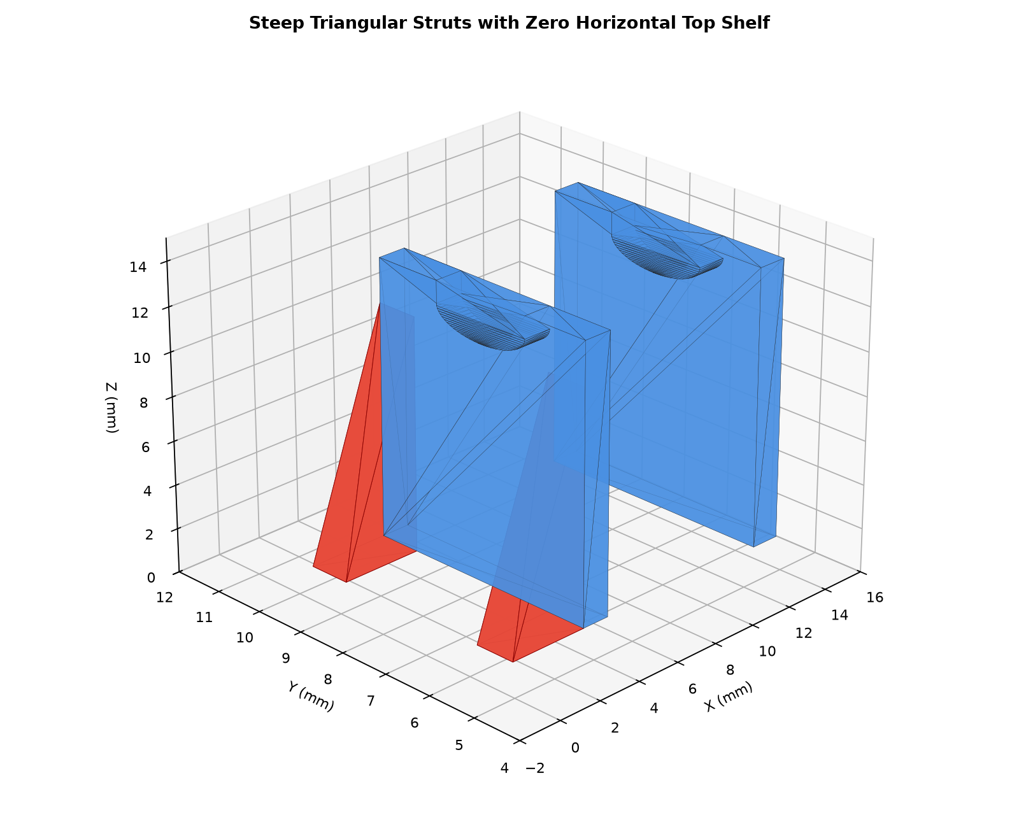
testing/steep_struts_preview.png
