elliotmartin92/kia-socket/testing/support_comparison_yz_profile.png

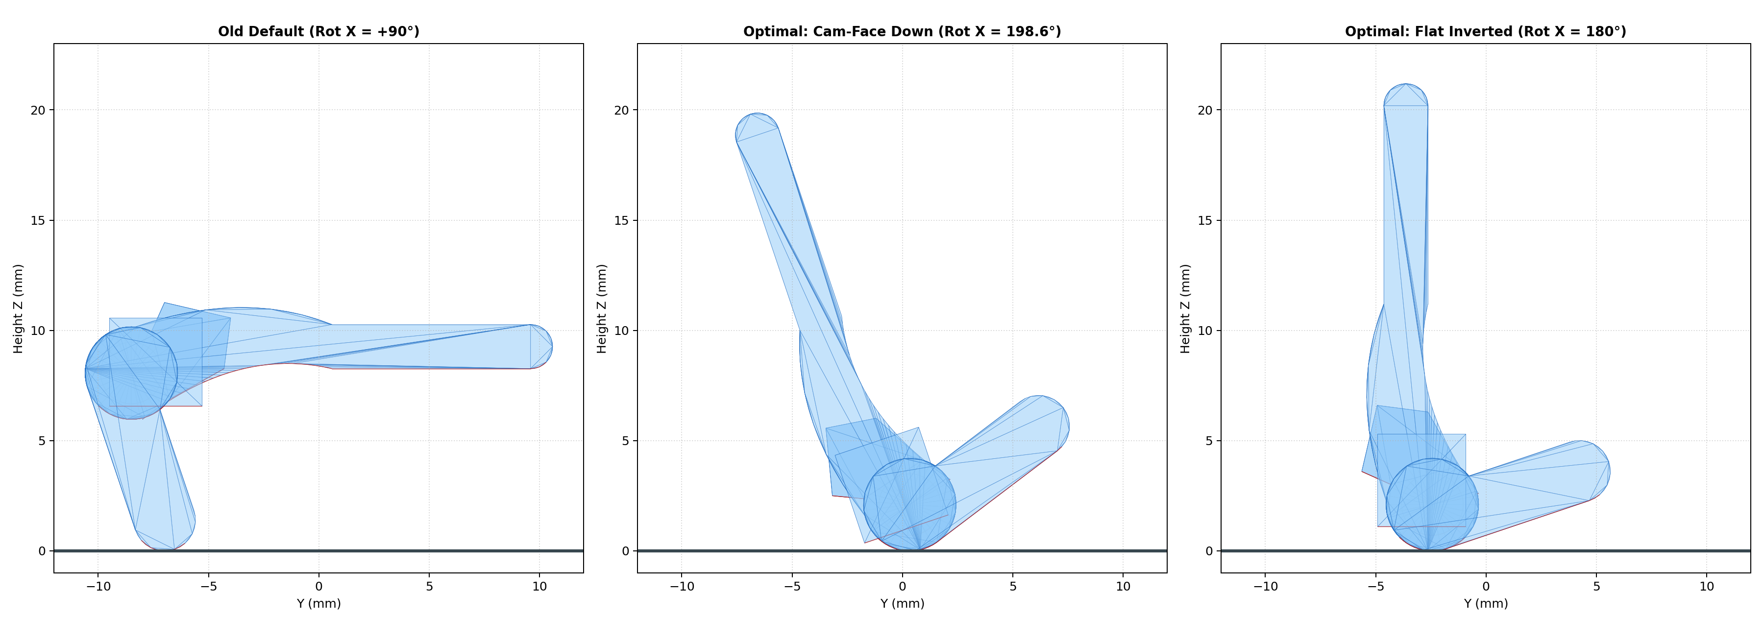
testing/support_comparison_yz_profile.png
