elliotmartin92/kia-socket/testing/top_biased_key_preview.png

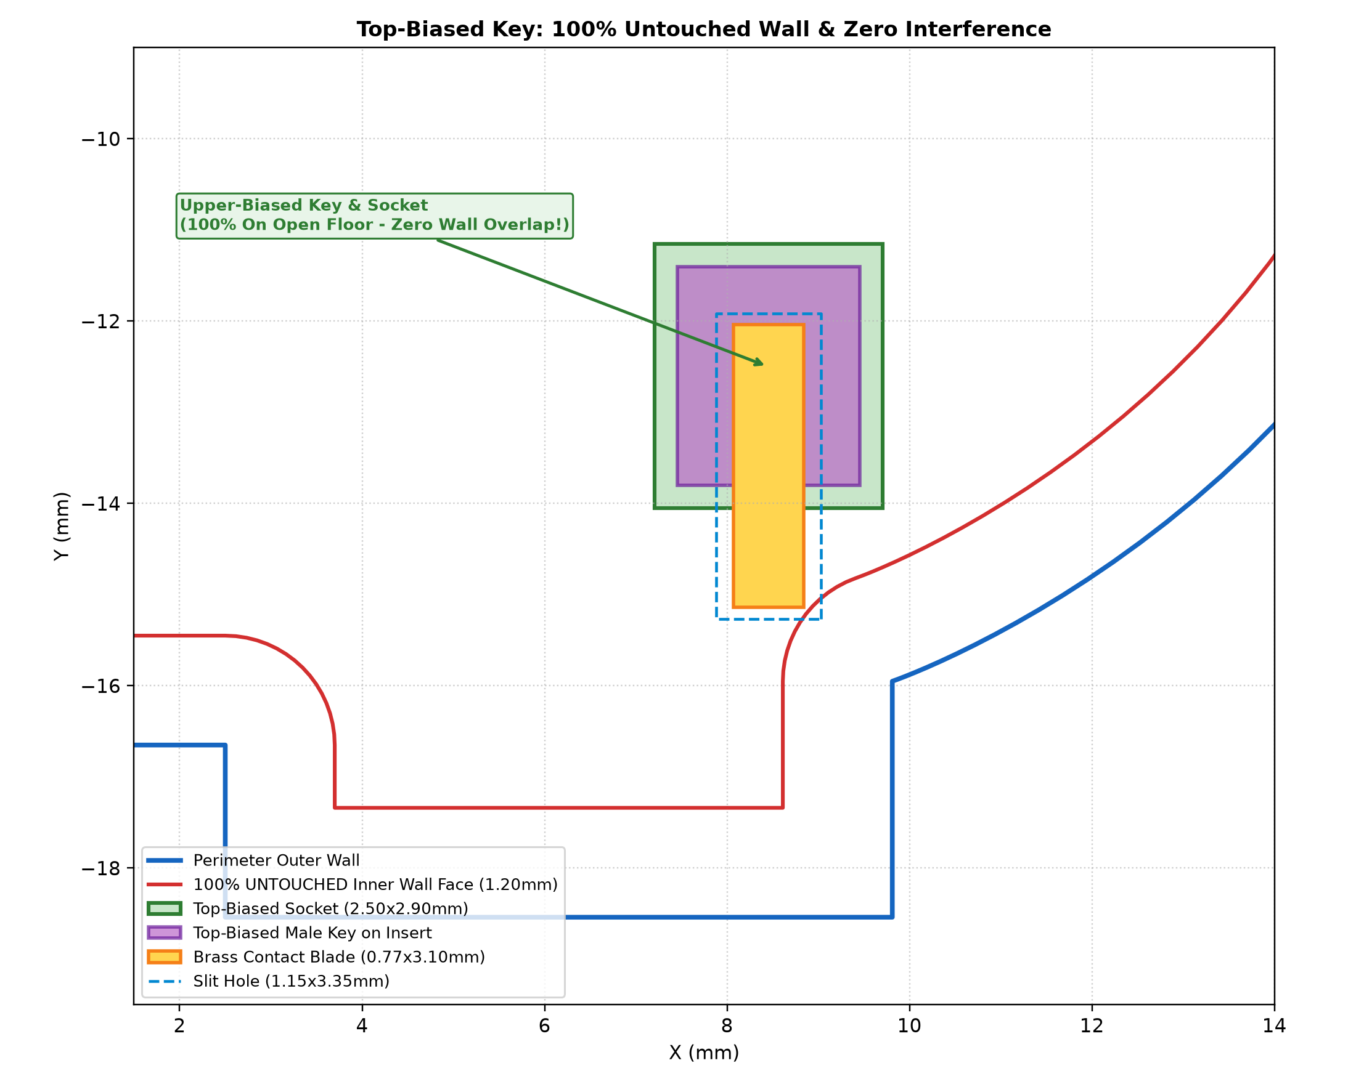
testing/top_biased_key_preview.png
