elliotmartin92/kia-socket/testing/top_ribs_boundary.png

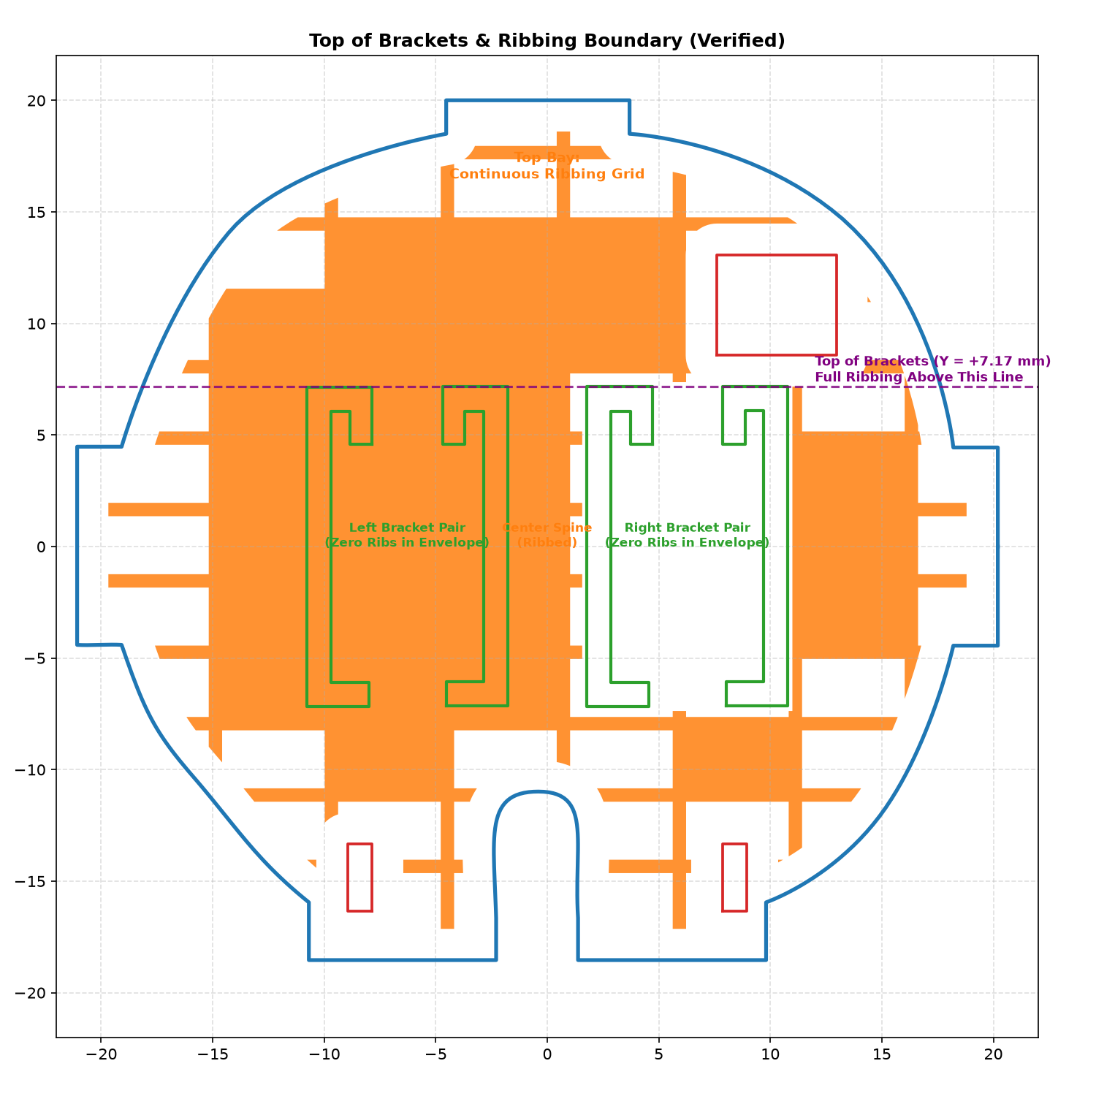
testing/top_ribs_boundary.png
