elliotmartin92/kia-socket/testing/top_tab_833_gap_test.png

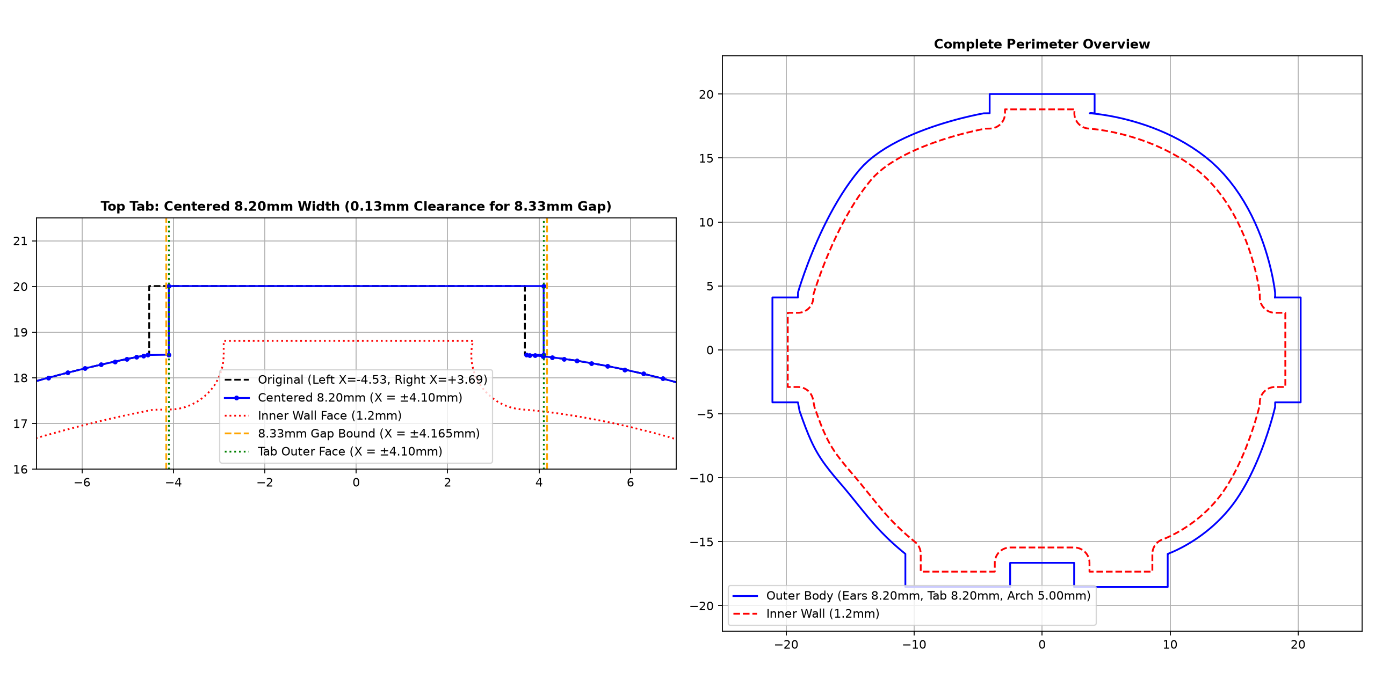
testing/top_tab_833_gap_test.png
