elliotmartin92/kia-socket/testing/tower_bracket3_exact_y_alignment.png

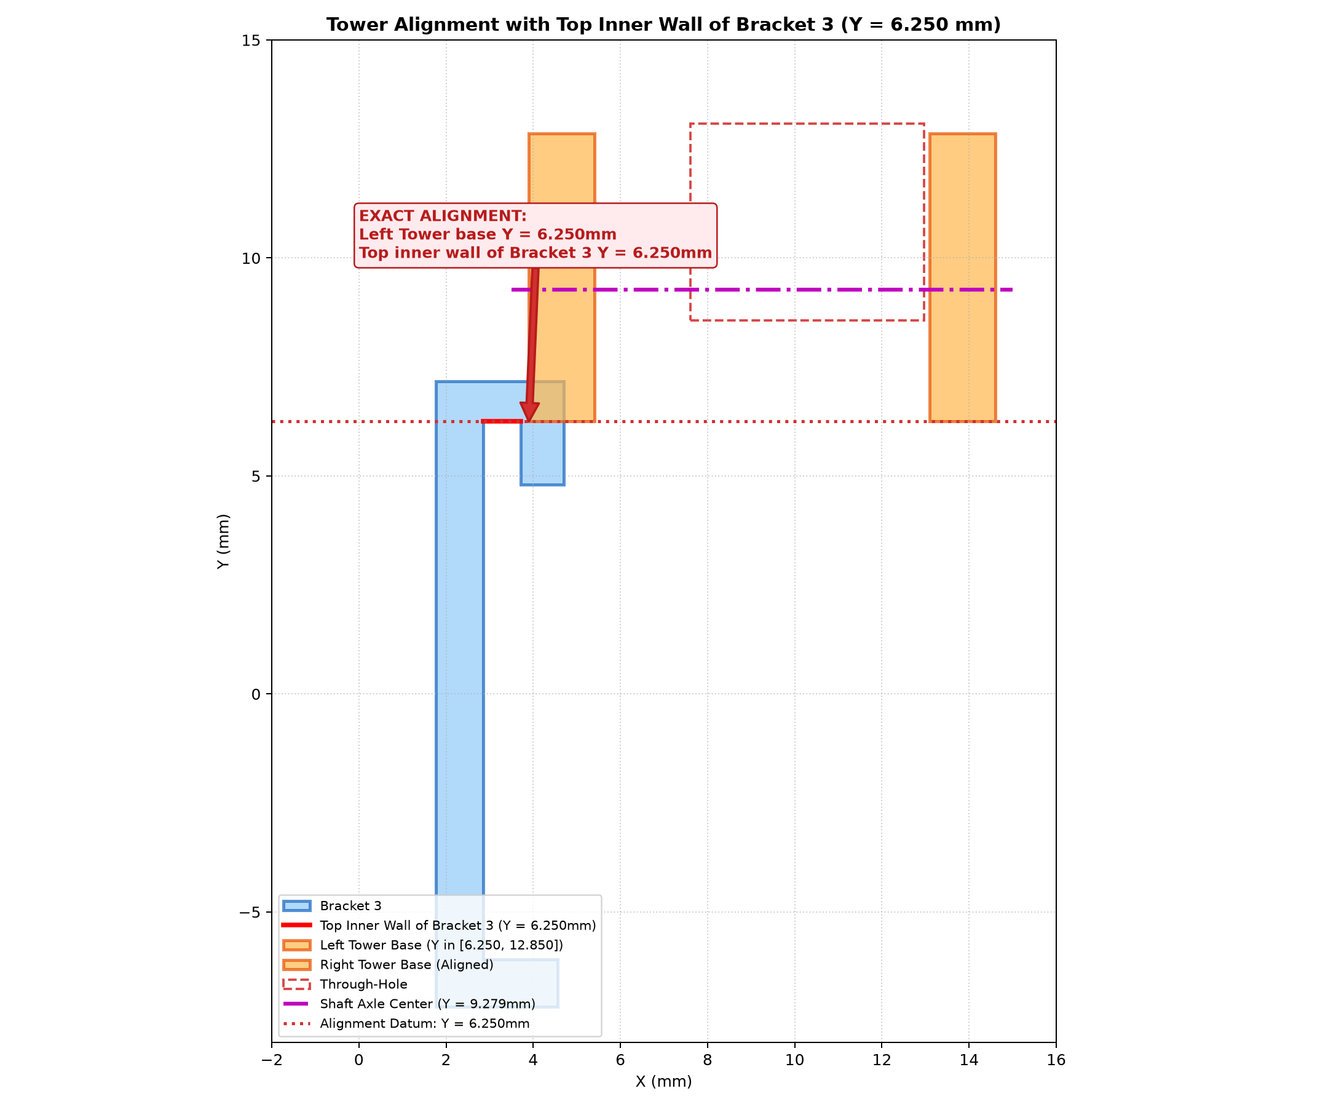
testing/tower_bracket3_exact_y_alignment.png
