elliotmartin92/kia-socket/testing/tower_bracket3_intersection.png

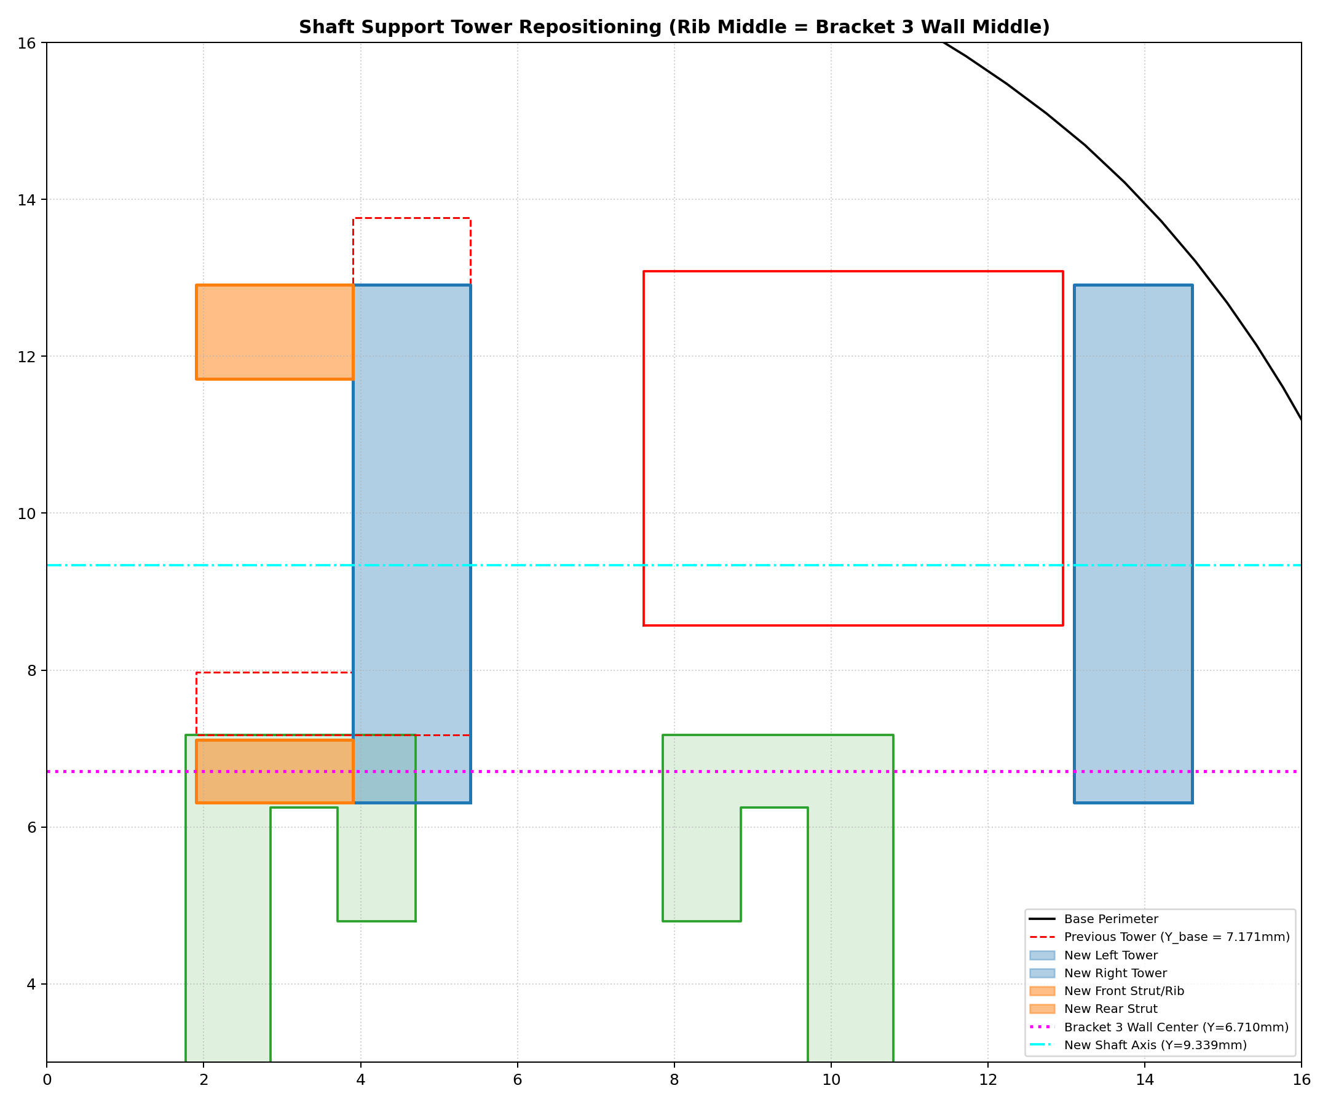
testing/tower_bracket3_intersection.png
