elliotmartin92/kia-socket/testing/tower_cap_fitment_analysis.png

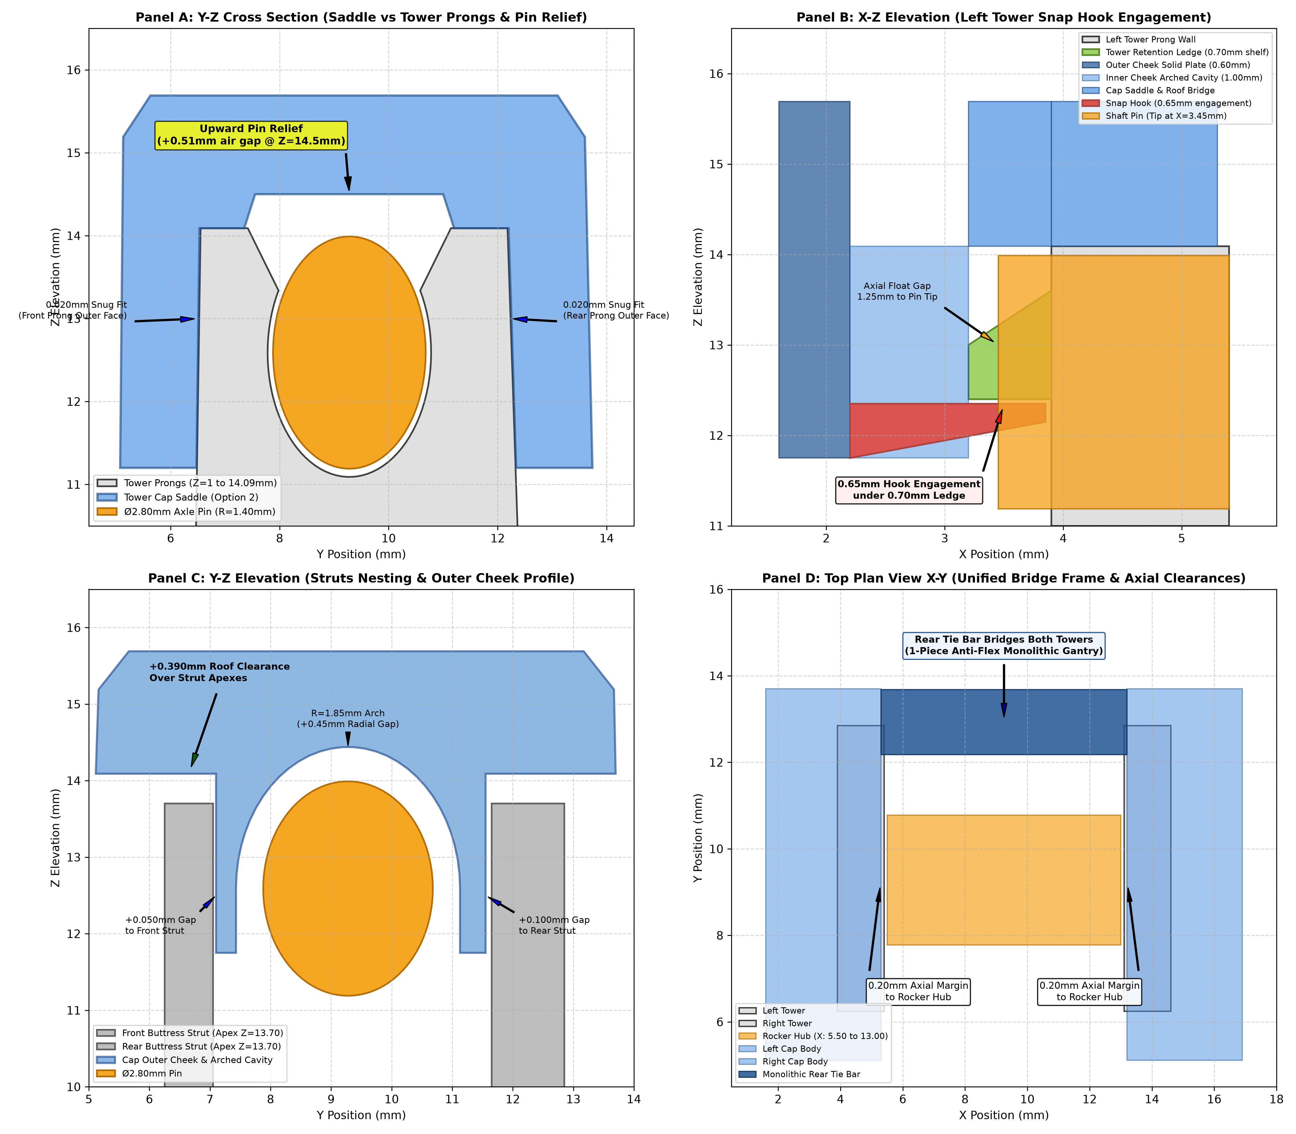
testing/tower_cap_fitment_analysis.png
