elliotmartin92/kia-socket/testing/tower_options_comparison.png

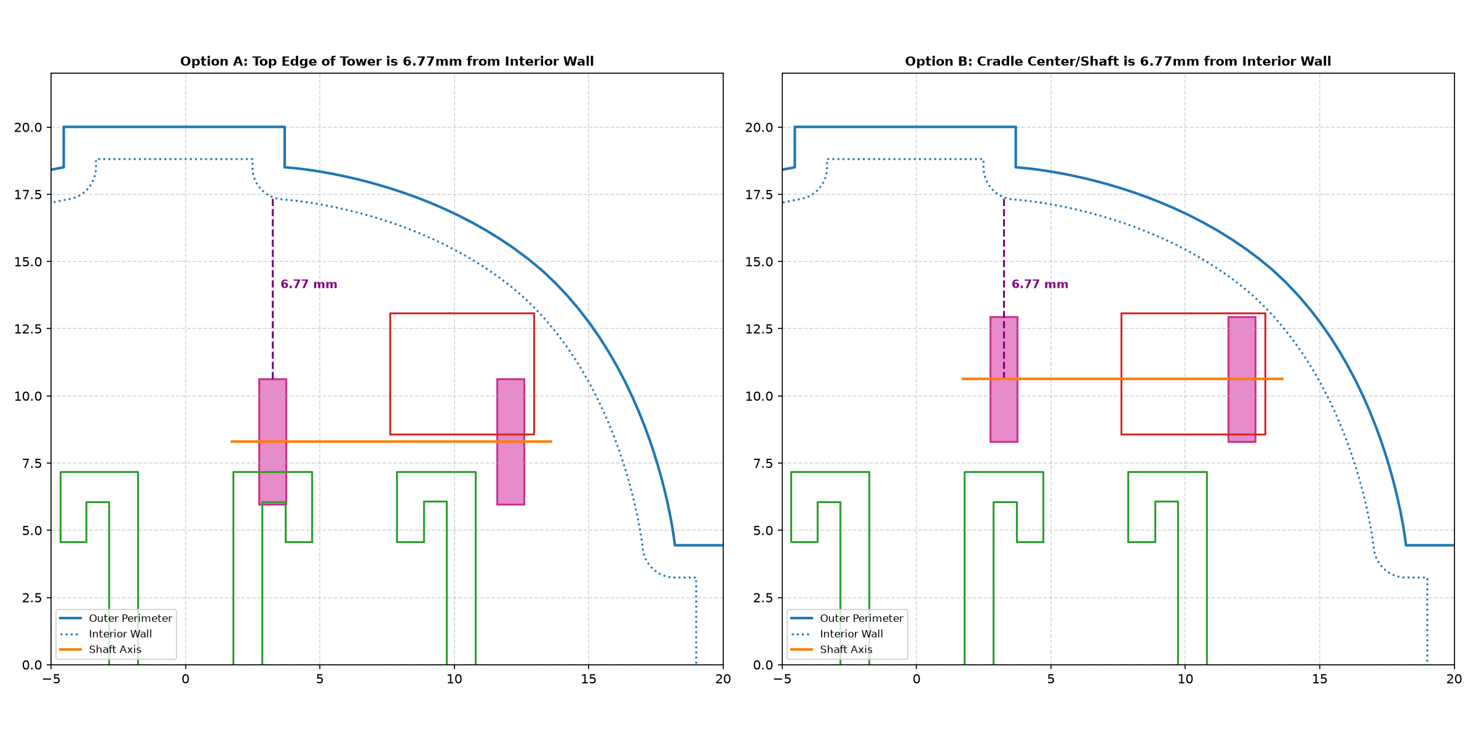
testing/tower_options_comparison.png
