elliotmartin92/kia-socket/testing/tower_reinforcement_comparison.png

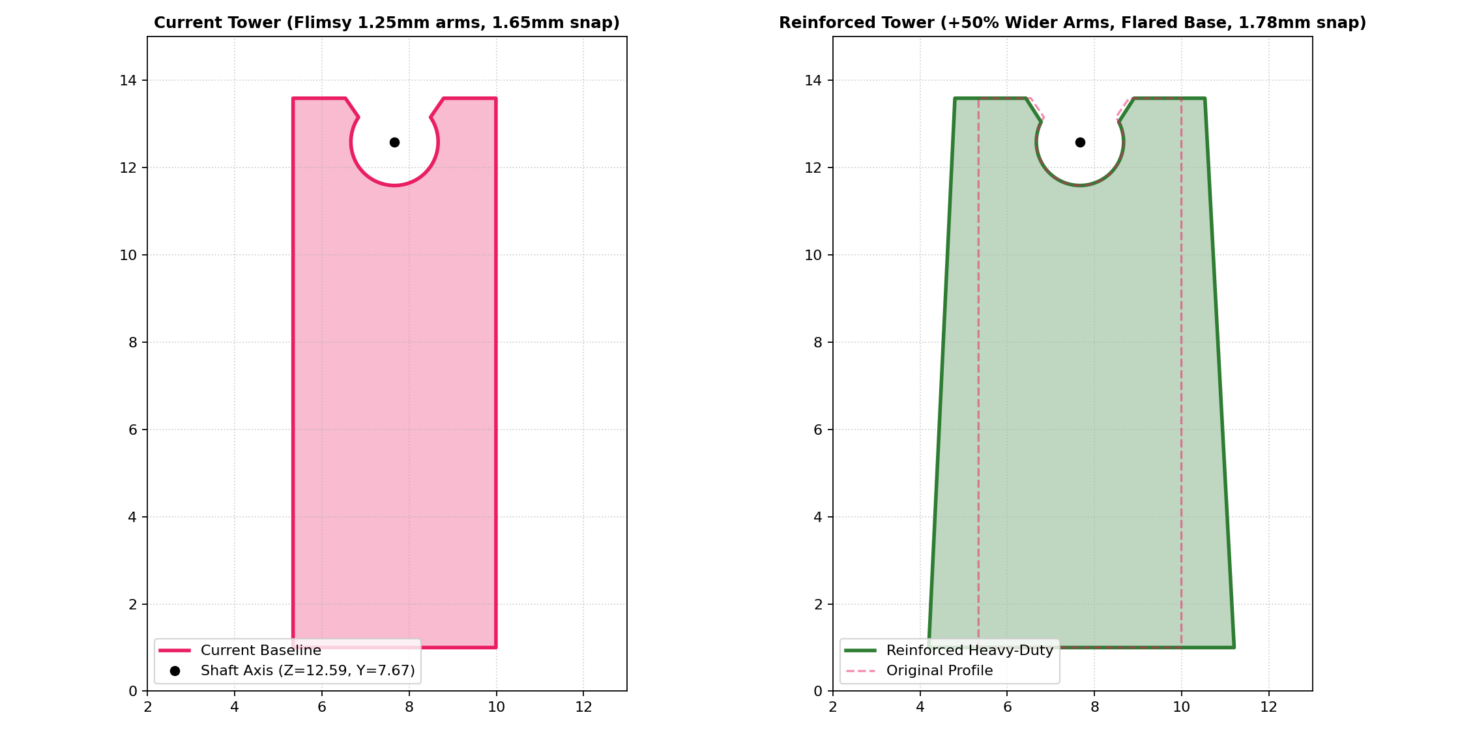
testing/tower_reinforcement_comparison.png
