elliotmartin92/kia-socket/testing/tower_shift_options.png

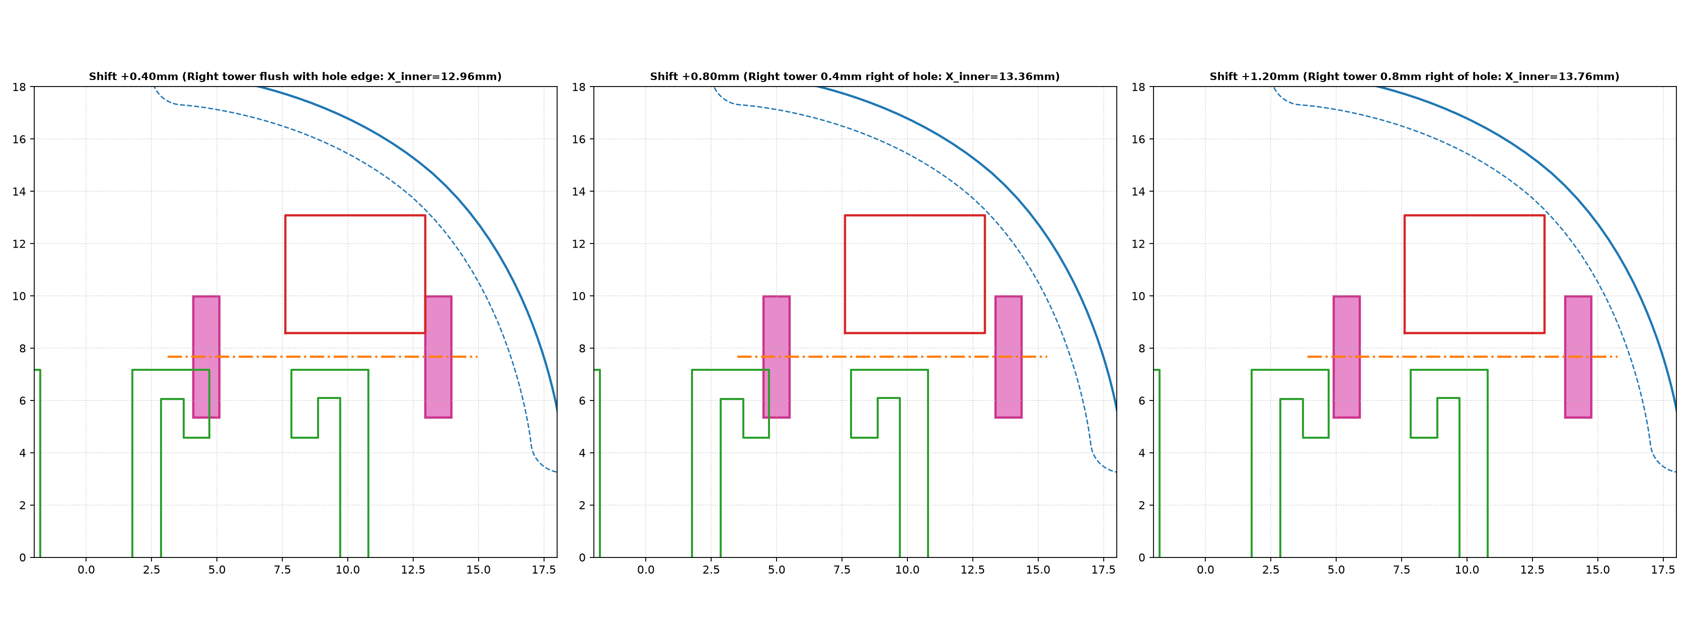
testing/tower_shift_options.png
