elliotmartin92/kia-socket/testing/tower_shifted_up_preview.png

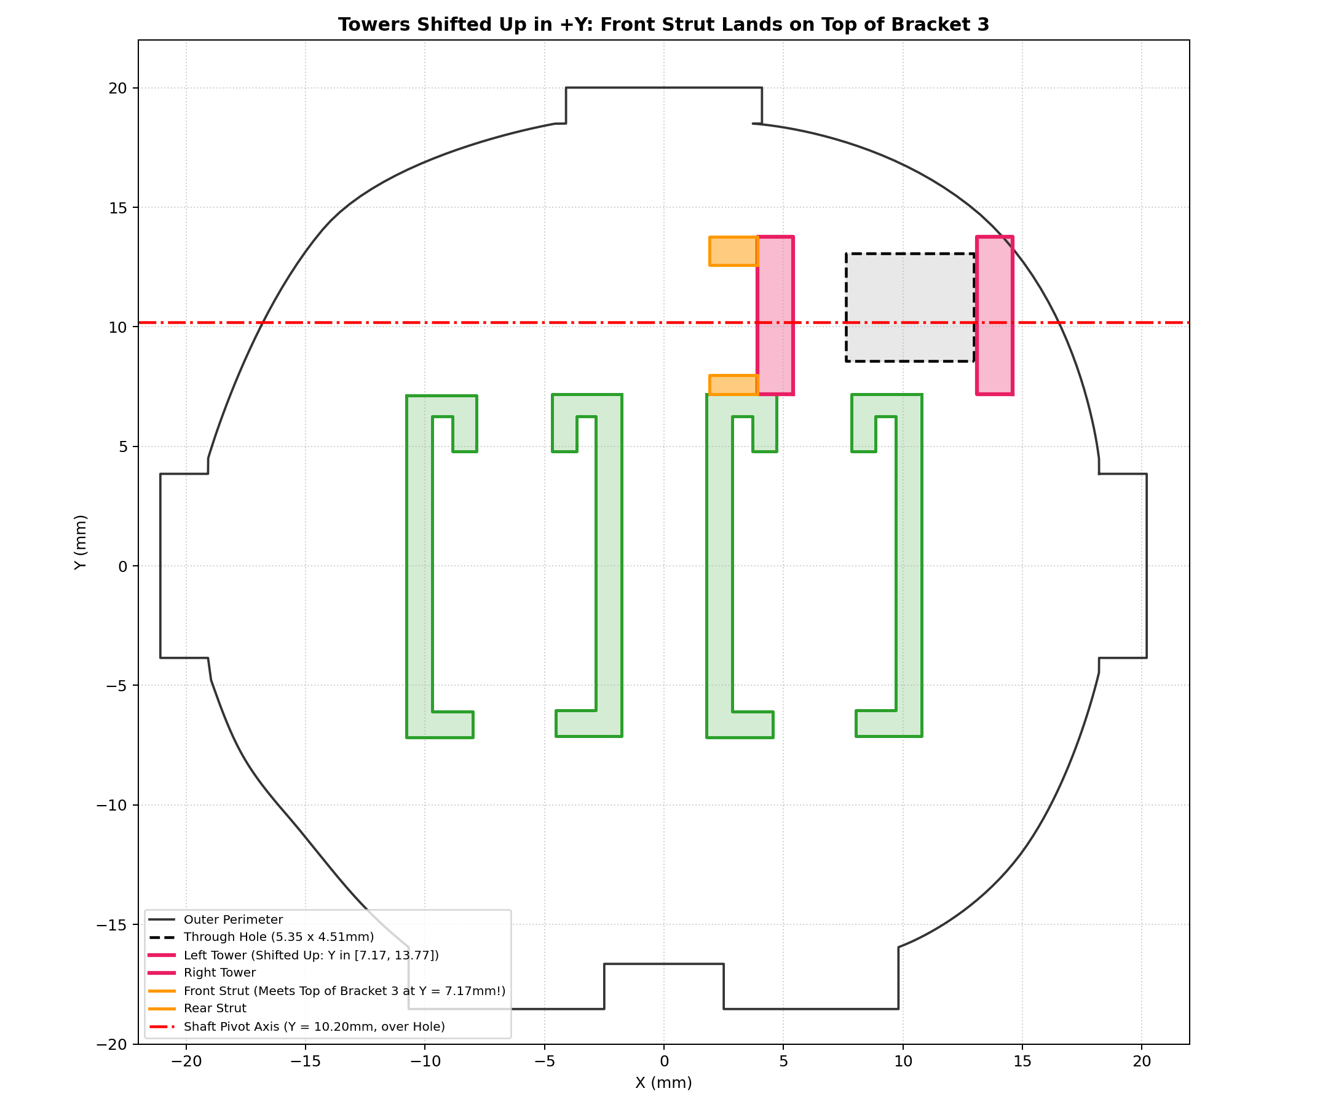
testing/tower_shifted_up_preview.png
