elliotmartin92/kia-socket/testing/tower_snap_options_comparison.png

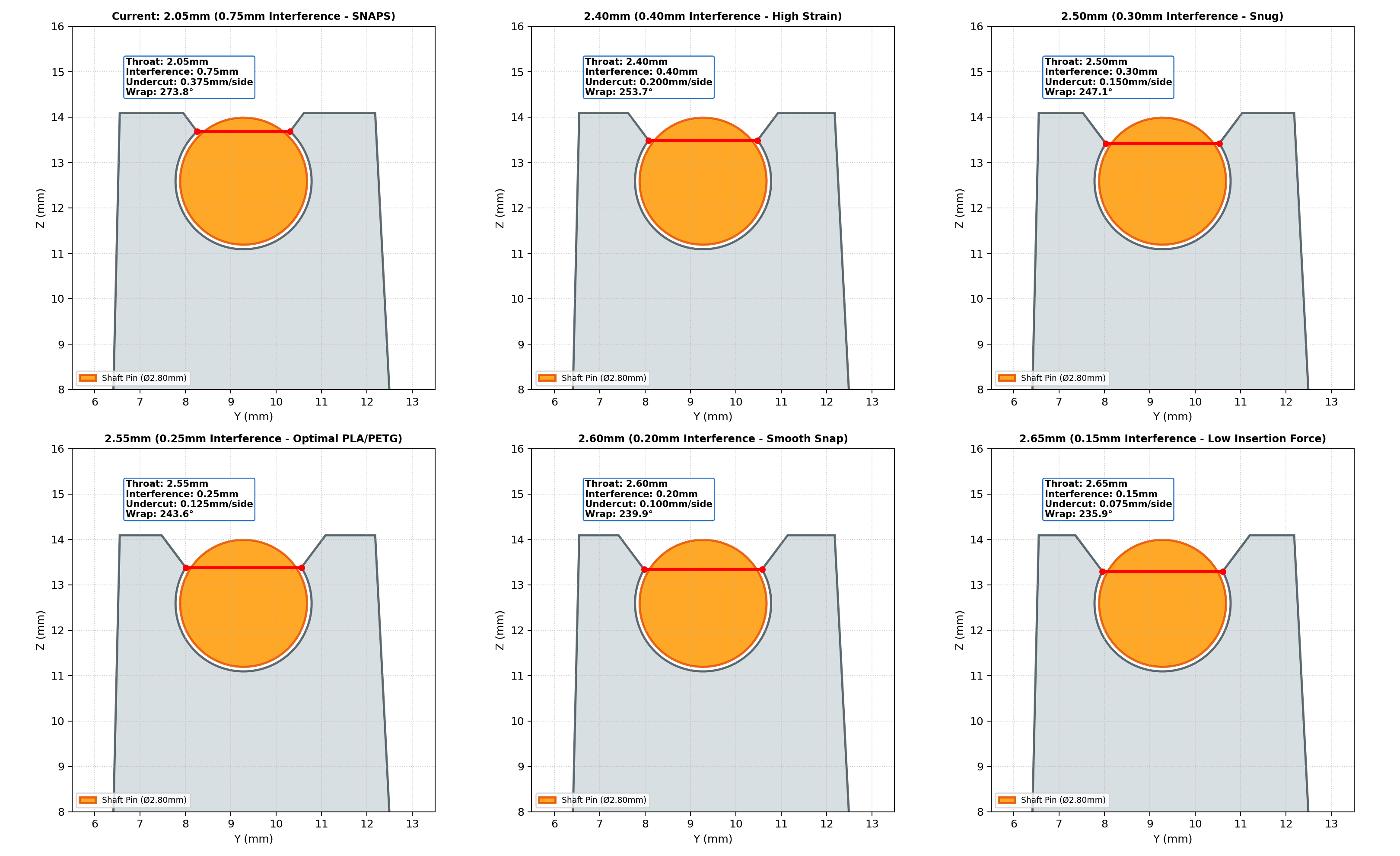
testing/tower_snap_options_comparison.png
