elliotmartin92/kia-socket/testing/twin_prong_support_3d.png

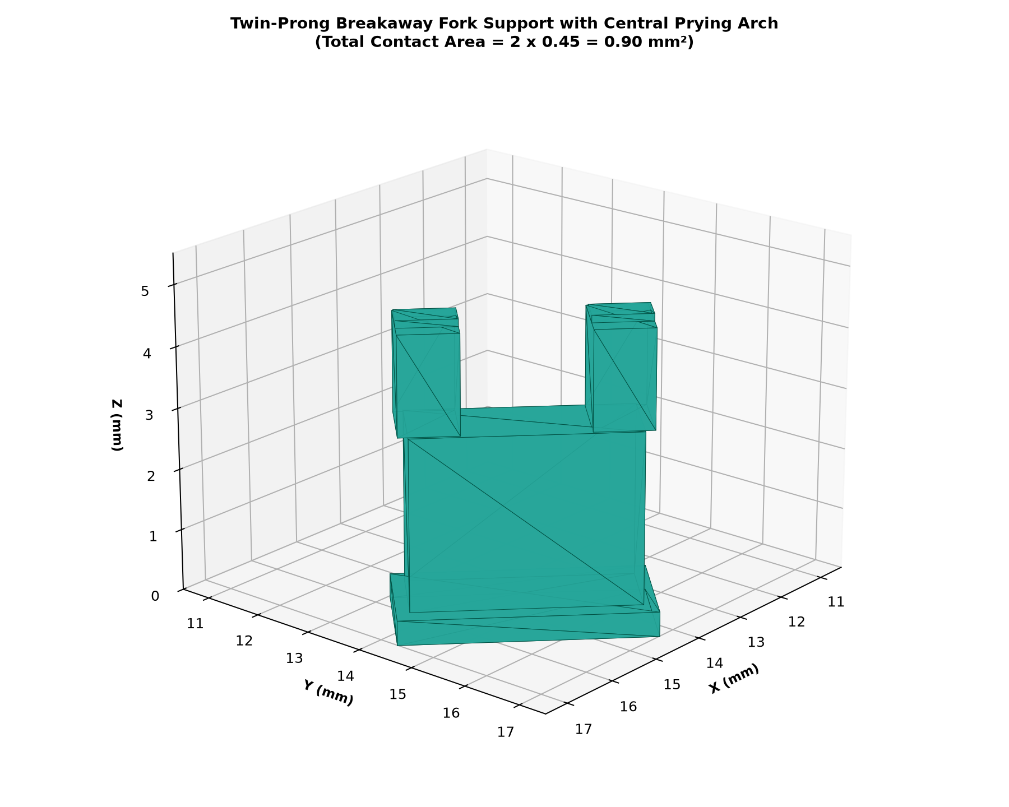
testing/twin_prong_support_3d.png
