elliotmartin92/kia-socket/testing/u_cradle_3d_closeup.png

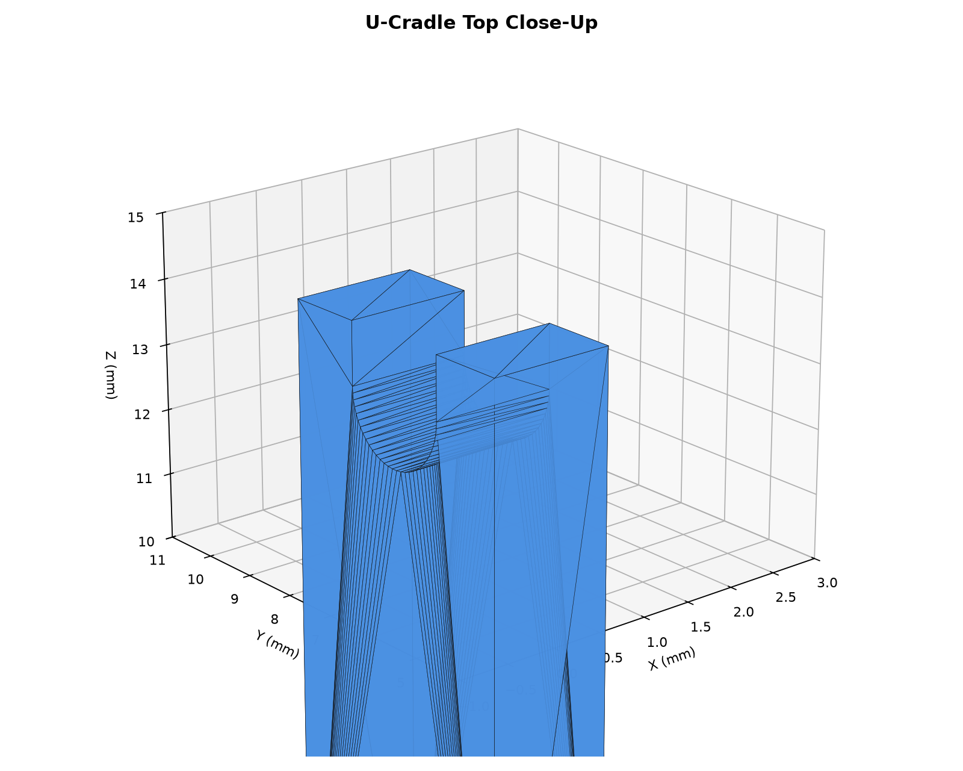
testing/u_cradle_3d_closeup.png
