elliotmartin92/kia-socket/testing/u_cradle_preview.png

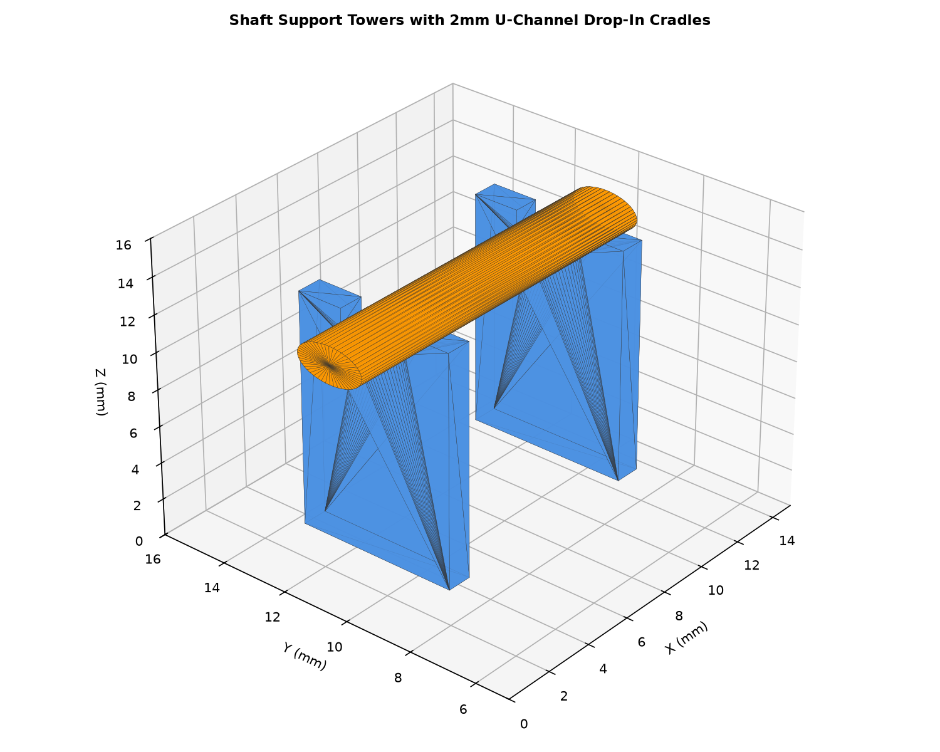
testing/u_cradle_preview.png
