elliotmartin92/kia-socket/testing/u_cradle_profile_test.png

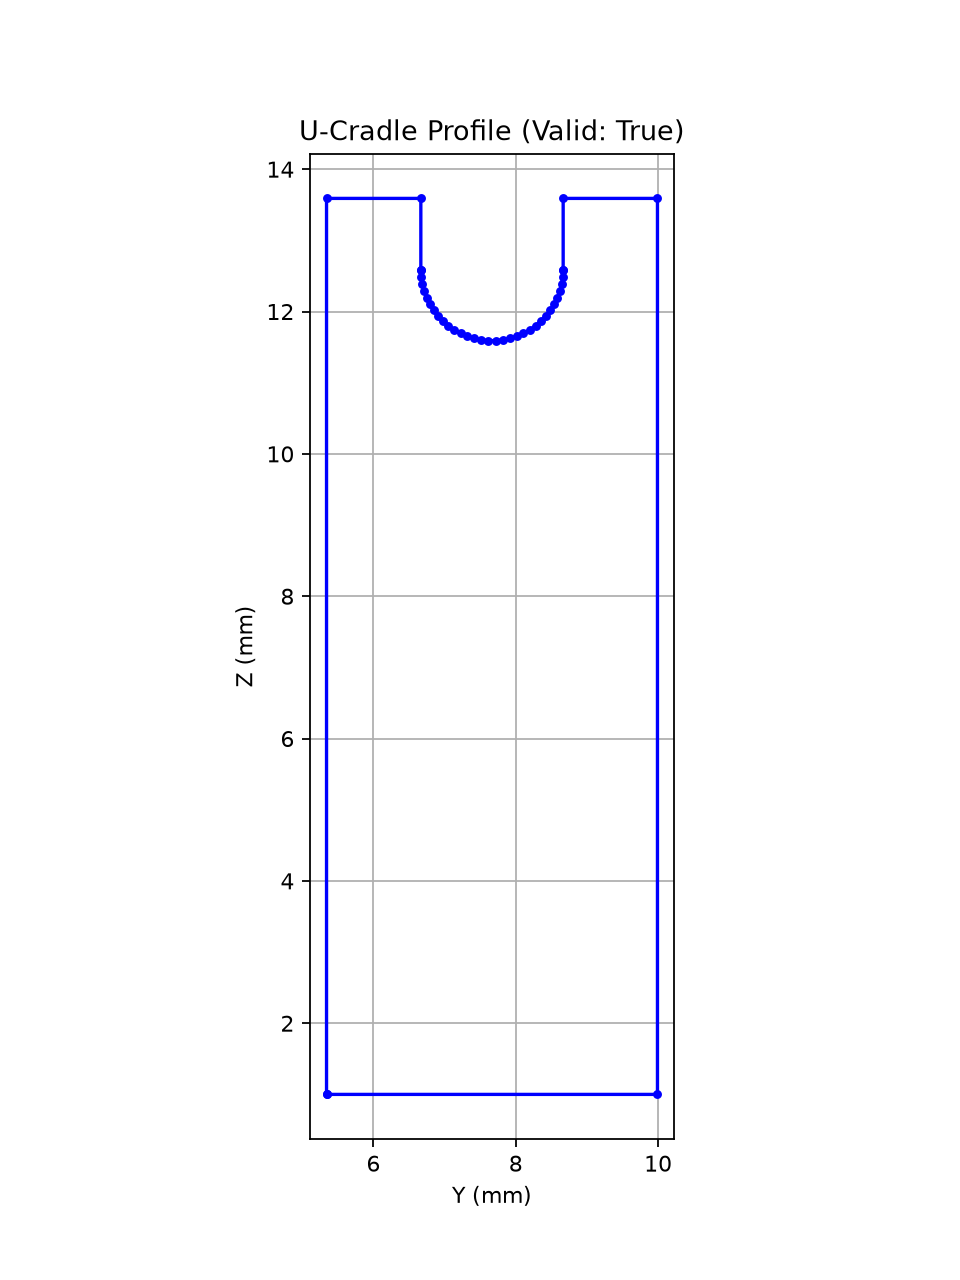
testing/u_cradle_profile_test.png
