elliotmartin92/kia-socket/testing/user_oriented_brass_insert.png

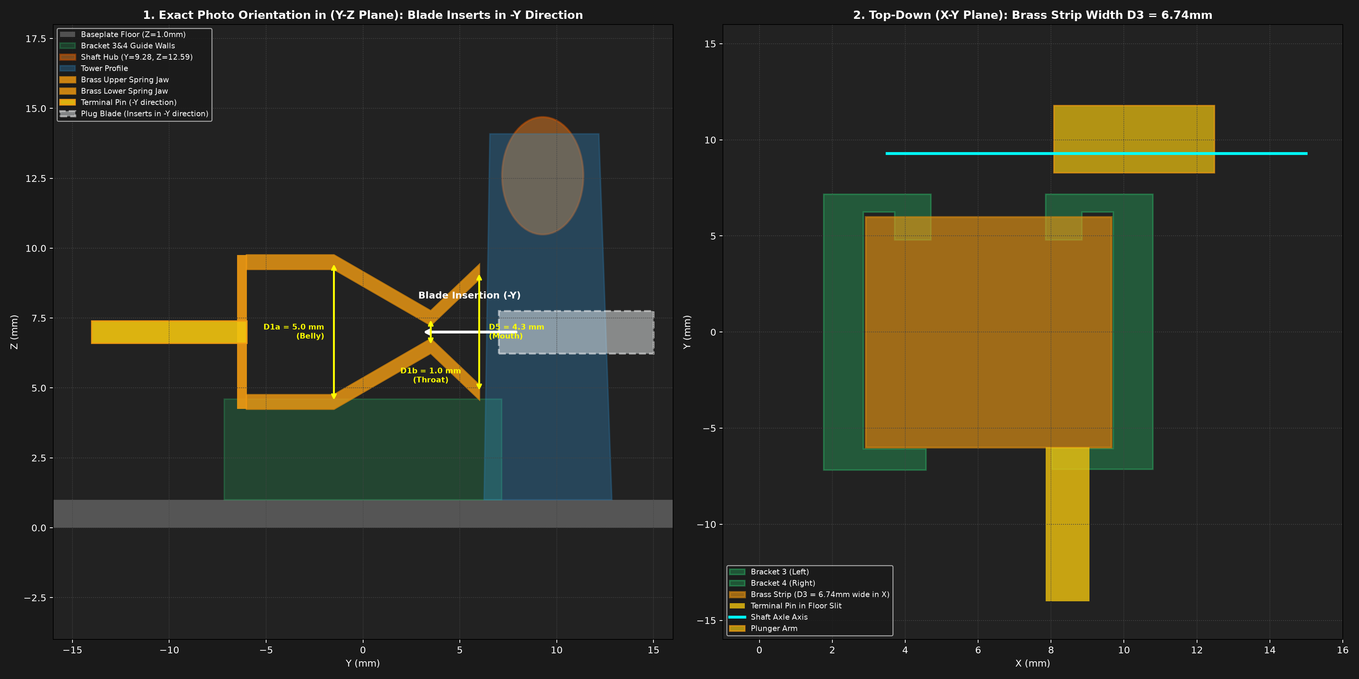
testing/user_oriented_brass_insert.png
