elliotmartin92/kia-socket/testing/v7_vs_v8_cam_interference_simulation.png

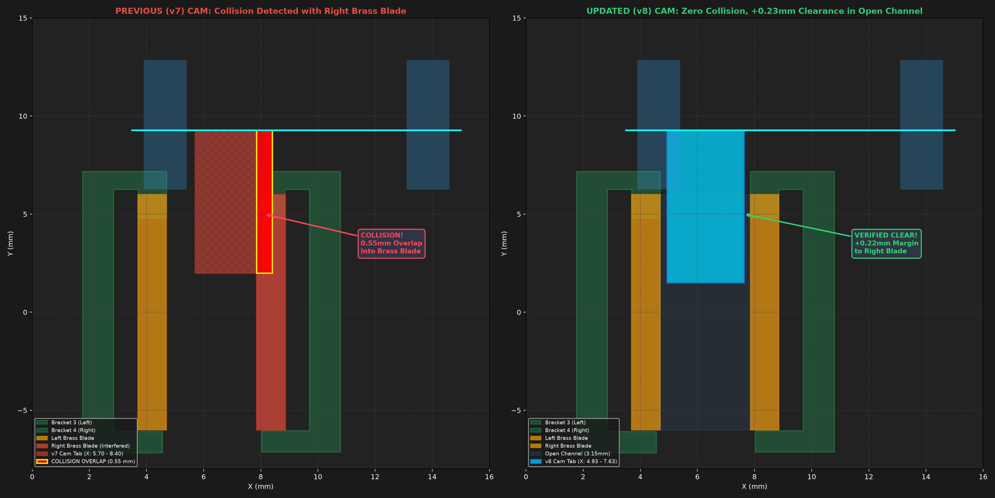
testing/v7_vs_v8_cam_interference_simulation.png
