elliotmartin92/kia-socket/testing/zoom_bracket34_photo.png

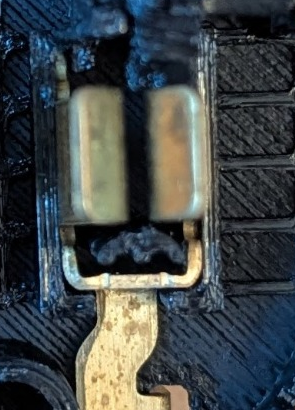
testing/zoom_bracket34_photo.png
