elliotmartin92/kia-socket/testing/zoom_bracket34_pixels.png

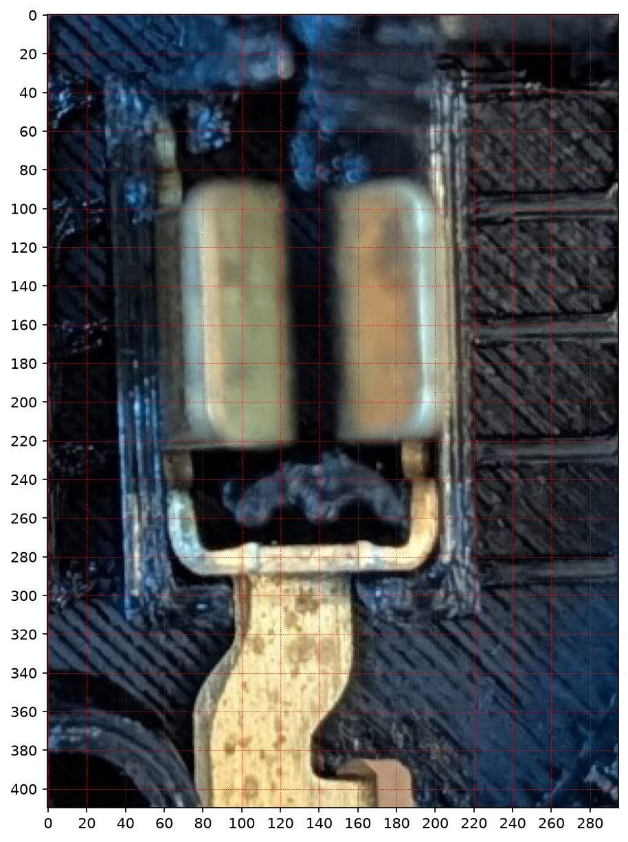
testing/zoom_bracket34_pixels.png
