elliotmartin92/kia-socket/testing/inspect_slit_insert_bug.png

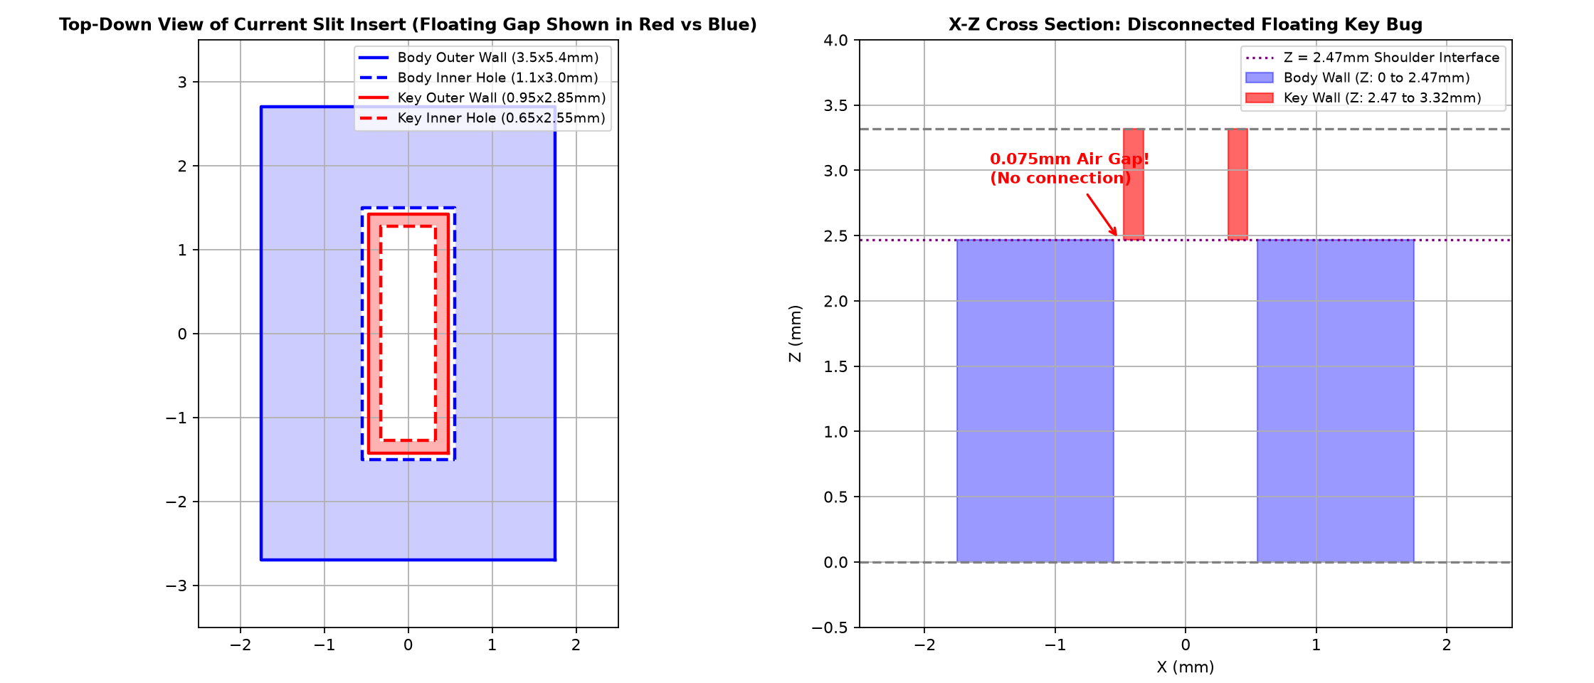
testing/inspect_slit_insert_bug.png
