elliotmartin92/kia-socket/testing/slit_insert_lip_fix_diagram.png

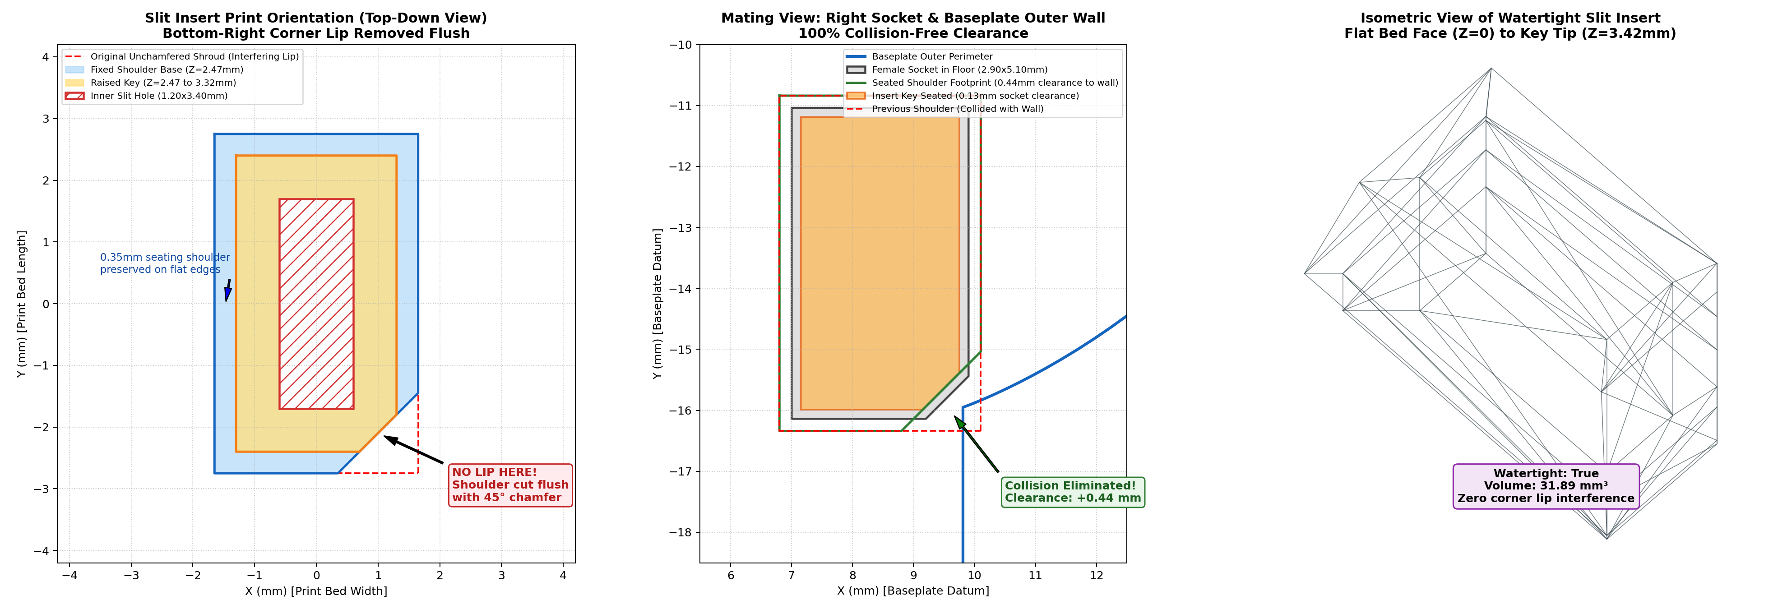
testing/slit_insert_lip_fix_diagram.png
