elliotmartin92/kia-socket/testing/verified_tower_tolerance_fix.png

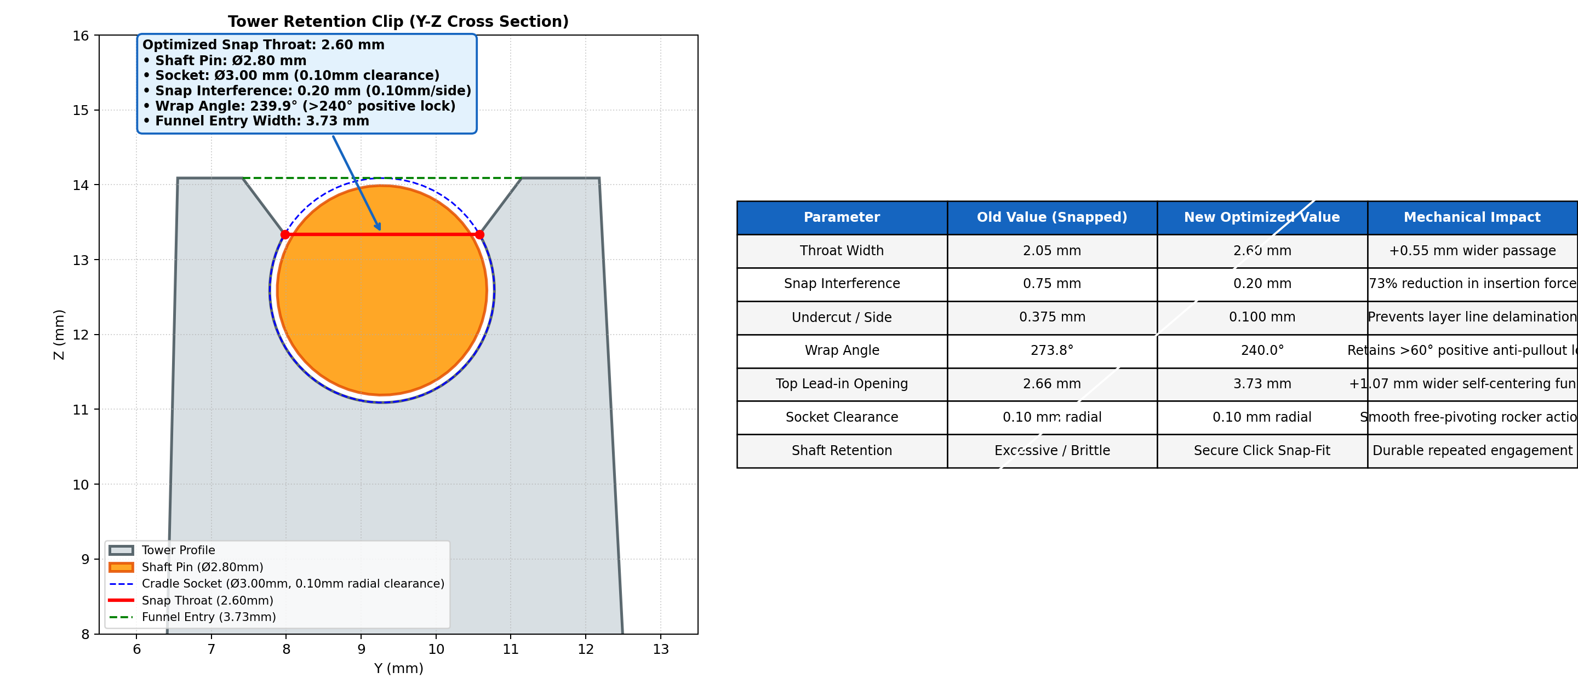
testing/verified_tower_tolerance_fix.png
